IowaScaledEngineering/ckt-irsense/pg/ckt-irsense-ra-v4.1-9db1f3e/ckt-irsense-ra-pcb.pdf

# ckt-irsense-ra.pcb

# 1. Table of Contents (This Page) Created on Mon Oct 12 17:48:26 2020

# 2. top 3. bottom 4. outline 5. plated-drill 6. unplated-drill 7. componentmask 8. soldermask 9. topsilk 10. bottomsilk 11. toppaste 12. bottompaste 13. topassembly 14. bottomassembly 15. fab

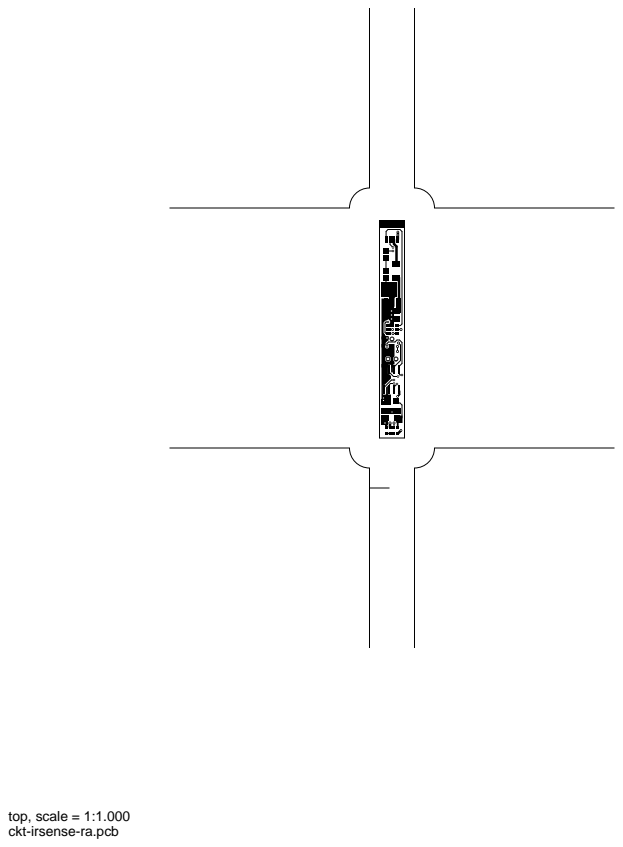
[picture p4: page 2]
top, scale = 1:1.000

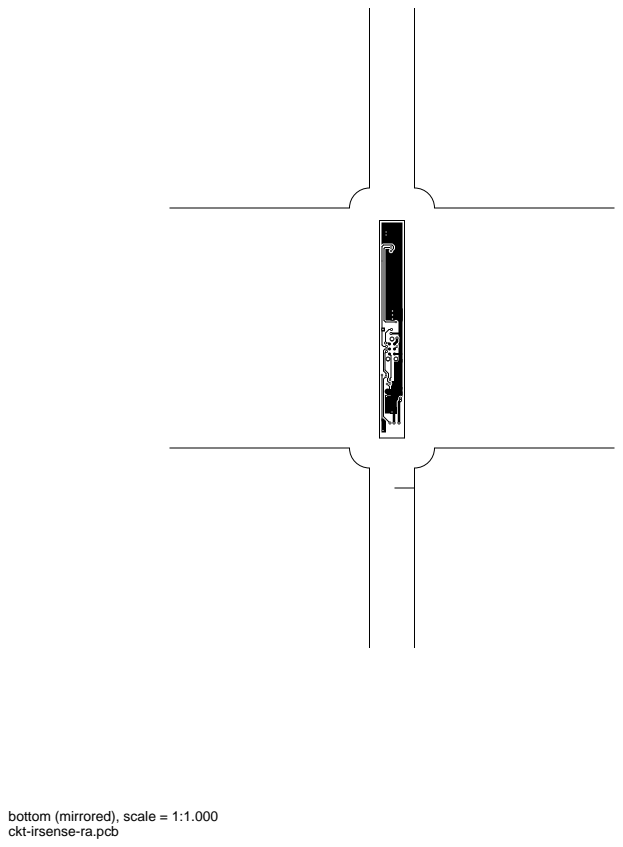
[picture p5: page 3]

bottom (mirrored), scale = 1:1.000

outline, scale = 1:1.000 plated-drill, scale = 1:1.000 unplated-drill, scale = 1:1.000

topmask, scale = 1:1.000

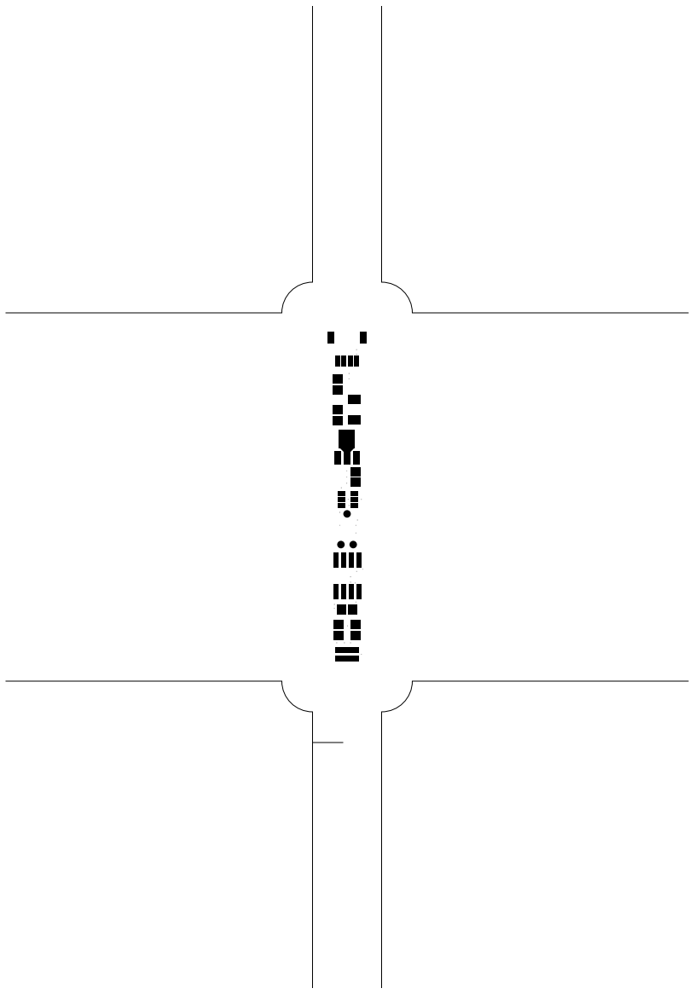
[picture p6: figure]

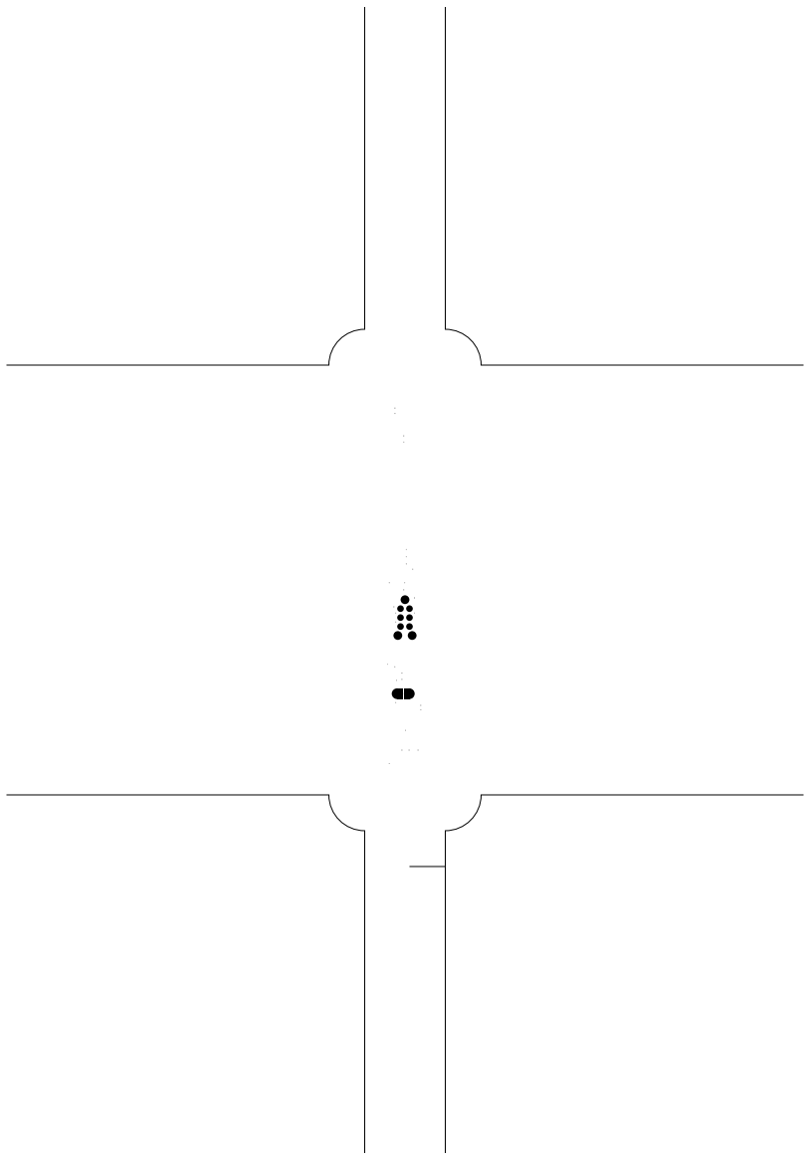
[picture p7: figure]

bottommask (mirrored), scale = 1:1.000

topsilk, scale = 1:1.000 bottomsilk (mirrored), scale = 1:1.000

toppaste, scale = 1:1.000 bottompaste (mirrored), scale = 1:1.000

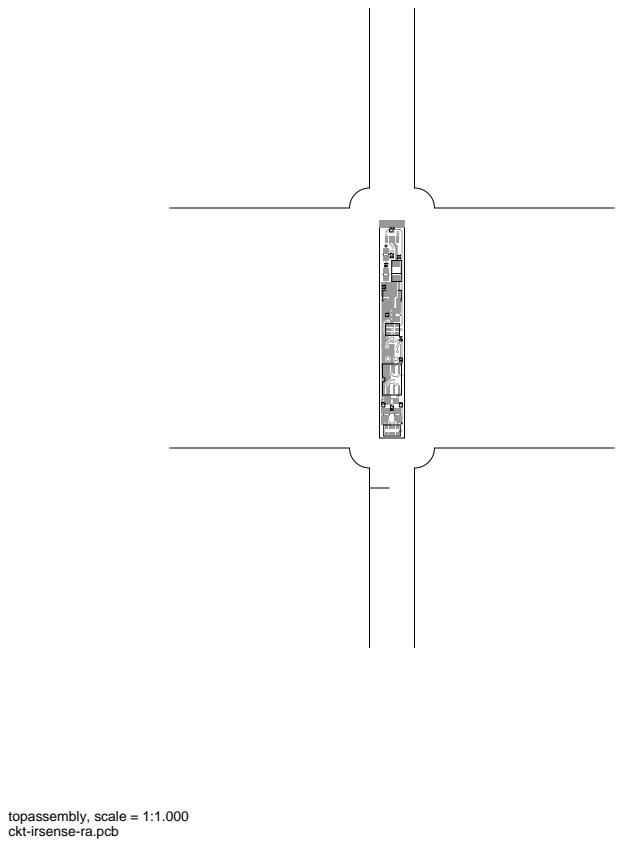
[picture p8: page 13]
topassembly, scale = 1:1.000

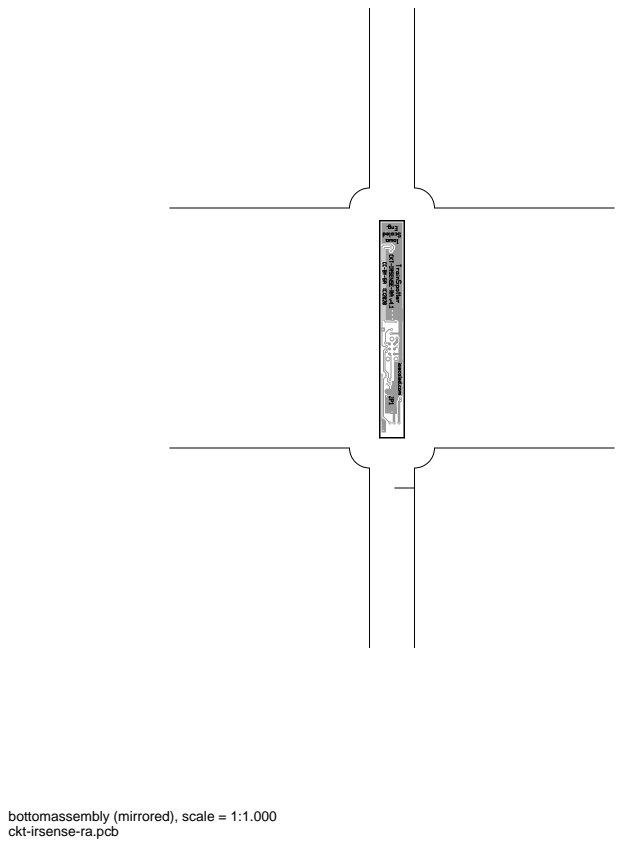
[picture p9: page 14]

bottomassembly (mirrored), scale = 1:1.000

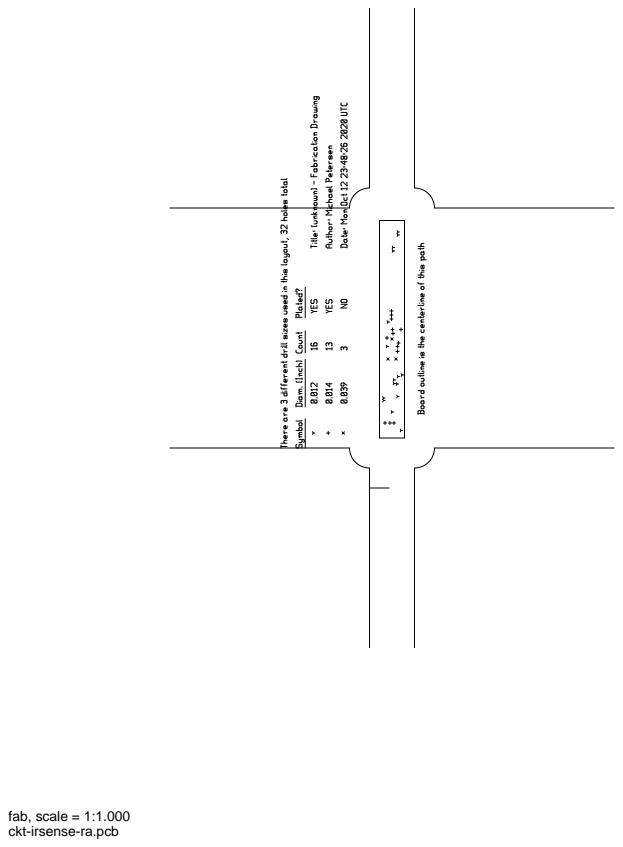
[picture p10: page 15]
fab, scale = 1:1.000
