IowaScaledEngineering/ckt-irsense/pg/i2c-irsense-v1.1-0d06f27/i2c-irsense-pcb.pdf

# i2c-irsense.pcb

# 1. Table of Contents (This Page) Created on Tue Jan 26 08:26:58 2016

# 2. top 3. bottom 4. outline 5. plated-drill 6. componentmask 7. soldermask 8. topsilk 9. bottomsilk 10. toppaste 11. topassembly 12. bottomassembly 13. fab

top, scale = 1:1.000

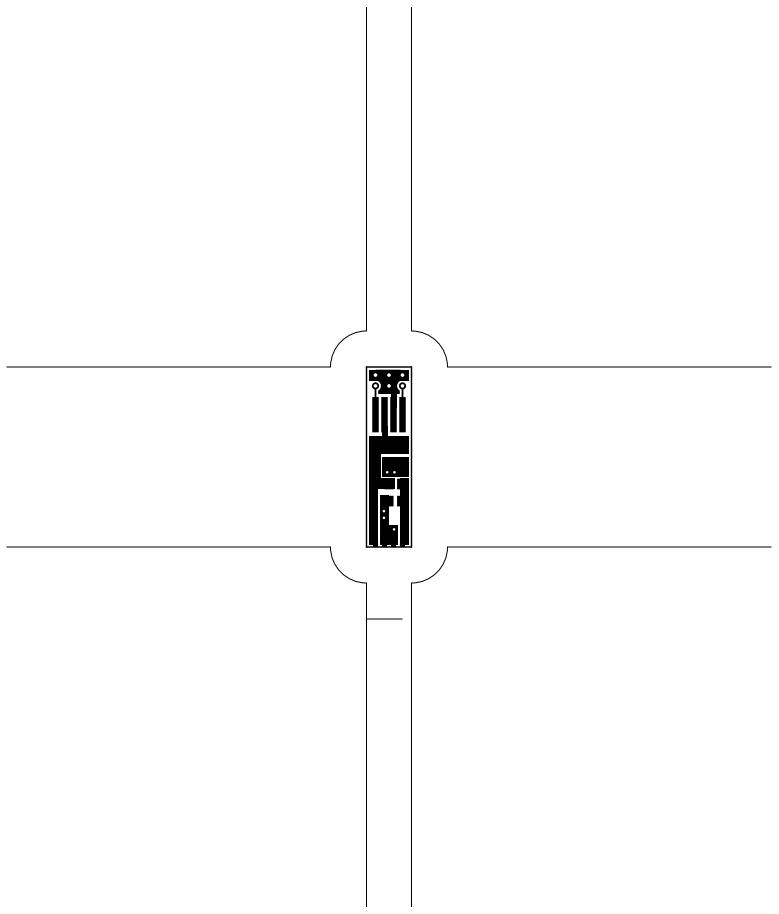
[picture p20: figure]
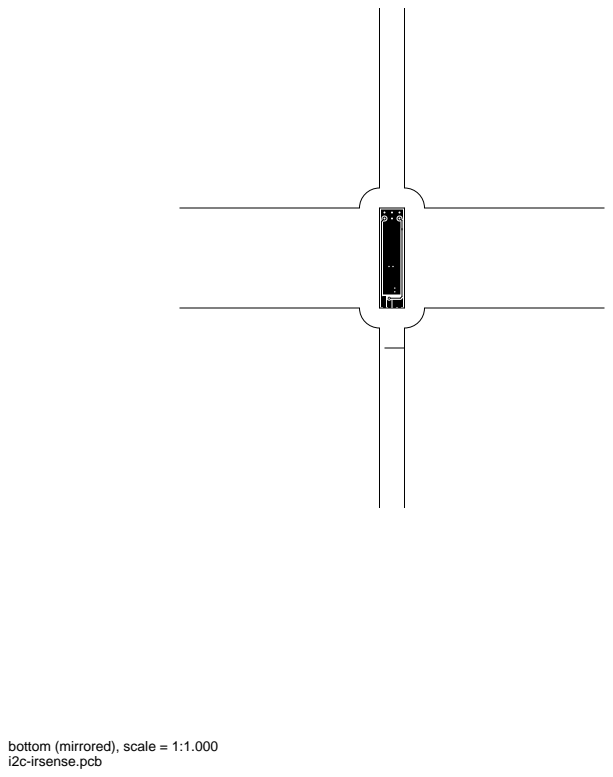
[picture p21: page 3]

bottom (mirrored), scale = 1:1.000

outline, scale = 1:1.000 plated-drill, scale = 1:1.000

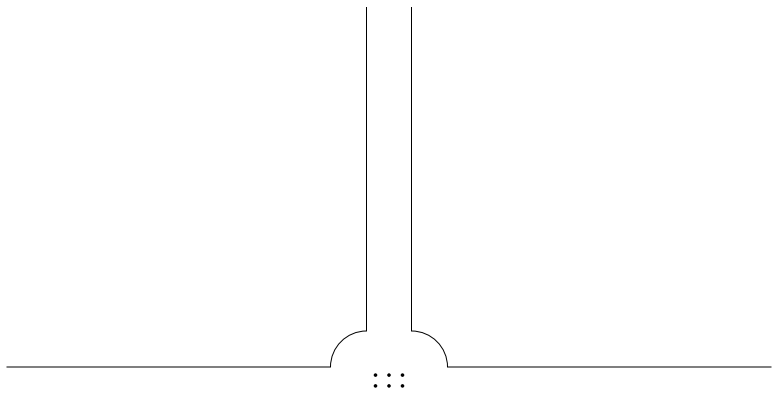
[picture p22: figure]
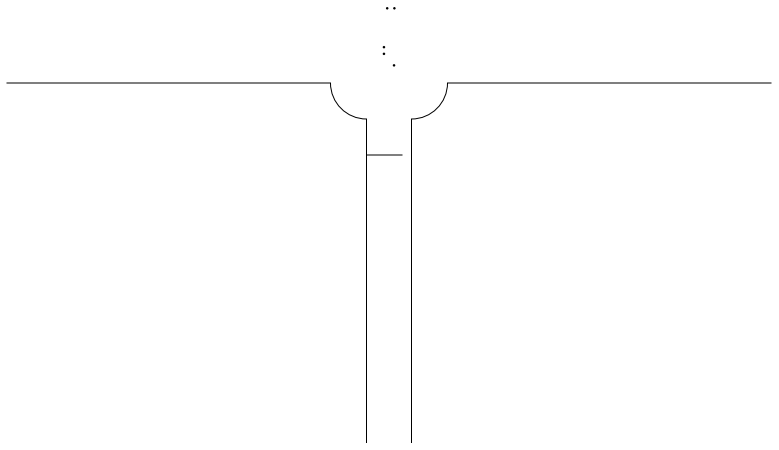
[picture p23: figure]

topmask, scale = 1:1.000 bottommask (mirrored), scale = 1:1.000

topsilk, scale = 1:1.000

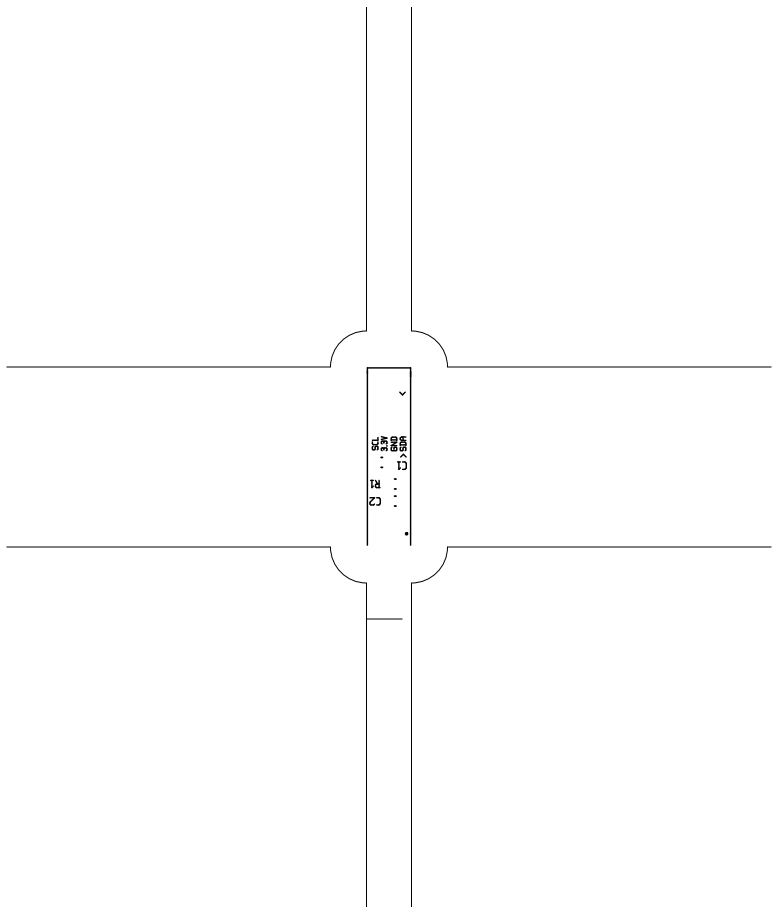
[picture p24: figure]

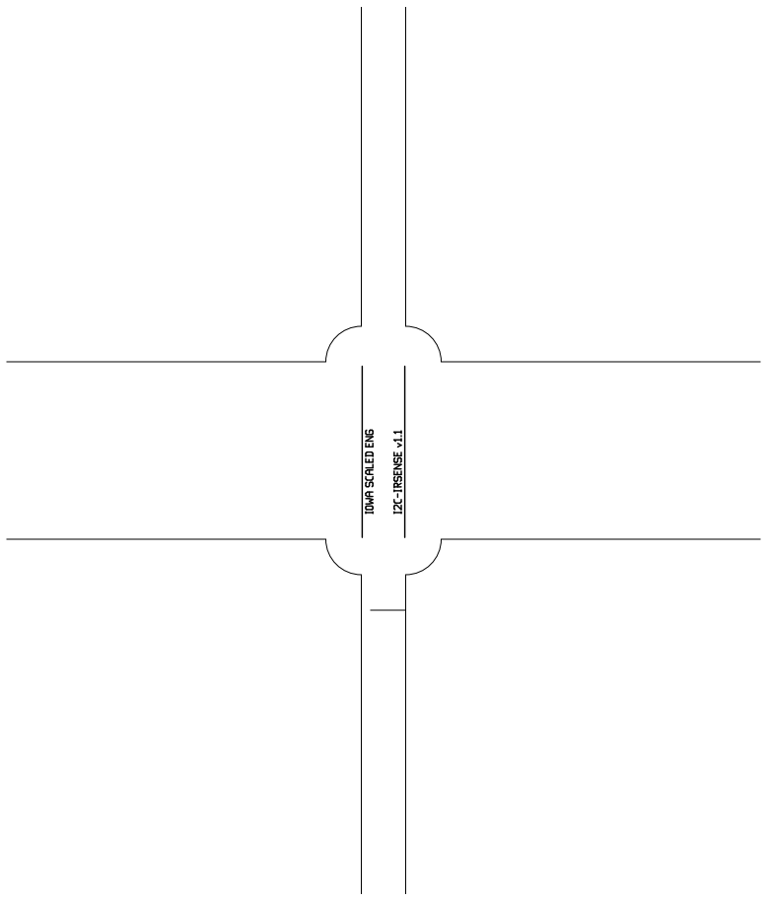
[picture p25: figure]

bottomsilk (mirrored), scale = 1:1.000

toppaste, scale = 1:1.000

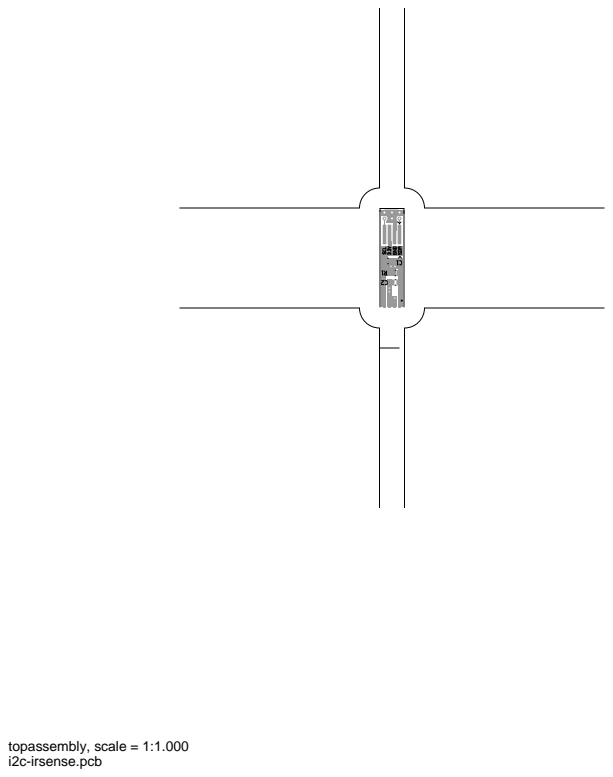
[picture p26: page 11]
topassembly, scale = 1:1.000

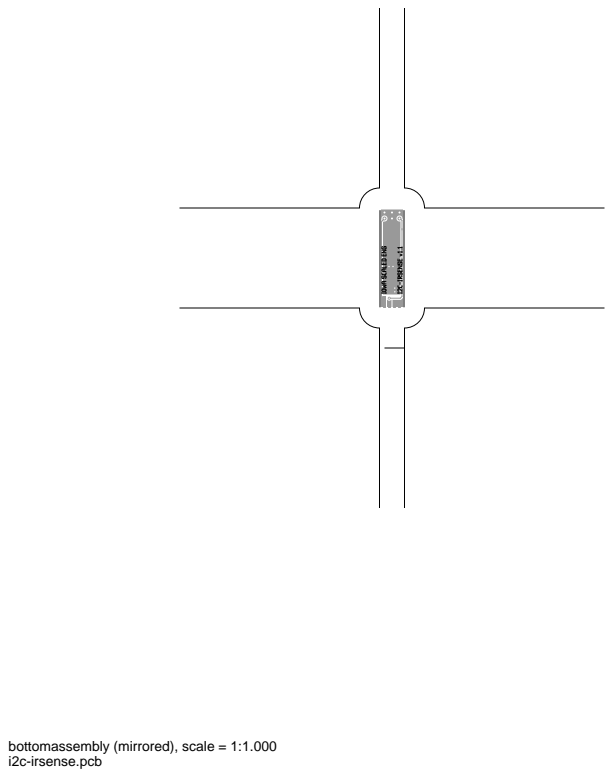
[picture p27: page 12]

bottomassembly (mirrored), scale = 1:1.000

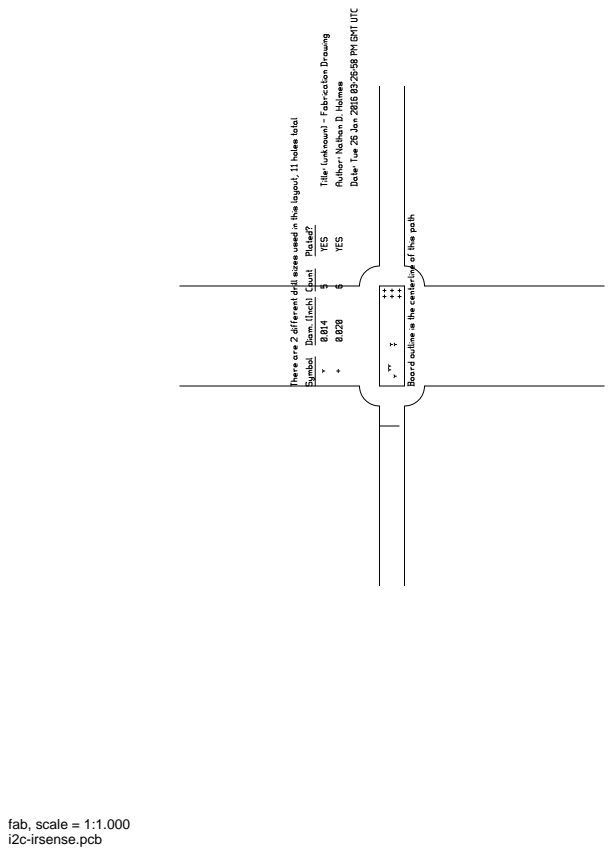
[picture p28: page 13]
fab, scale = 1:1.000
