IowaScaledEngineering/ckt-irsense/pg/ckt-irsense-v3.2-r1103/ckt-irsense-pcb.pdf

# ckt-irsense.pcb

# 1. Table of Contents (This Page) Created on Thu Oct 16 12:59:54 2014

# 2. top 3. bottom 4. outline 5. plated-drill 6. unplated-drill 7. componentmask 8. soldermask 9. topsilk 10. bottomsilk 11. toppaste 12. topassembly 13. bottomassembly 14. fab

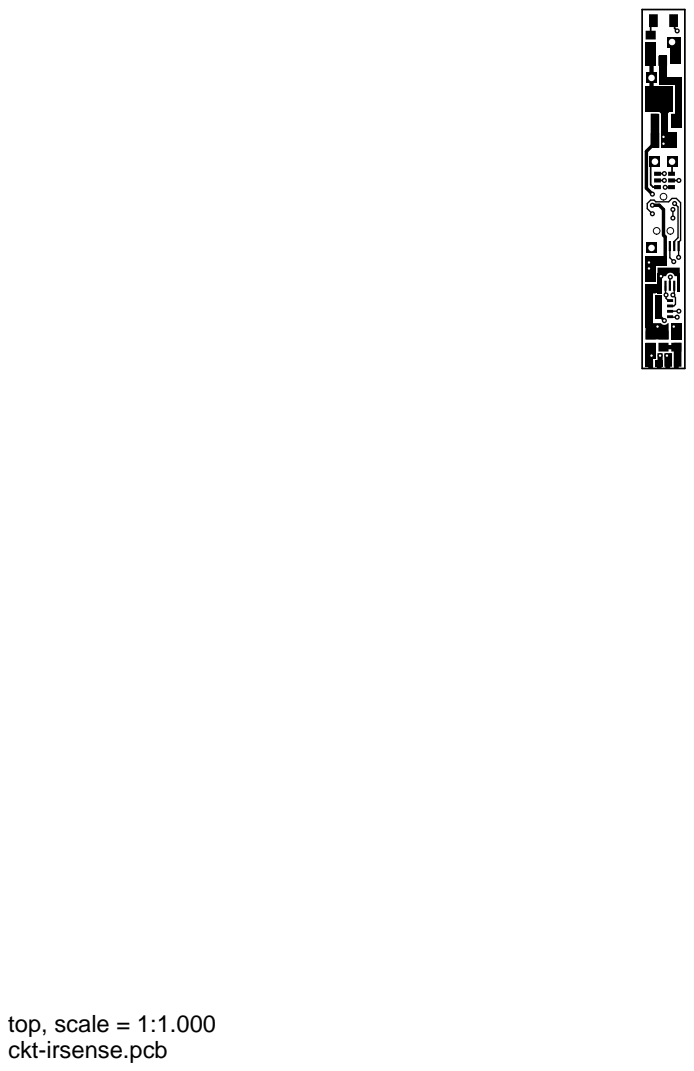
[picture p29: page 2]
top, scale = 1:1.000

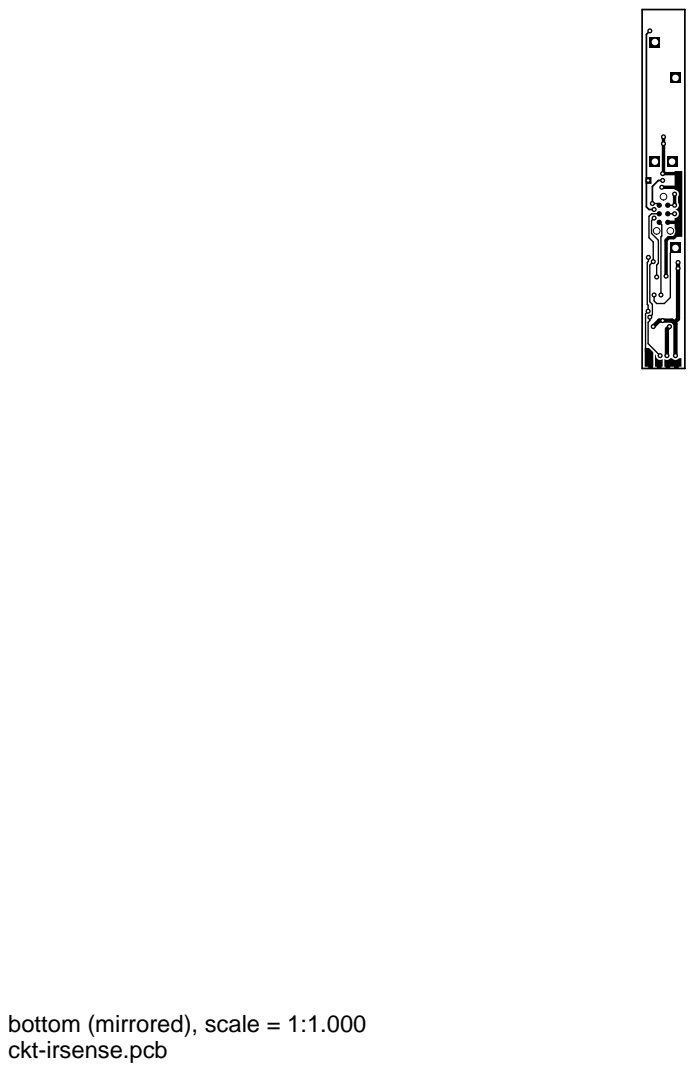
[picture p30: page 3]

bottom (mirrored), scale = 1:1.000

outline, scale = 1:1.000

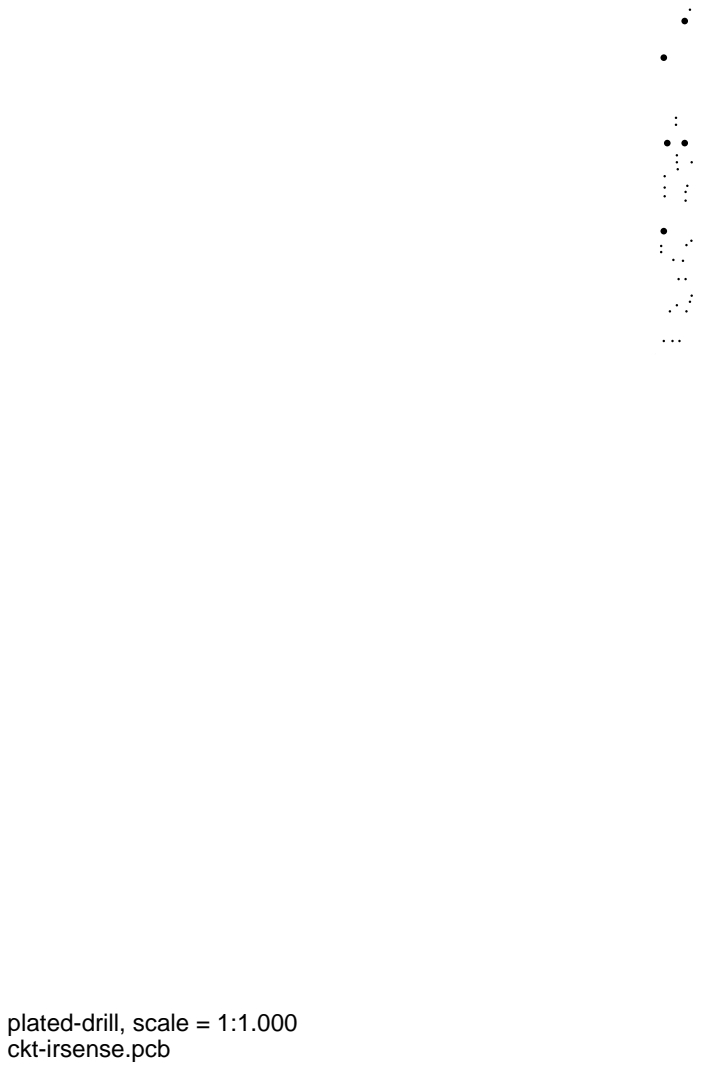
[picture p31: page 5]

plated-drill, scale = 1:1.000

unplated-drill, scale = 1:1.000

topmask, scale = 1:1.000 bottommask (mirrored), scale = 1:1.000

topsilk, scale = 1:1.000 bottomsilk (mirrored), scale = 1:1.000

toppaste, scale = 1:1.000

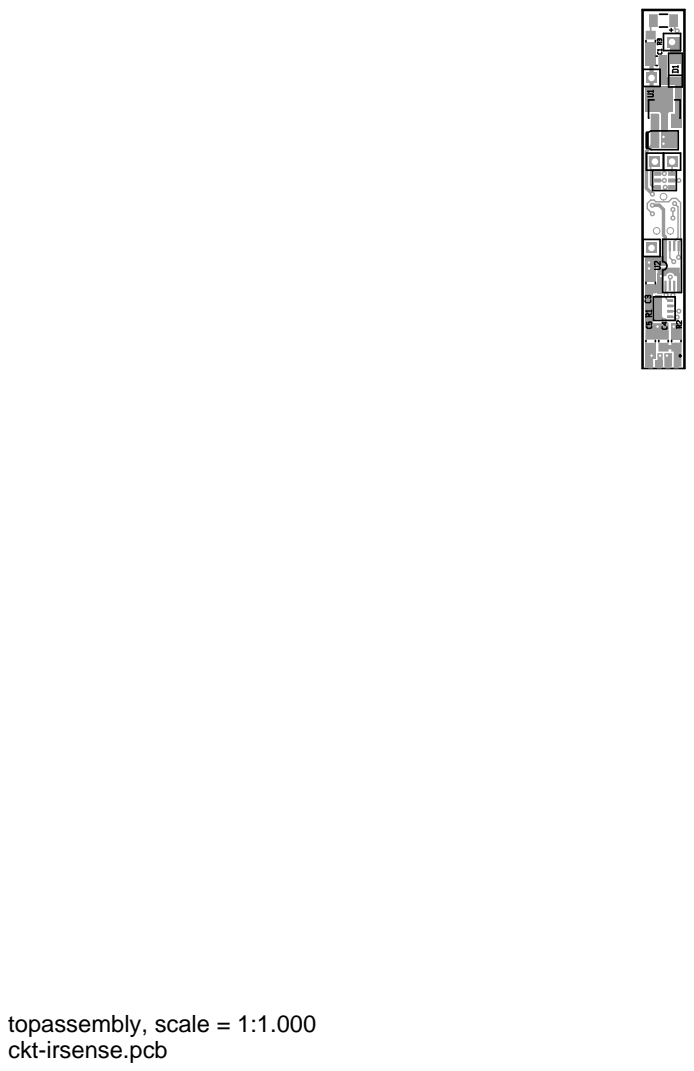
[picture p32: page 12]
topassembly, scale = 1:1.000

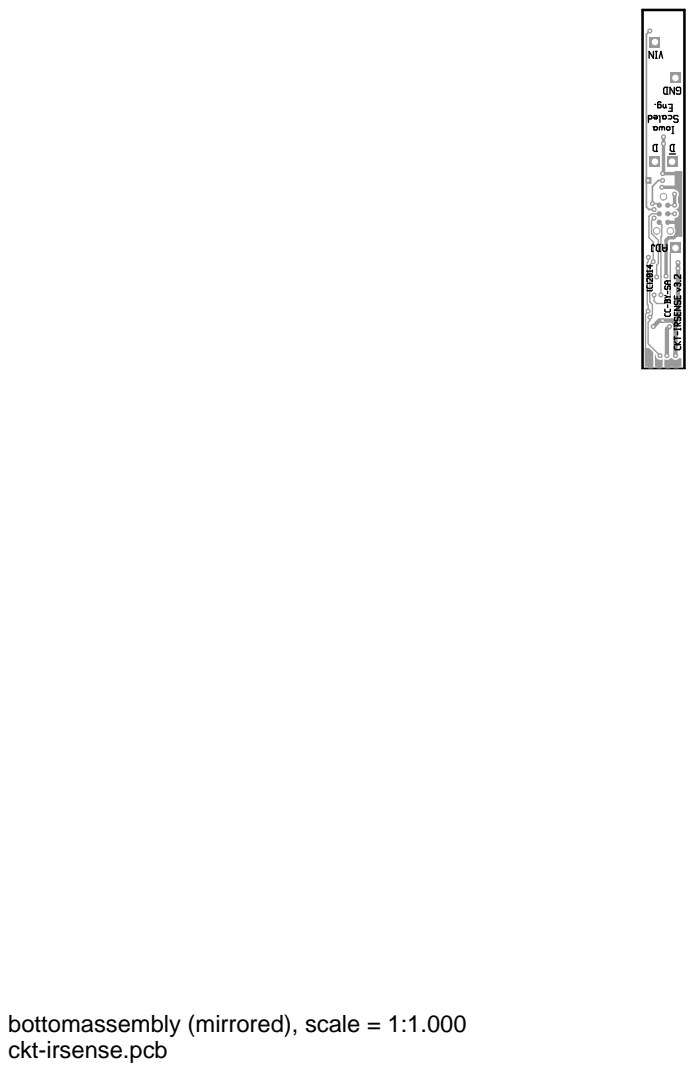
[picture p33: page 13]

bottomassembly (mirrored), scale = 1:1.000

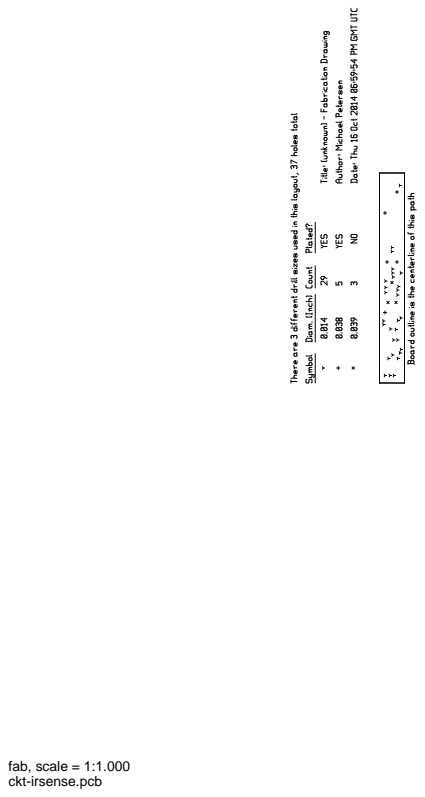
[picture p34: page 14]
fab, scale = 1:1.000
