IowaScaledEngineering/ckt-irsense/pg/ckt-irsense-sns-v1.0-r943/ckt-irsense-sns-pcb.pdf

# ckt-irsense-sns.pcb

# 1. Table of Contents (This Page) Created on Sat Jun 21 22:25:47 2014

# 2. top 3. bottom 4. outline 5. plated-drill 6. componentmask 7. soldermask 8. topsilk 9. bottomsilk 10. toppaste 11. topassembly 12. bottomassembly 13. fab

top, scale = 1:1.000 bottom (mirrored), scale = 1:1.000

outline, scale = 1:1.000 plated-drill, scale = 1:1.000

topmask, scale = 1:1.000 bottommask (mirrored), scale = 1:1.000

topsilk, scale = 1:1.000 bottomsilk (mirrored), scale = 1:1.000

toppaste, scale = 1:1.000 topassembly, scale = 1:1.000 bottomassembly (mirrored), scale = 1:1.000

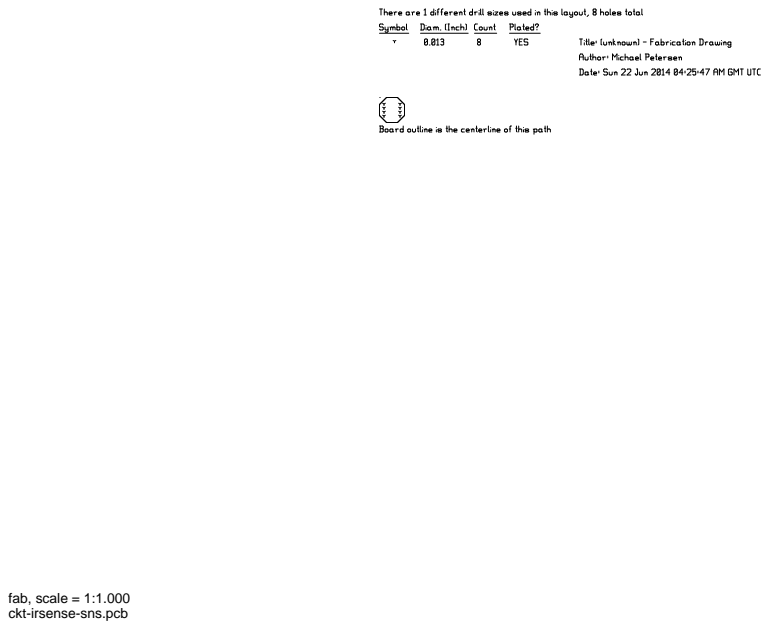
[picture p35: page 13]
fab, scale = 1:1.000
