IowaScaledEngineering/ckt-irsense/pg/ckt-irsense-sns-panel-v1.1-4b12239/ckt-irsense-sns-panel-pcb.pdf

# ckt-irsense-sns-panel.pcb

# 1. Table of Contents (This Page) Created on Fri Dec 9 19:34:45 2016

# 2. top 3. bottom 4. outline 5. plated-drill 6. componentmask 7. soldermask 8. topsilk 9. bottomsilk 10. toppaste 11. topassembly 12. bottomassembly 13. fab

top, scale = 1:1.000


bottom (mirrored), scale = 1:1.000

outline, scale = 1:1.000


plated-drill, scale = 1:1.000

topmask, scale = 1:1.000 bottommask (mirrored), scale = 1:1.000

topsilk, scale = 1:1.000

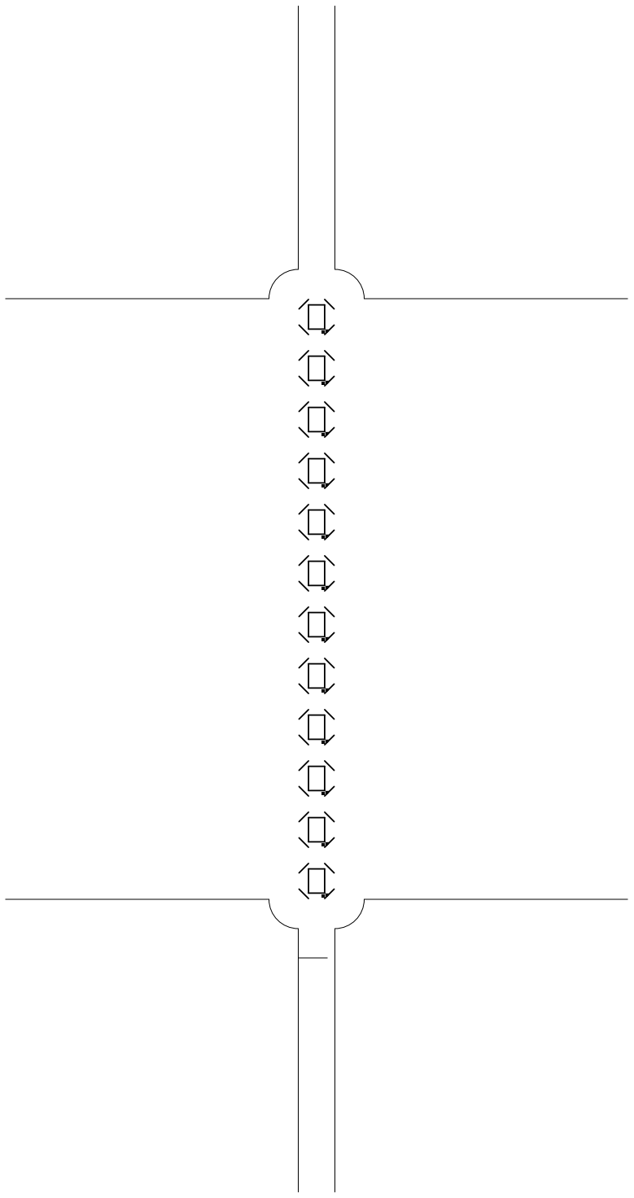
[picture p36: figure]

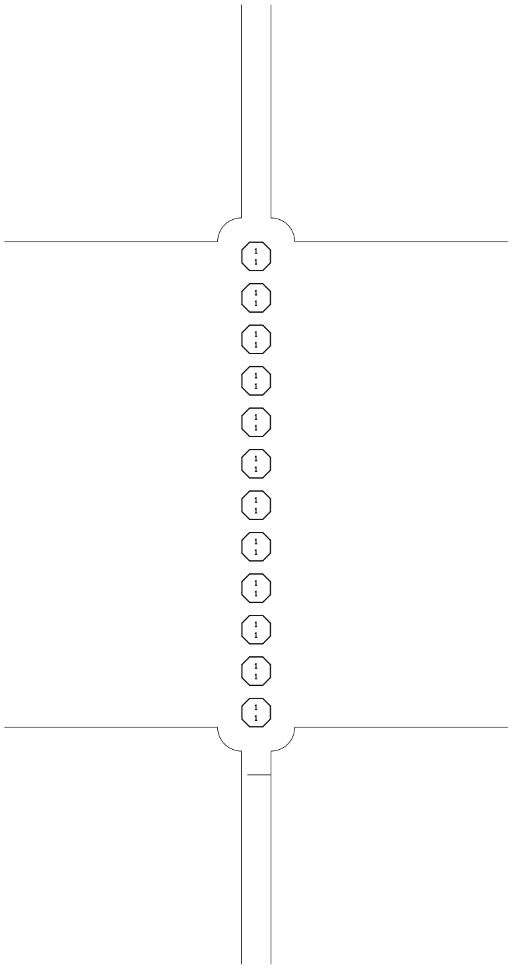
[picture p37: figure]

bottomsilk (mirrored), scale = 1:1.000

toppaste, scale = 1:1.000

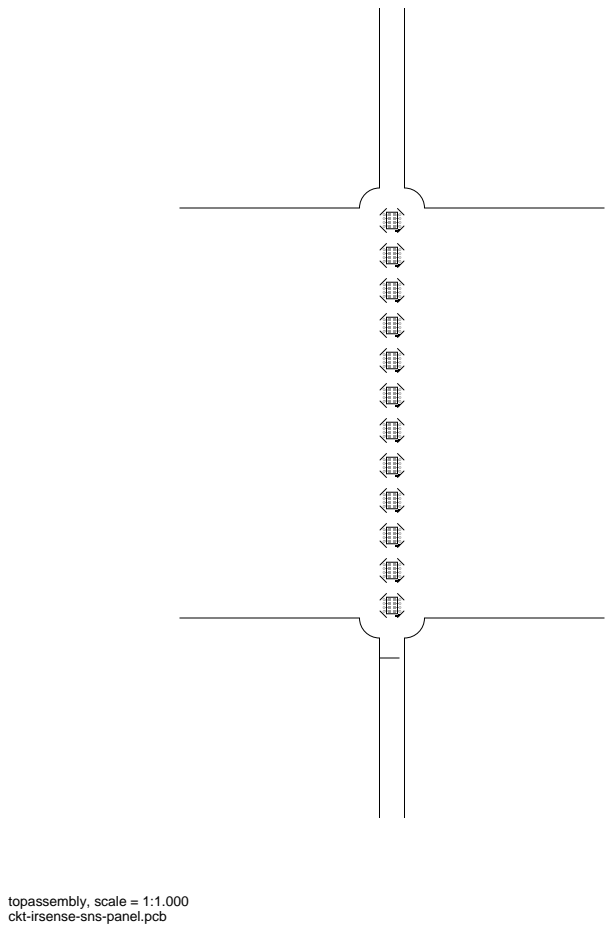
[picture p38: page 11]
topassembly, scale = 1:1.000

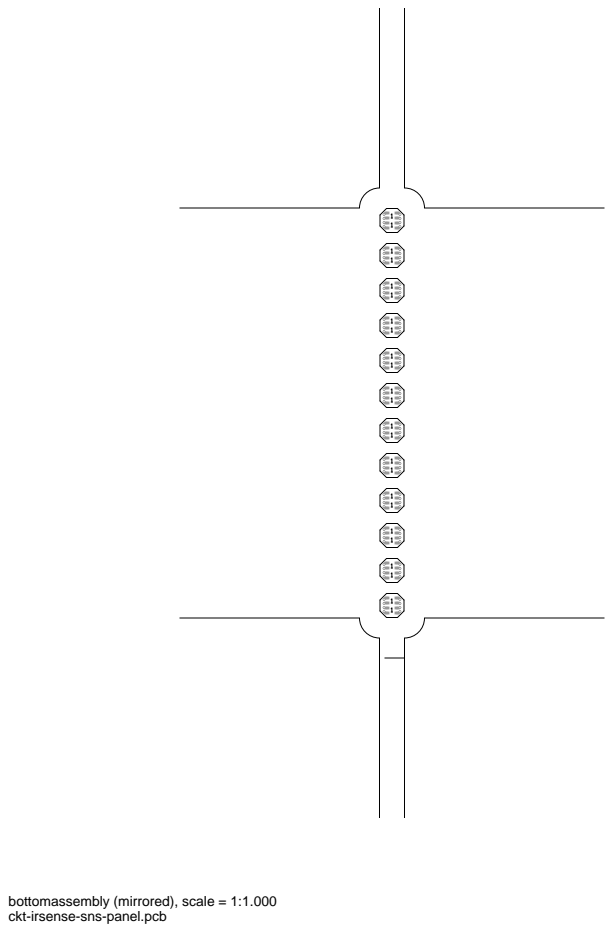
[picture p39: page 12]

bottomassembly (mirrored), scale = 1:1.000

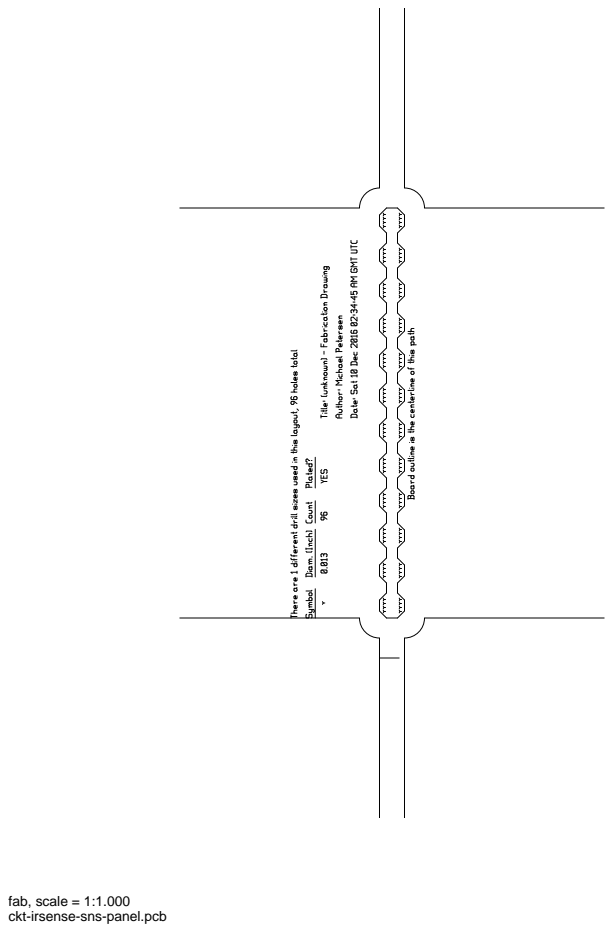
[picture p40: page 13]
fab, scale = 1:1.000
