IowaScaledEngineering/ckt-irsense/pg/i2c-irsense-v1.0-a2b9973/i2c-irsense-pcb.pdf

# i2c-irsense.pcb

# 1. Table of Contents (This Page) Created on Mon Nov 2 10:29:45 2015

# 2. top 3. bottom 4. outline 5. plated-drill 6. componentmask 7. soldermask 8. topsilk 9. bottomsilk 10. toppaste 11. topassembly 12. bottomassembly 13. fab

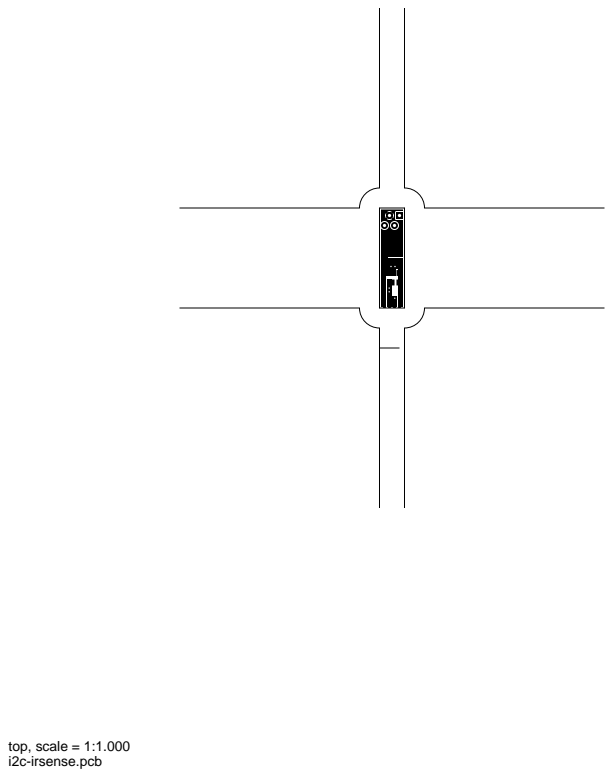
[picture p41: page 2]
top, scale = 1:1.000

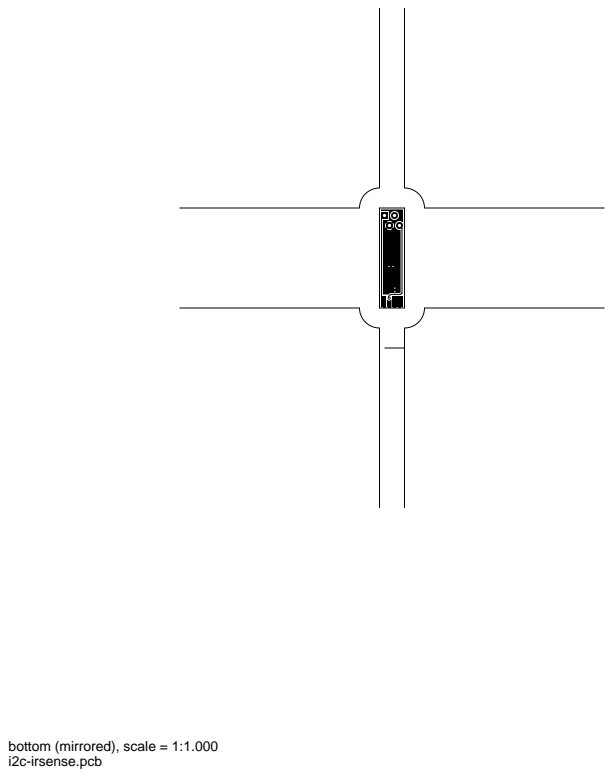
[picture p42: page 3]

bottom (mirrored), scale = 1:1.000

outline, scale = 1:1.000 plated-drill, scale = 1:1.000

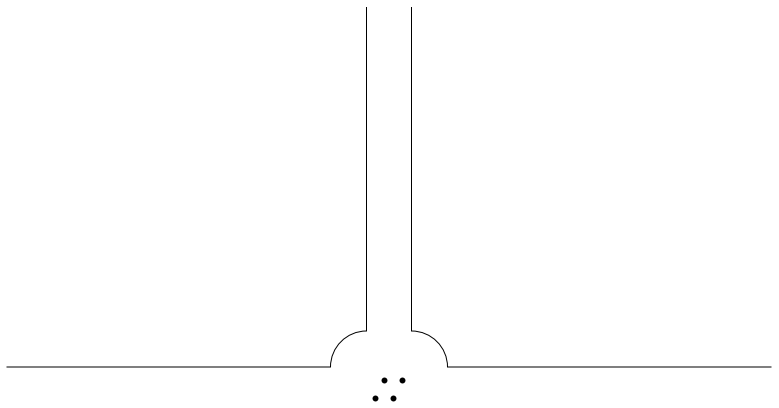
[picture p43: figure]

topmask, scale = 1:1.000

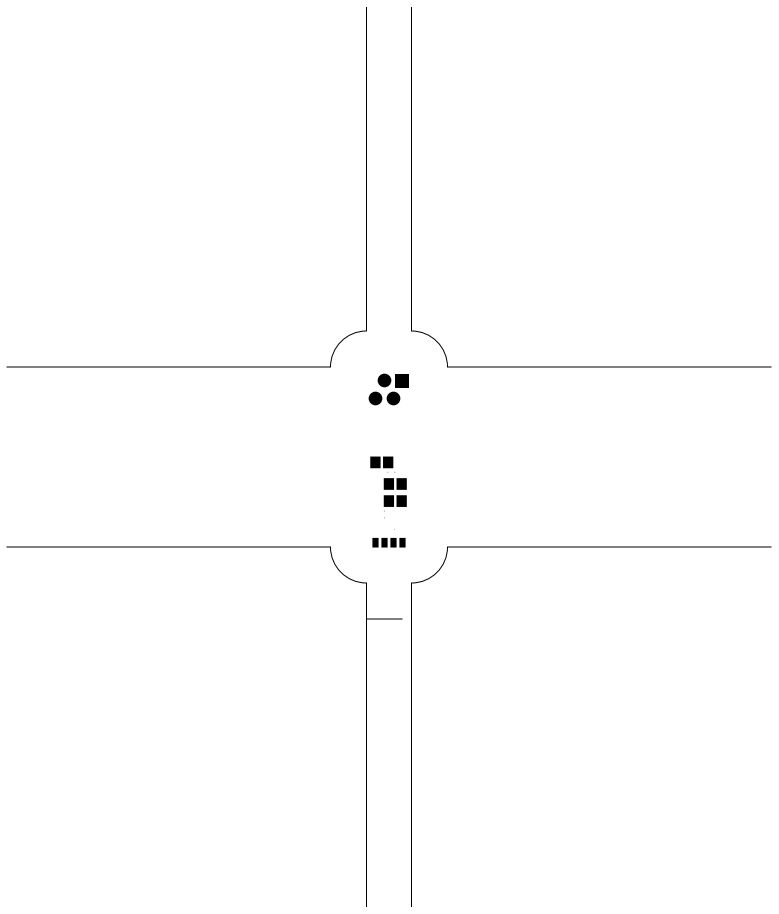
[picture p44: figure]

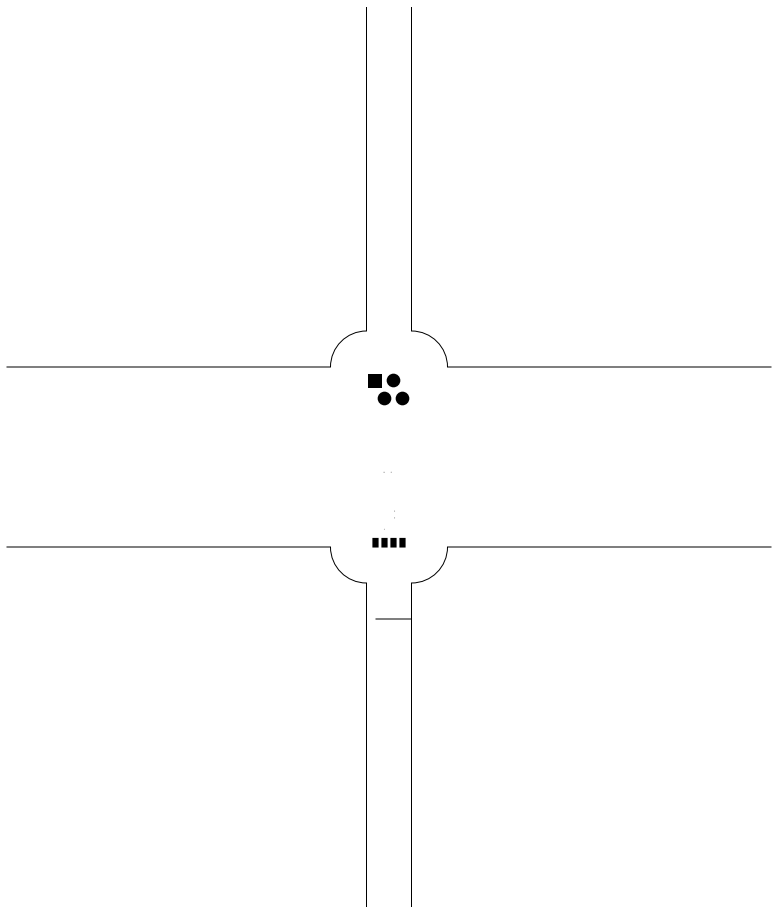
[picture p45: figure]

bottommask (mirrored), scale = 1:1.000

topsilk, scale = 1:1.000

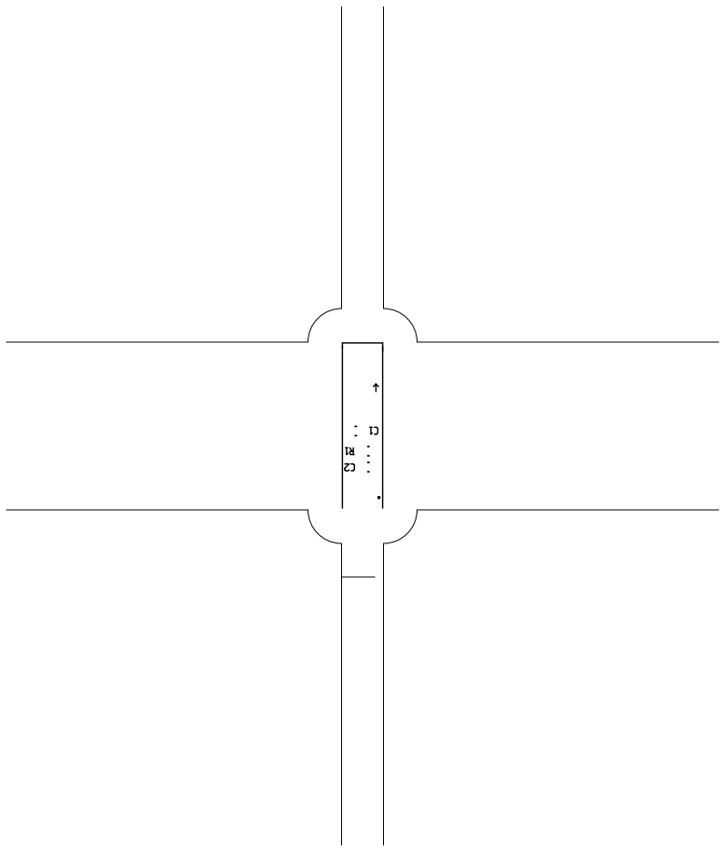
[picture p46: figure]

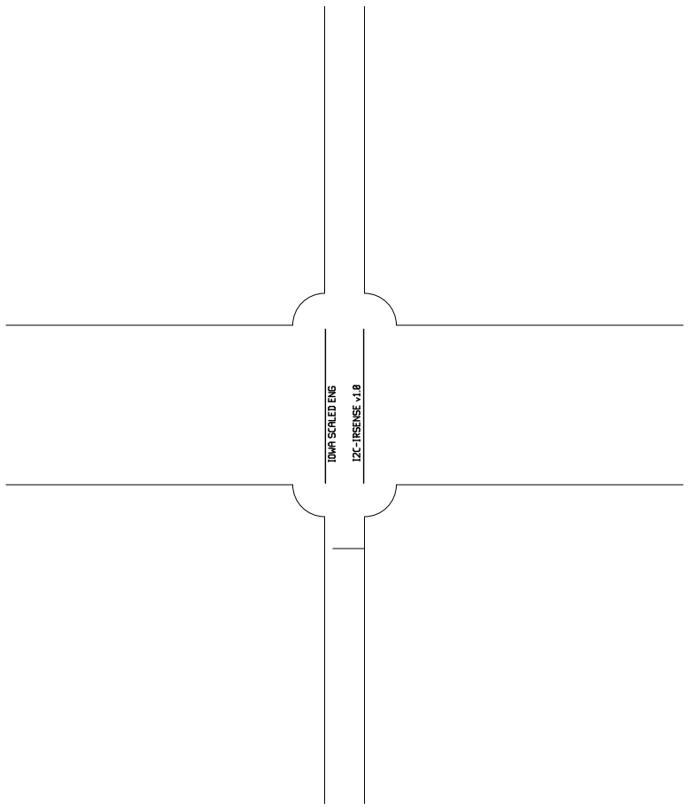
[picture p47: figure]

bottomsilk (mirrored), scale = 1:1.000

toppaste, scale = 1:1.000

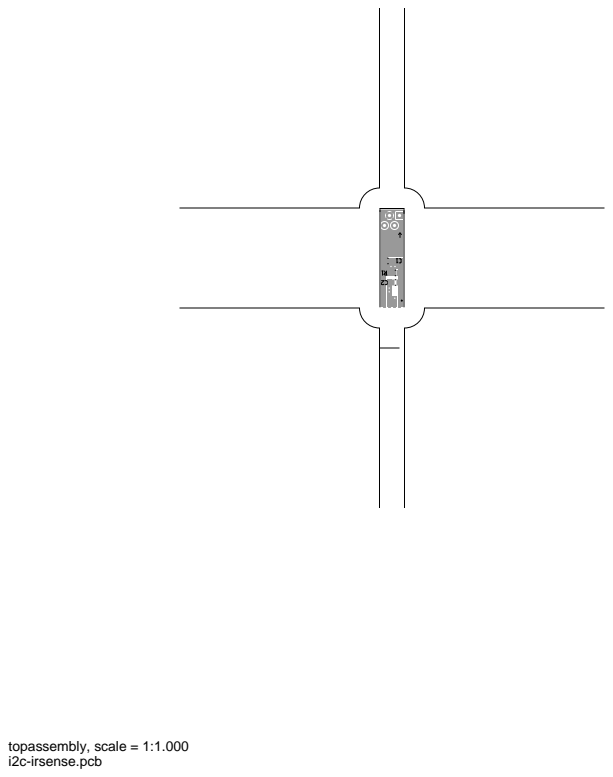
[picture p48: page 11]
topassembly, scale = 1:1.000

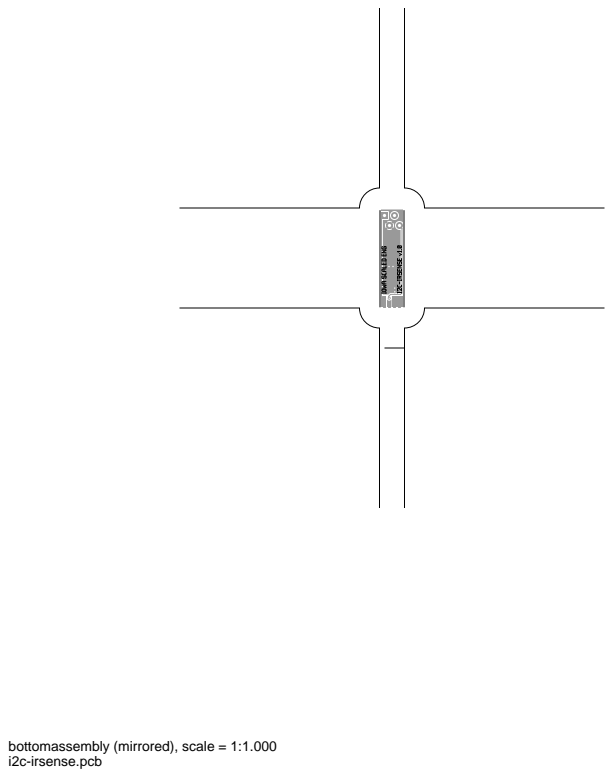
[picture p49: page 12]

bottomassembly (mirrored), scale = 1:1.000

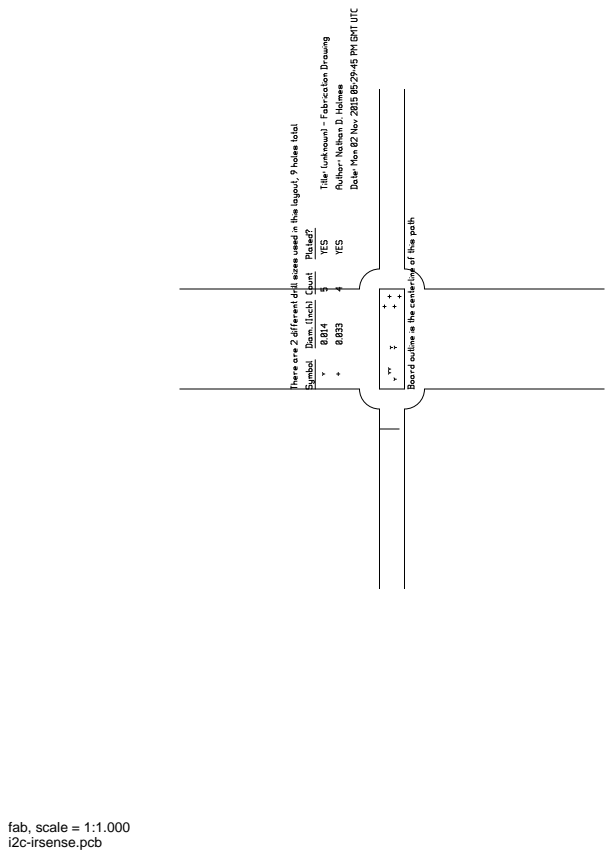
[picture p50: page 13]
fab, scale = 1:1.000
