IowaScaledEngineering/ckt-irsense/pg/ckt-irsense-v3.1-r943/ckt-irsense-pcb.pdf

# ckt-irsense.pcb

# 1. Table of Contents (This Page) Created on Sat Jun 21 22:24:18 2014

# 2. top 3. bottom 4. outline 5. plated-drill 6. unplated-drill 7. componentmask 8. soldermask 9. topsilk 10. bottomsilk 11. toppaste 12. topassembly 13. bottomassembly 14. fab

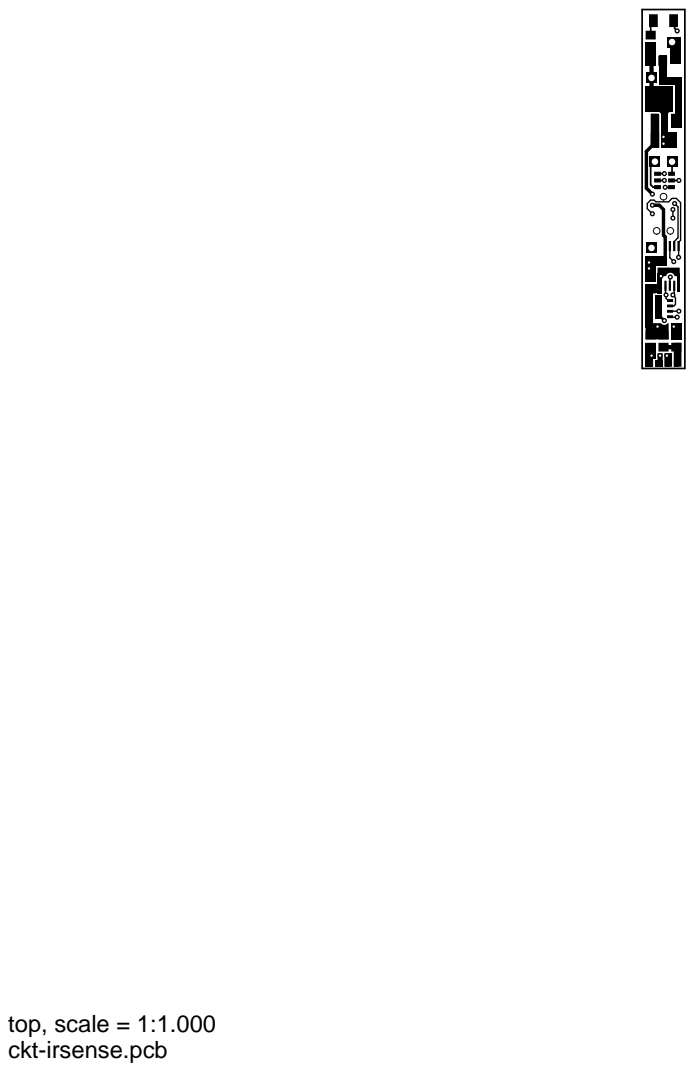
[picture p57: page 2]
top, scale = 1:1.000

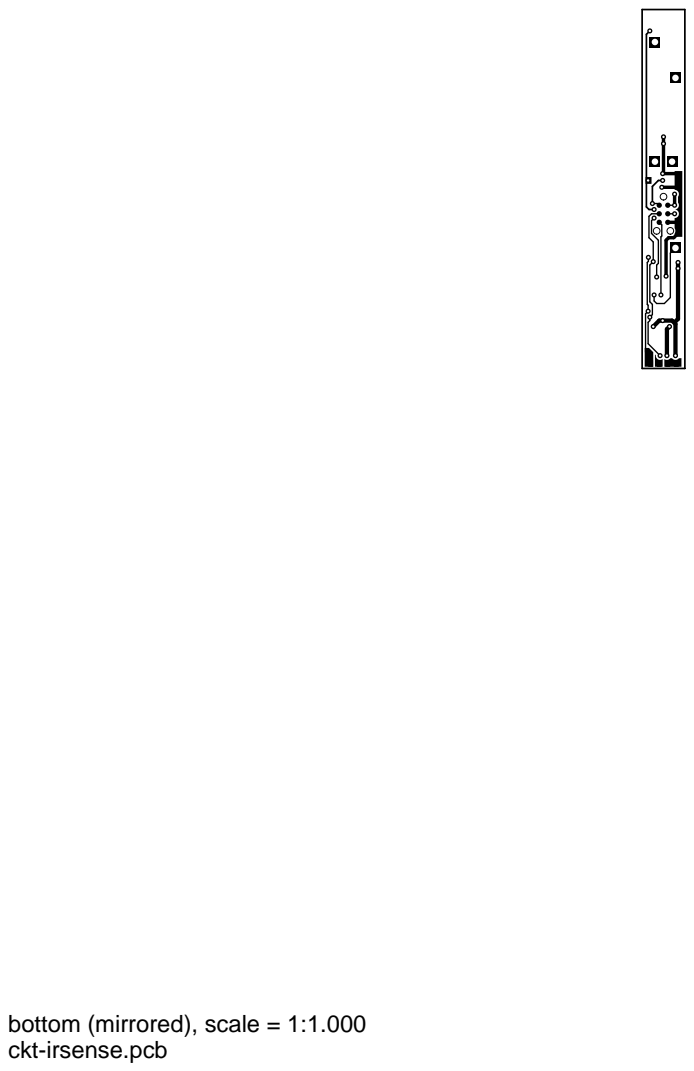
[picture p58: page 3]

bottom (mirrored), scale = 1:1.000

outline, scale = 1:1.000


plated-drill, scale = 1:1.000

unplated-drill, scale = 1:1.000

topmask, scale = 1:1.000 bottommask (mirrored), scale = 1:1.000

topsilk, scale = 1:1.000 bottomsilk (mirrored), scale = 1:1.000

toppaste, scale = 1:1.000

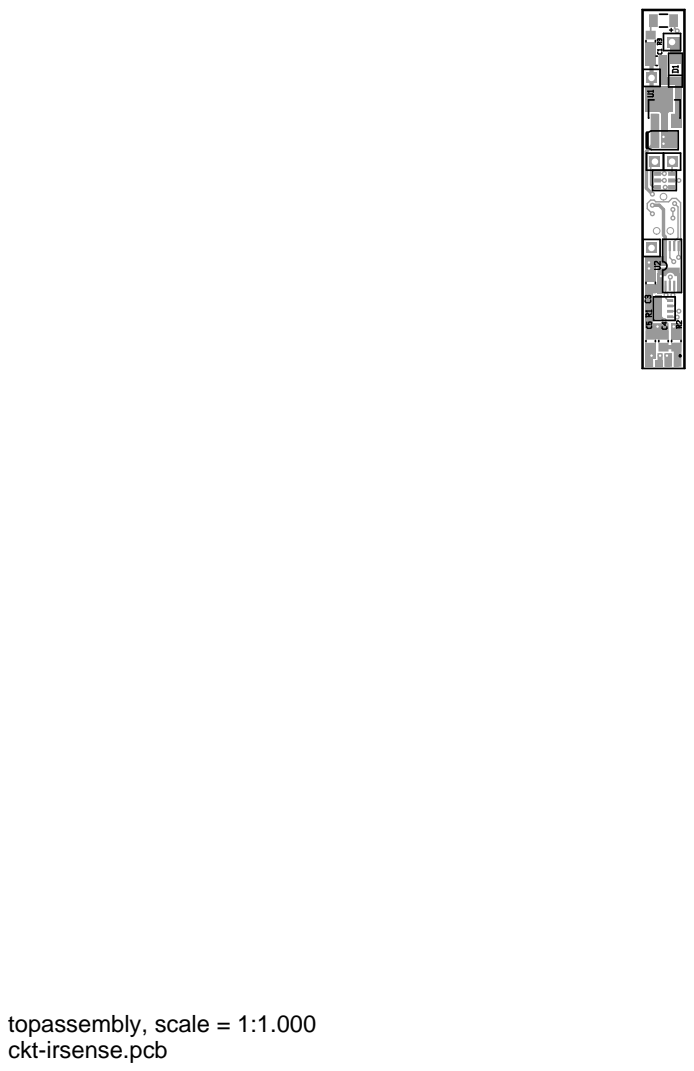
[picture p59: page 12]
topassembly, scale = 1:1.000

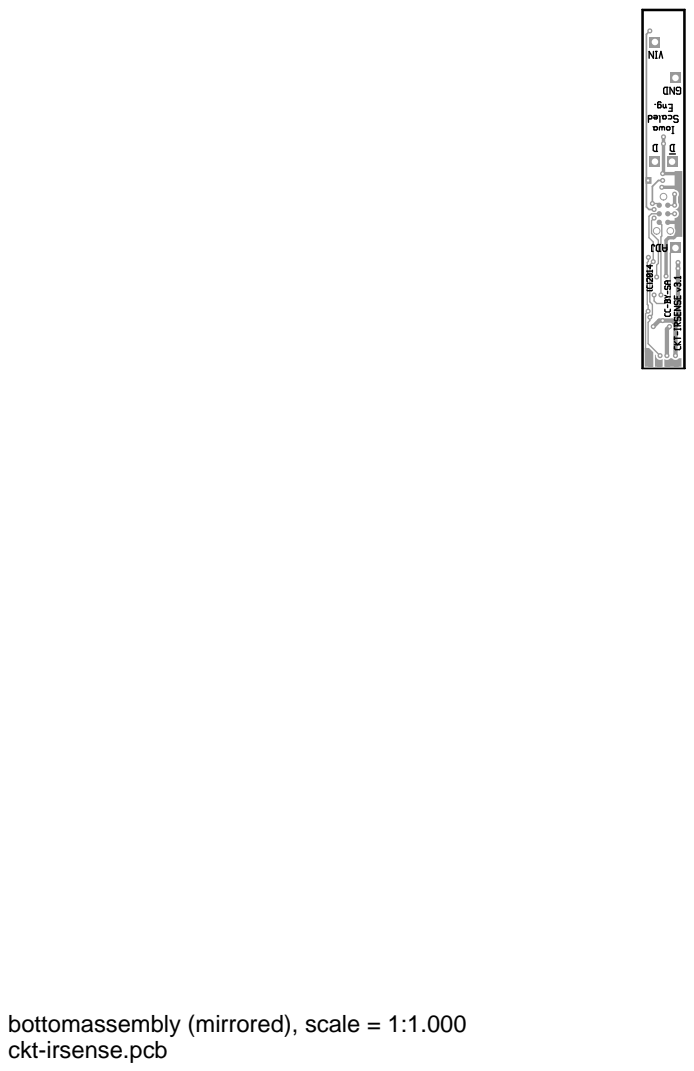
[picture p60: page 13]

bottomassembly (mirrored), scale = 1:1.000

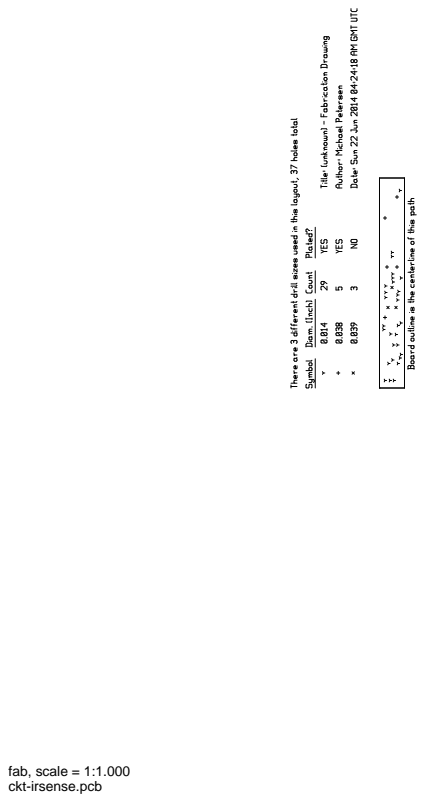
[picture p61: page 14]
fab, scale = 1:1.000
