IowaScaledEngineering/ckt-irsense/pg/ckt-irsense-v2.0-r755/ckt-irsense-pcb.pdf

# ckt-irsense.pcb

# 1. Table of Contents (This Page) Created on Sat Mar 22 13:33:40 2014

# 2. component 3. gnd 4. pwr 5. solder 6. outline 7. plated-drill 8. unplated-drill 9. componentmask 10. soldermask 11. topsilk 12. bottomsilk 13. toppaste 14. bottompaste 15. topassembly 16. bottomassembly 17. fab

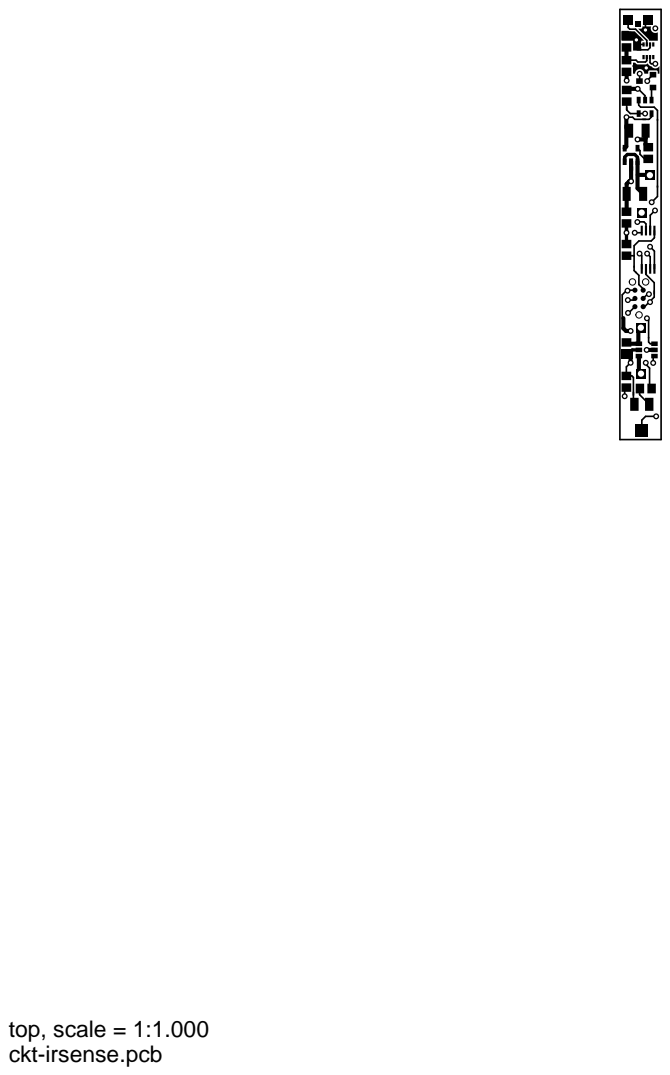
[picture p67: page 2]
top, scale = 1:1.000

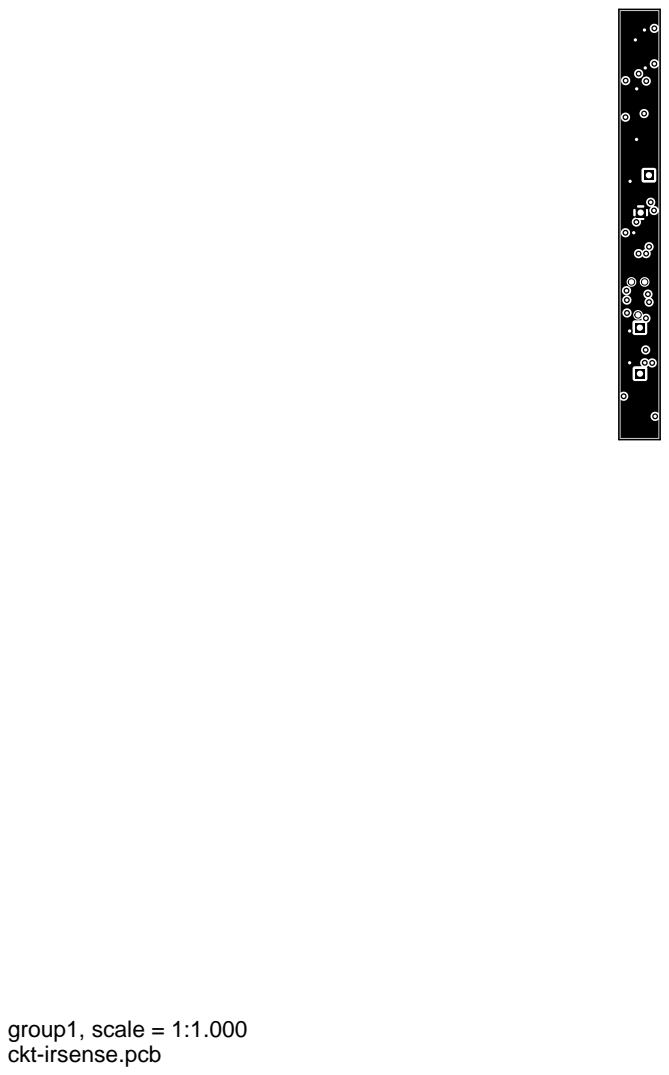
[picture p68: page 3]
group1, scale = 1:1.000

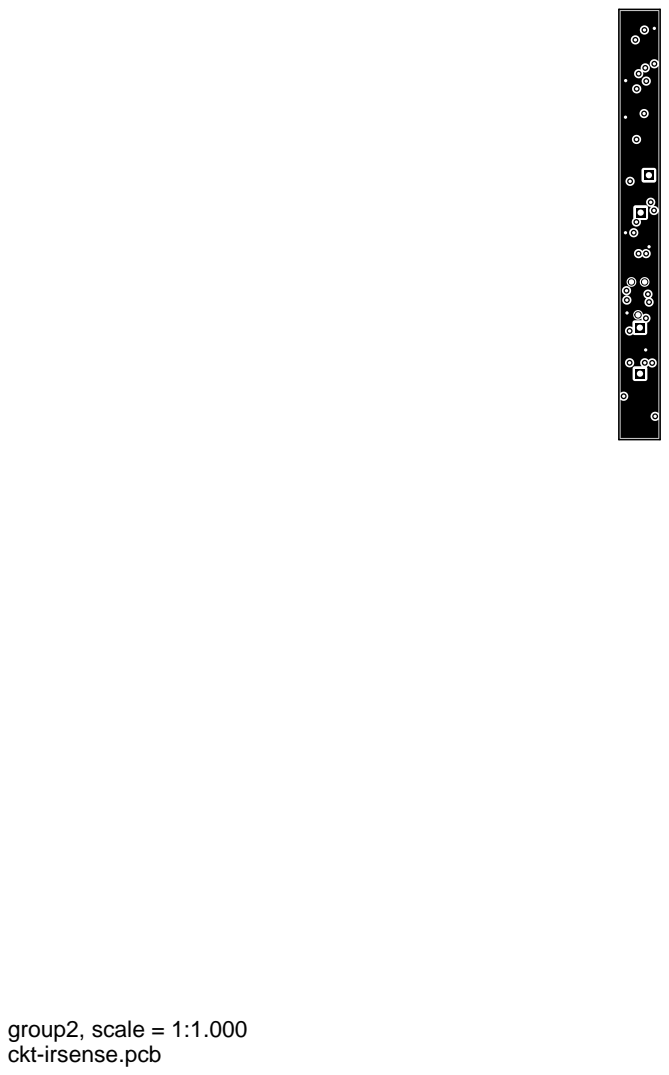
[picture p69: page 4]
group2, scale = 1:1.000

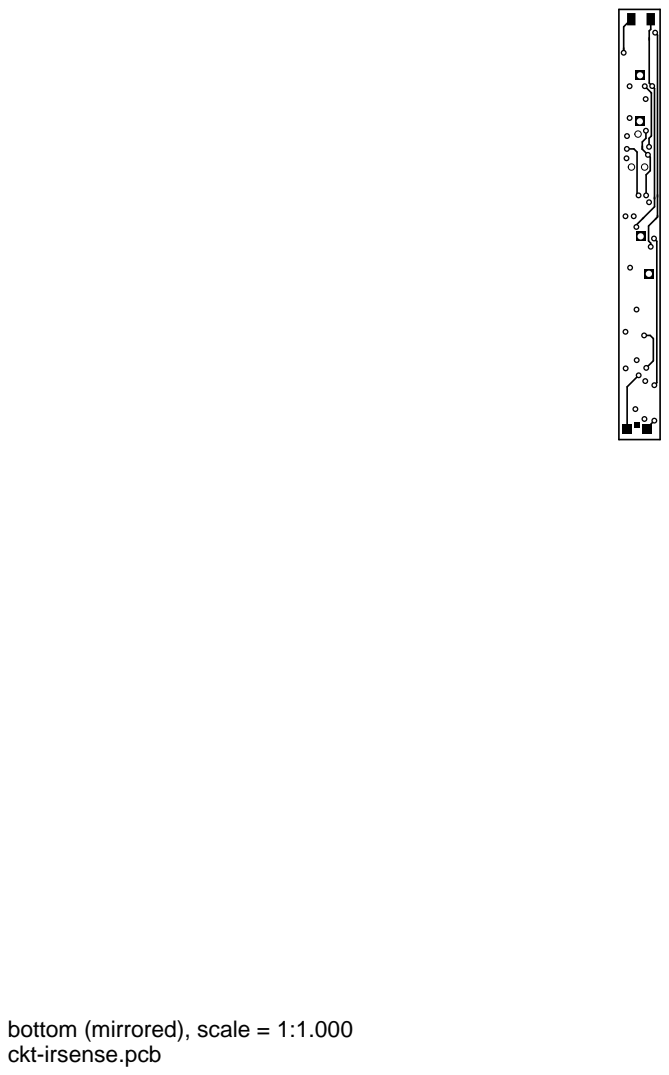
[picture p70: page 5]

bottom (mirrored), scale = 1:1.000

outline, scale = 1:1.000

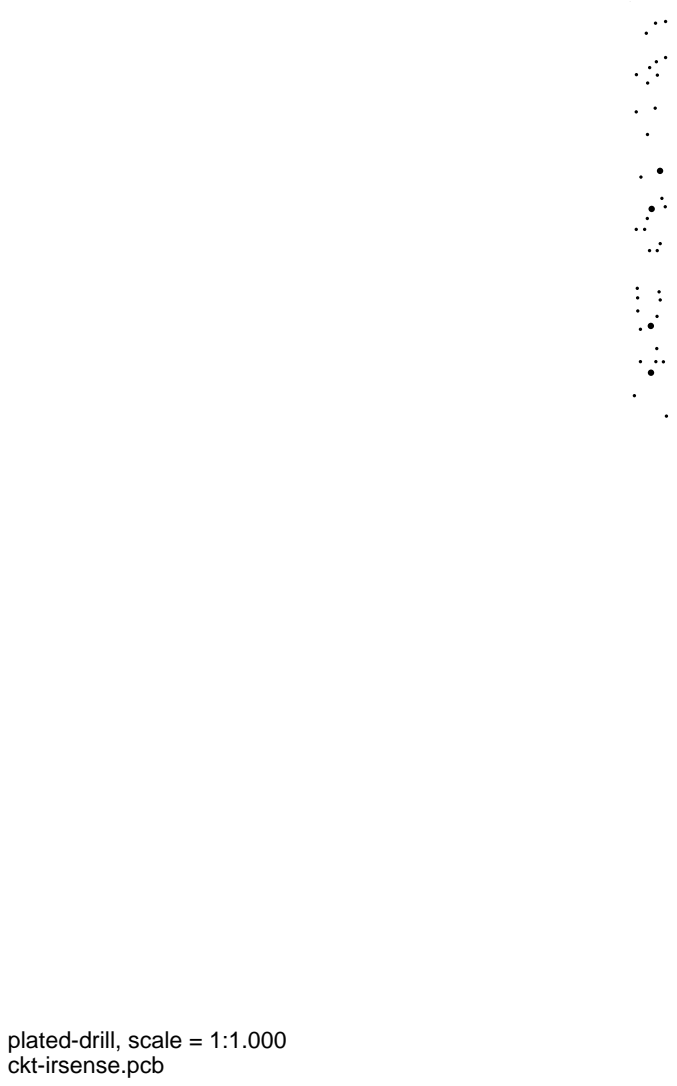
[picture p71: page 7]

plated-drill, scale = 1:1.000

unplated-drill, scale = 1:1.000

topmask, scale = 1:1.000 bottommask (mirrored), scale = 1:1.000

topsilk, scale = 1:1.000 bottomsilk (mirrored), scale = 1:1.000

toppaste, scale = 1:1.000 bottompaste (mirrored), scale = 1:1.000

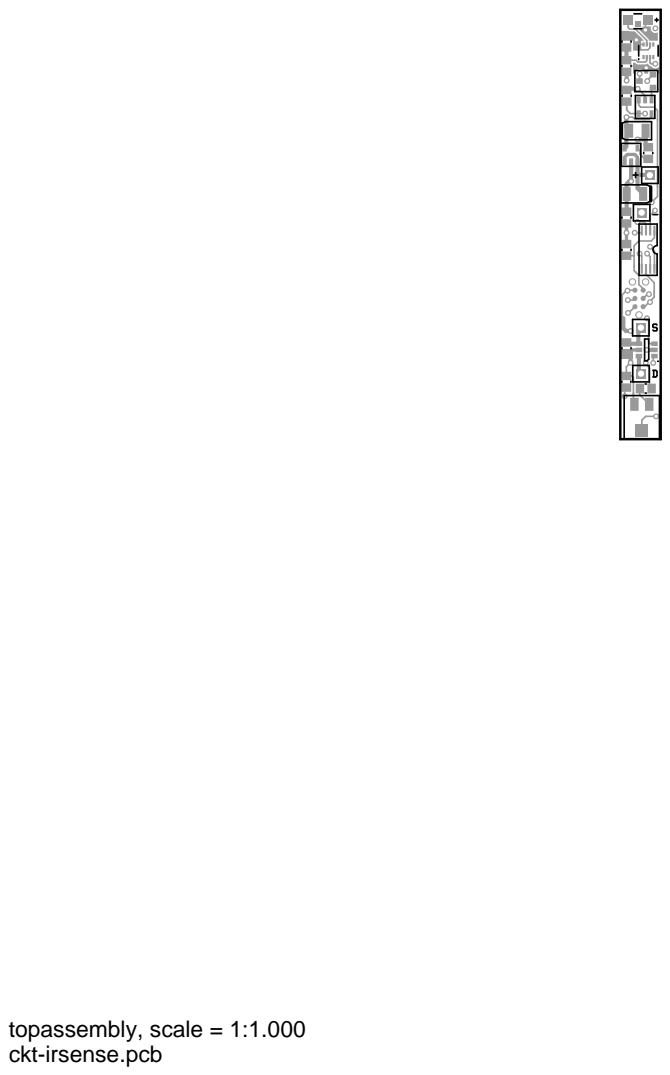
[picture p72: page 15]
topassembly, scale = 1:1.000

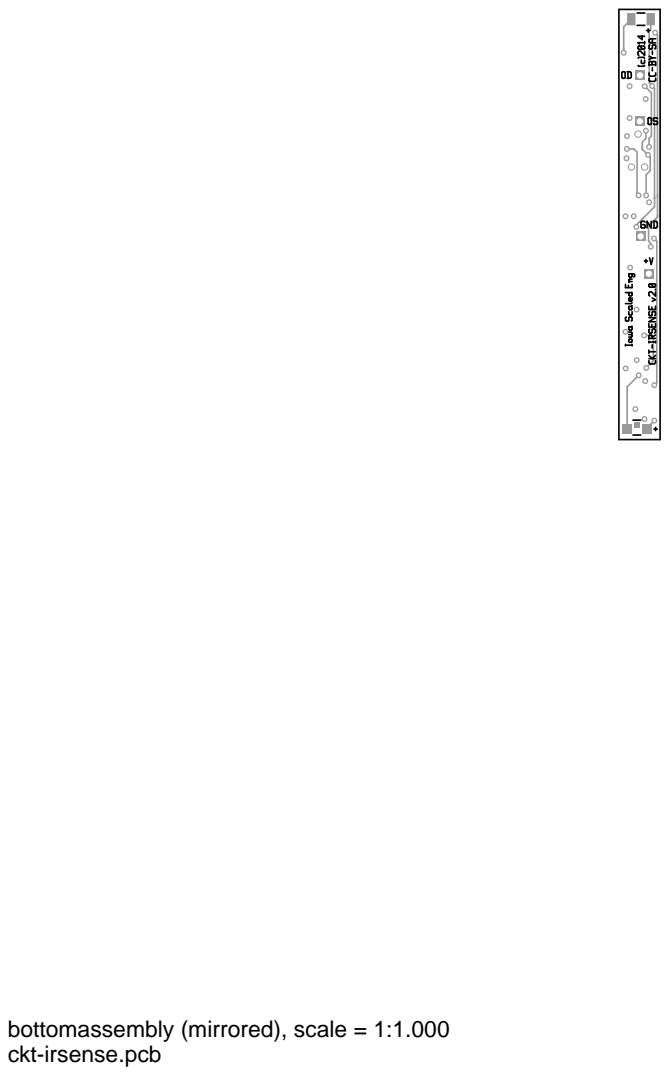
[picture p73: page 16]

bottomassembly (mirrored), scale = 1:1.000

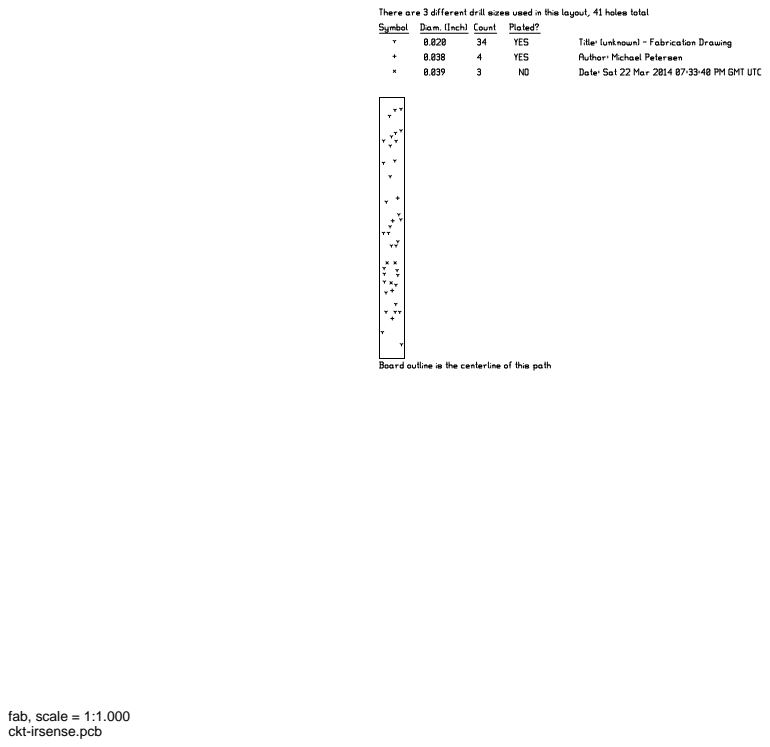
[picture p74: page 17]
fab, scale = 1:1.000
