IowaScaledEngineering/ckt-irsense/pg/ckt-irsense-v1.0-r656/ckt-irsense-pcb.pdf

# ckt-irsense.pcb

# 1. Table of Contents (This Page) Created on Sat Feb 22 21:32:07 2014

# 2. component 3. solder 4. plated-drill 5. unplated-drill 6. componentmask 7. soldermask 8. topsilk 9. bottomsilk 10. toppaste 11. bottompaste 12. topassembly 13. bottomassembly 14. fab

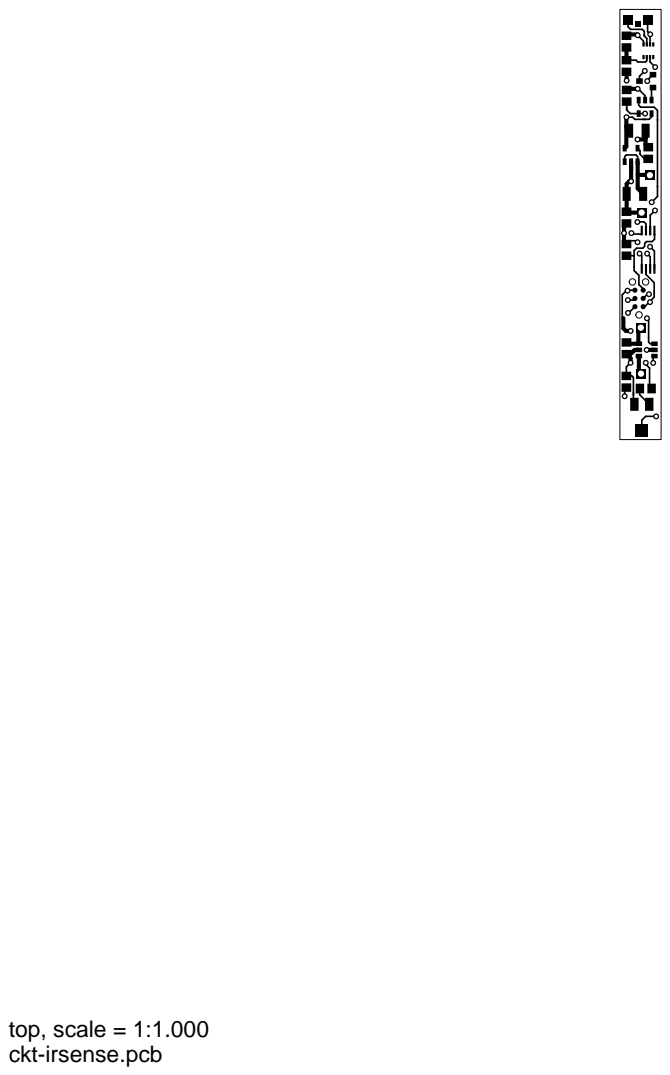
[picture p75: page 2]
top, scale = 1:1.000

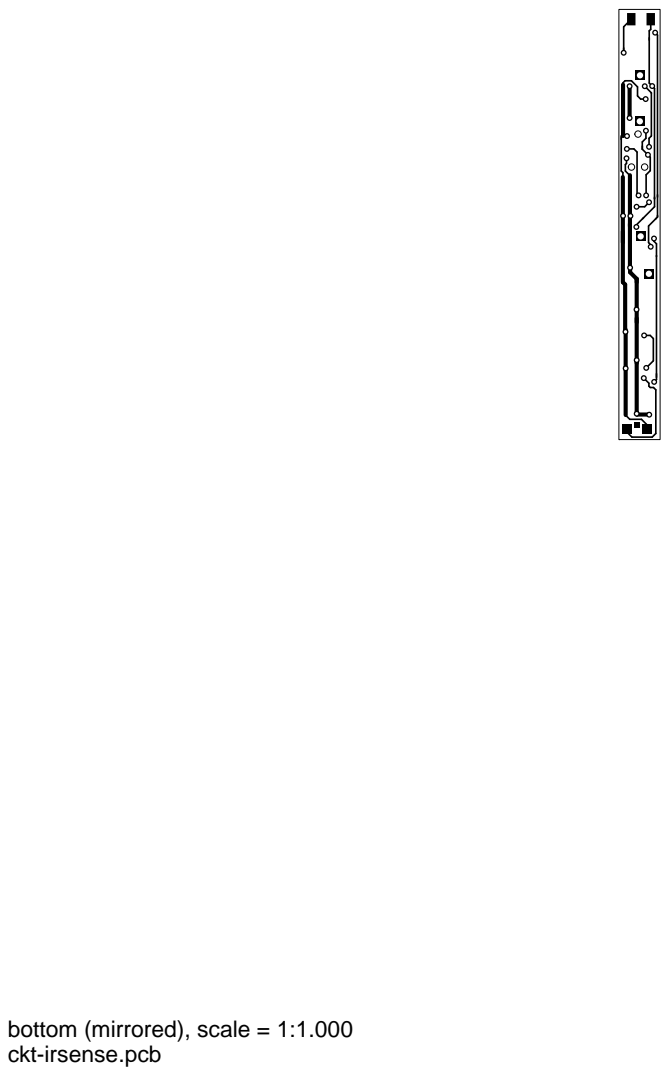
[picture p76: page 3]

bottom (mirrored), scale = 1:1.000

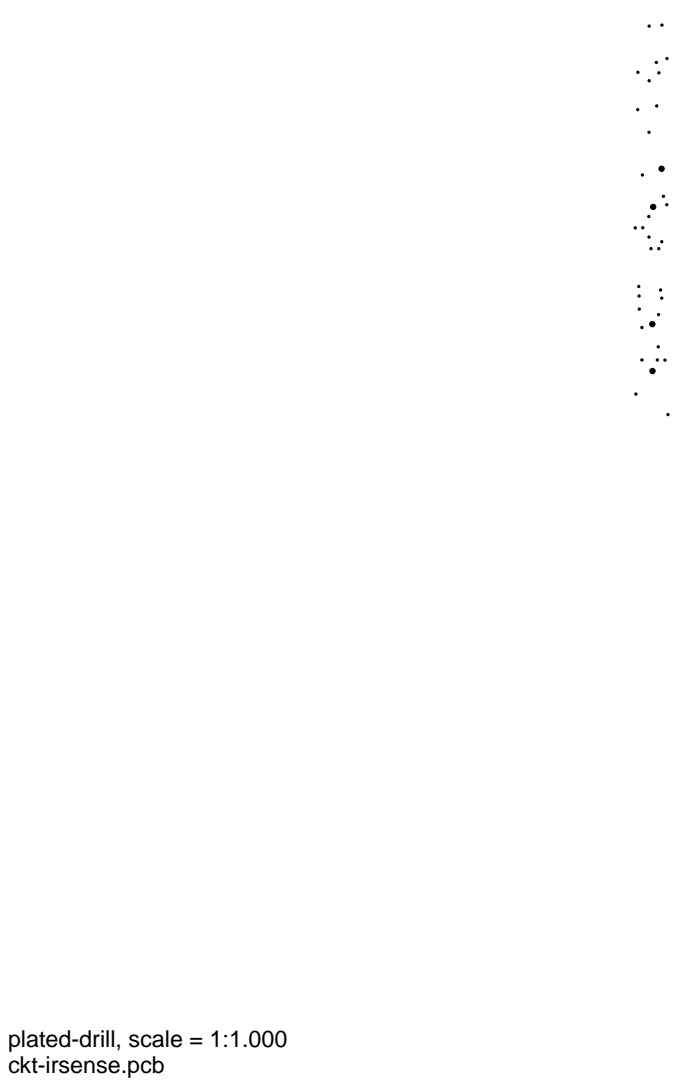
[picture p77: page 4]

plated-drill, scale = 1:1.000

unplated-drill, scale = 1:1.000

topmask, scale = 1:1.000 bottommask (mirrored), scale = 1:1.000

topsilk, scale = 1:1.000 bottomsilk (mirrored), scale = 1:1.000

toppaste, scale = 1:1.000 bottompaste (mirrored), scale = 1:1.000

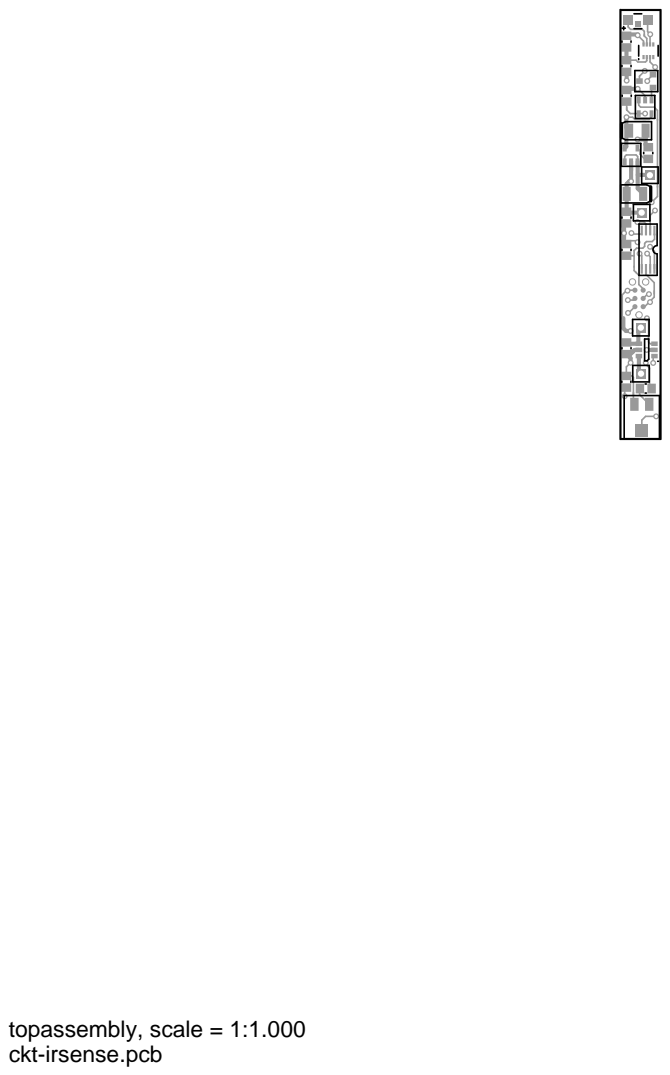
[picture p78: page 12]
topassembly, scale = 1:1.000

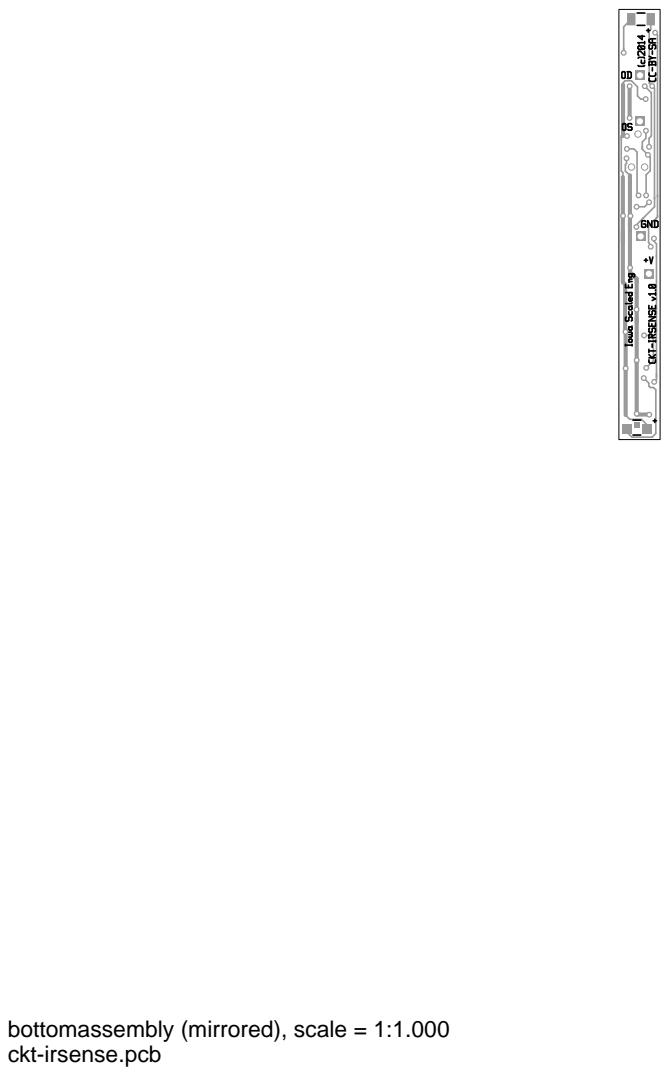
[picture p79: page 13]

bottomassembly (mirrored), scale = 1:1.000

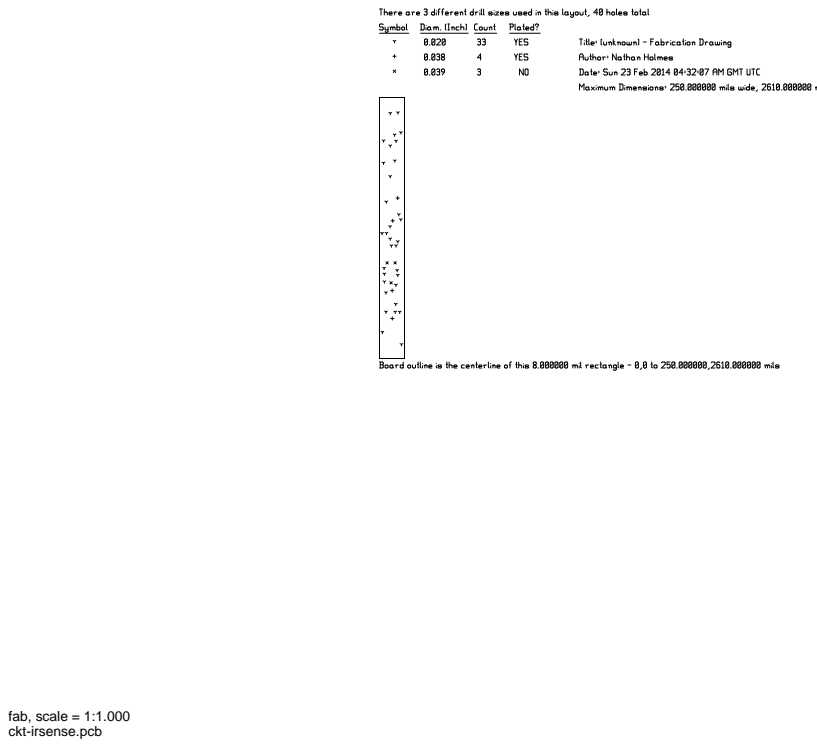
[picture p80: page 14]
fab, scale = 1:1.000
