IowaScaledEngineering/ckt-irsense/doc/usermanual/ckt-irsense-manual-print.pdf

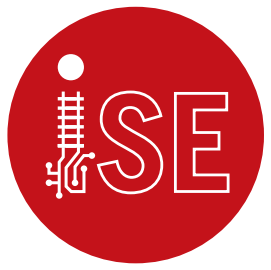
[picture p83: figure]

## www.iascaled.com • support@iascaled.com

## MANUAL

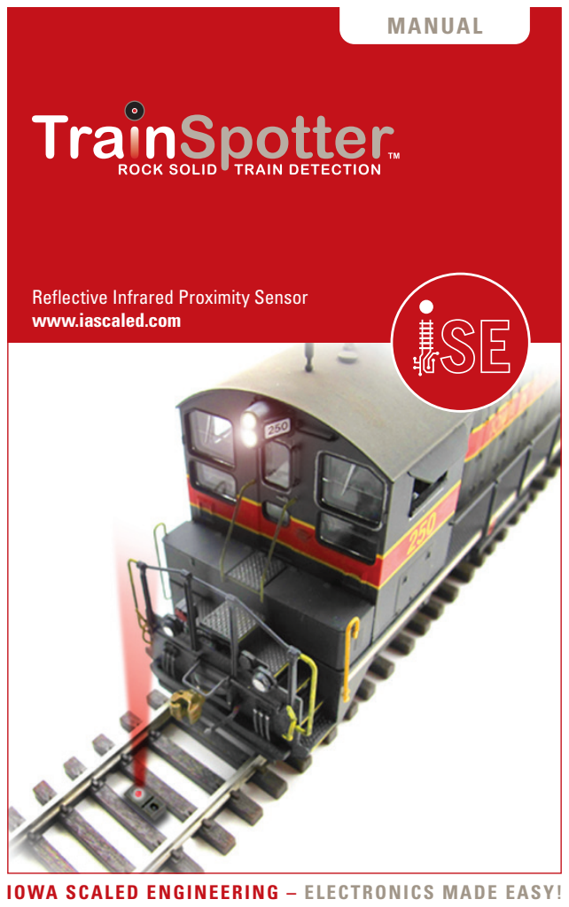
[picture p84: page 2]

Reflective Infrared Proximity Sensor
www.iascaled.com

IOWA SCALED ENGINEERING – ELECTRONICS MADE EASY!

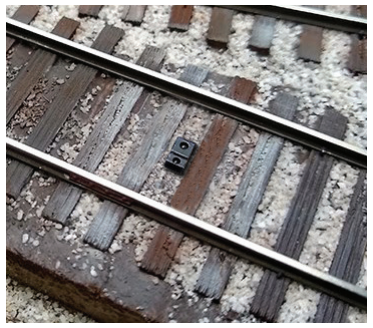
[picture p85: figure]

### 2 Reflective Infrared Proximity Sensor

The TrainSpotter is a simple infrared proximity sensor that makes detection of model railroad locomotives and rolling stock easy and reliable. Just place the sensor where its invisible light beam will reflect off the object of interest and you’re done - no time-consuming or frustrating adjustments! Based on modern silicon technology, this sensor is tolerant of ambient (background) lighting conditions, be it completely dark or under full lights, with no false triggering. Combined with a discrete under-track or beside-track installation, this low-profile sensor solves many of the challenges that plague other optical detector products.

Features
- Small size (0.25" x 2.25")
- No adjustment needed!
- Simple, discrete under-track installation
- Selectable release times
- Two opposite polarity, open-collector outputs (40V / 250mA capable)
- Tolerant of ambient (background) lighting conditions - no false triggering
- 24" pre-stripped wire leads (CKT-IRSENSE, CKT-IRSENSE-RA)
- Terminal blocks for easy connections (CKT-IRSENSE-2PC)
- Powered from 5V to 24V
- Optional mounting bracket available

Typical Applications
- Activate grade crossing signals
- Trigger sounds
- Build an automatic interchange
- Indicate end-of-track in hidden staging yards
- Detect block occupancy for signal systems

Reflective Infrared Proximity Sensor | 11

## Notes

### 10 Reflective Infrared Proximity Sensor

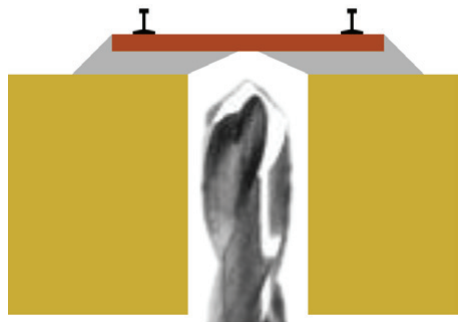
[picture p86: figure]
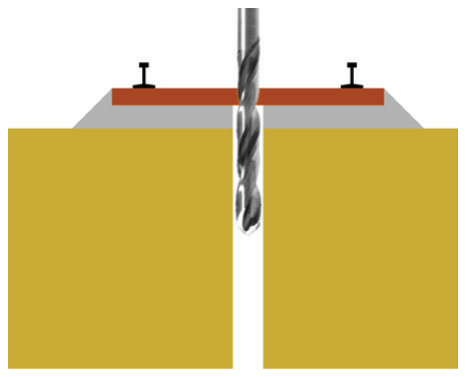
[picture p87: figure]
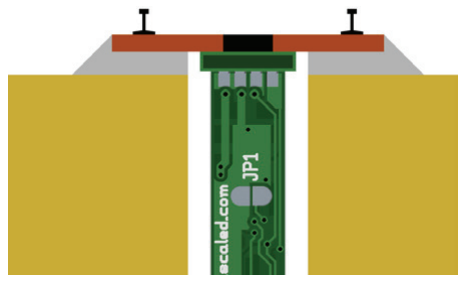
[picture p88: figure]

Reflective Infrared Proximity Sensor | 3

Installation
The TrainSpotter is designed to be installed up through the benchwork in a 3/8” (10 mm) hole. To install in existing track, first drill a 1/16” pilot hole between the ties. Then, from the bottom, drill a 3/8” hole up toward the track, using the pilot hole you just drilled as a guide. Work slowly and be very careful to not damage the ties (you might want to remove a couple of ties first and reinsert them after drilling the hole). Once the TrainSpotter is installed, be sure that both lenses are clear to shine up between any ties or ballast.
The TrainSpotter with Right-Angle Sensor (CKT-IRSENSE-RA) can be installed in a similar manner beside the track. Make sure the sensor points toward the track, is not obstructed, and will not reflect off any other stationary objects nearby.
The module is not naturally water resistant, so be careful when ballasting. Some amount of water resistance can be added by coating everything (other than the lenses) with liquid electrical tape or similar sealant. Be very careful not to cloud or cover the sensor lenses.
The TrainSpotter can be secured in the hole using a variety of methods such as hot glue or by using a mounting bracket. See the Iowa Scaled Engineering website for more details and to order a mounting bracket.
1/16" pilot hole | 3/8" mounting hole

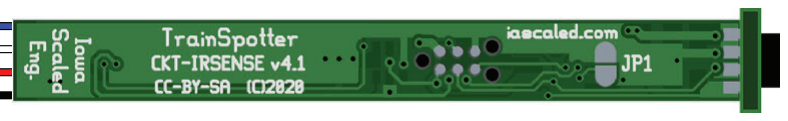
[picture p89: figure]
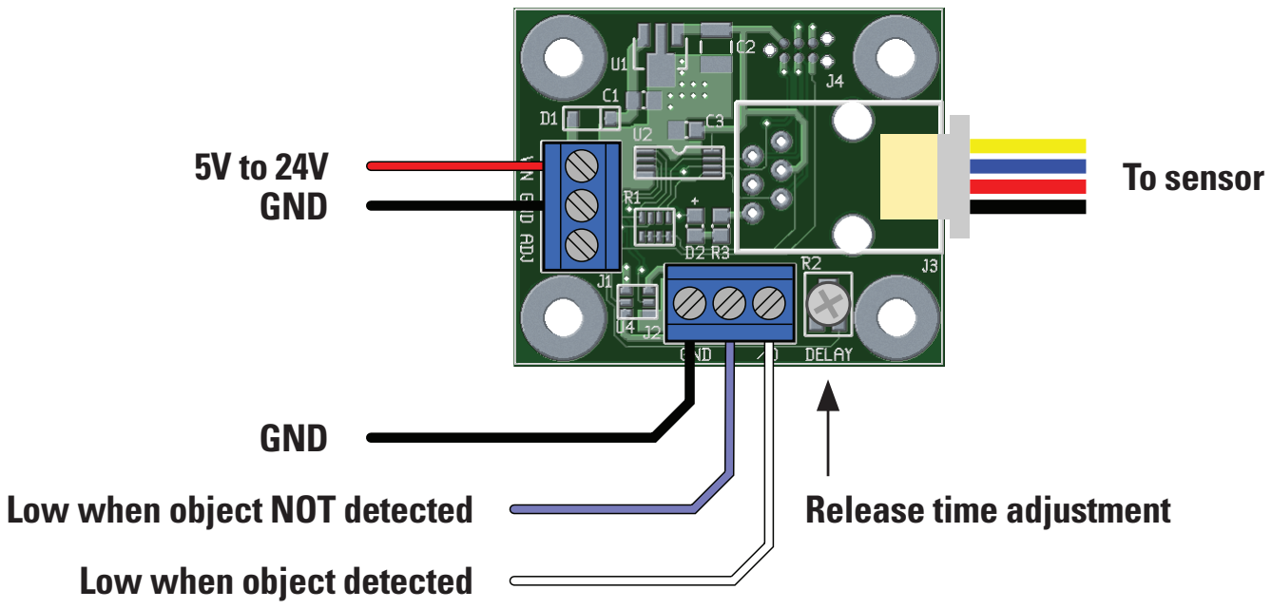
[picture p90: figure]
5V to 24V GND; GND; Low when object NOT detected; Low when object detected; Release Time Adjustment; Release time adjustment; To sensor

### 4 Reflective Infrared Proximity Sensor

Electrical Connections
Input power needs to be 5 to 24 volts of clean direct current (DC) for proper operation. Noisy power supplies may cause issues with detection, and supply voltages exceeding 24V DC may damage the device. The red wire should be connected to the positive side of the power supply and the black wire to the negative.
Two outputs are available, both of which are “open drain” (also known as “open collector”). This means that they act like a switch to the ground / negative lead. When an output is “active”, it will conduct current to ground. When an output is “inactive”, it will act like an open circuit and not pass any current. Each output can handle a maximum of 0.25 amps, and should be exposed to no more than a 40V DC supply.
The white output is active when the sensor is detecting an object. The blue output is active when the sensor is not detecting an object.

5V - 24V
GND

Low when object NOT detected Low when object detected

Low when object detected
5V to 24V
GND

Low when object NOT detected

### Figure 1: TrainSpotter Connections (CKT-IRSENSE, CKT-IRSENSE-RA)

### TrainSpotter with Remote Sensor Connections (CKT-IRSENSE-2PC)

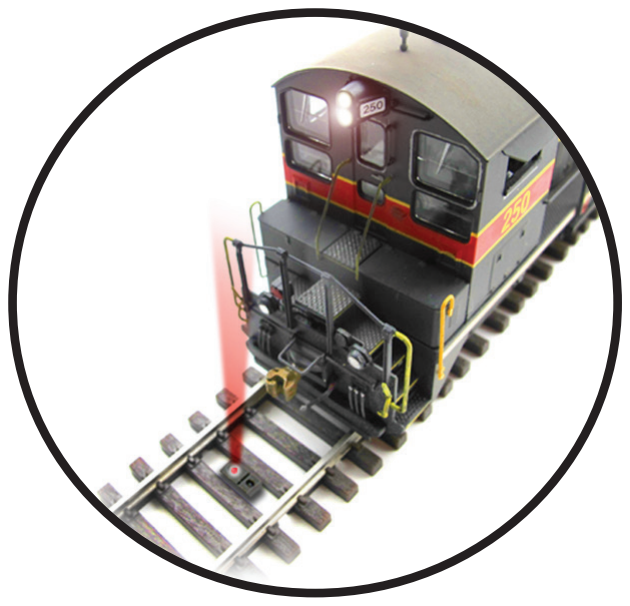
[picture p91: figure]
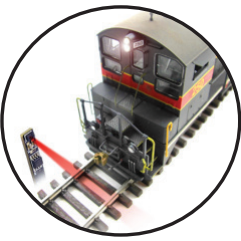
[picture p92: figure]
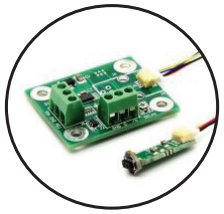
[picture p93: figure]

Reflective Infrared Proximity Sensor | 9

Ordering Information

MODEL | DESCRIPTION
CKT-IRSENSE | TrainSpotter
CKT-IRSENSE-RA | TrainSpotter with right-angle sensor
CKT-IRSENSE-2PC | TrainSpotter with remote sensor

### 8 Reflective Infrared Proximity Sensor

Open Design
Iowa Scaled Engineering is committed to creating open designs that users are free
to build, modify, adapt, improve, and share with others.
The design of the TrainSpotter hardware is open source hardware, and is made available under the terms of the Creative Commons Attribution-Share Alike v3.0 license, a copy of which is available from: https://creativecommons.org/licenses/by-sa/3.0/

Design files can be found on the Iowa Scaled Engineering website: https://www.iascaled.com/store/CKT-IRSENSEhttps://www.iascaled.com/store/CKT-IRSENSE-RAhttps://www.iascaled.com/store/CKT-IRSENSE-2PC

The official Iowa Scaled Engineering firmware for the TrainSpotter is free software: you can redistribute it and/or modify it under the terms of the GNU General Public License as published by the Free Software Foundation, either version 3 of the License, or (at your option) any later version. A copy of the GNU GPL can be found at: https://www.gnu.org/licenses/gpl.html

New firmware can be flashed into the CKT-IRSENSE and CKT-IRSENSE-RA through J1 or the CKT-IRSENSE-2PC through J4. The six land pads implement the standard AVR 6-pin ISP header on a connector compatible with the Tag-Connect TC2030 cable. Stable releases of firmware and source code can be found on the Iowa Scaled Engineering website.

Reflective Infrared Proximity Sensor | 5

Driving Other Circuits
If a logic level output is needed to drive a grade crossing controller, for instance, use
a 4.7k to 10k ohm resistor to pull the output up to the positive logic supply. See Figure 3. The TrainSpotter should share the same ground connection (black wire) with the circuit being driven.
To drive an LED, connect a current-limiting resistor in series with the LED and connect the LED cathode to the TrainSpotter output as shown in Figure 4. A similar method to drive a relay is shown in Figure 5.
Since the outputs are open drain, outputs from multiple sensors can be connected in parallel to create one common output. This common output will pull low whenever any one sensor pulls its output low.

### Figure 3: Logic Level Output

5

10

+5V

10K

Logic level output

CKT-IRSENSE blue
or white wire

### Figure 4: Driving an LED

1

1K

CKT-IRSENSE blue
or white wire

CKT-IRSENSE red wire or
positive power supply

### Figure 5: Driving a Relay

CKT-IRSENSE blue
or white wire

CKT-IRSENSE red wire or
positive power supply

To other circuits

### 6 Reflective Infrared Proximity Sensor

Sensing Distance
The sensor is pre-calibrated to a typical detection range of ~1.5” and needs no user adjustment for most applications. However, the detection distance will vary based on the reflectivity of the object being sensed. If other ranges are needed, contact us for custom programmed devices. The detection range can be adjusted from approximately 0.5” to 3”.

Activation Time
The activation time is preset to 0.1 seconds. The outputs will indicate an object is detected if the object is present over the sensor for 2 consecutive readings spaced 100ms apart. This helps eliminate errant readings. As a consequence, there will be
a slight (0.1s) delay before an object is detected. For most model railroad applications, this is not an issue. If longer (or shorter) activation times are required, we can provide custom programmed devices. Please contact us with your requirements.

Release Time
The default release time is preset to 0.1 seconds. The outputs will indicate an object is not detected if the sensor is clear for 2 consecutive readings spaced 100ms apart. To stop the outputs from toggling, for example, in the spaces between rolling stock as it travels over the sensor, the release time can be increased. On the single piece versions (CKT-IRSENSE, CKT-IRSENSE-RA) the release time can be changed to
5 seconds by shorting jumper JP1 on the back side. Solder this jumper closed to activate the longer delay.
For the version with remote sensor (CKT-IRSENSE-2PC), there is an adjustment potentiometer (variable resistor) located next to the output terminal block. Rotating it clockwise will increase the release time, whereas rotating it counter-clockwise will decrease the release time. The maximum release time is 23 seconds.
Custom delay times up to 23 minutes are available for any version of the sensor upon request.

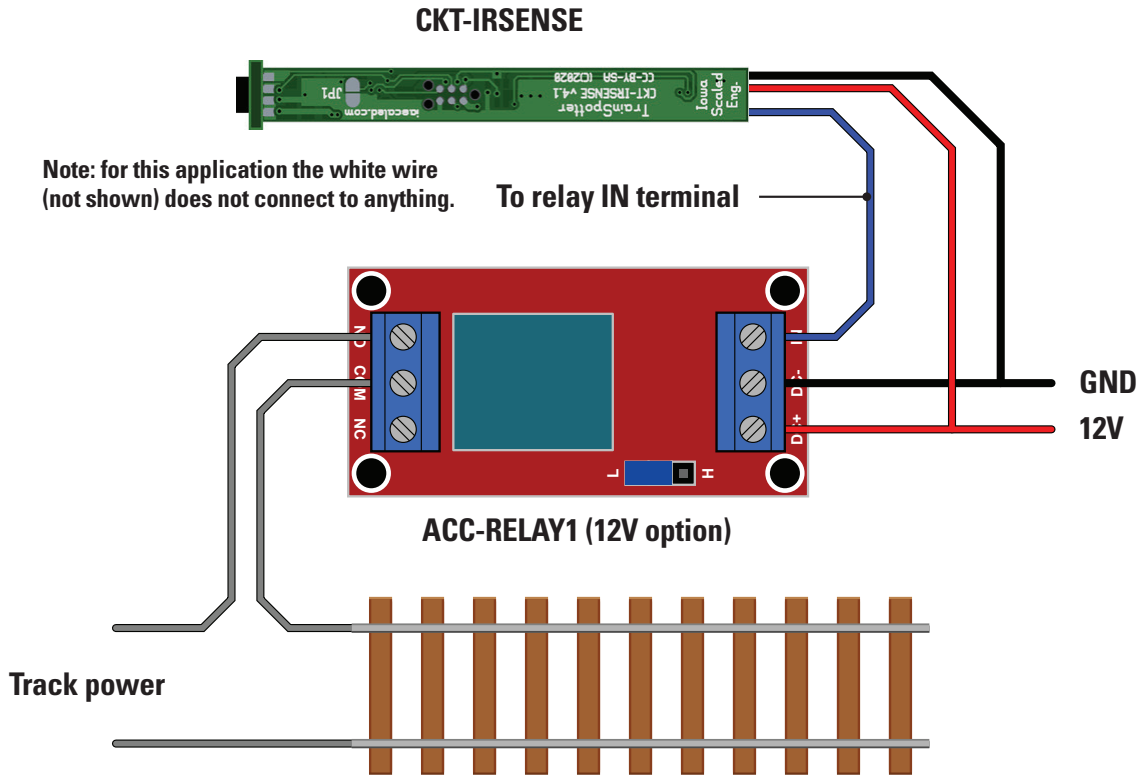
[picture p94: figure]
NO COM NC; H ACC-RELAY1 (12V Option); Track Power; CKT-IRSENSE; ACC-RELAY1 (12V option); GND 12V; Track power

Reflective Infrared Proximity Sensor | 7

Automatic Interchange
An automated interchange track, similar to the one described in the September 2006 issue of Model Railroader, can be assembled using a TrainSpotter and a relay module (ACC-RELAY1). The TrainSpotter is placed near the switch end of the interchange track. When the sensor is covered by a piece of rolling stock, the blue output line is released, causing the relay module (configured to activate with a low input) to be in the normal position. The normally-open (NO) contacts of the relay cut track power.
After a train picks up the cars covering the sensor, the blue output line then pulls low. This causes the relay to activate, closing the circuit between the COM and NO terminals, and applying power to the track. The locomotive is configured to push another cut of cars forward until they cover the sensor. At that point, track power is once again cut and the cars are available to be picked up by the next train.
A longer release time is helpful in this application to delay the time between cars being picked up and when the locomotive begins to push the next cut of cars. The variable delay time, up to 23 seconds, of the TrainSpotter with Remote Sensor (CKT-IRSENSE-2PC) is useful in this case. Or, contact us for custom delay times up to 23 minutes on any version of the TrainSpotter.

### Figure 6: Automatic Interchange

Note: for this application the white wire
(not shown) does not connect to anything. To relay IN terminal
