IowaScaledEngineering/ckt-irsense/doc/usermanual/installation.png

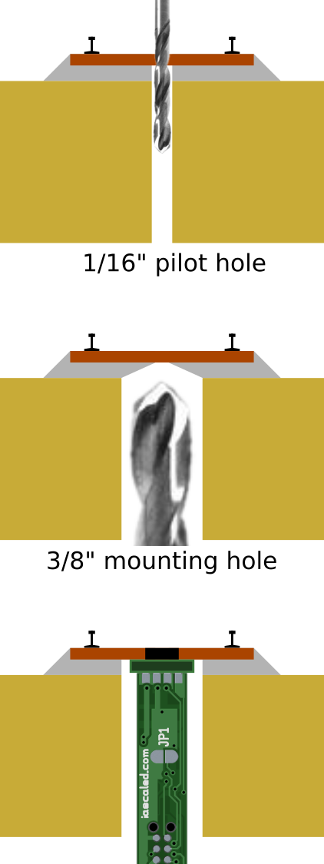
doc/usermanual/installation.png
