IowaScaledEngineering/ckt-irsense/pg/test-irsense-v1.1-36e9364/test-irsense-pcb.pdf

# test-irsense.pcb

# 1. Table of Contents (This Page) Created on Mon Dec 12 20:17:30 2016

# 2. top 3. bottom 4. plated-drill 5. componentmask 6. soldermask 7. topsilk 8. bottomsilk 9. toppaste 10. topassembly 11. bottomassembly 12. fab

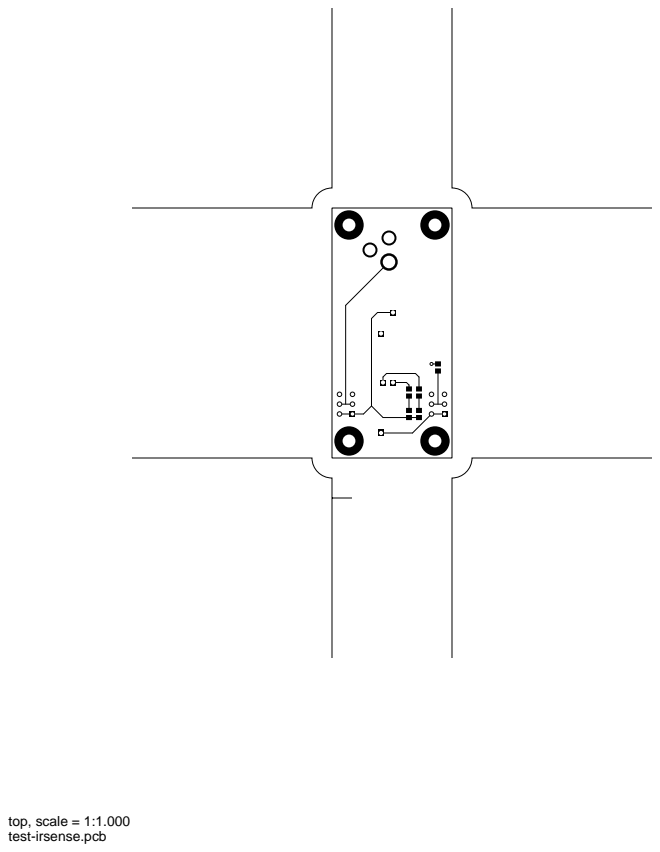
[picture p125: page 2]
top, scale = 1:1.000

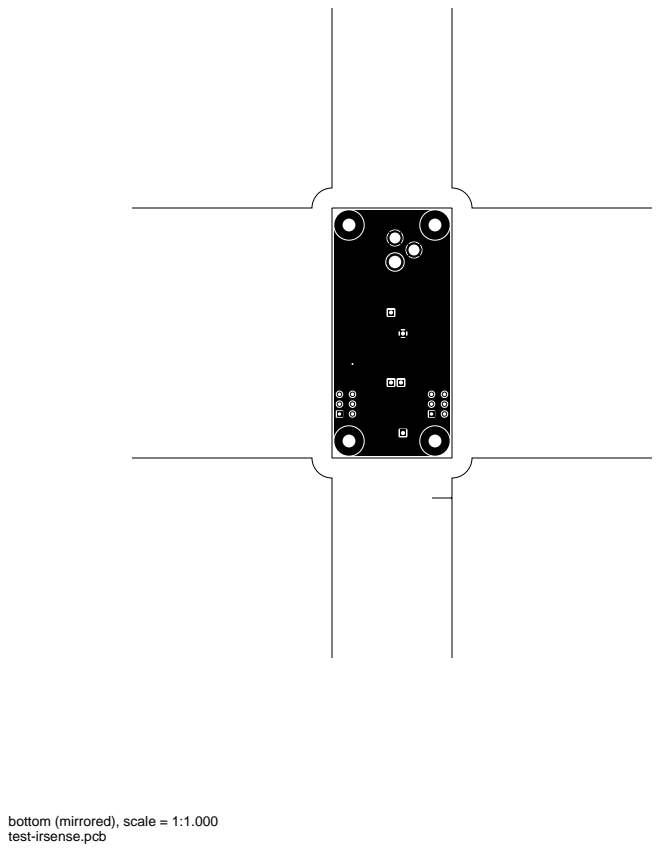
[picture p126: page 3]

bottom (mirrored), scale = 1:1.000

plated-drill, scale = 1:1.000

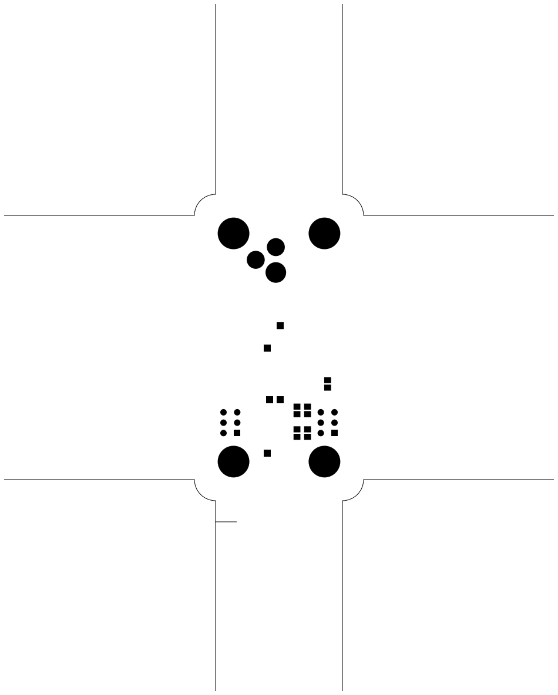
[picture p127: figure]

topmask, scale = 1:1.000

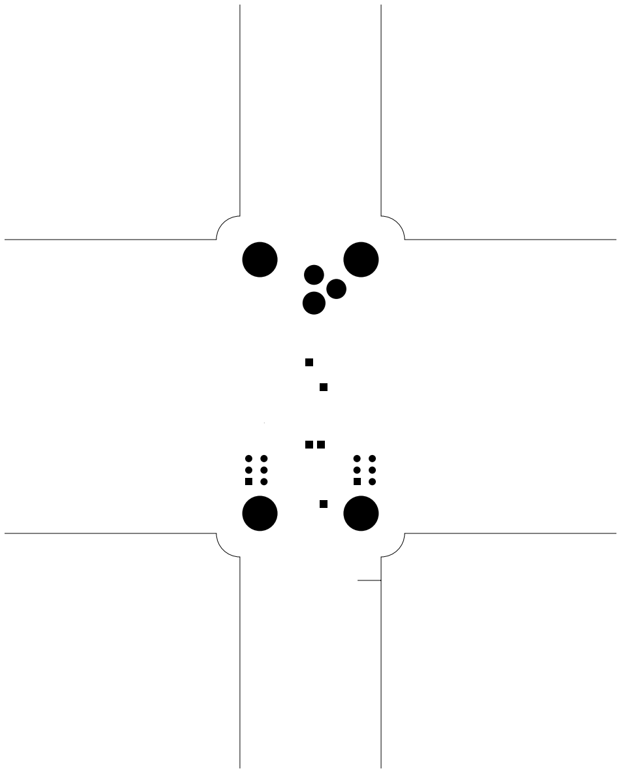
[picture p128: figure]

bottommask (mirrored), scale = 1:1.000

topsilk, scale = 1:1.000

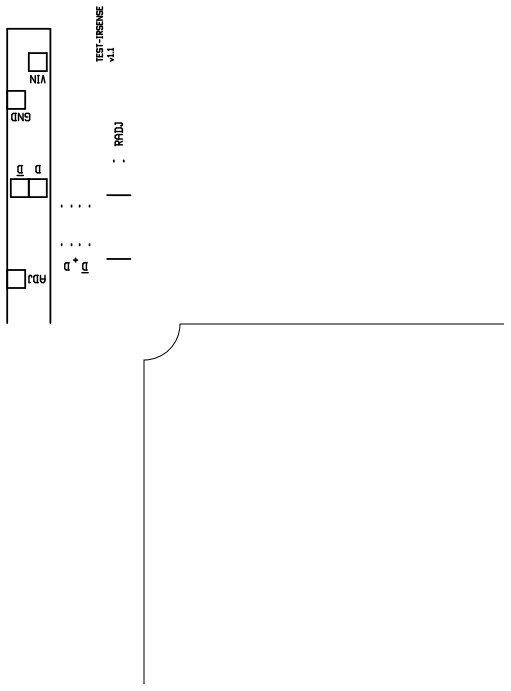
[picture p129: figure]

bottomsilk (mirrored), scale = 1:1.000

toppaste, scale = 1:1.000

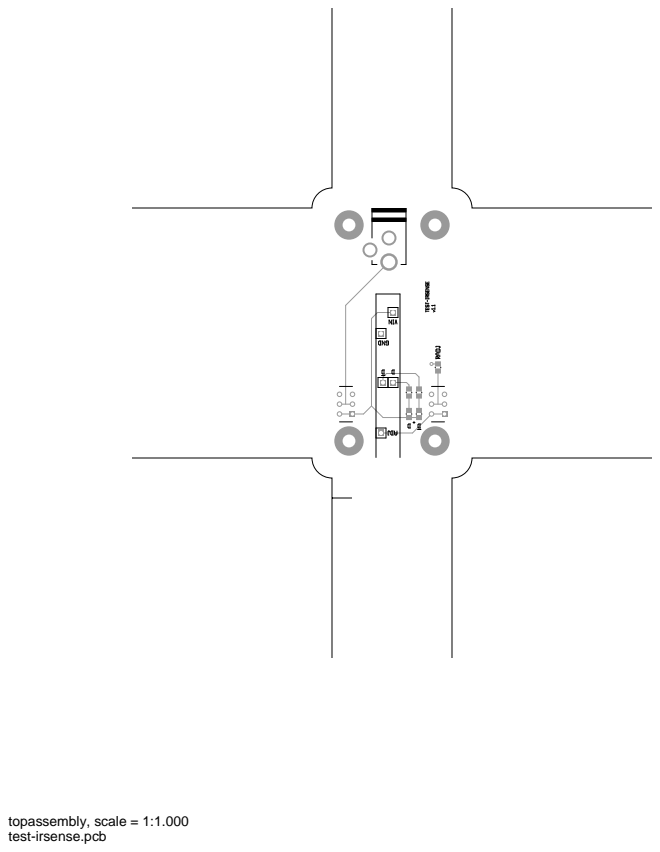
[picture p130: page 10]
topassembly, scale = 1:1.000

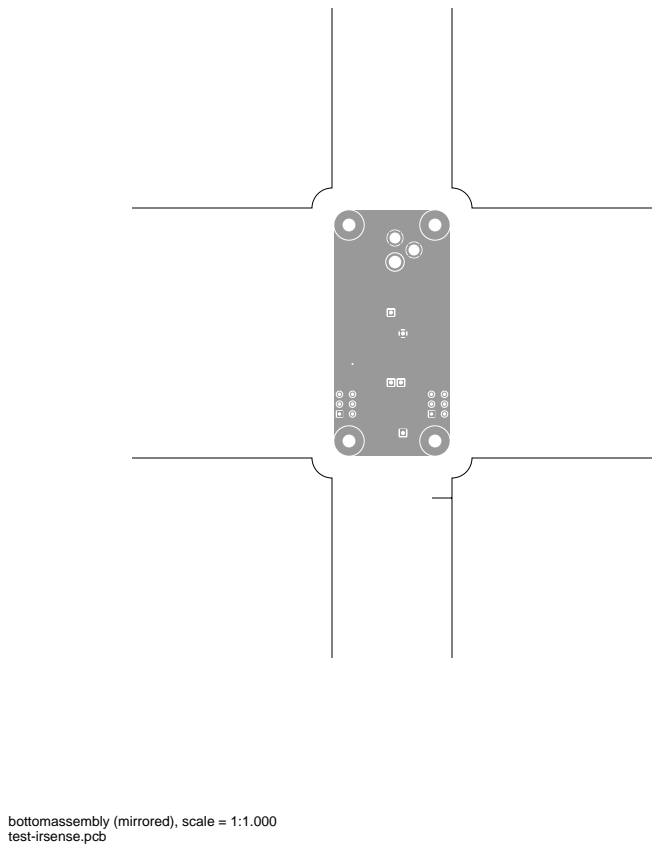
[picture p131: page 11]

bottomassembly (mirrored), scale = 1:1.000

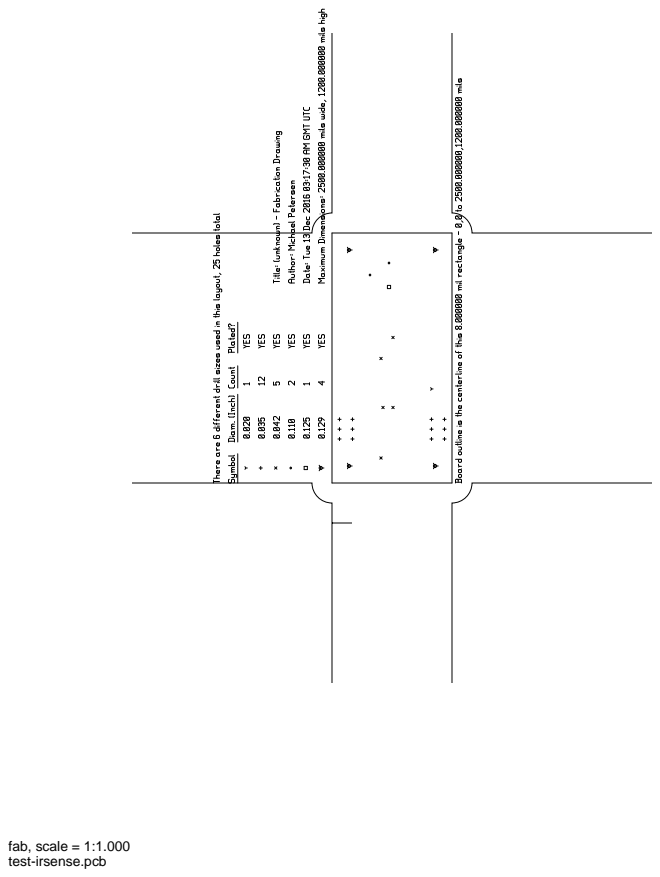
[picture p132: page 12]
fab, scale = 1:1.000
