IowaScaledEngineering/ckt-irsense/pg/test-irsense-v1.0-2aea66e/test-irsense-pcb.pdf

# test-irsense.pcb

# 1. Table of Contents (This Page) Created on Fri Jan 29 20:31:43 2016

# 2. top 3. bottom 4. outline 5. plated-drill 6. componentmask 7. soldermask 8. topsilk 9. bottomsilk 10. toppaste 11. topassembly 12. bottomassembly 13. fab

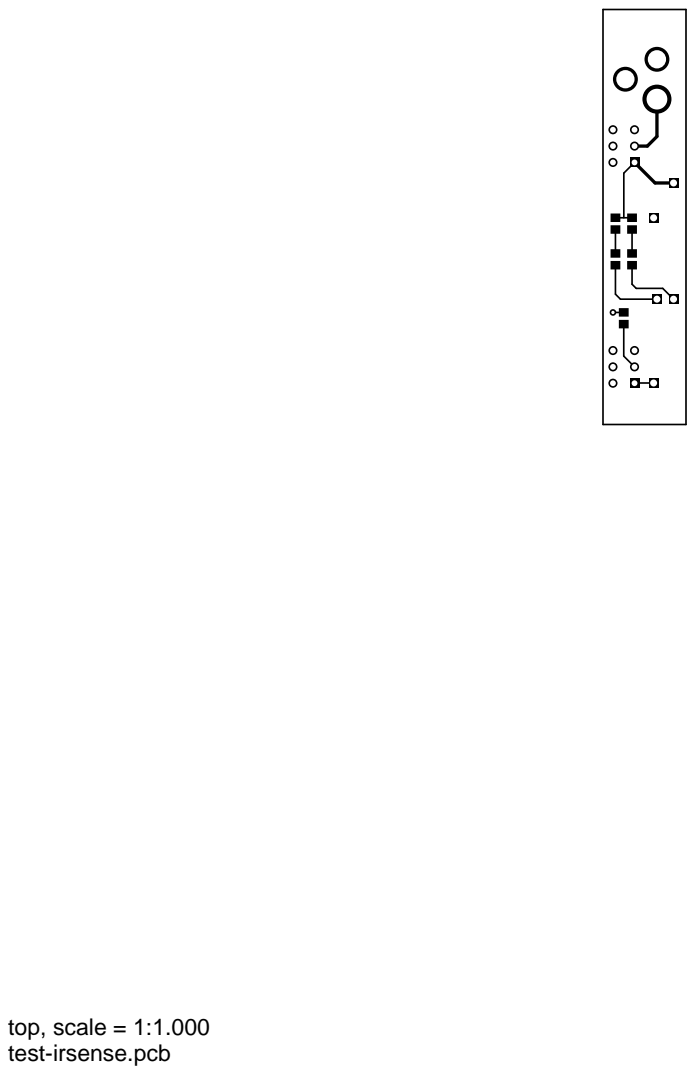
[picture p133: page 2]
top, scale = 1:1.000

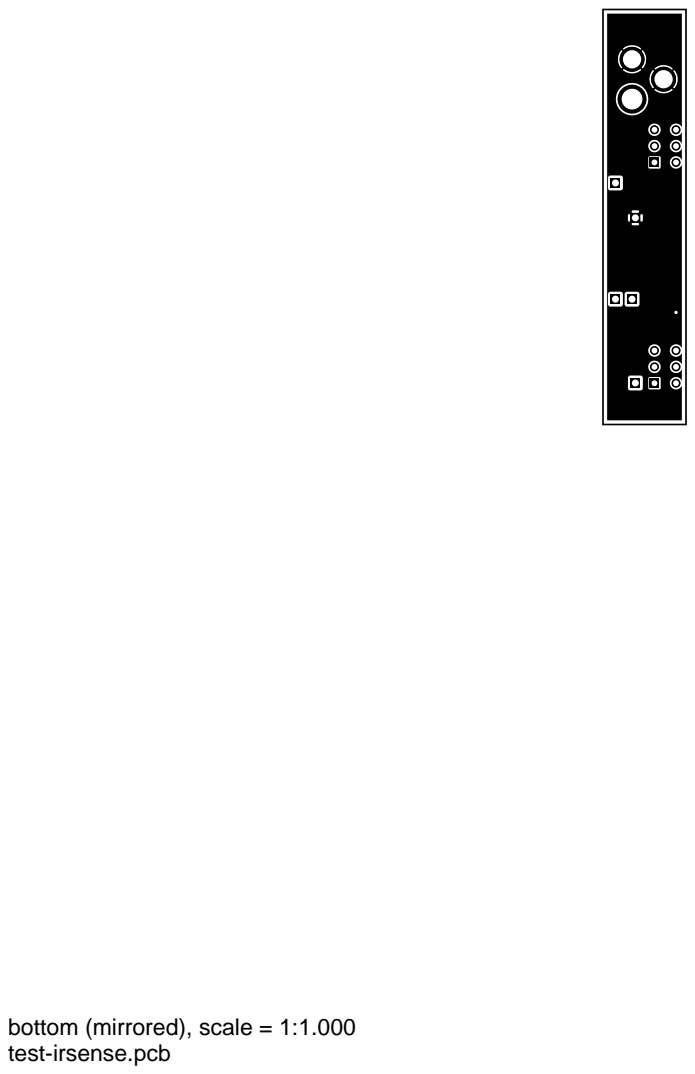
[picture p134: page 3]

bottom (mirrored), scale = 1:1.000

outline, scale = 1:1.000 plated-drill, scale = 1:1.000

topmask, scale = 1:1.000 bottommask (mirrored), scale = 1:1.000

topsilk, scale = 1:1.000 bottomsilk (mirrored), scale = 1:1.000

toppaste, scale = 1:1.000

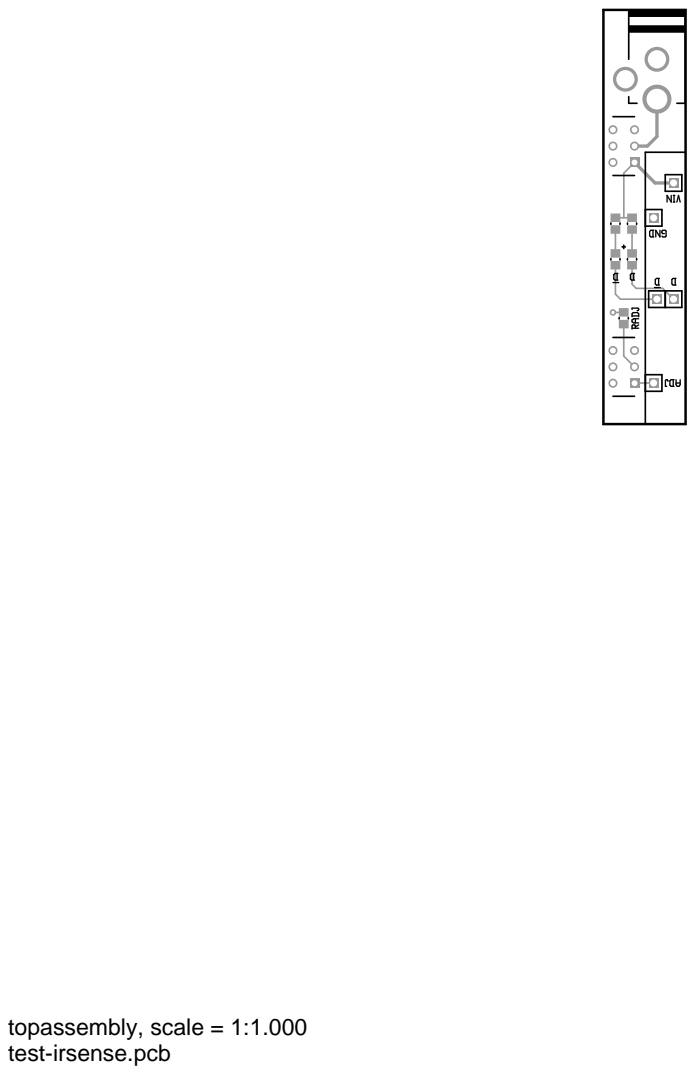
[picture p135: page 11]
topassembly, scale = 1:1.000

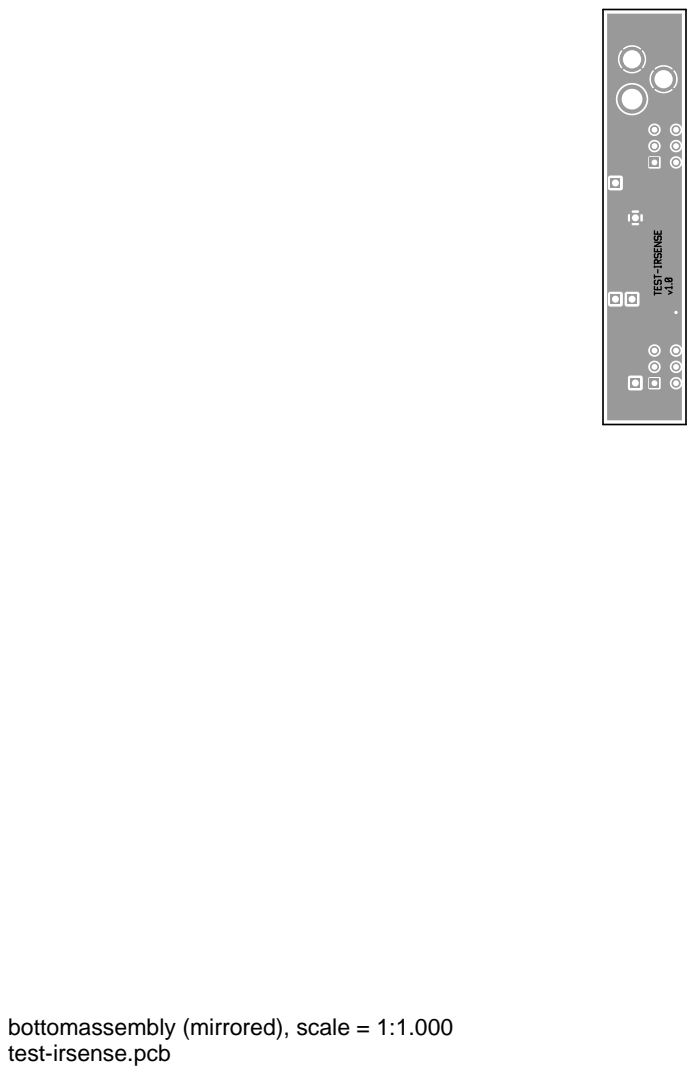
[picture p136: page 12]

bottomassembly (mirrored), scale = 1:1.000

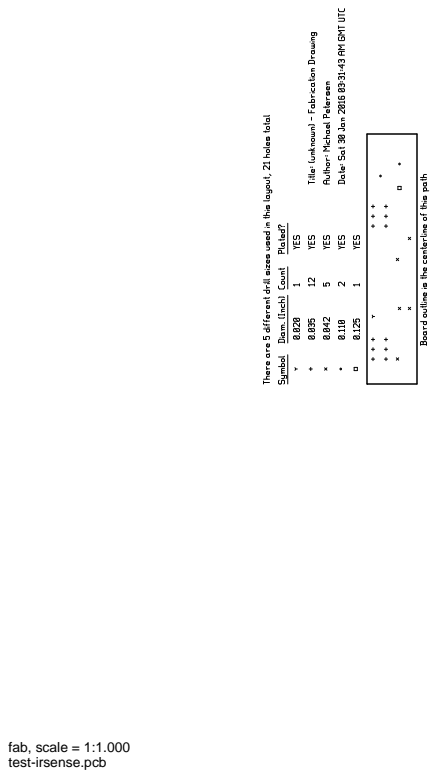
[picture p137: page 13]
fab, scale = 1:1.000
