IowaScaledEngineering/ckt-irsense/pg/ckt-irsense-sns-panel-3x-v1.2-b9ed279/ckt-irsense-sns-panel-3x-pcb.pdf

# ckt-irsense-sns-panel-3x.pcb

# 1. Table of Contents (This Page) Created on Thu Oct 28 09:19:50 2021

# 2. top 3. bottom 4. outline 5. plated-drill 6. componentmask 7. soldermask 8. topsilk 9. bottomsilk 10. toppaste 11. topassembly 12. bottomassembly 13. fab

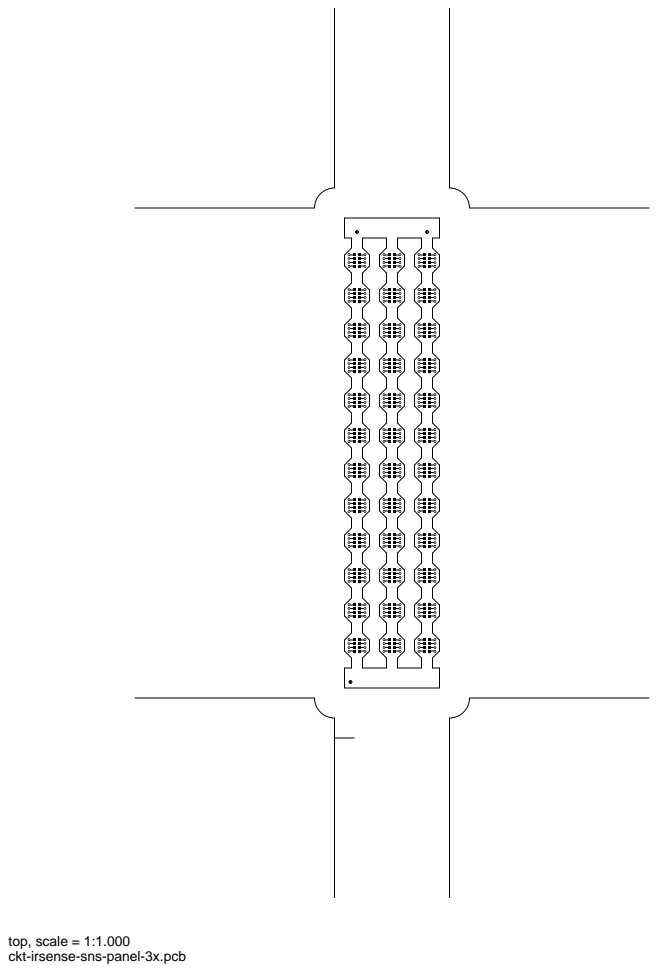
[picture p187: page 2]
top, scale = 1:1.000

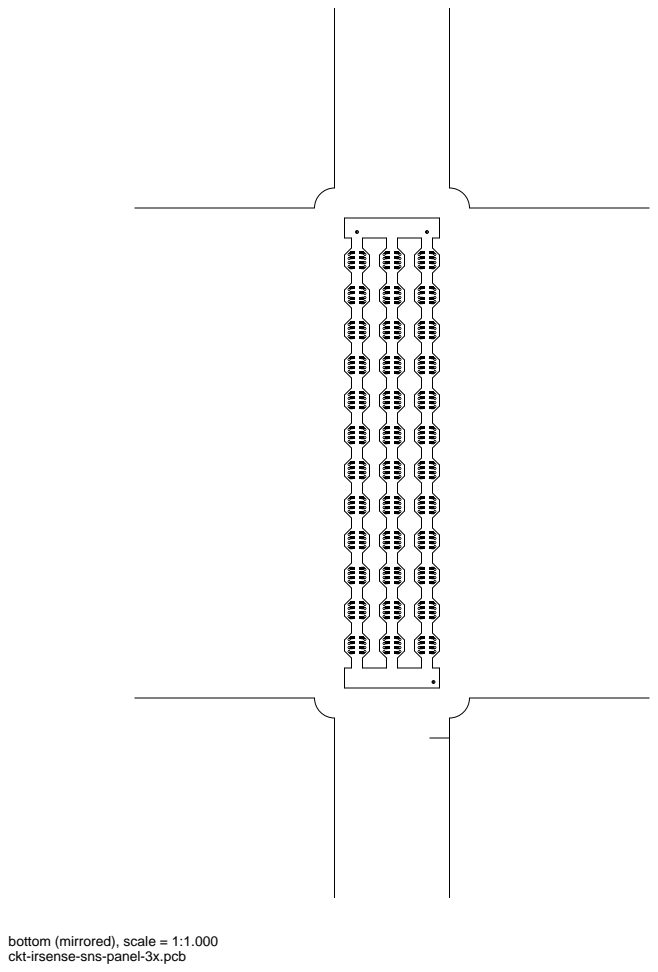
[picture p188: page 3]

bottom (mirrored), scale = 1:1.000

outline, scale = 1:1.000

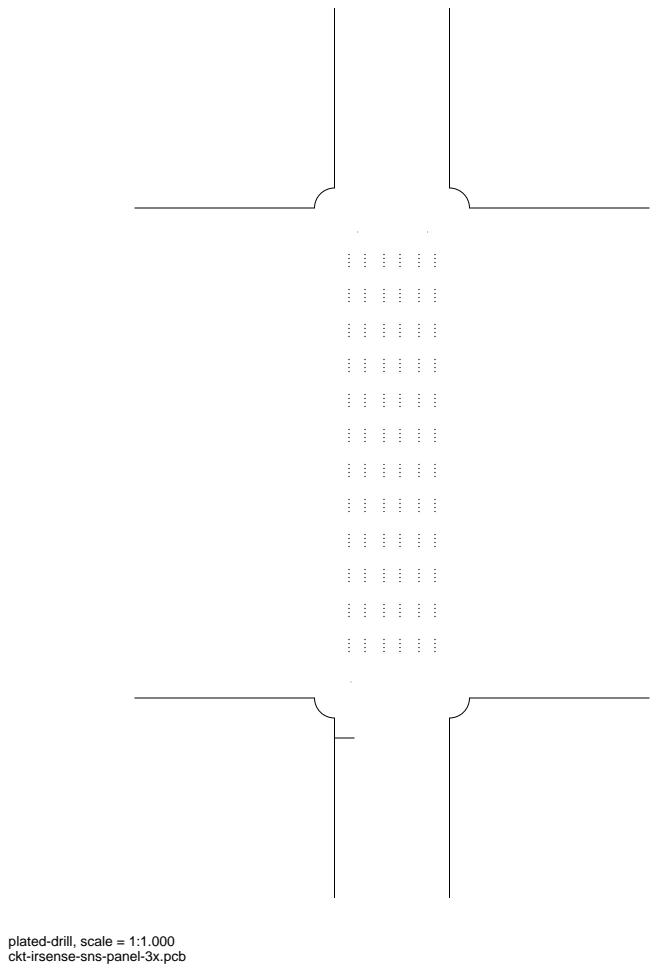
[picture p189: page 5]

plated-drill, scale = 1:1.000

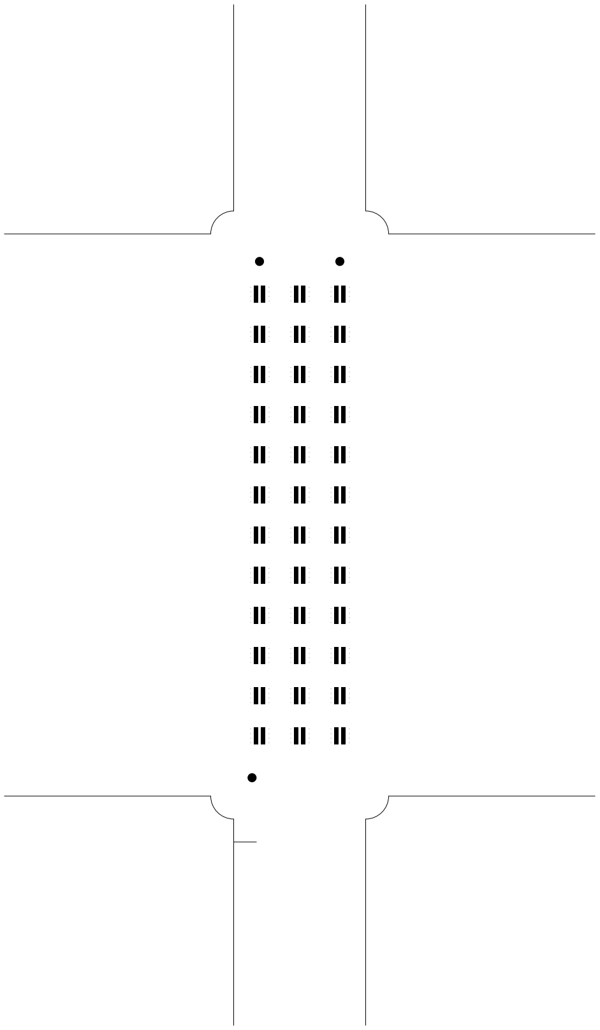
[picture p190: figure]

topmask, scale = 1:1.000

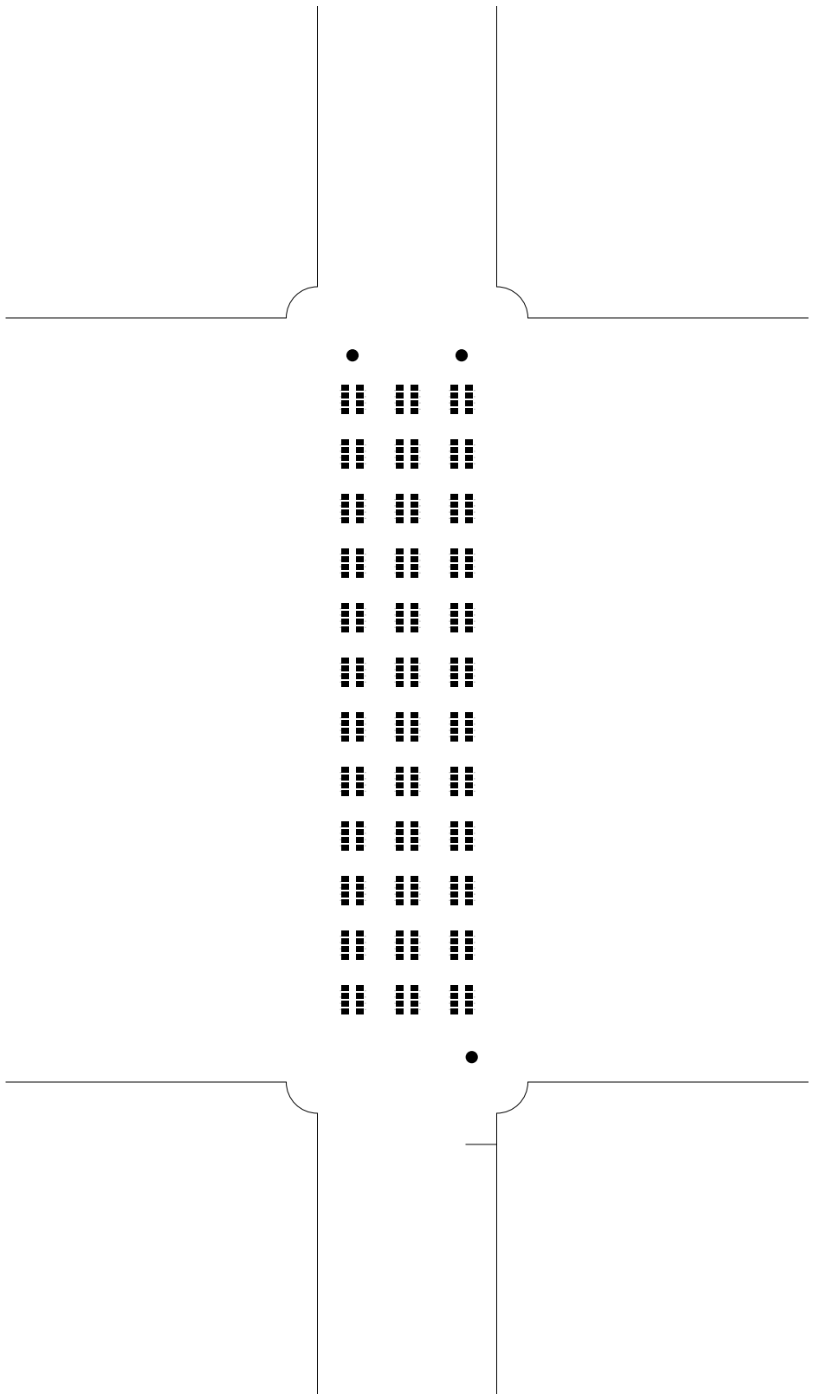
[picture p191: figure]

bottommask (mirrored), scale = 1:1.000

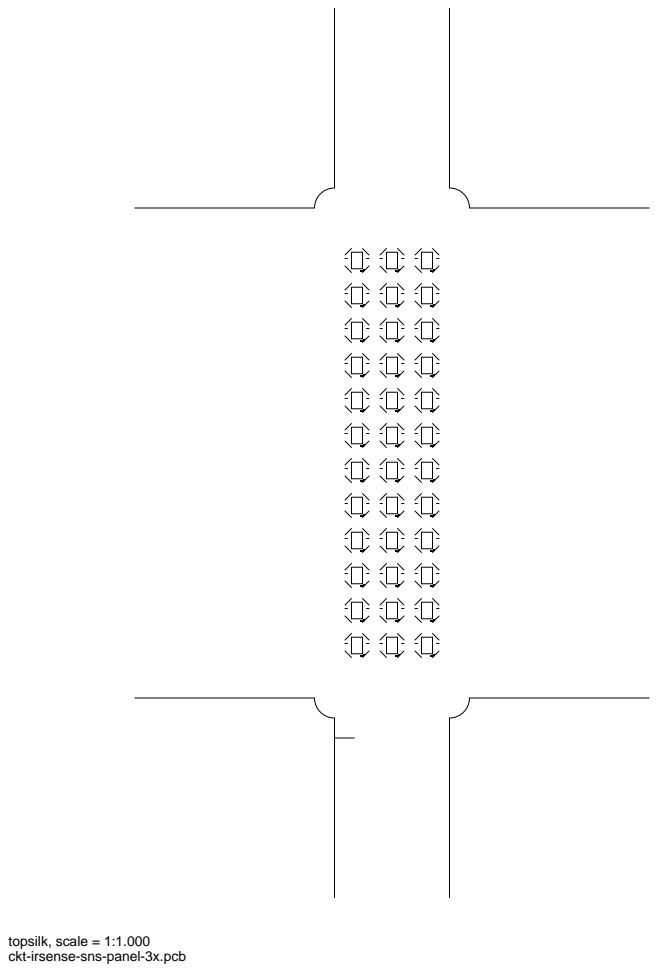
[picture p192: page 8]
topsilk, scale = 1:1.000

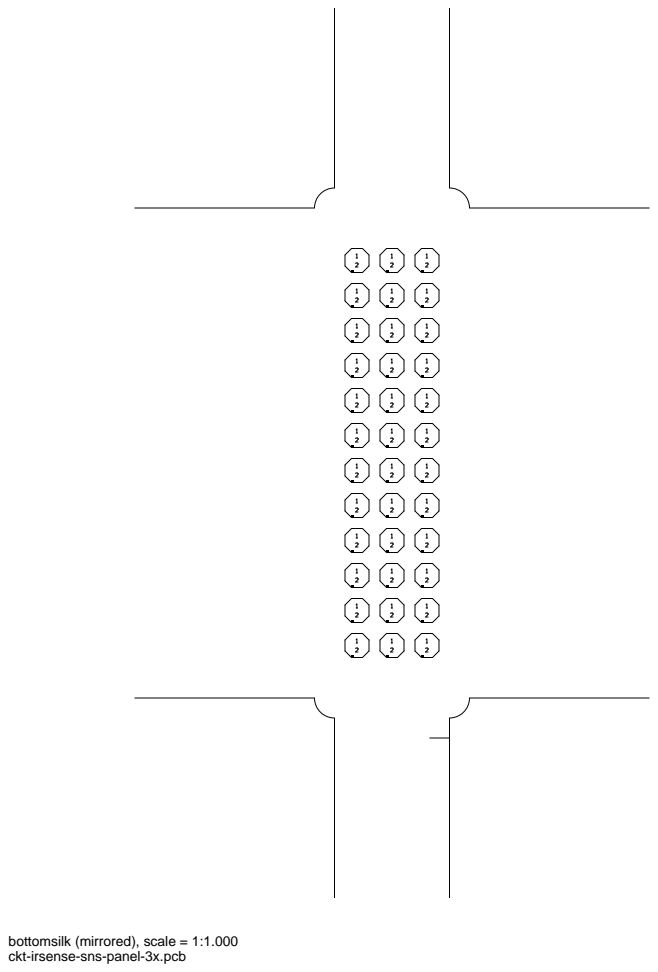
[picture p193: page 9]

bottomsilk (mirrored), scale = 1:1.000

toppaste, scale = 1:1.000

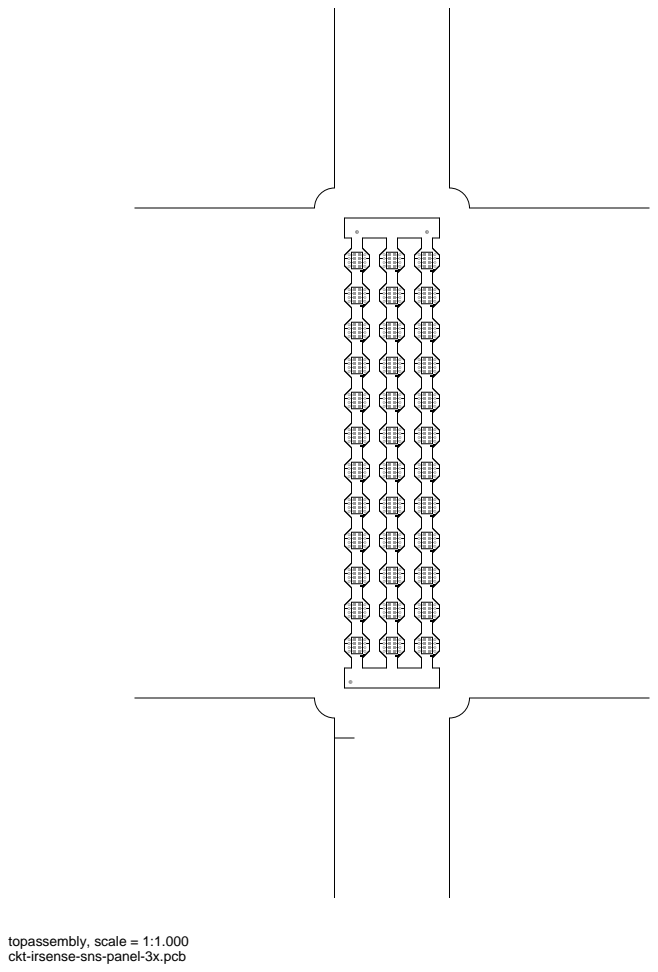
[picture p194: page 11]
topassembly, scale = 1:1.000

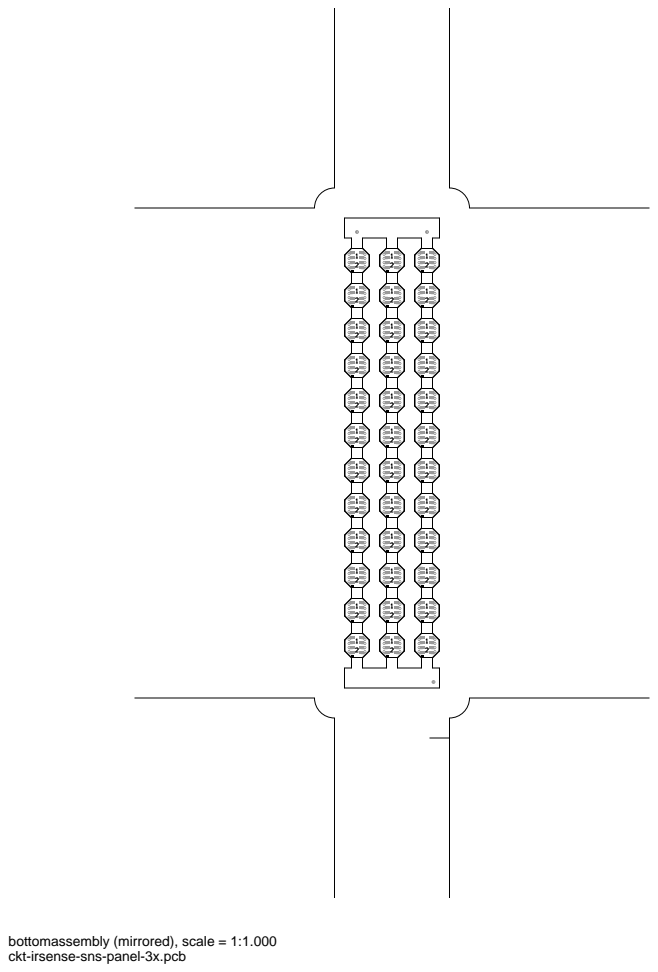
[picture p195: page 12]

bottomassembly (mirrored), scale = 1:1.000

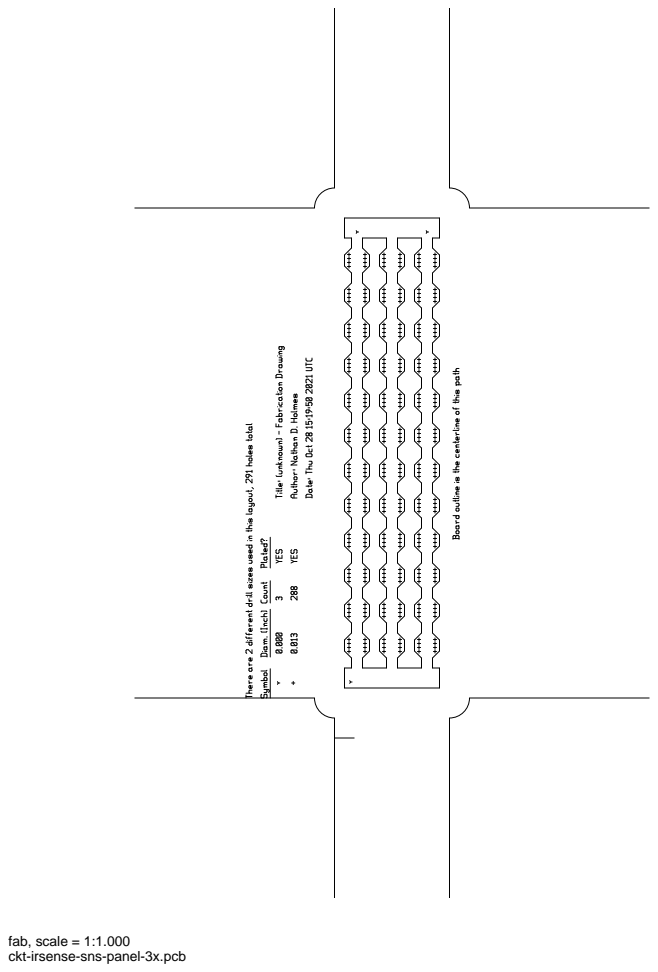
[picture p196: page 13]
fab, scale = 1:1.000
