IowaScaledEngineering/ckt-irsense/pg/i2c-irsense-panel-v2.1.txt-c6e3c9a/i2c-irsense-panel-pcb.pdf

# i2c-irsense-panel.pcb

# 1. Table of Contents (This Page) Created on Wed Feb 24 20:30:47 2021

# 2. top 3. bottom 4. outline 5. plated-drill 6. unplated-drill 7. componentmask 8. soldermask 9. topsilk 10. bottomsilk 11. toppaste 12. topassembly 13. bottomassembly 14. fab

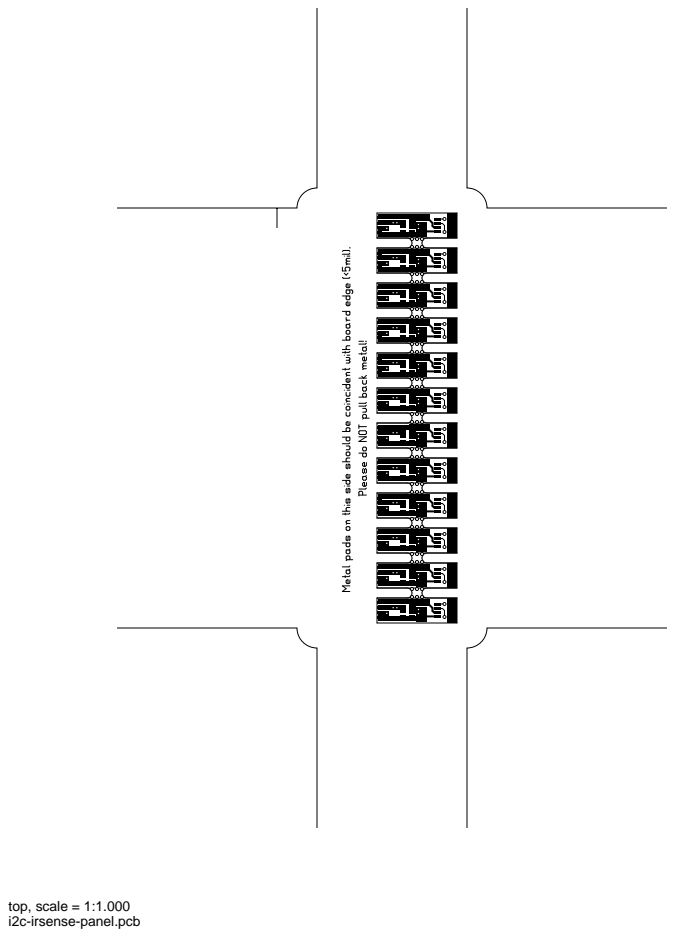
[picture p197: page 2]
top, scale = 1:1.000

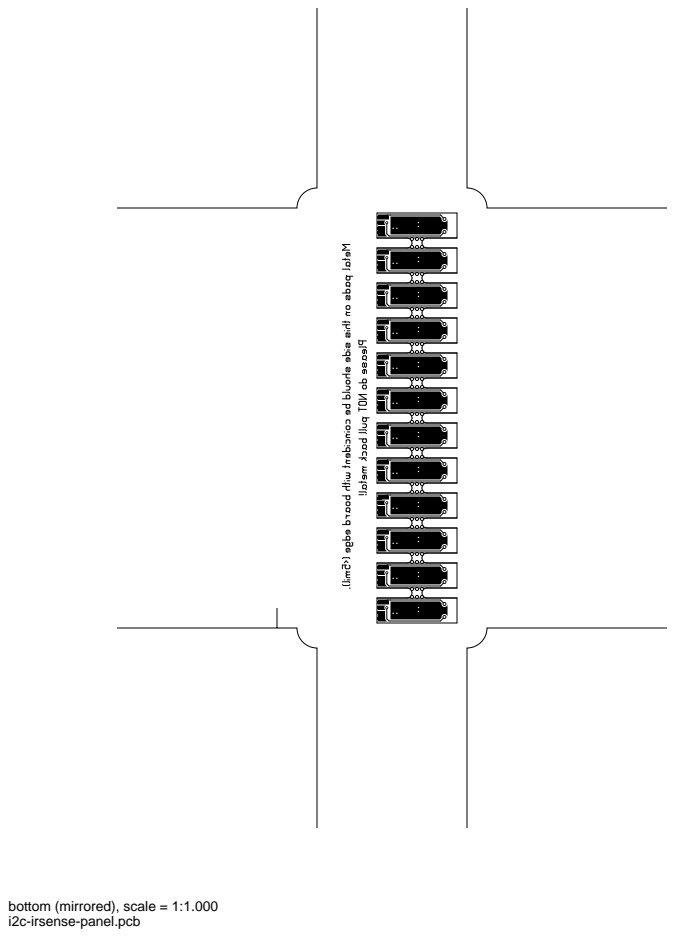
[picture p198: page 3]

bottom (mirrored), scale = 1:1.000

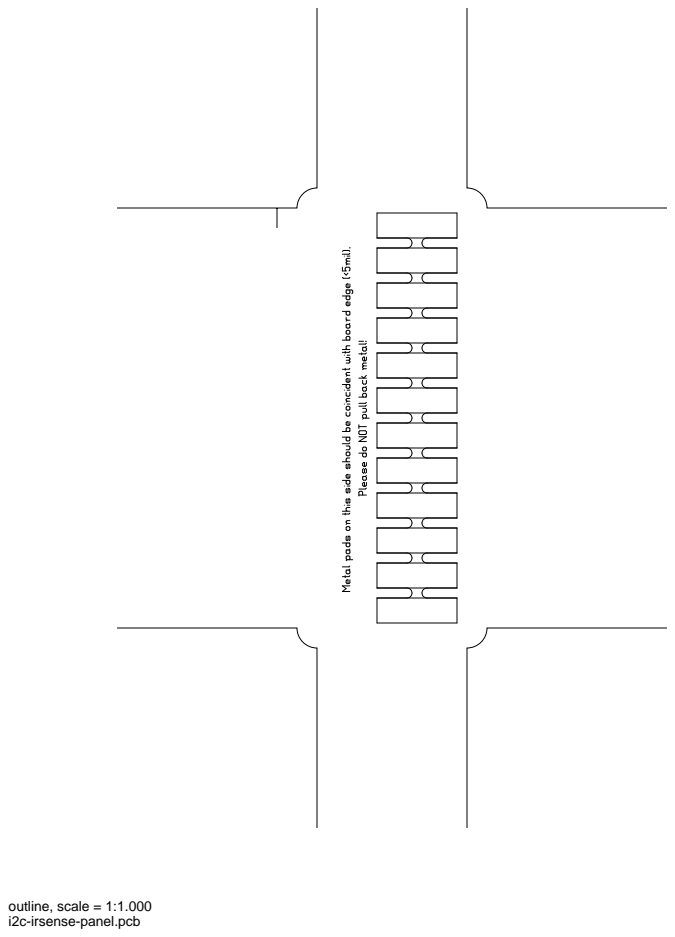
[picture p199: page 4]
outline, scale = 1:1.000

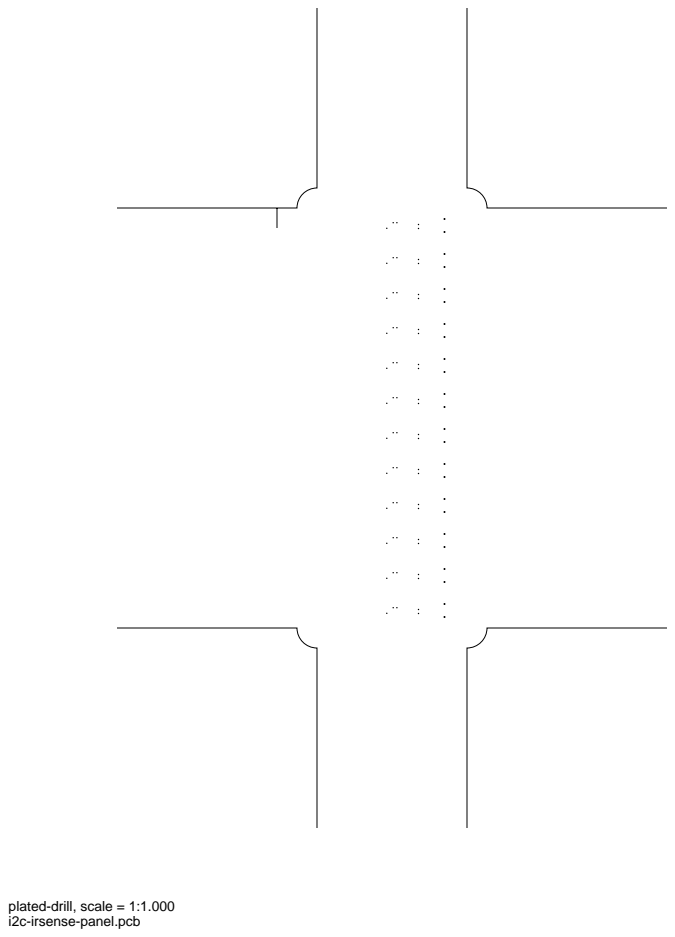
[picture p200: page 5]

plated-drill, scale = 1:1.000

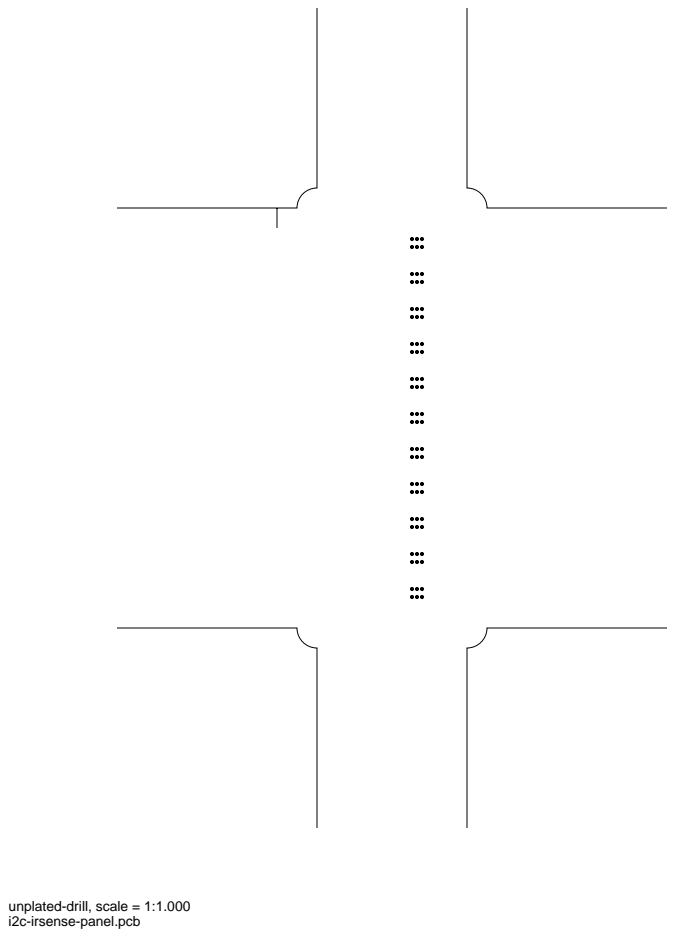
[picture p201: page 6]

unplated-drill, scale = 1:1.000

topmask, scale = 1:1.000 bottommask (mirrored), scale = 1:1.000

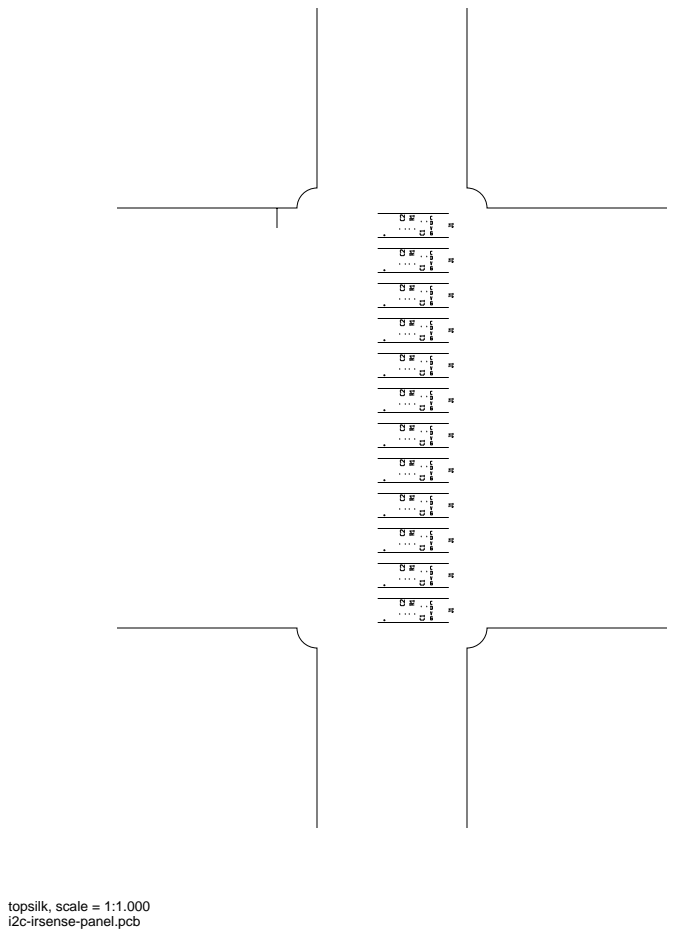
[picture p202: page 9]
topsilk, scale = 1:1.000

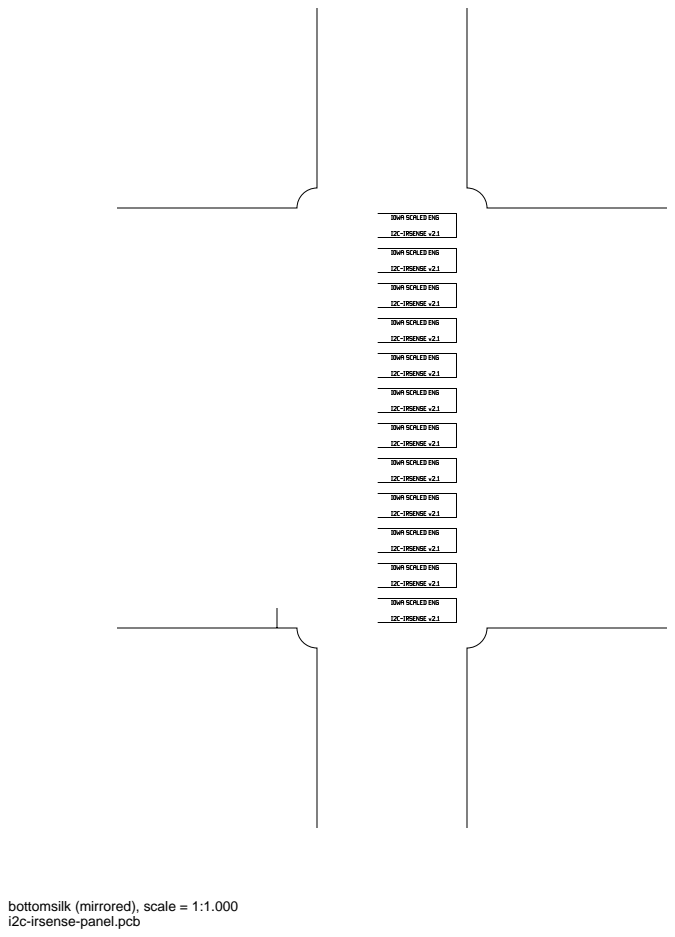
[picture p203: page 10]

bottomsilk (mirrored), scale = 1:1.000

toppaste, scale = 1:1.000

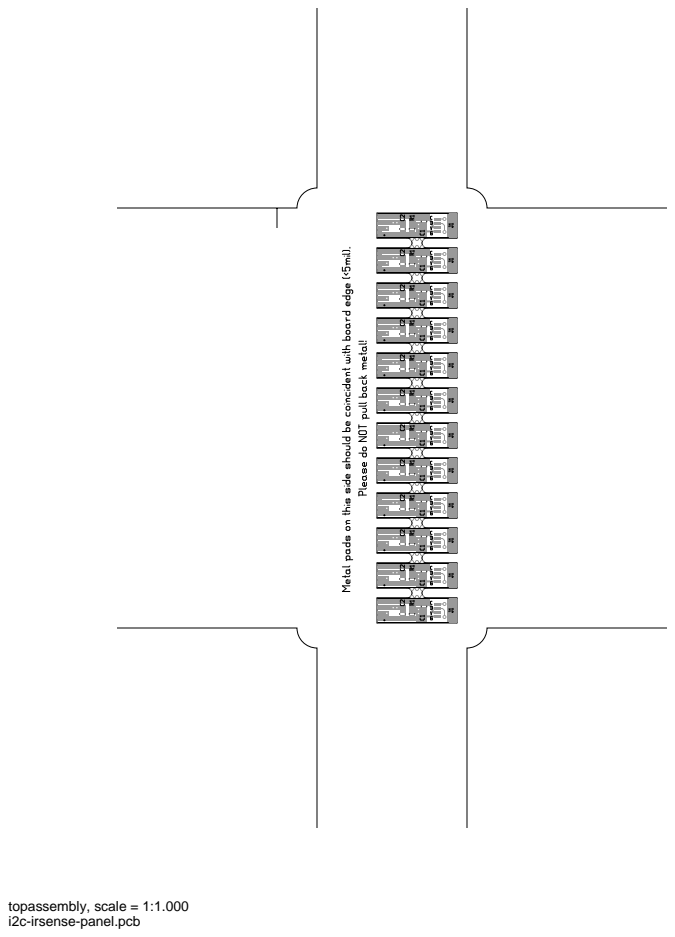
[picture p204: page 12]
topassembly, scale = 1:1.000

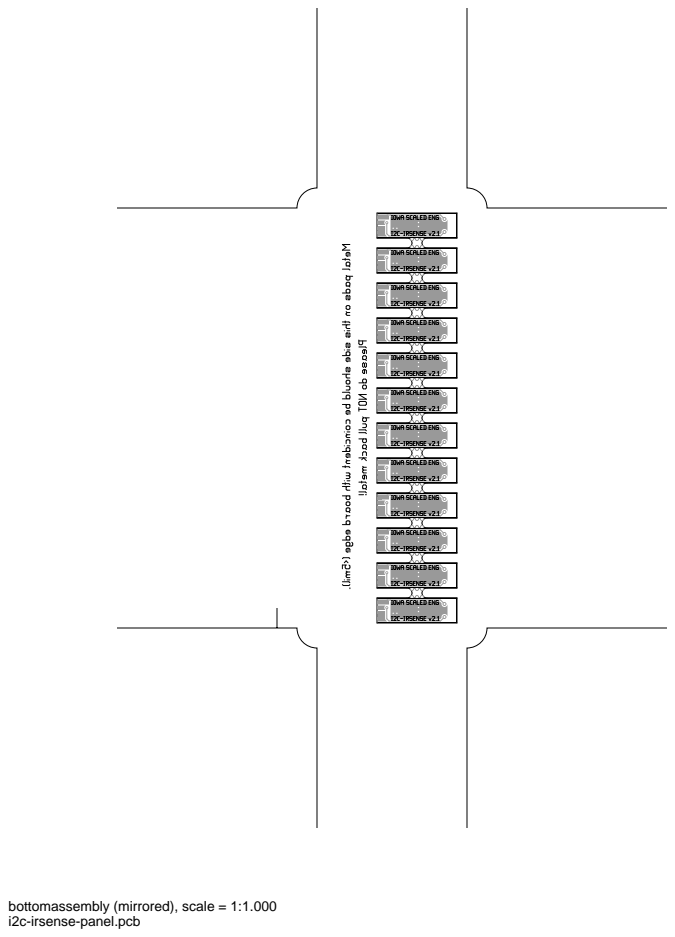
[picture p205: page 13]

bottomassembly (mirrored), scale = 1:1.000

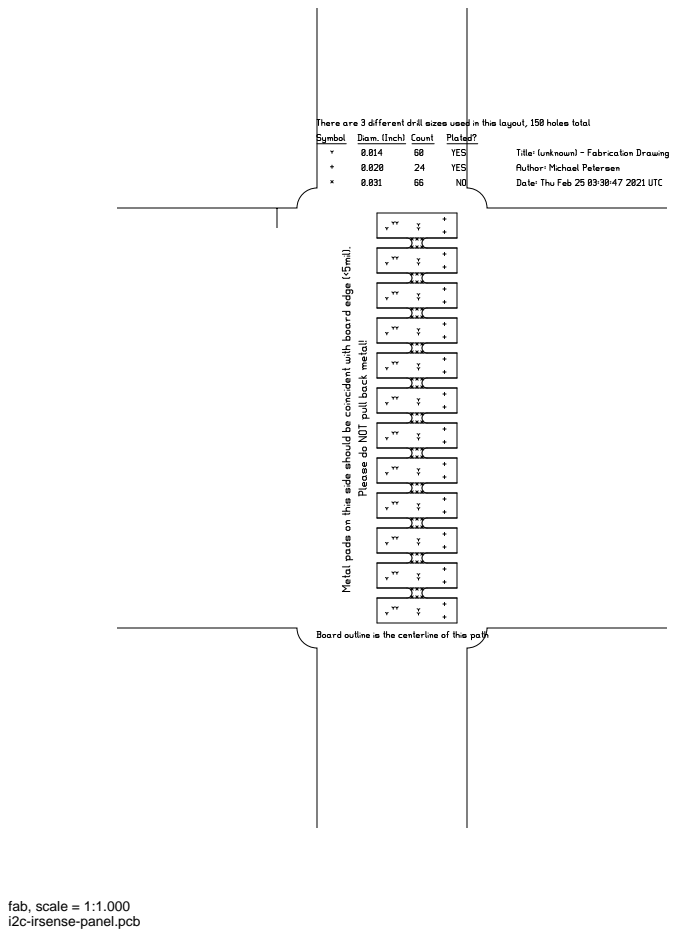
[picture p206: page 14]
fab, scale = 1:1.000
