IowaScaledEngineering/ckt-irsense/pg/ckt-irsense-panel-v4.1x-e690acc/ckt-irsense-panel-pcb.pdf

# ckt-irsense-panel.pcb

# 1. Table of Contents (This Page) Created on Wed Dec 16 20:42:43 2020

# 2. top 3. bottom 4. outline 5. plated-drill 6. unplated-drill 7. componentmask 8. soldermask 9. topsilk 10. bottomsilk 11. toppaste 12. bottompaste 13. topassembly 14. bottomassembly 15. fab

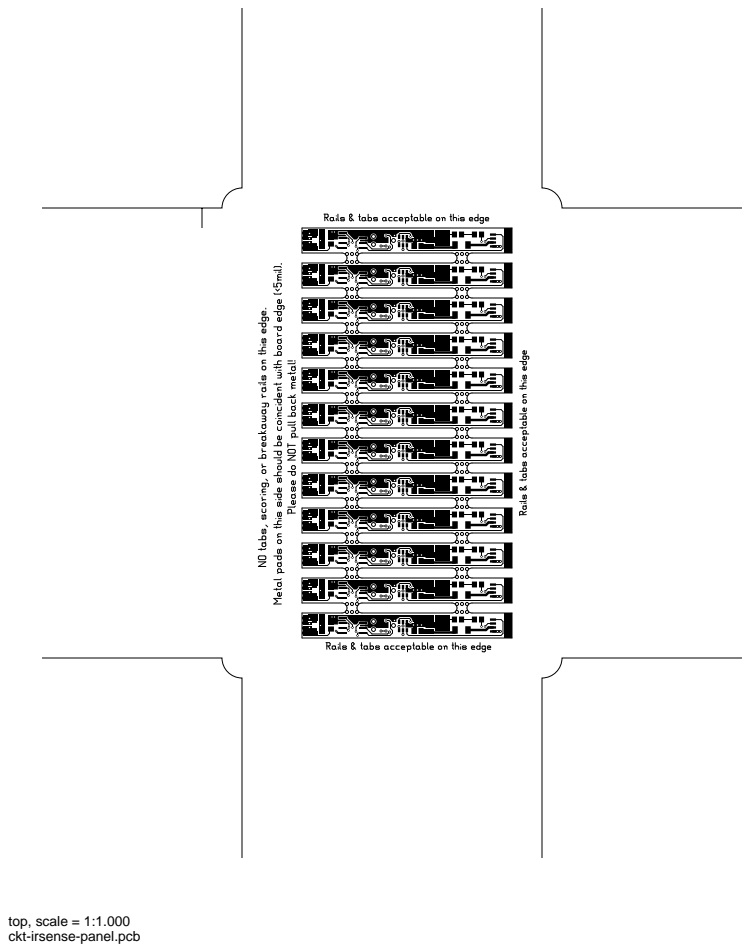
[picture p207: page 2]
top, scale = 1:1.000

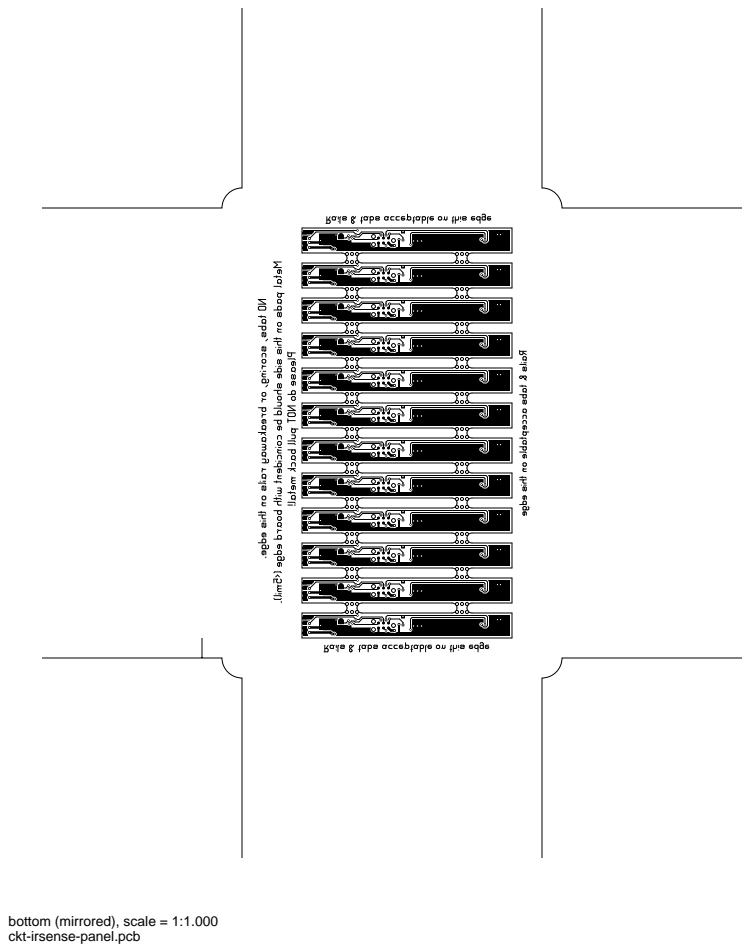
[picture p208: page 3]

bottom (mirrored), scale = 1:1.000

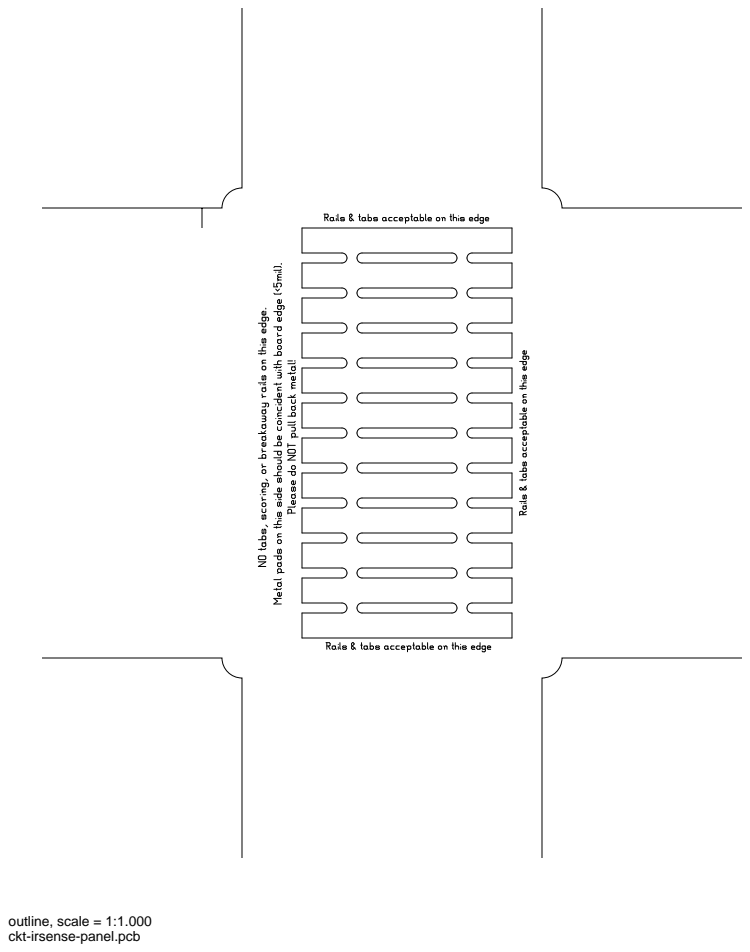
[picture p209: page 4]
outline, scale = 1:1.000

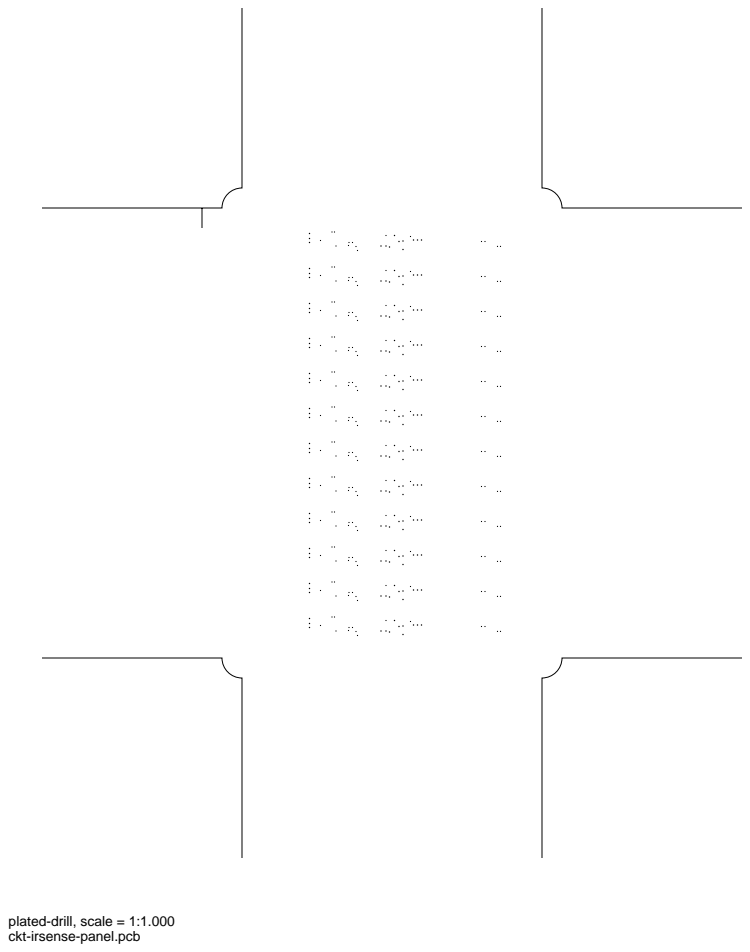
[picture p210: page 5]

plated-drill, scale = 1:1.000

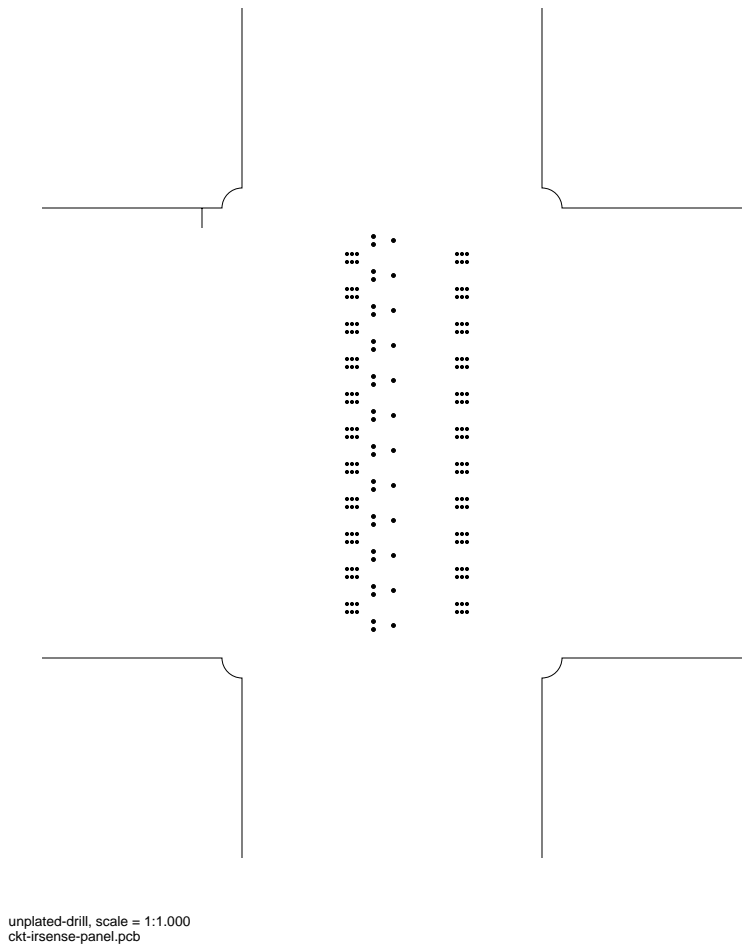
[picture p211: page 6]

unplated-drill, scale = 1:1.000

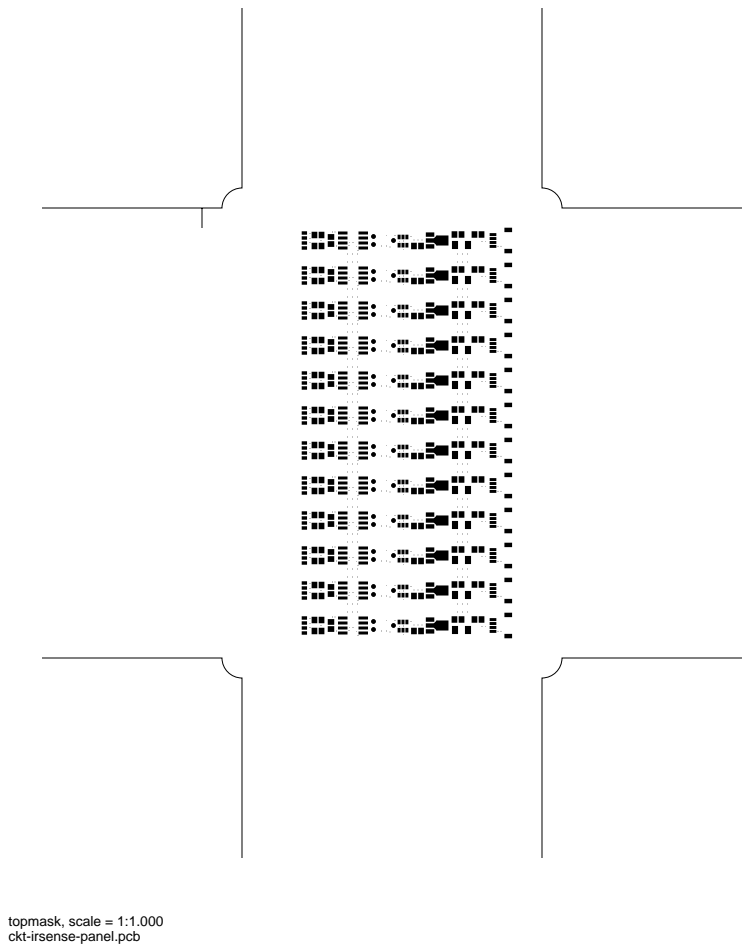
[picture p212: page 7]
topmask, scale = 1:1.000

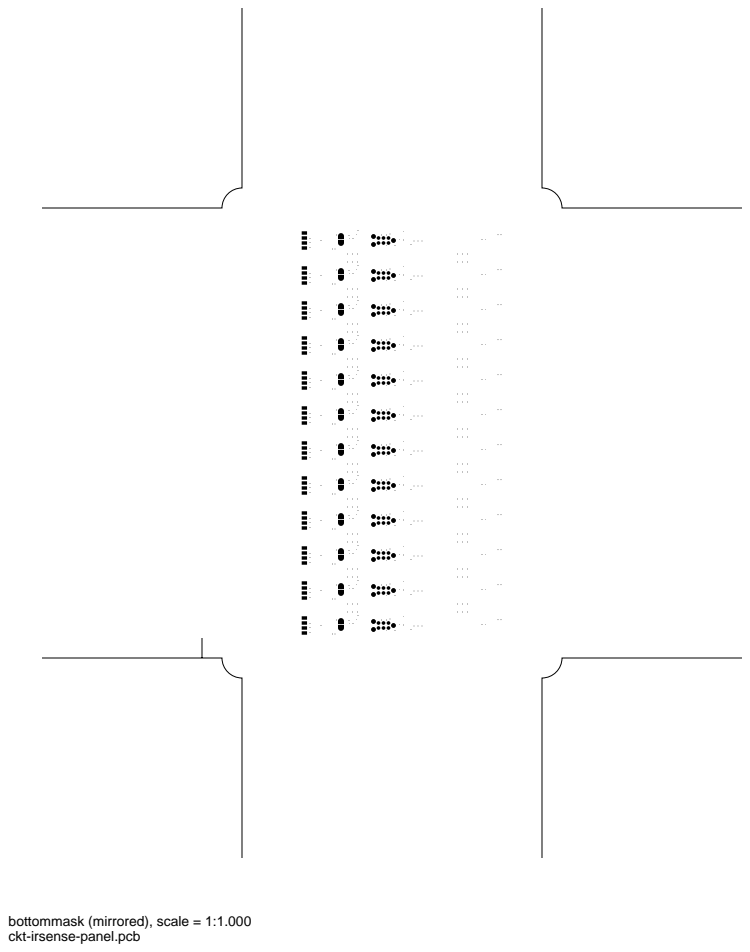
[picture p213: page 8]

bottommask (mirrored), scale = 1:1.000

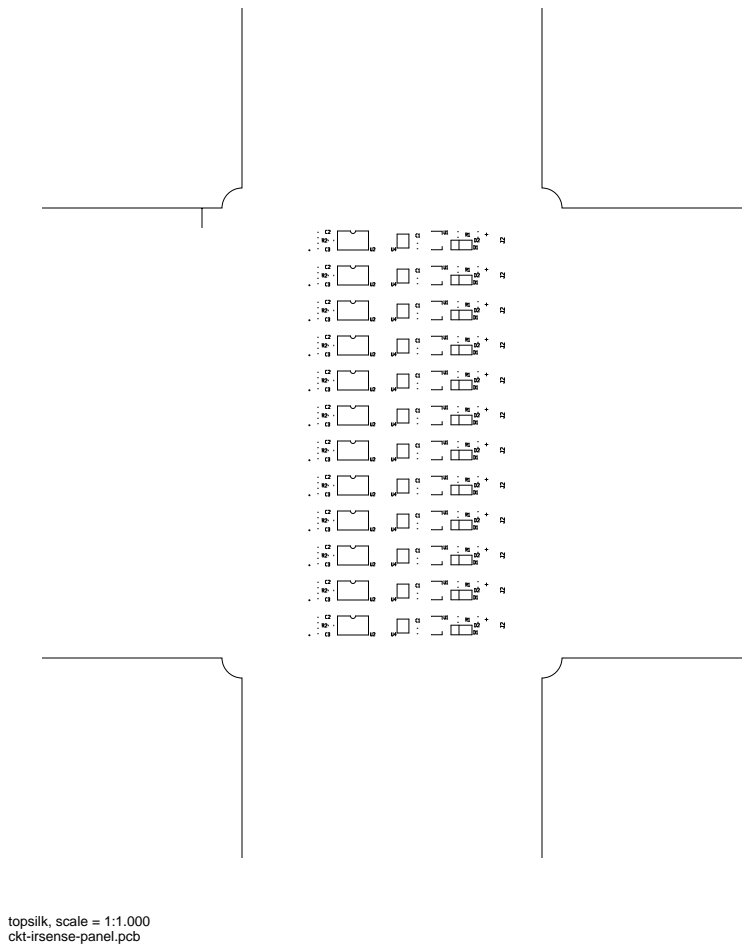
[picture p214: page 9]
topsilk, scale = 1:1.000

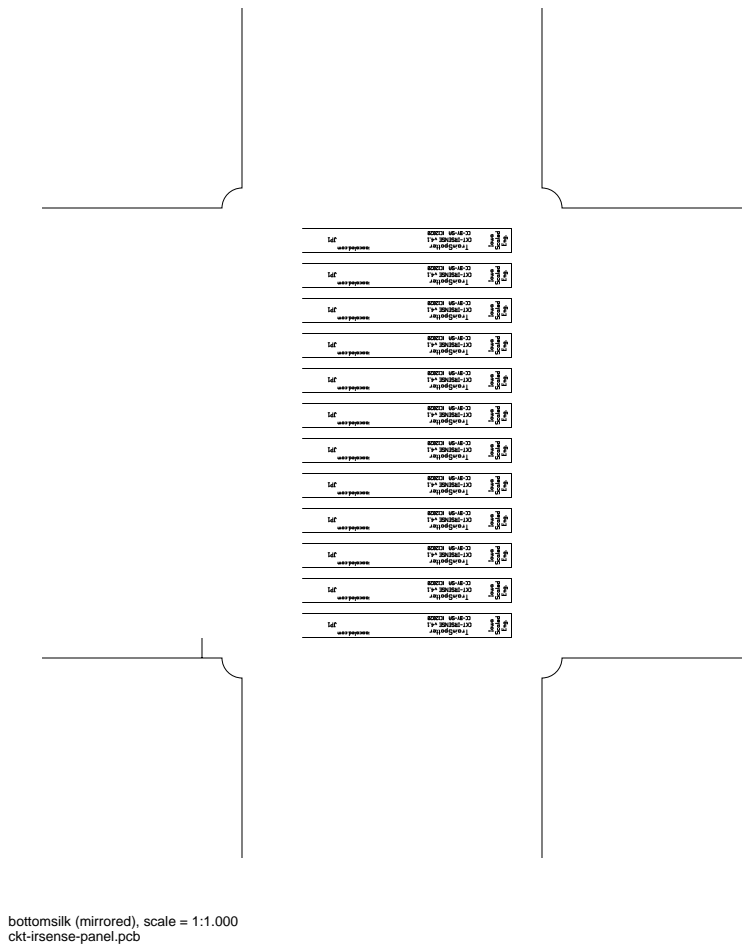
[picture p215: page 10]

bottomsilk (mirrored), scale = 1:1.000

toppaste, scale = 1:1.000 bottompaste (mirrored), scale = 1:1.000

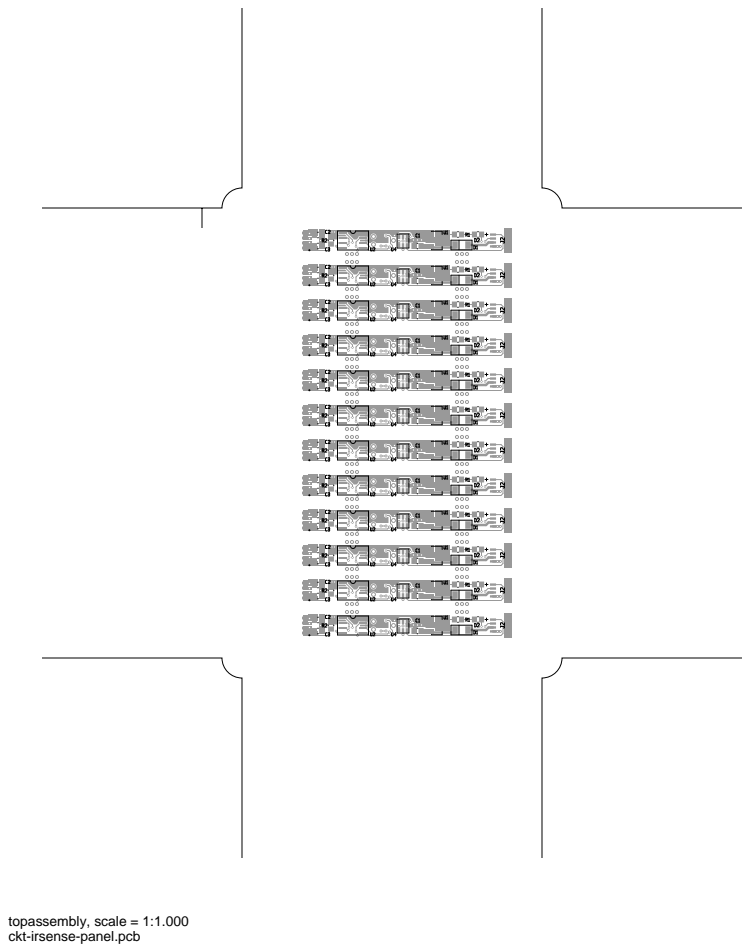
[picture p216: page 13]
topassembly, scale = 1:1.000

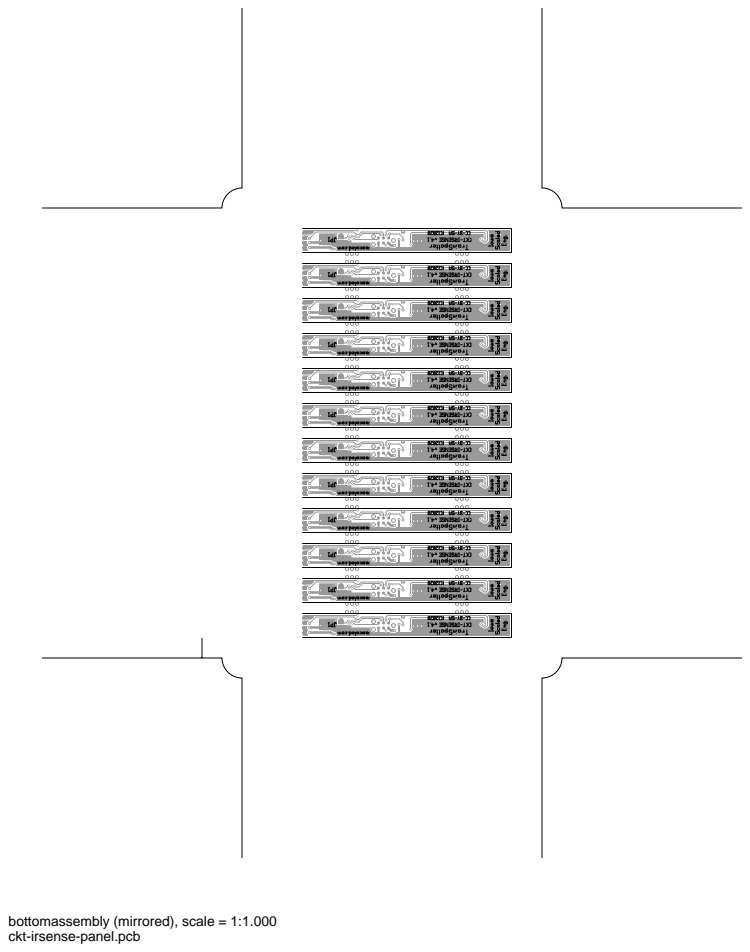
[picture p217: page 14]

bottomassembly (mirrored), scale = 1:1.000

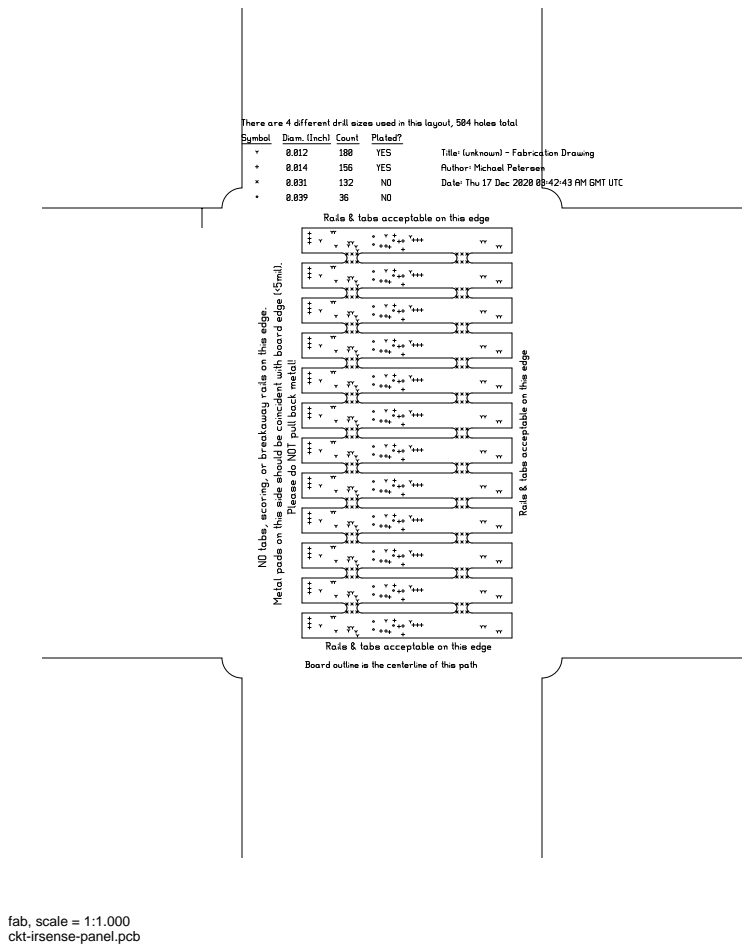
[picture p218: page 15]
fab, scale = 1:1.000
