IowaScaledEngineering/ckt-irsense/pg/ckt-irsense-base-v2.0-ae505da/ckt-irsense-base-pcb.pdf

# ckt-irsense-base.pcb

# 1. Table of Contents (This Page) Created on Wed Oct 14 17:18:56 2020

# 2. top 3. bottom 4. outline 5. plated-drill 6. unplated-drill 7. componentmask 8. soldermask 9. topsilk 10. bottomsilk 11. toppaste 12. topassembly 13. bottomassembly 14. fab

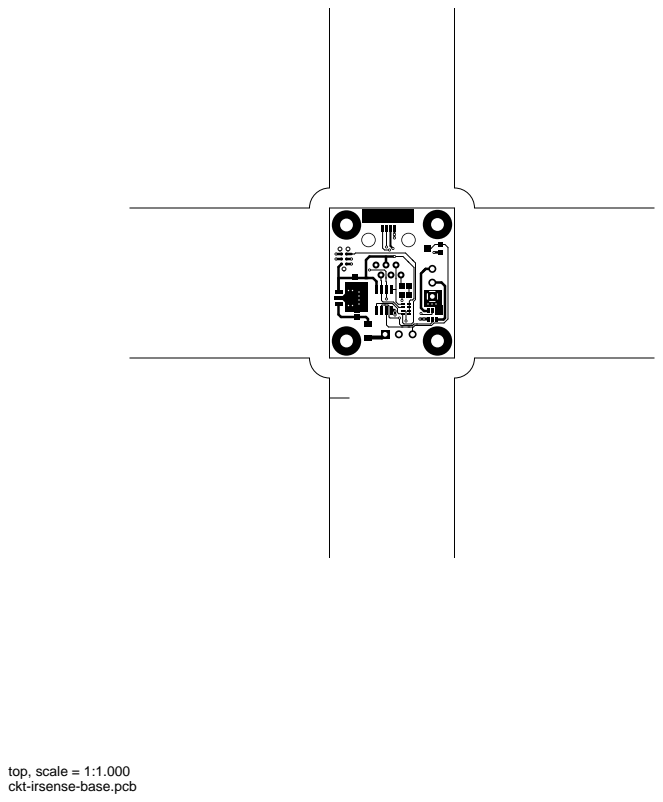
[picture p219: page 2]
top, scale = 1:1.000

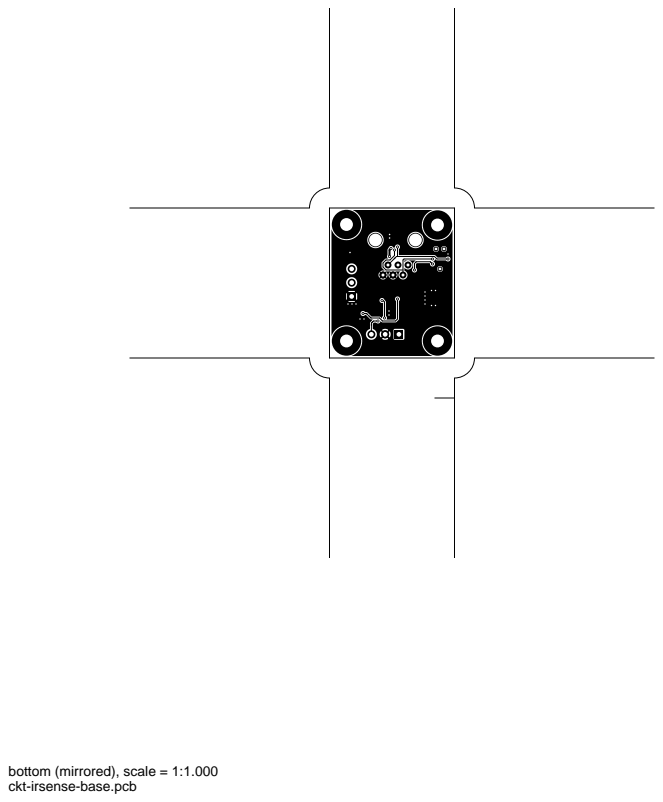
[picture p220: page 3]

bottom (mirrored), scale = 1:1.000

outline, scale = 1:1.000

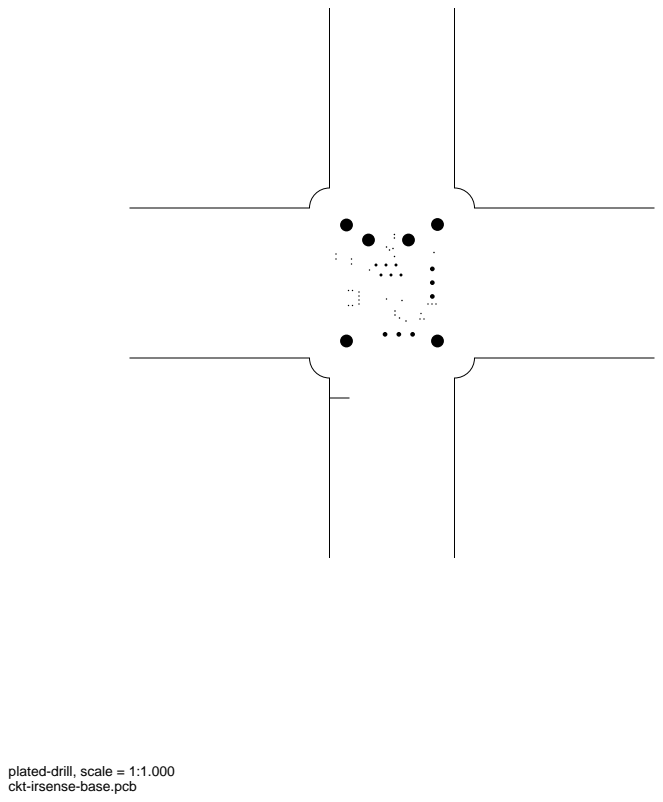
[picture p221: page 5]

plated-drill, scale = 1:1.000

unplated-drill, scale = 1:1.000

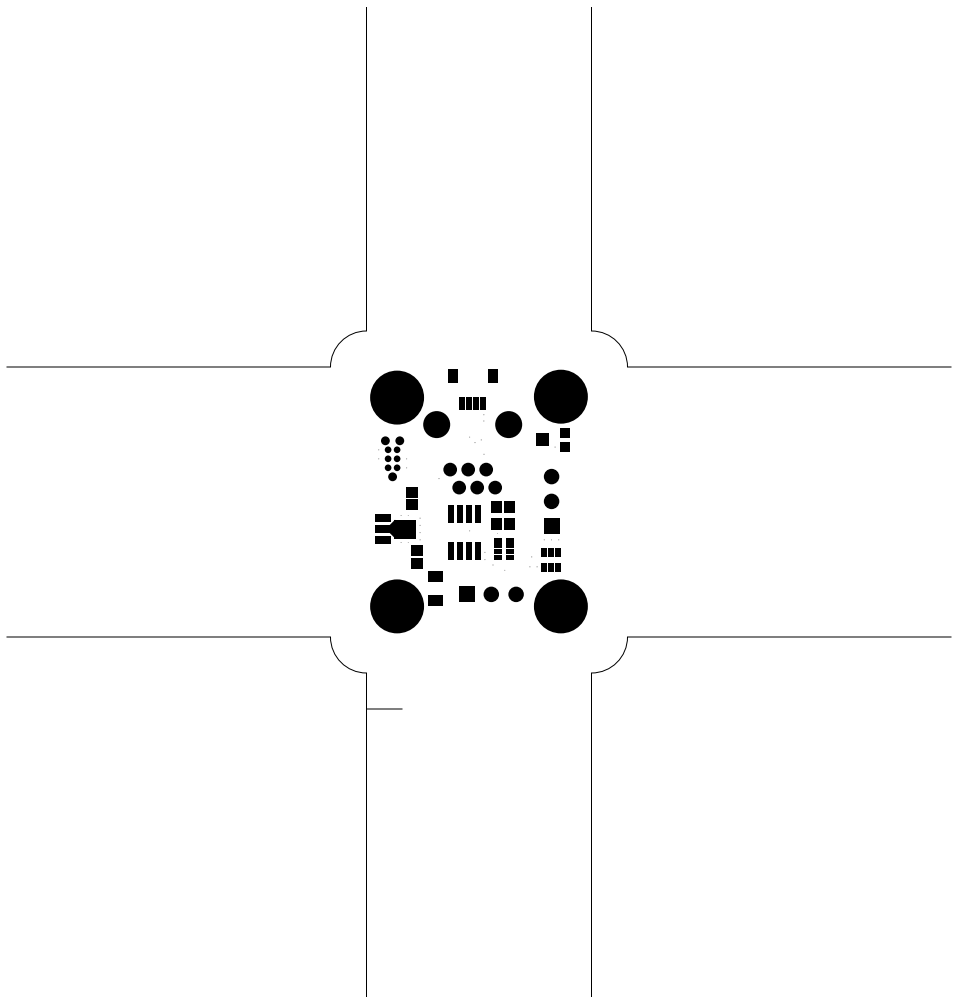
[picture p222: figure]

topmask, scale = 1:1.000

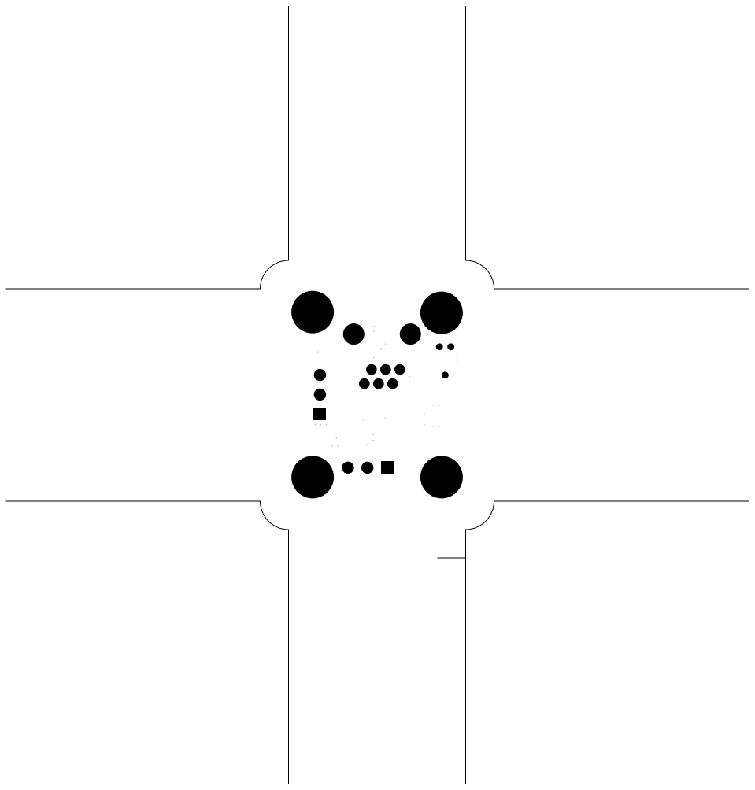
[picture p223: figure]

bottommask (mirrored), scale = 1:1.000

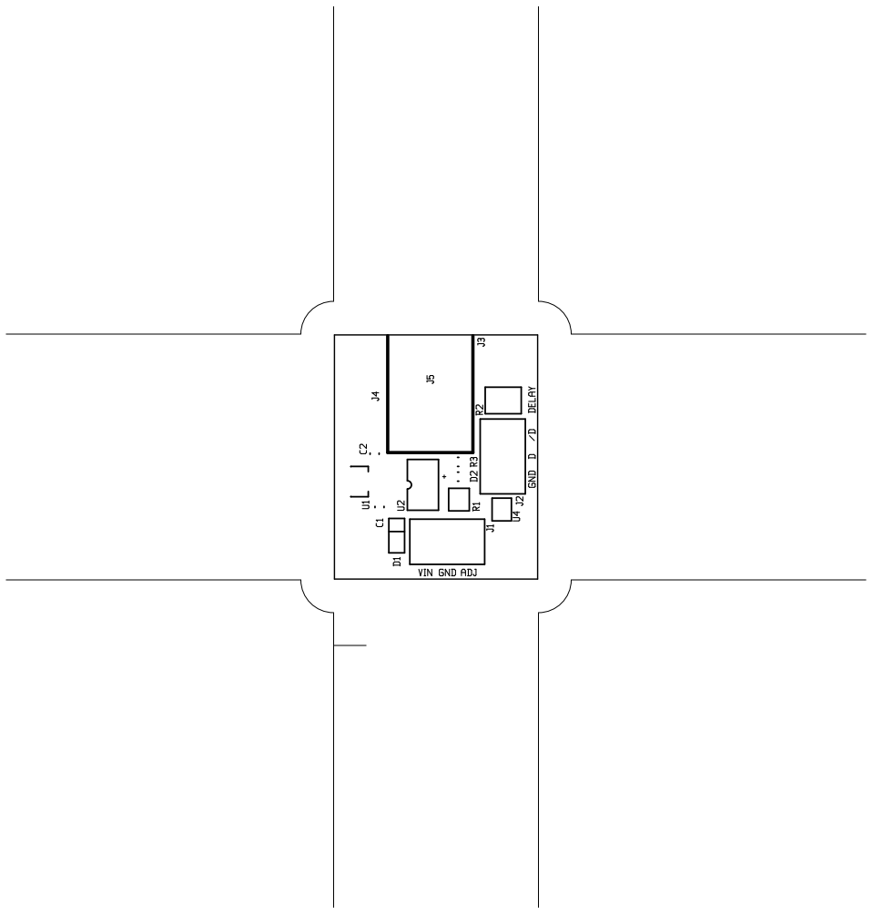
[picture p224: figure]

topsilk, scale = 1:1.000

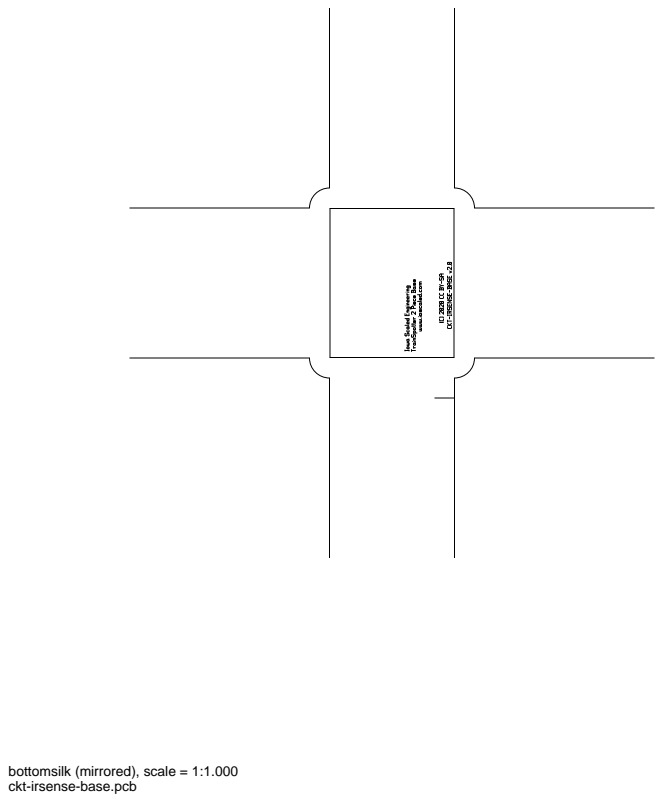
[picture p225: page 10]

bottomsilk (mirrored), scale = 1:1.000

toppaste, scale = 1:1.000

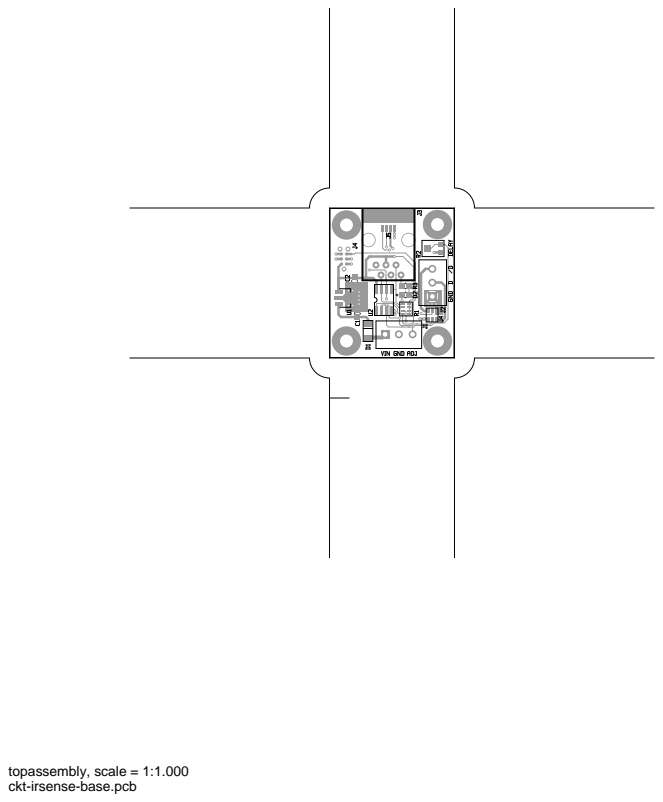
[picture p226: page 12]
topassembly, scale = 1:1.000

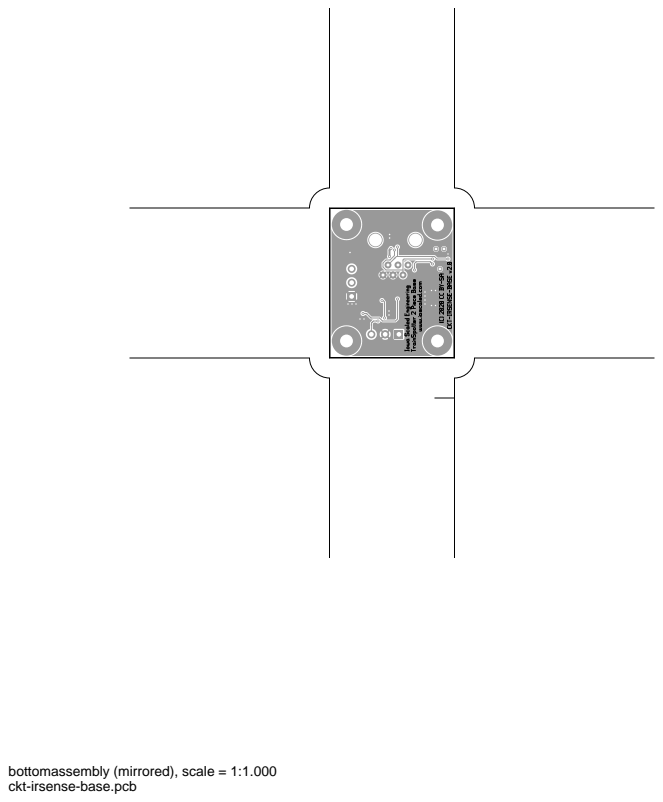
[picture p227: page 13]

bottomassembly (mirrored), scale = 1:1.000

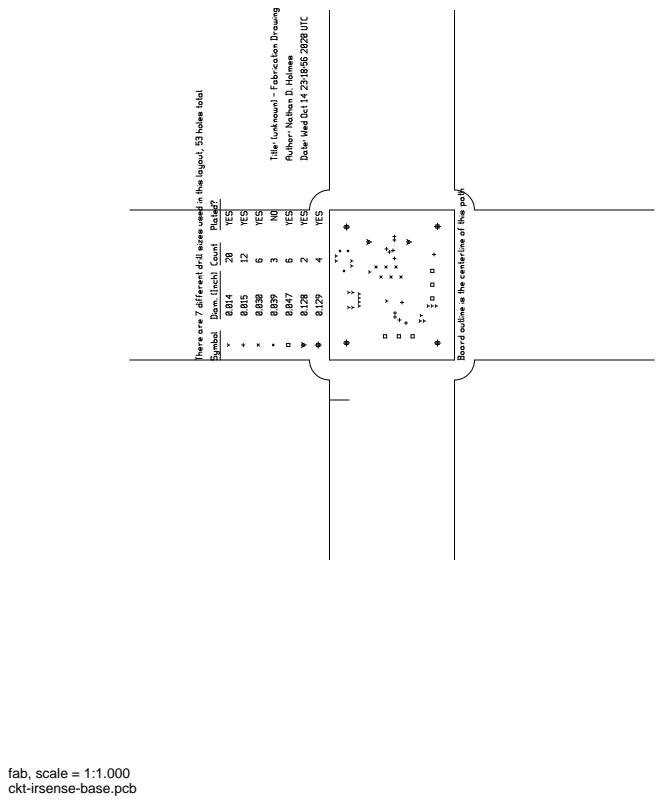
[picture p228: page 14]
fab, scale = 1:1.000
