IowaScaledEngineering/ckt-irsense/pg/ckt-irsense-base-v2.0-ae505da/ckt-irsense-base.pdf

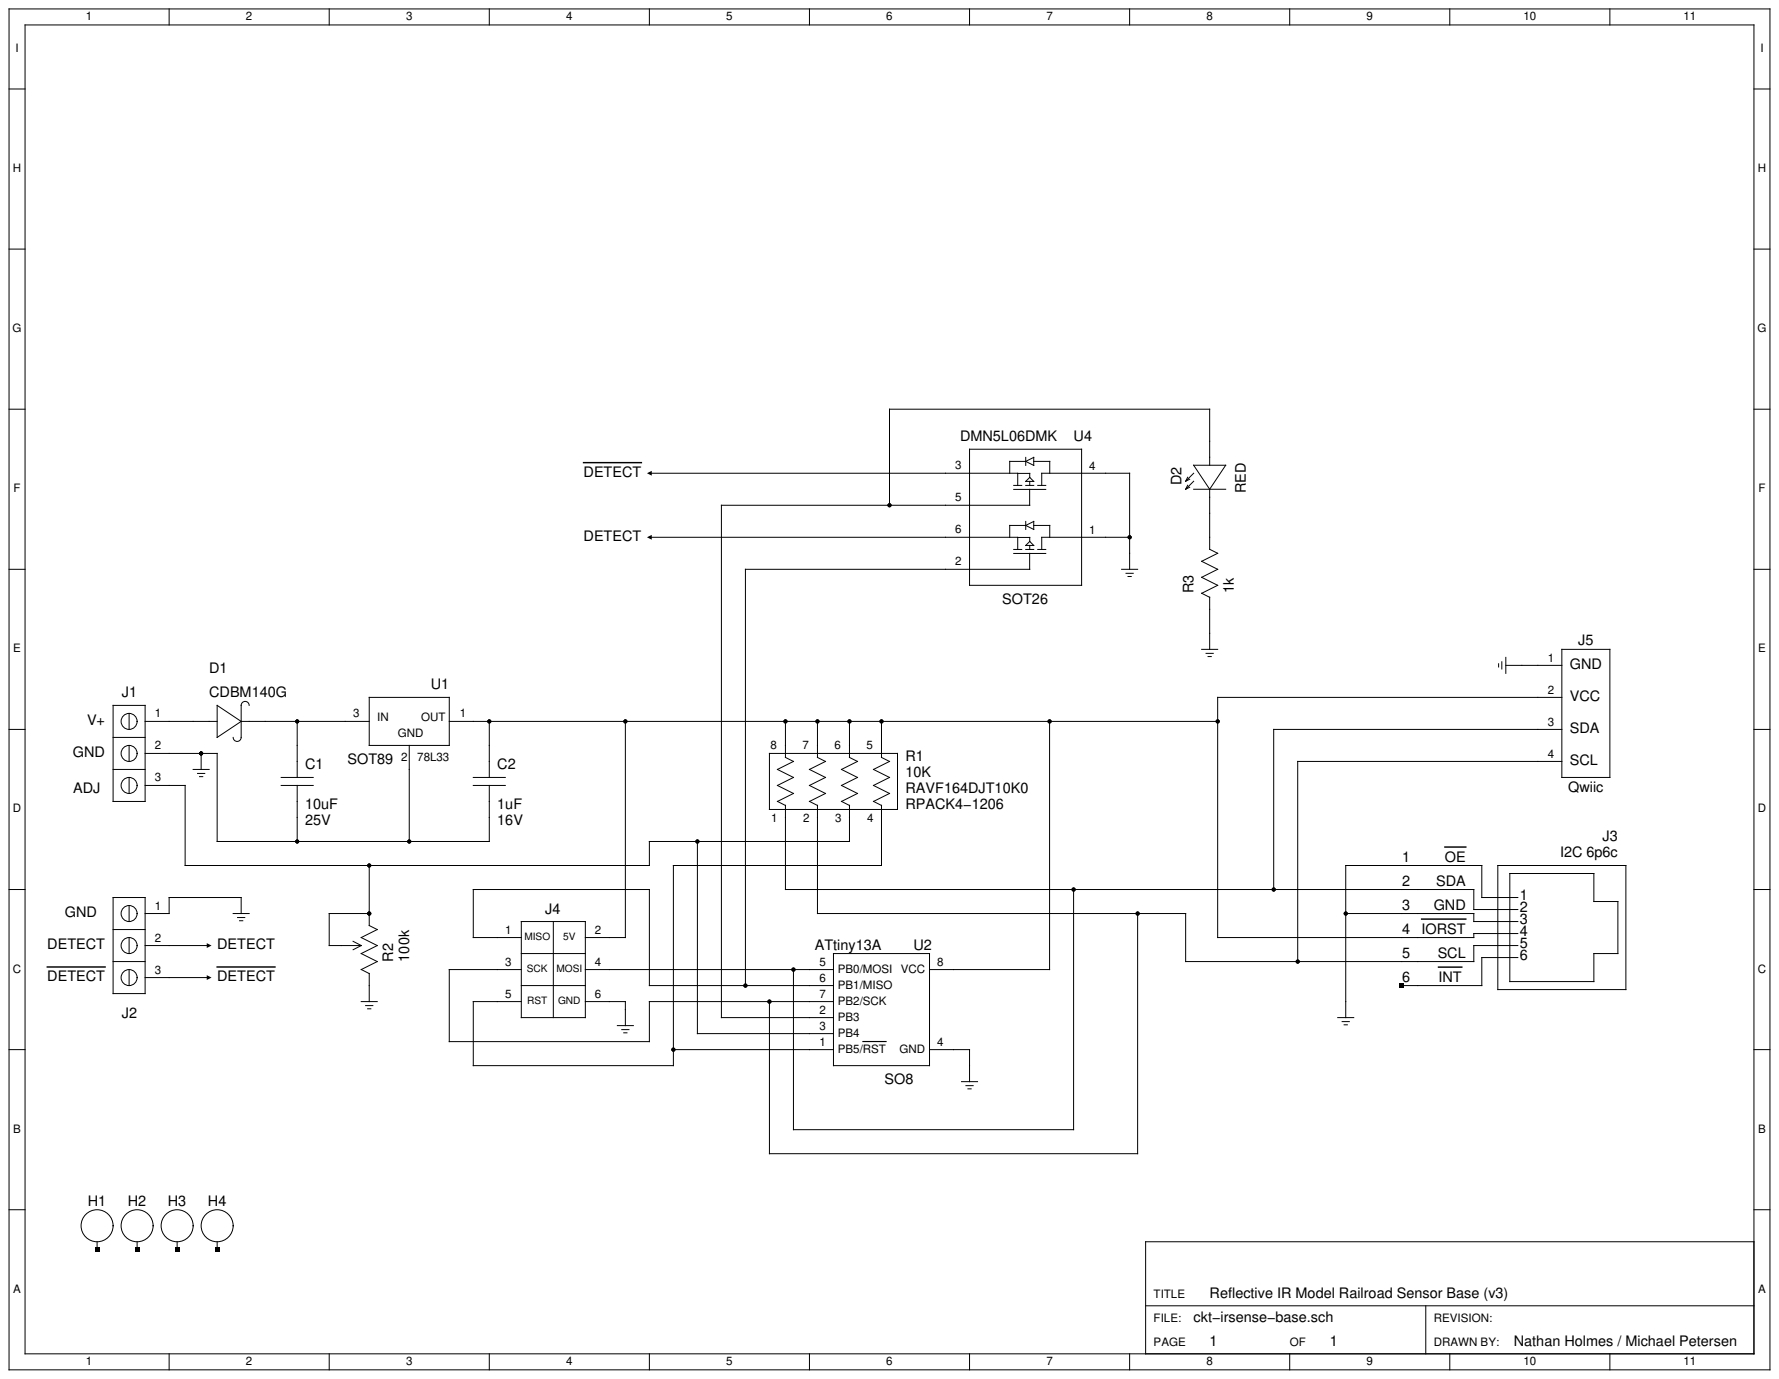
[picture p229: page 1]

Reflective IR Model Railroad Sensor Base (v3)
ckt−irsense−base.sch
