IowaScaledEngineering/ckt-irsense/pg/ckt-irsense-panel-v4.0-96c70f0/ckt-irsense.pdf

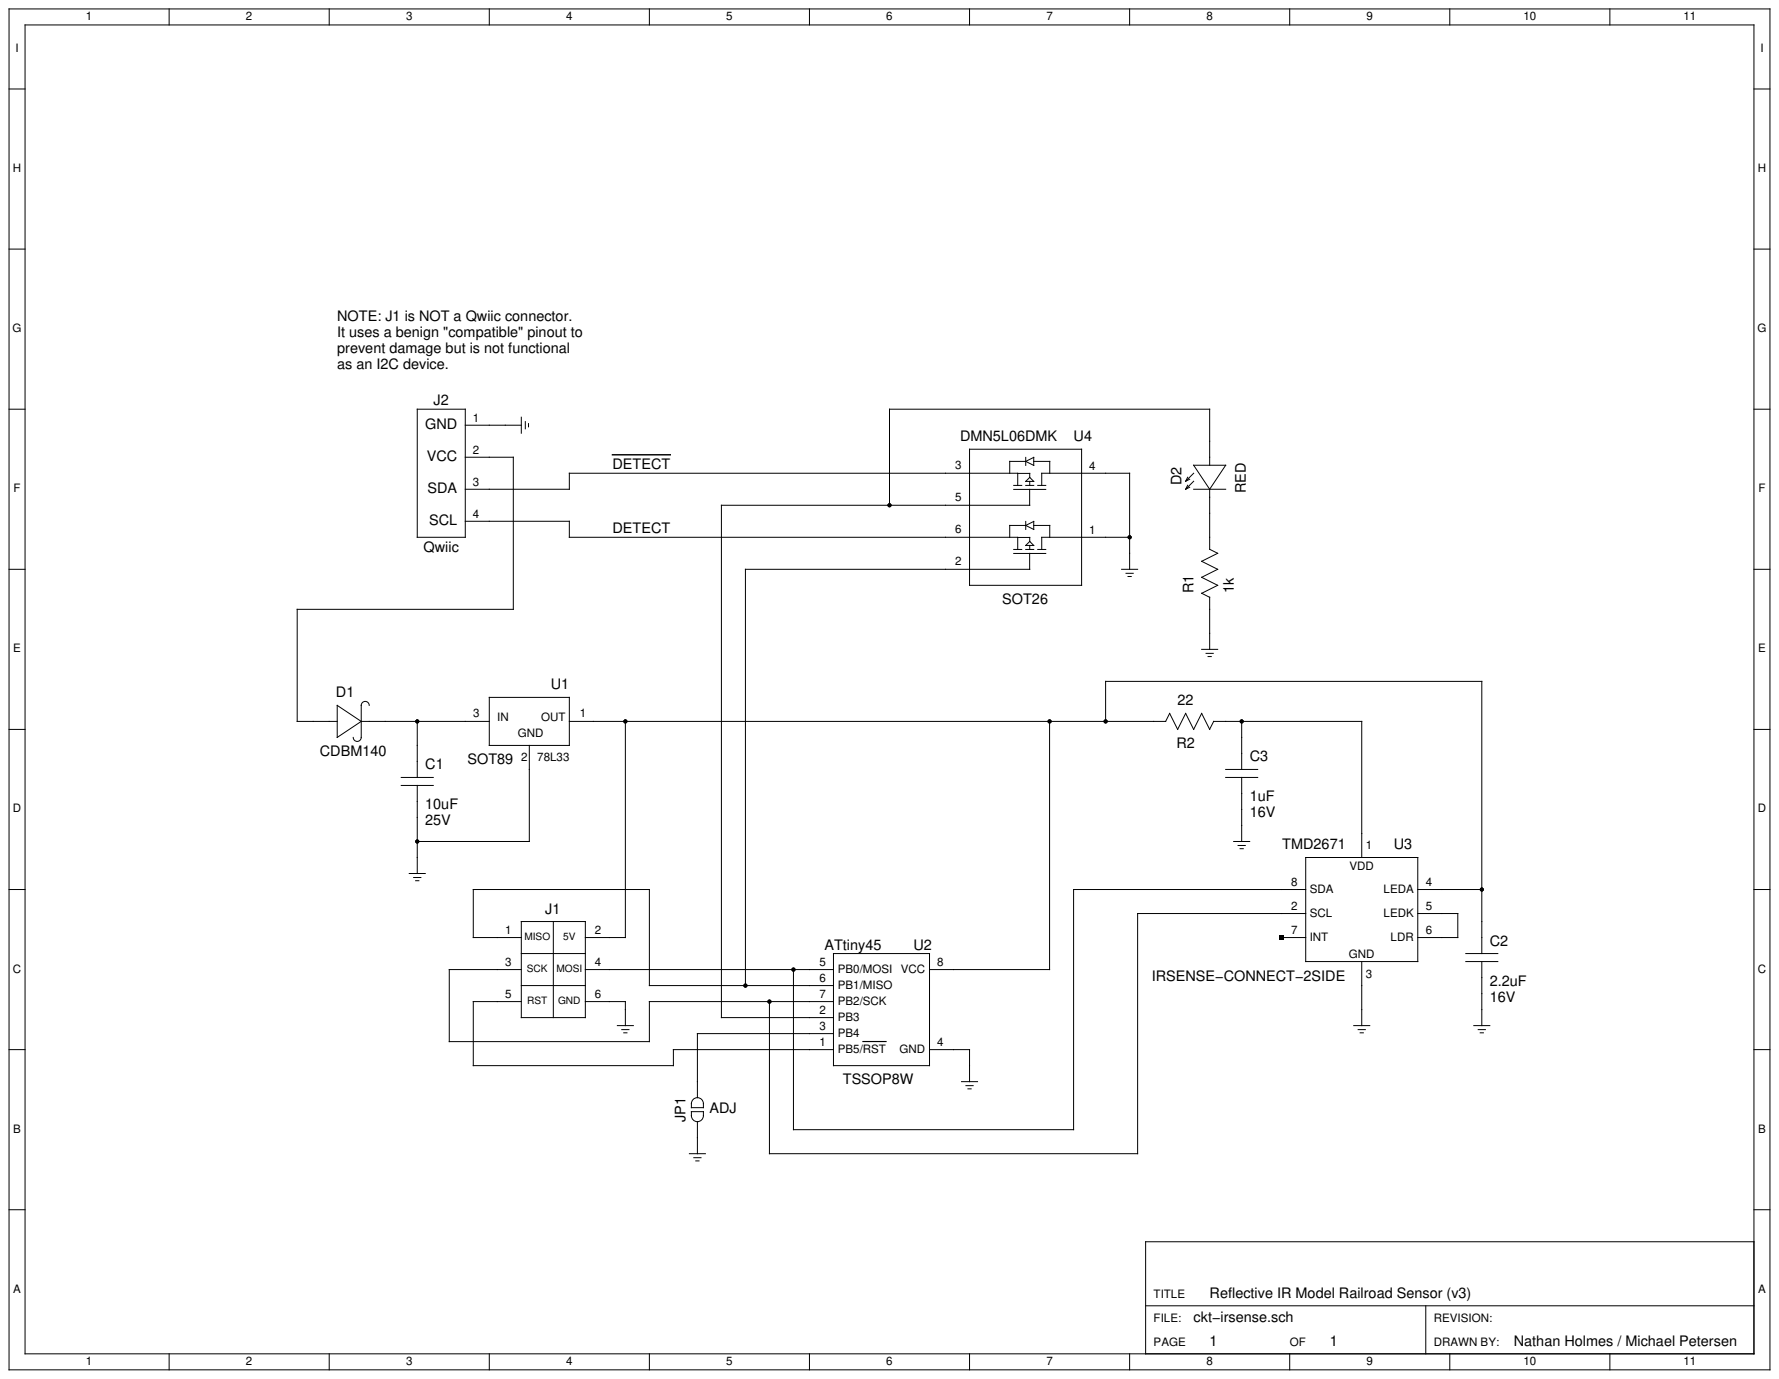
[picture p230: page 1]

NOTE: J1 is NOT a Qwiic connector.
It uses a benign "compatible" pinout to
prevent damage but is not functional
as an I2C device.

Reflective IR Model Railroad Sensor (v3)
ckt−irsense.sch
