IowaScaledEngineering/ckt-irsense/pg/ckt-irsense-ra-panel-v4.1-9db1f3e/ckt-irsense-ra-panel-pcb.pdf

# ckt-irsense-ra-panel.pcb

# 1. Table of Contents (This Page) Created on Wed Aug 19 20:40:31 2020

# 2. top 3. bottom 4. outline 5. plated-drill 6. unplated-drill 7. componentmask 8. soldermask 9. topsilk 10. bottomsilk 11. toppaste 12. bottompaste 13. topassembly 14. bottomassembly 15. fab

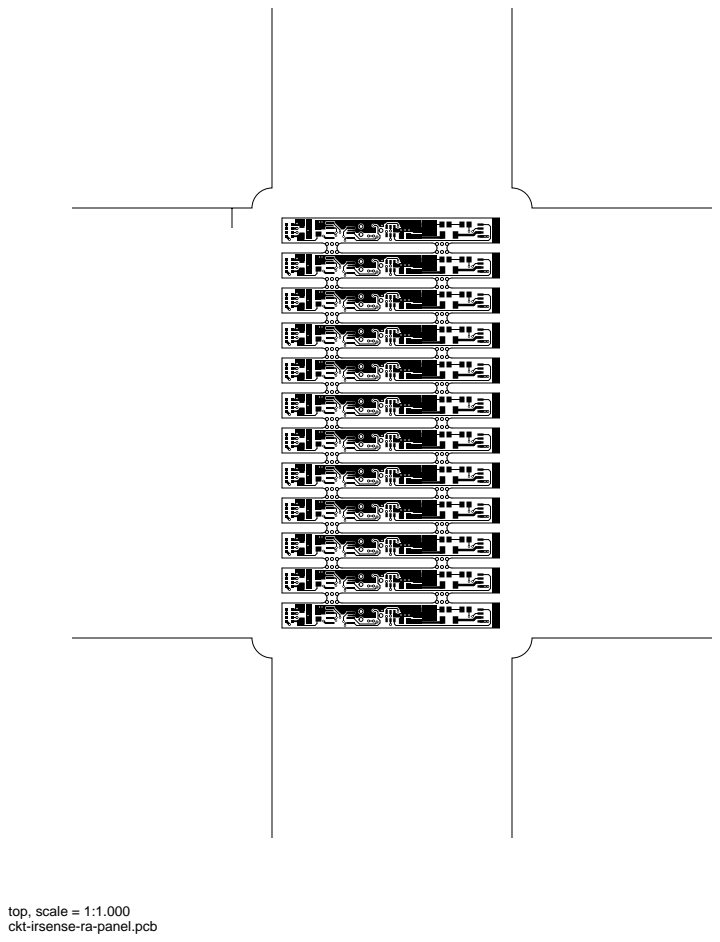
[picture p231: page 2]
top, scale = 1:1.000

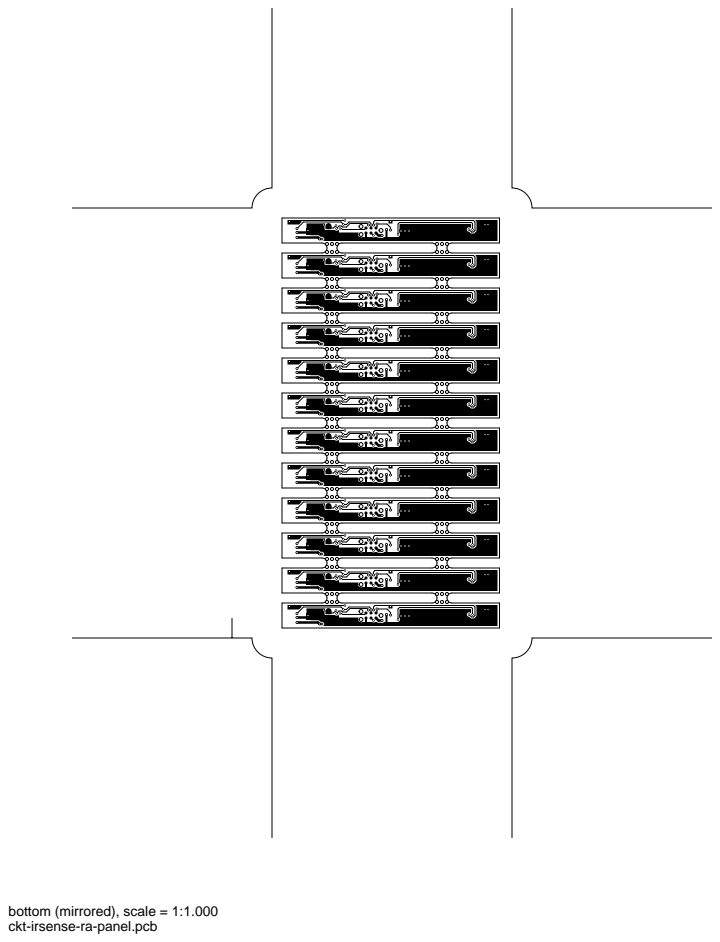
[picture p232: page 3]

bottom (mirrored), scale = 1:1.000

outline, scale = 1:1.000

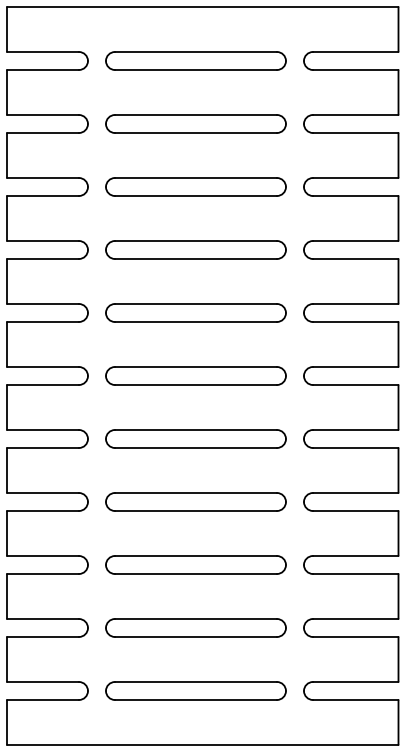
[picture p233: figure]
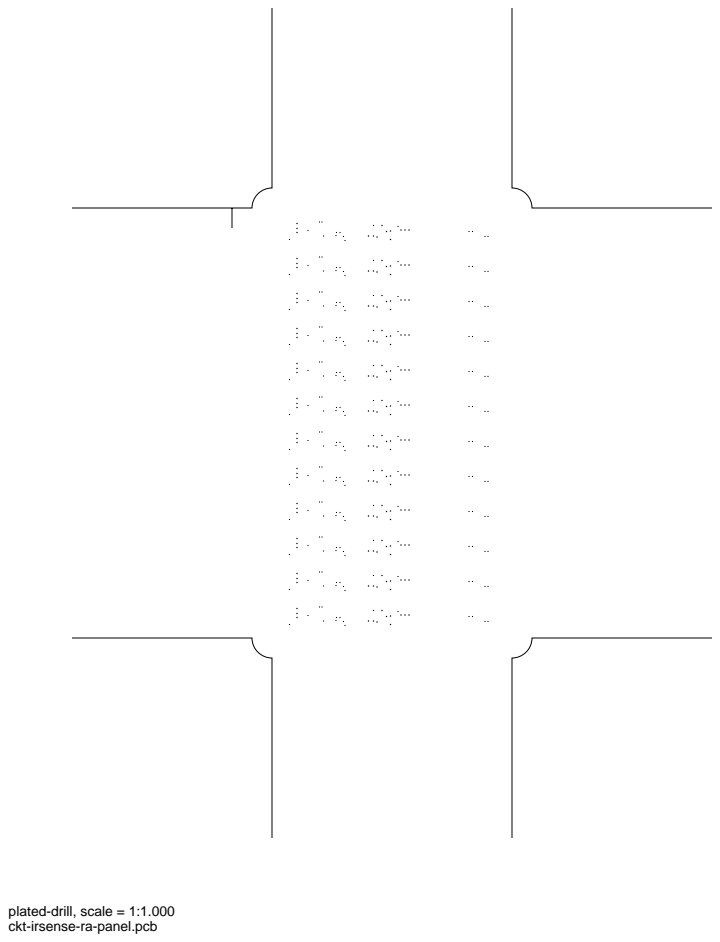
[picture p234: page 5]

plated-drill, scale = 1:1.000

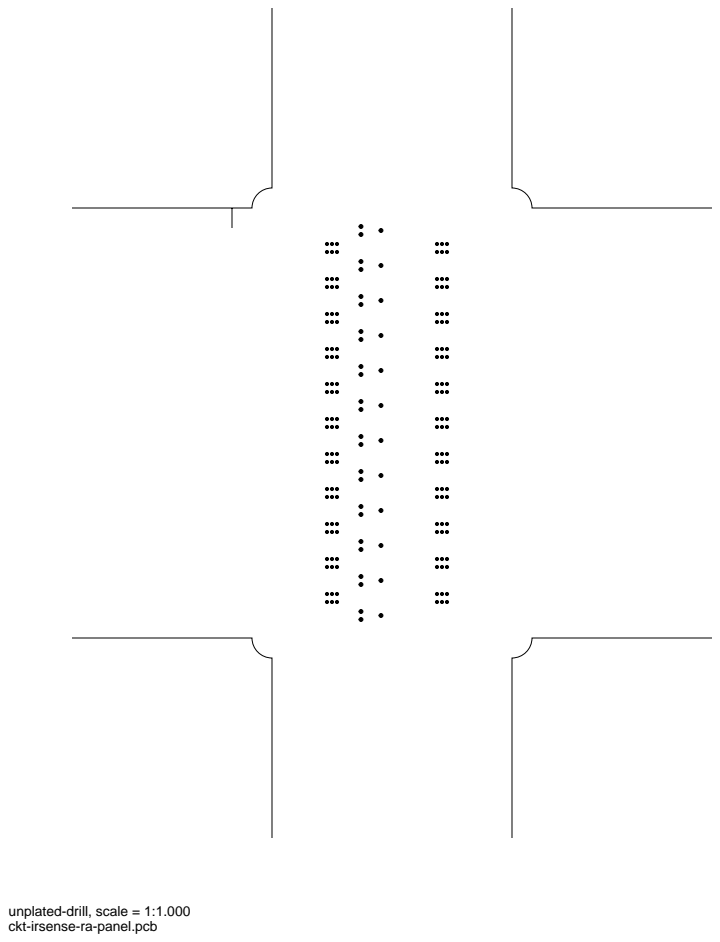
[picture p235: page 6]

unplated-drill, scale = 1:1.000

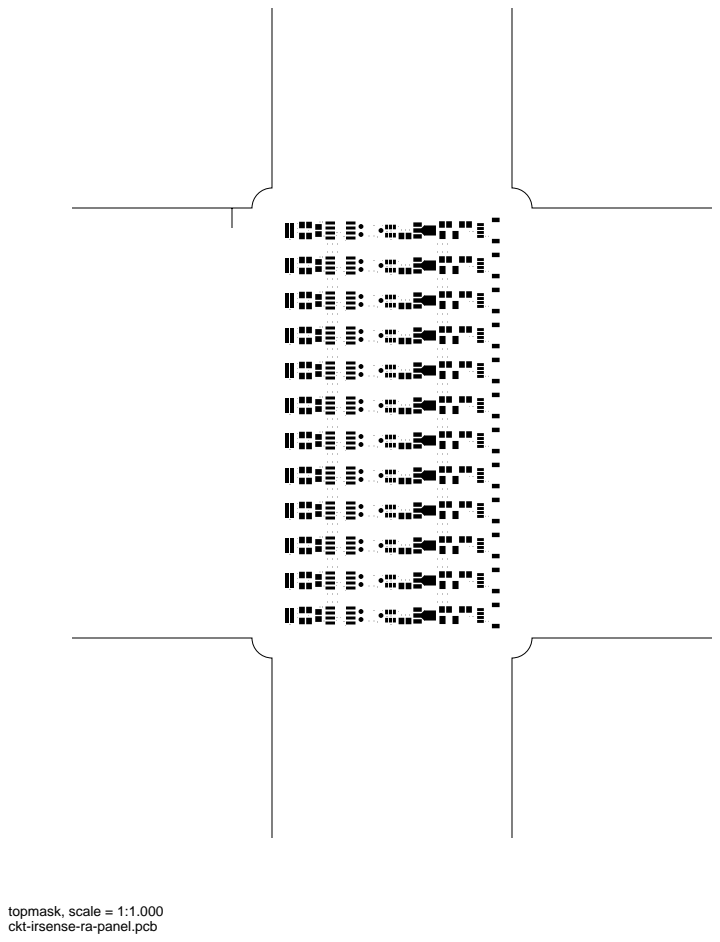
[picture p236: page 7]
topmask, scale = 1:1.000

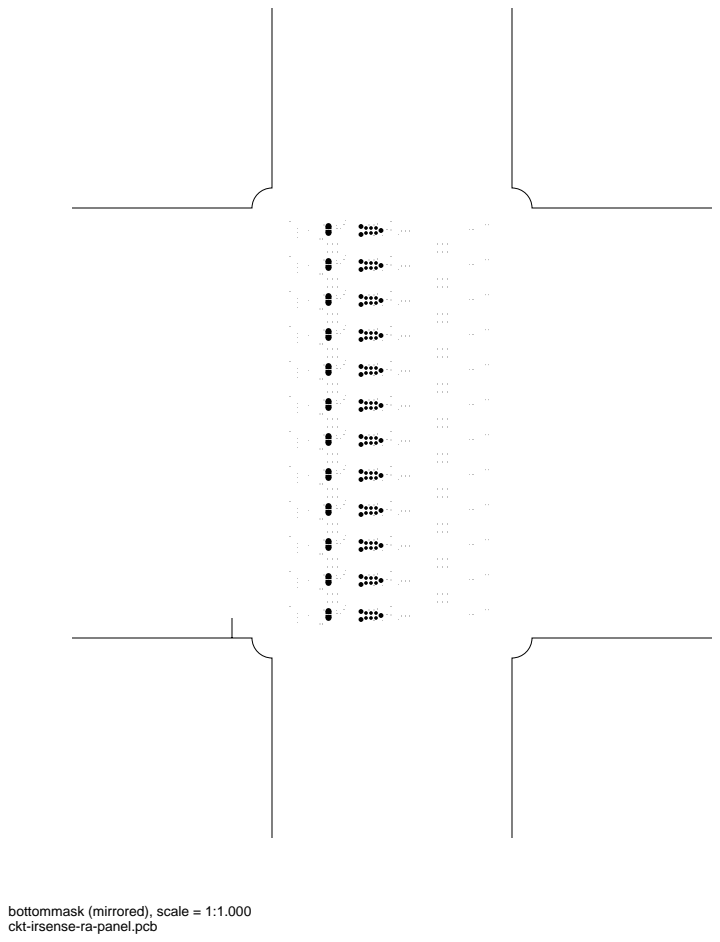
[picture p237: page 8]

bottommask (mirrored), scale = 1:1.000

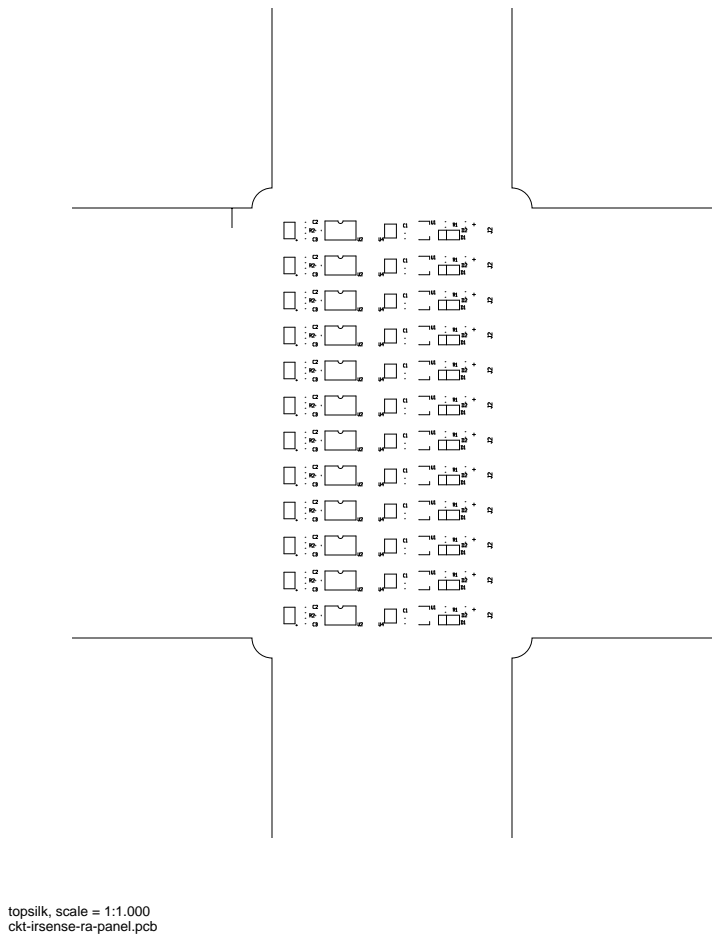
[picture p238: page 9]
topsilk, scale = 1:1.000

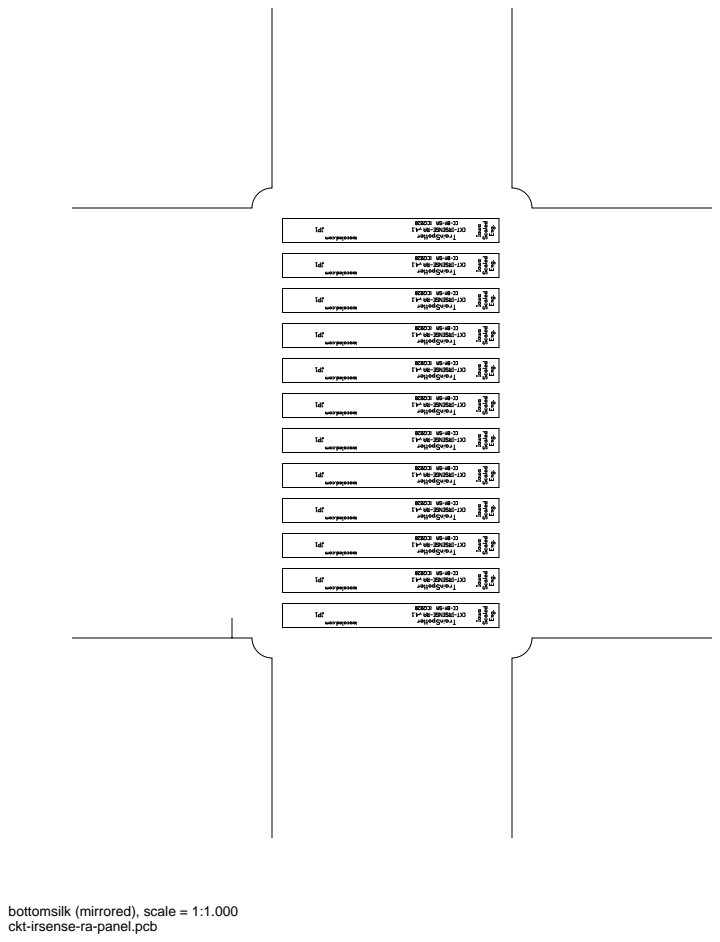
[picture p239: page 10]

bottomsilk (mirrored), scale = 1:1.000

toppaste, scale = 1:1.000 bottompaste (mirrored), scale = 1:1.000

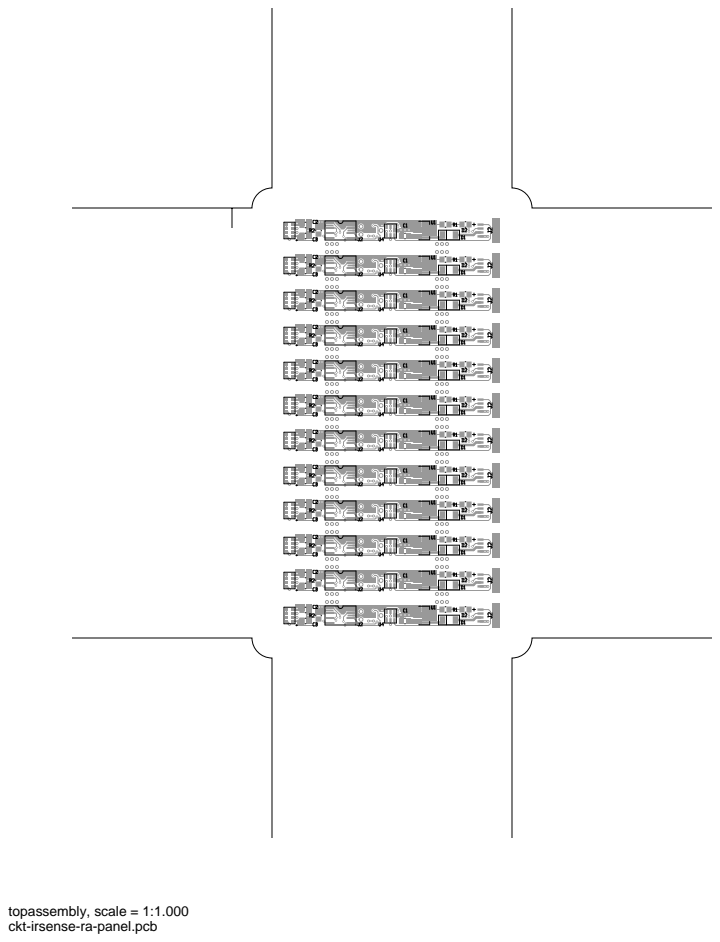
[picture p240: page 13]
topassembly, scale = 1:1.000

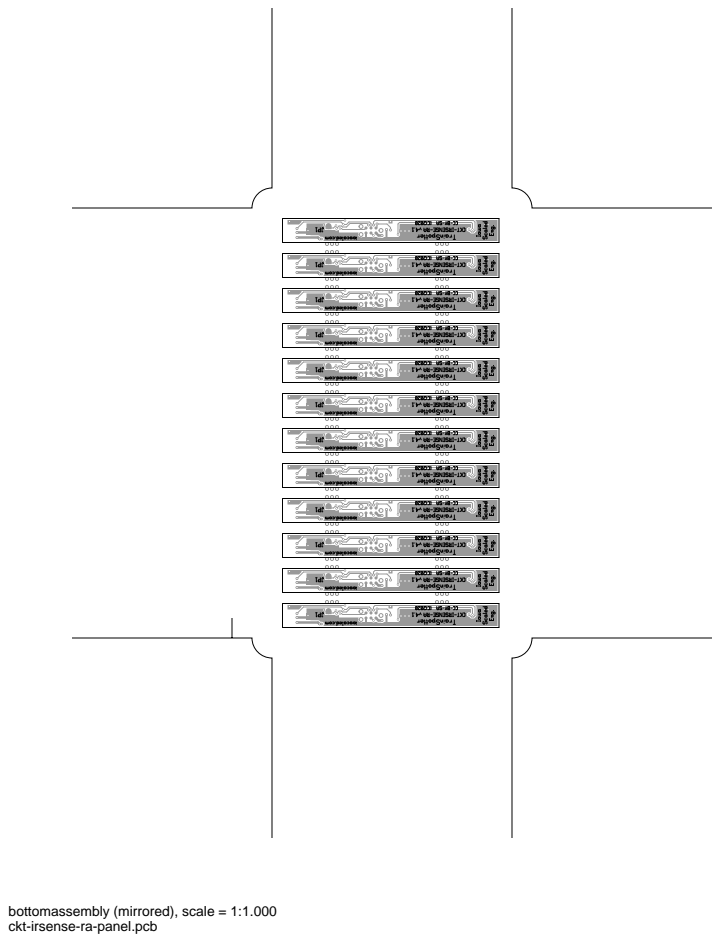
[picture p241: page 14]

bottomassembly (mirrored), scale = 1:1.000

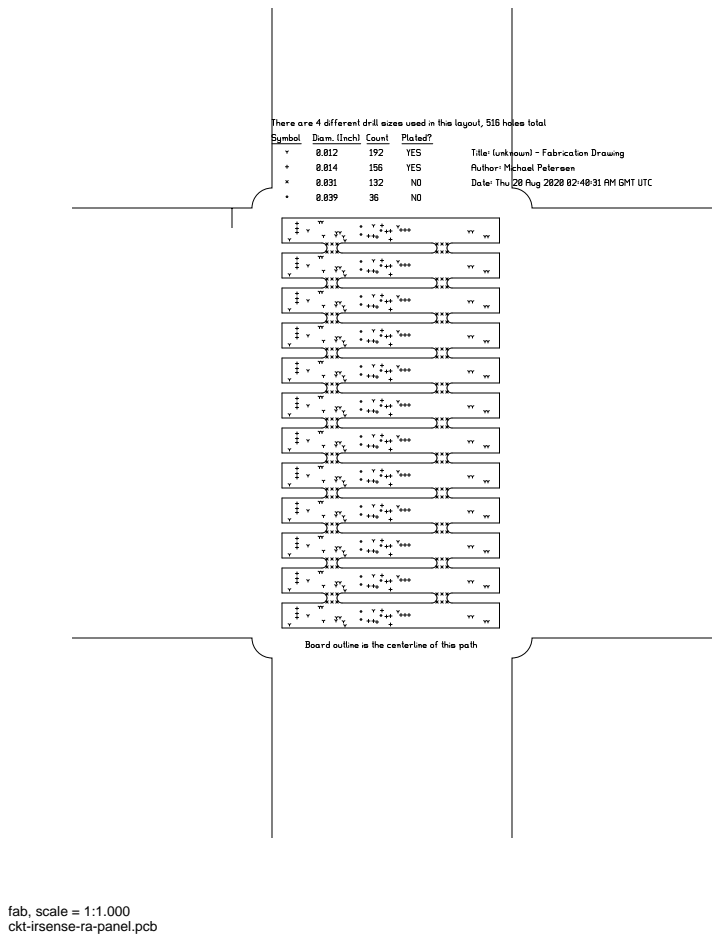
[picture p242: page 15]
fab, scale = 1:1.000
