IowaScaledEngineering/ckt-irsense/pg/i2c-irsense-panel-v2.1-6e7594a/i2c-irsense.pdf

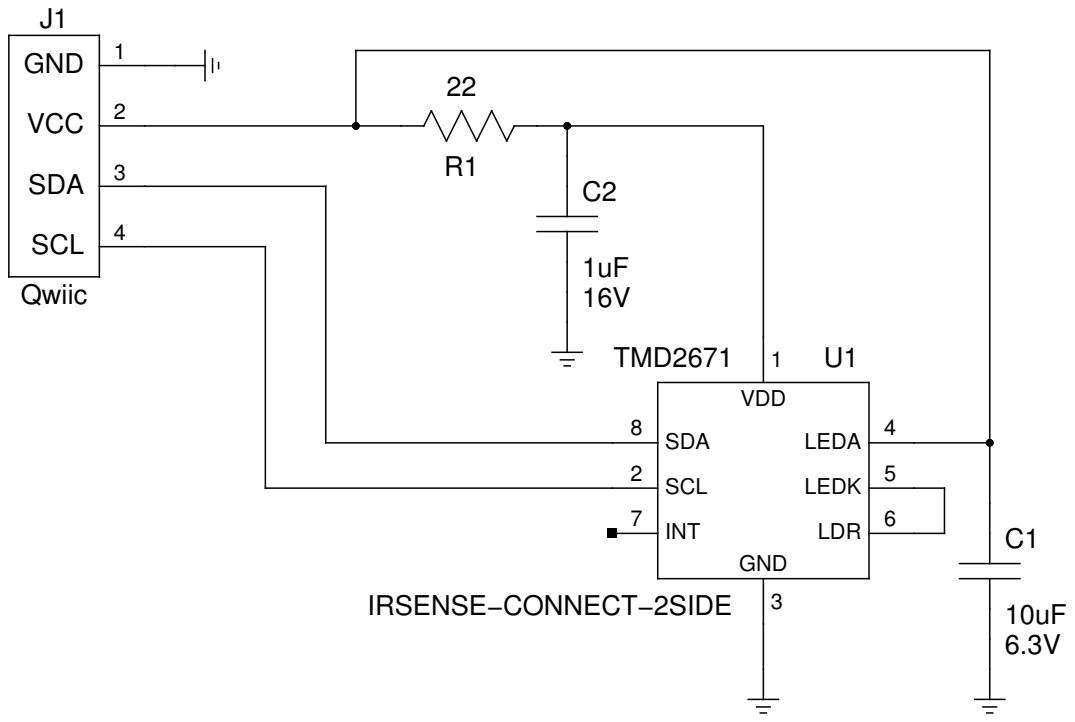
[picture p243: page 1]
4 LEDA; 5 LEDK; 6 LDR; 8 SDA; 2 SCL; 7 INT; PAGE; DRAWN BY:; Reflective IR Proximity Sensor (Qwiic compatible); Nathan Holmes / Michael Petersen
