IowaScaledEngineering/ckt-irsense/pg/i2c-irsense-v1.1-0d06f27/i2c-irsense.pdf

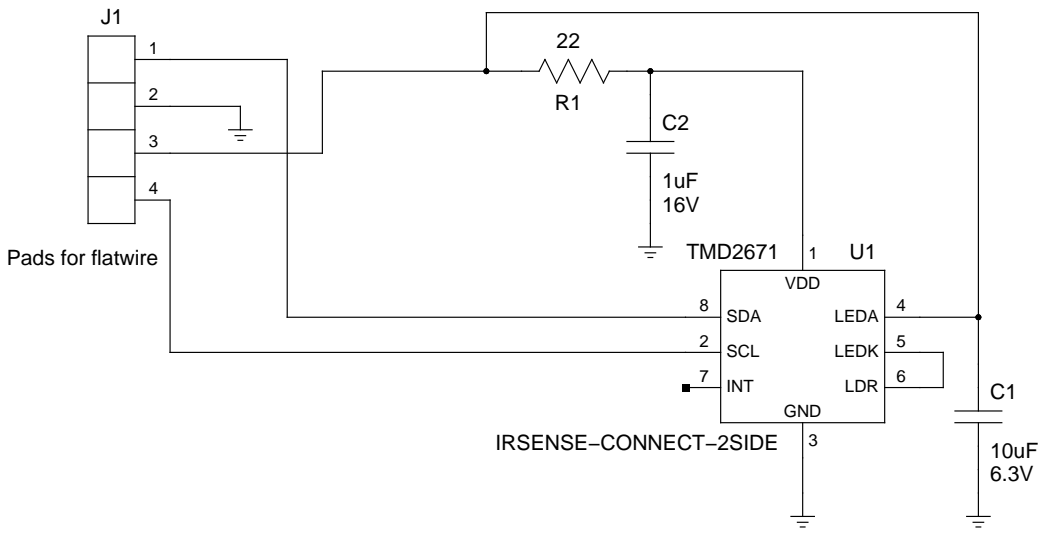
[picture p244: page 1]
Nathan Holmes / Michael Petersen; 4 LEDA; 5 LEDK; 6 LDR; PAGE; DRAWN BY:

Pads for flatwire

Reflective IR Model Railroad Sensor (v3)
ckt−irsense.sch
