IowaScaledEngineering/ckt-irsense/pg/ckt-irsense-v3.2-r1103/ckt-irsense.pdf

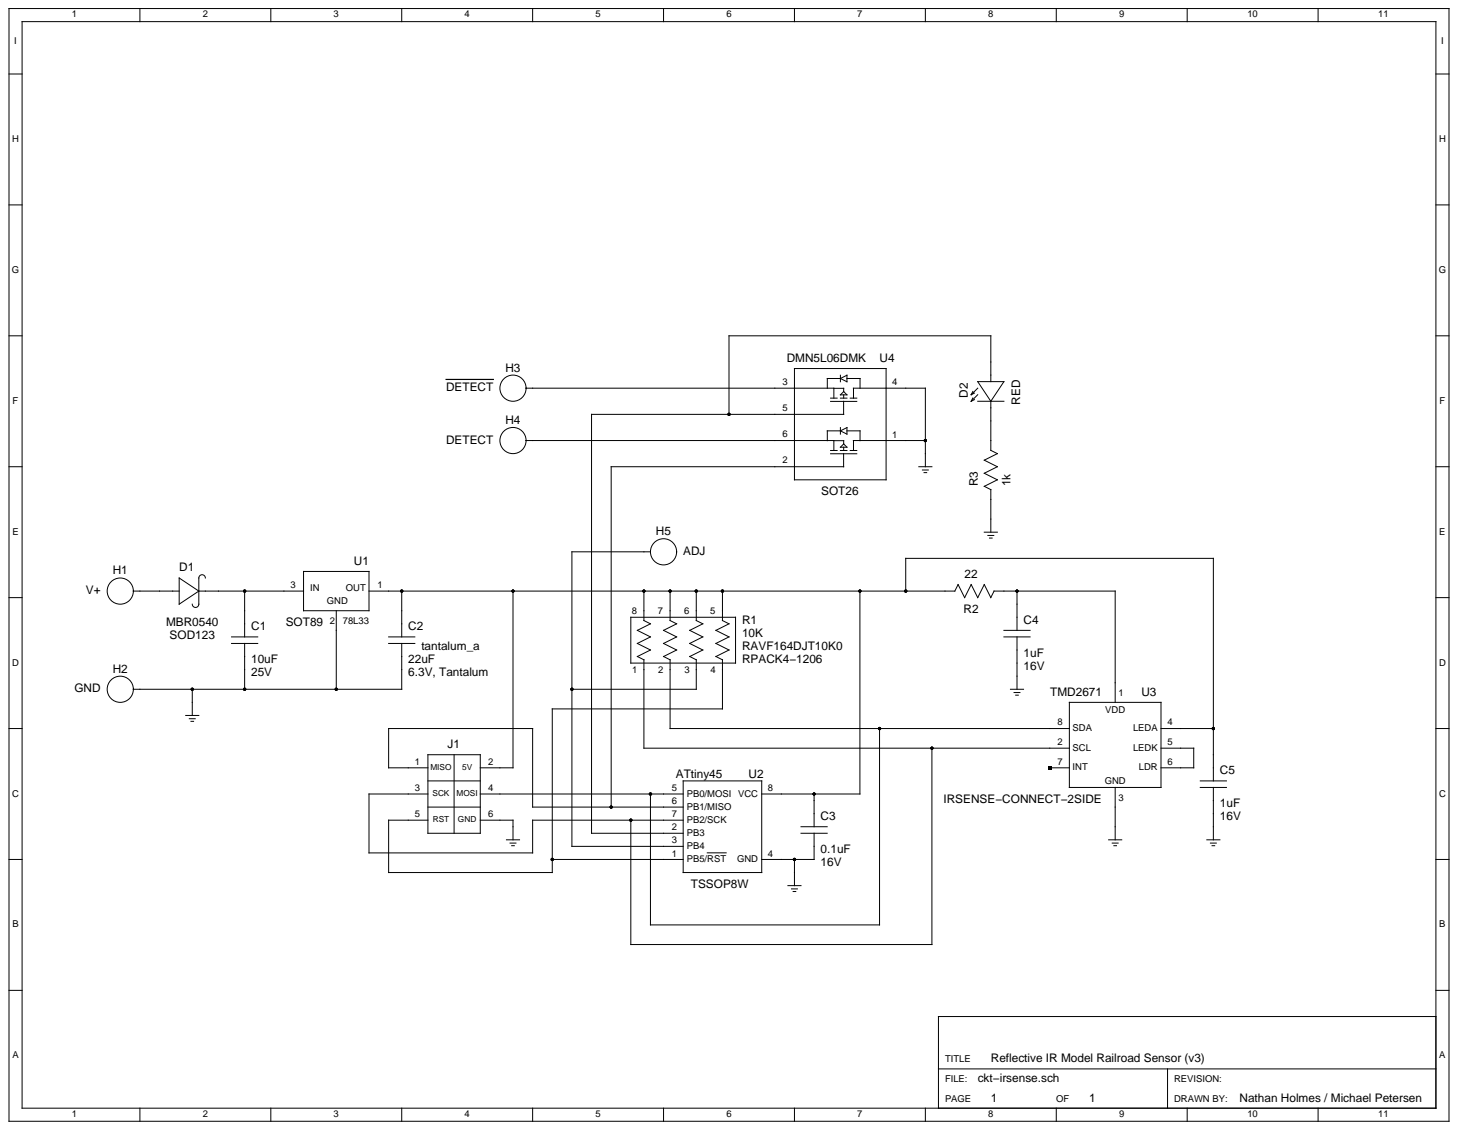
[picture p245: page 1]

Reflective IR Model Railroad Sensor (v3)
ckt−irsense.sch
