IowaScaledEngineering/ckt-irsense/pg/ckt-irsense-ra-array-v4.3a-7e089c9/ckt-irsense-ra-array-pcb.pdf

# ckt-irsense-ra-array.pcb

# 1. Table of Contents (This Page) Created on Mon Jul 24 15:31:58 2023

# 2. top 3. bottom 4. outline 5. plated-drill 6. unplated-drill 7. componentmask 8. soldermask 9. topsilk 10. bottomsilk 11. toppaste 12. bottompaste 13. topassembly 14. bottomassembly 15. fab

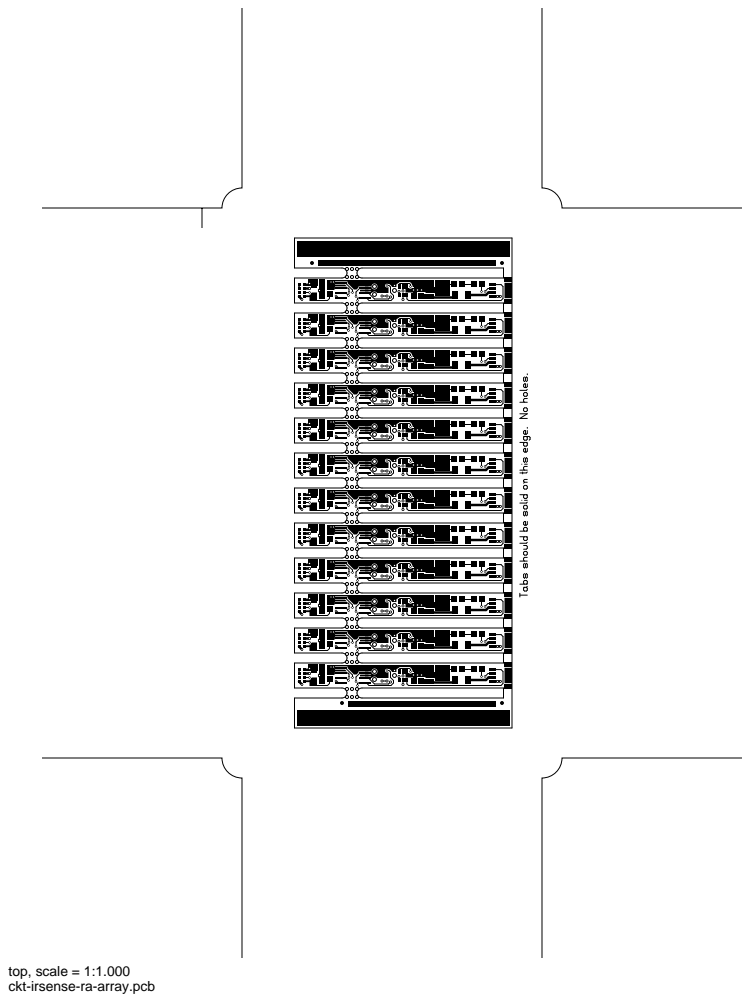
[picture p251: page 2]
top, scale = 1:1.000

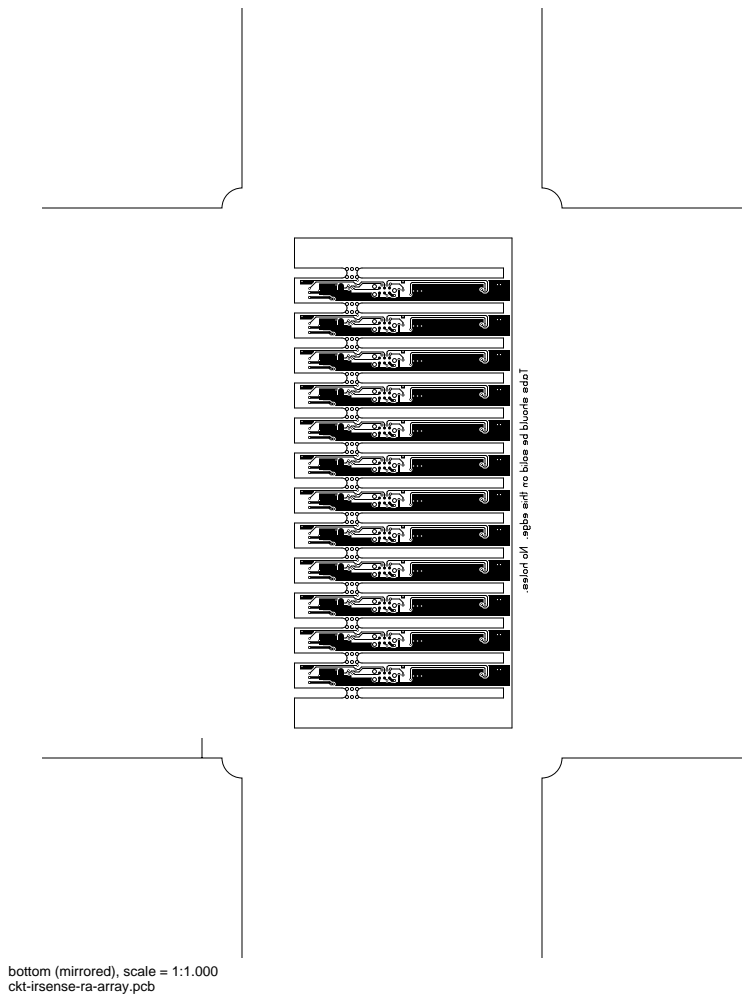
[picture p252: page 3]

bottom (mirrored), scale = 1:1.000

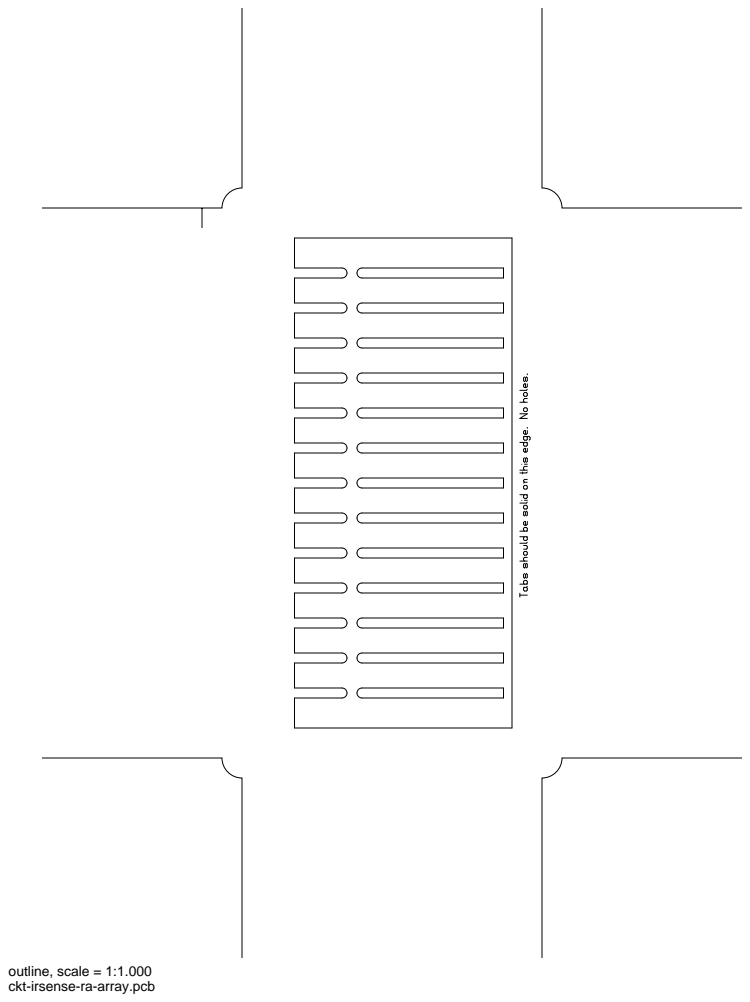
[picture p253: page 4]
outline, scale = 1:1.000


plated-drill, scale = 1:1.000


unplated-drill, scale = 1:1.000

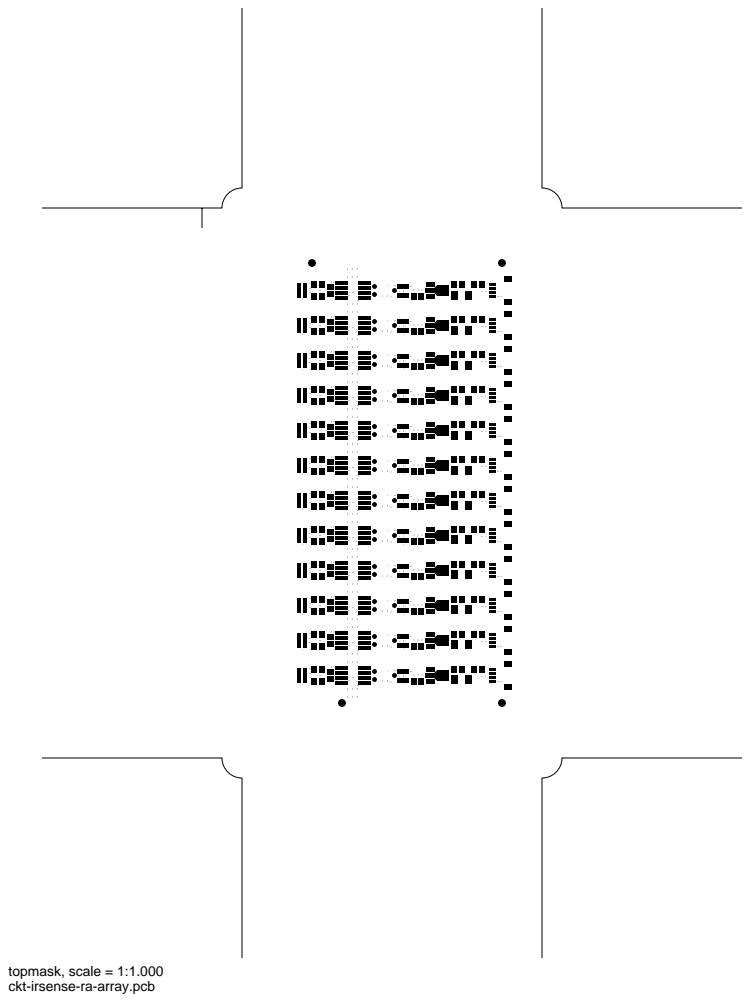
[picture p254: page 7]
topmask, scale = 1:1.000


bottommask (mirrored), scale = 1:1.000

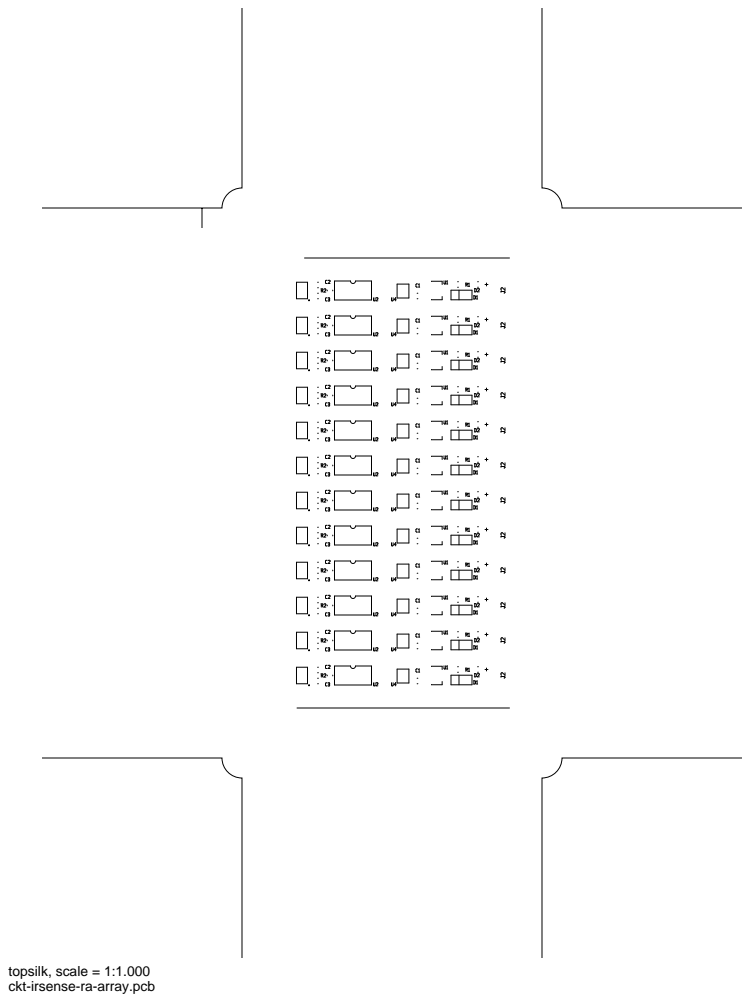
[picture p255: page 9]
topsilk, scale = 1:1.000

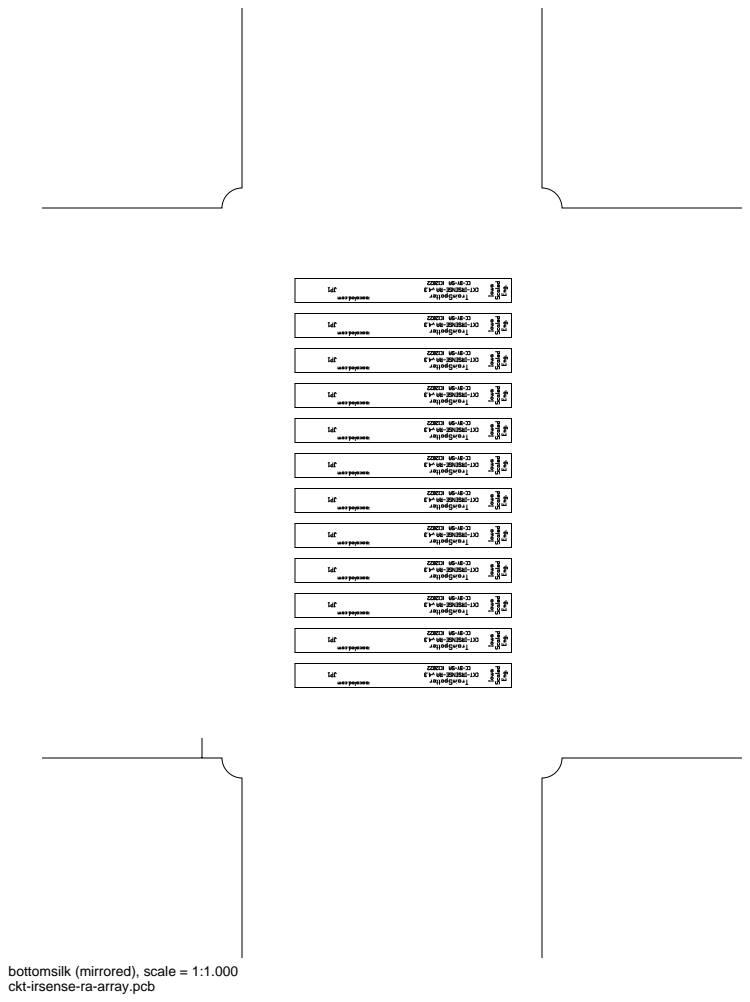
[picture p256: page 10]

bottomsilk (mirrored), scale = 1:1.000

toppaste, scale = 1:1.000 bottompaste (mirrored), scale = 1:1.000

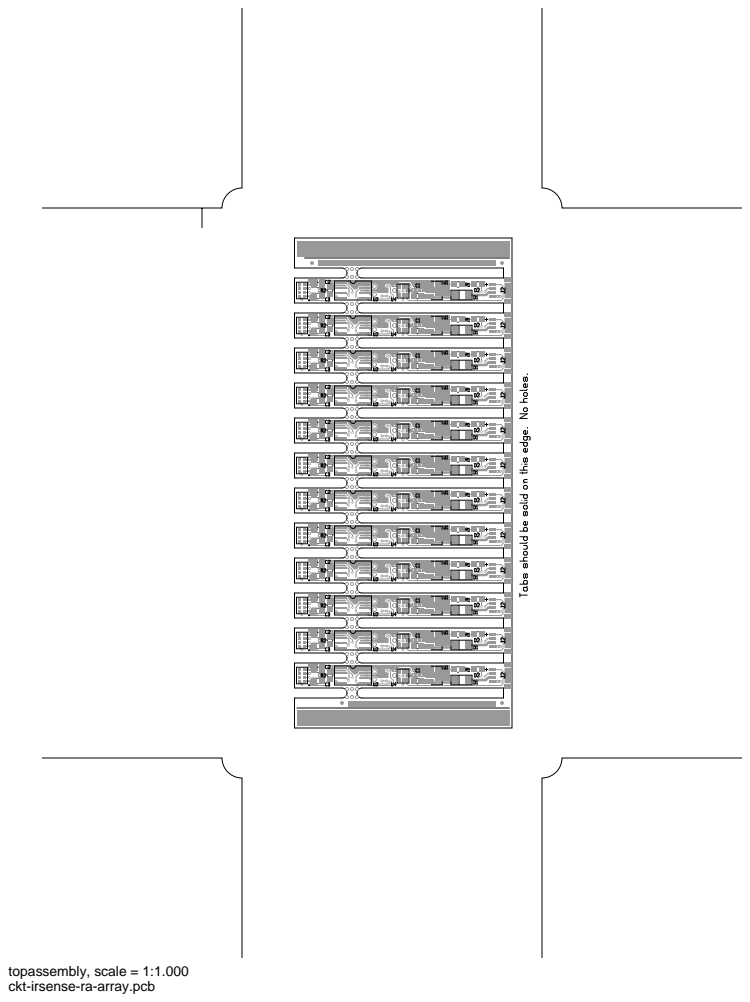
[picture p257: page 13]
topassembly, scale = 1:1.000

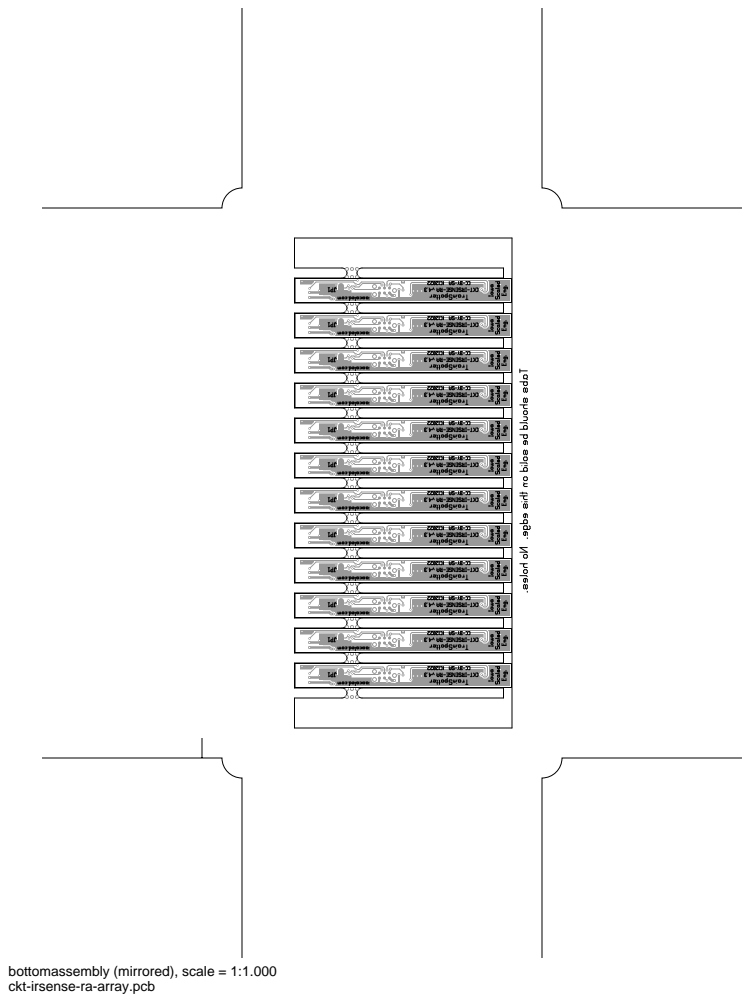
[picture p258: page 14]

bottomassembly (mirrored), scale = 1:1.000

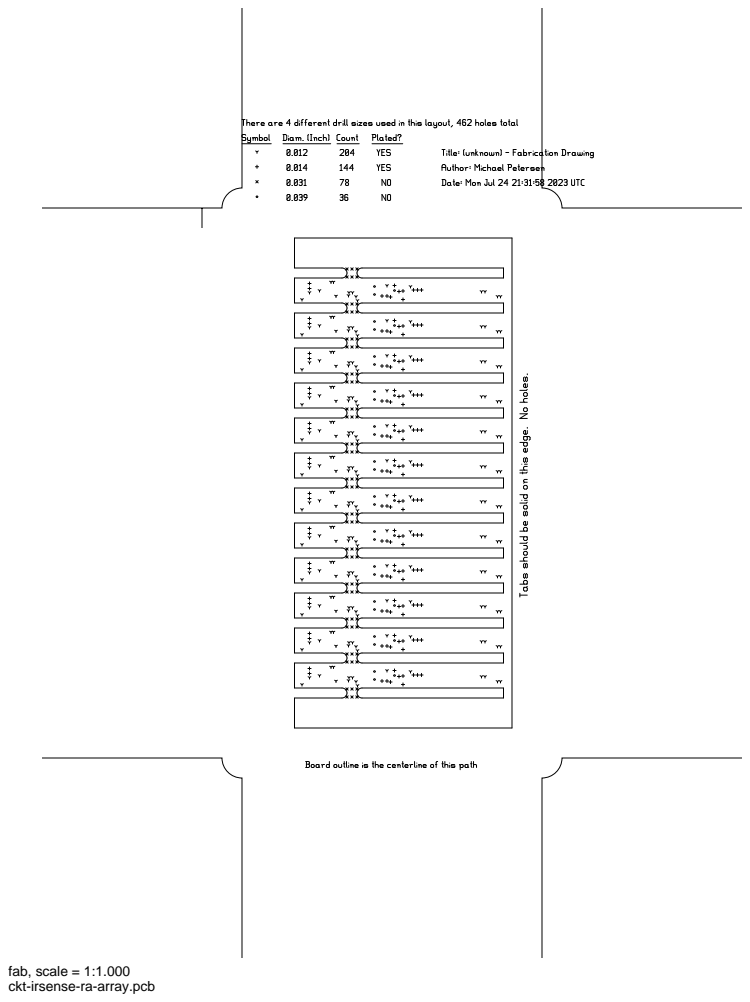
[picture p259: page 15]
fab, scale = 1:1.000
