IowaScaledEngineering/ckt-irsense/pg/ckt-irsense-array-v4.3-9e8855f/ckt-irsense-array-pcb.pdf

# ckt-irsense-array.pcb

# 1. Table of Contents (This Page) Created on Wed Jun 21 21:03:34 2023

# 2. top 3. bottom 4. outline 5. plated-drill 6. unplated-drill 7. componentmask 8. soldermask 9. topsilk 10. bottomsilk 11. toppaste 12. bottompaste 13. topassembly 14. bottomassembly 15. fab

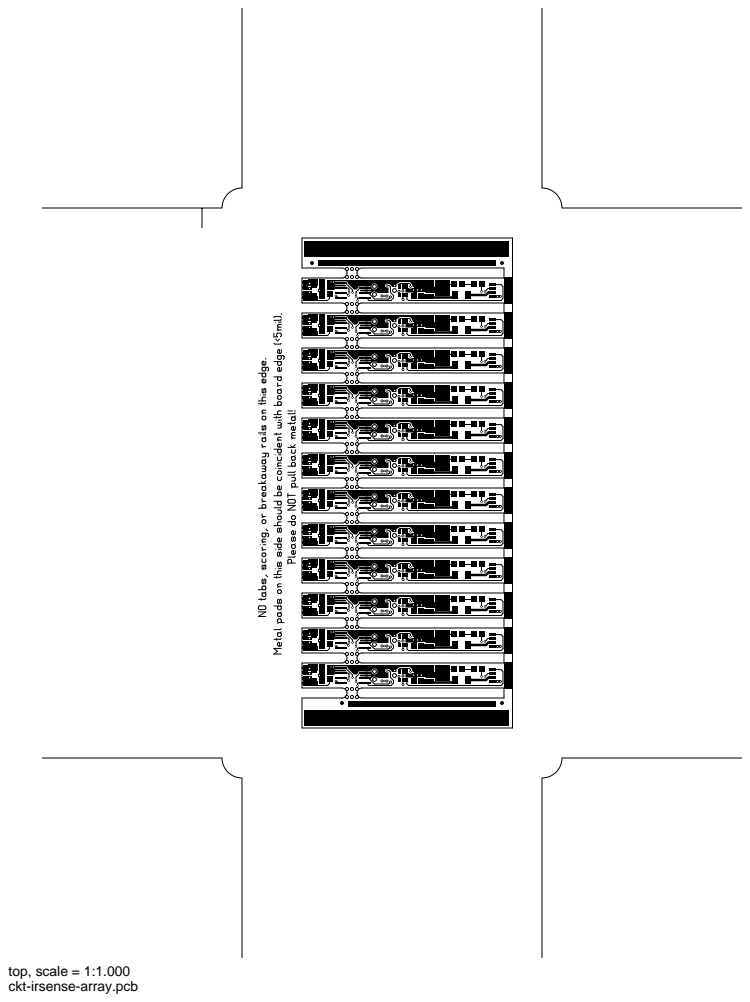
[picture p260: page 2]
top, scale = 1:1.000

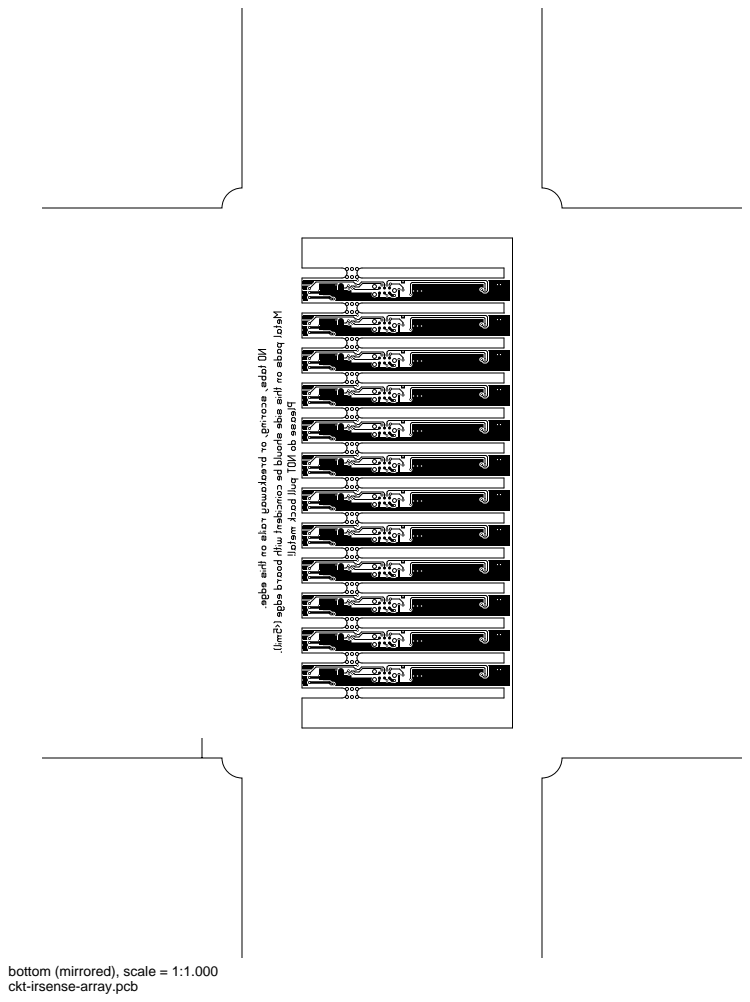
[picture p261: page 3]

bottom (mirrored), scale = 1:1.000

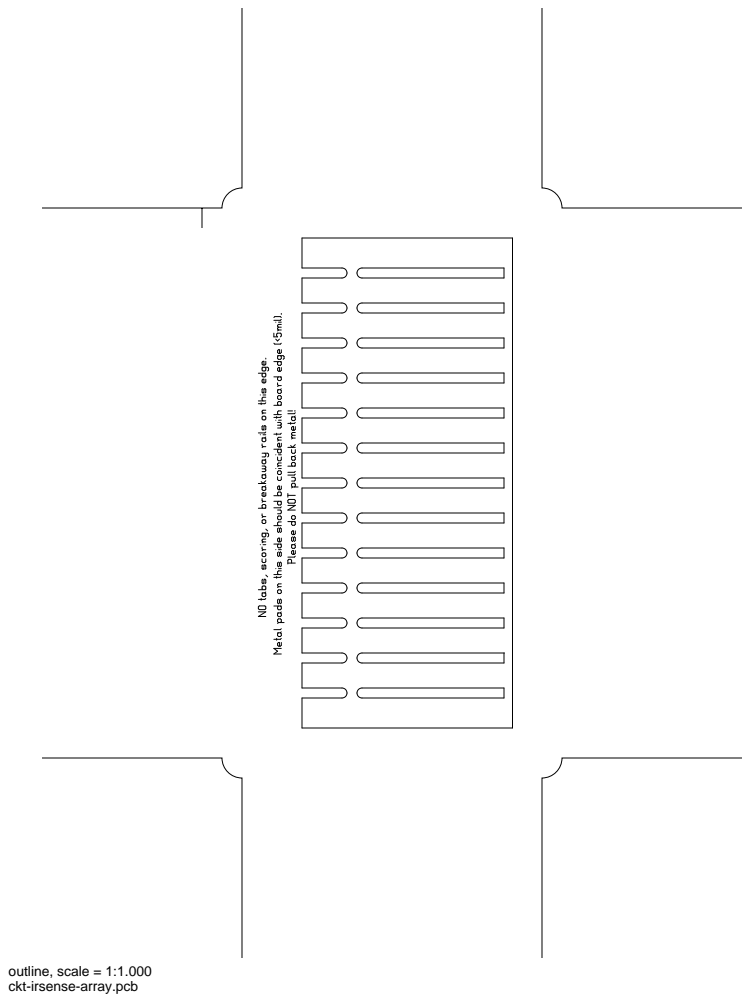
[picture p262: page 4]
outline, scale = 1:1.000


plated-drill, scale = 1:1.000


unplated-drill, scale = 1:1.000

topmask, scale = 1:1.000


bottommask (mirrored), scale = 1:1.000

topsilk, scale = 1:1.000


bottomsilk (mirrored), scale = 1:1.000

toppaste, scale = 1:1.000 bottompaste (mirrored), scale = 1:1.000

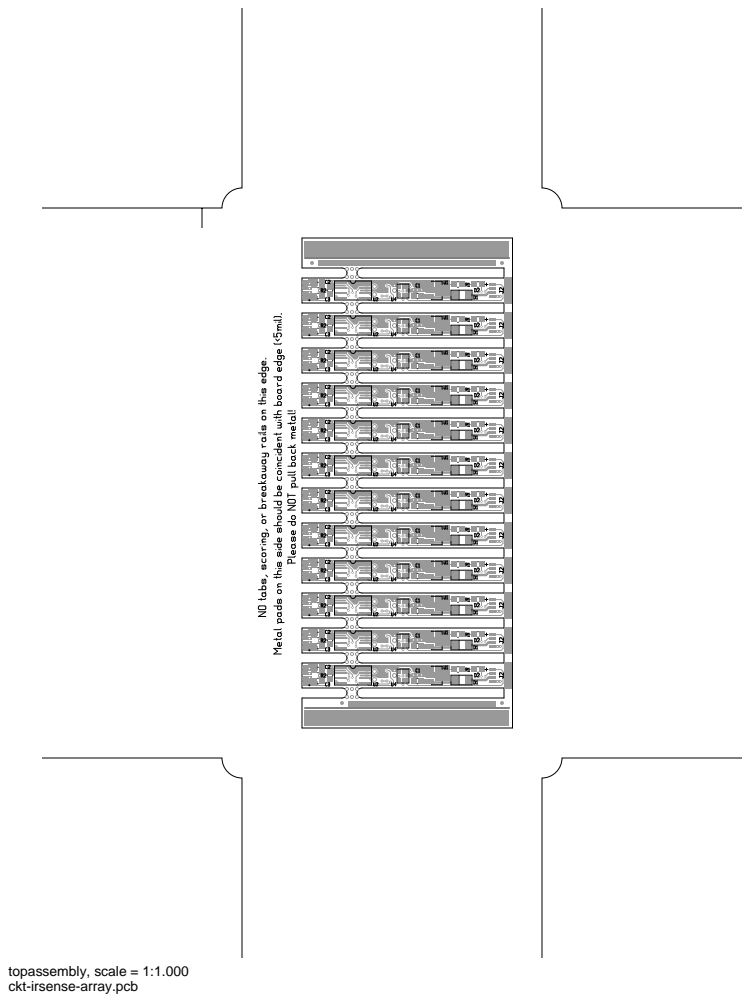
[picture p263: page 13]
topassembly, scale = 1:1.000

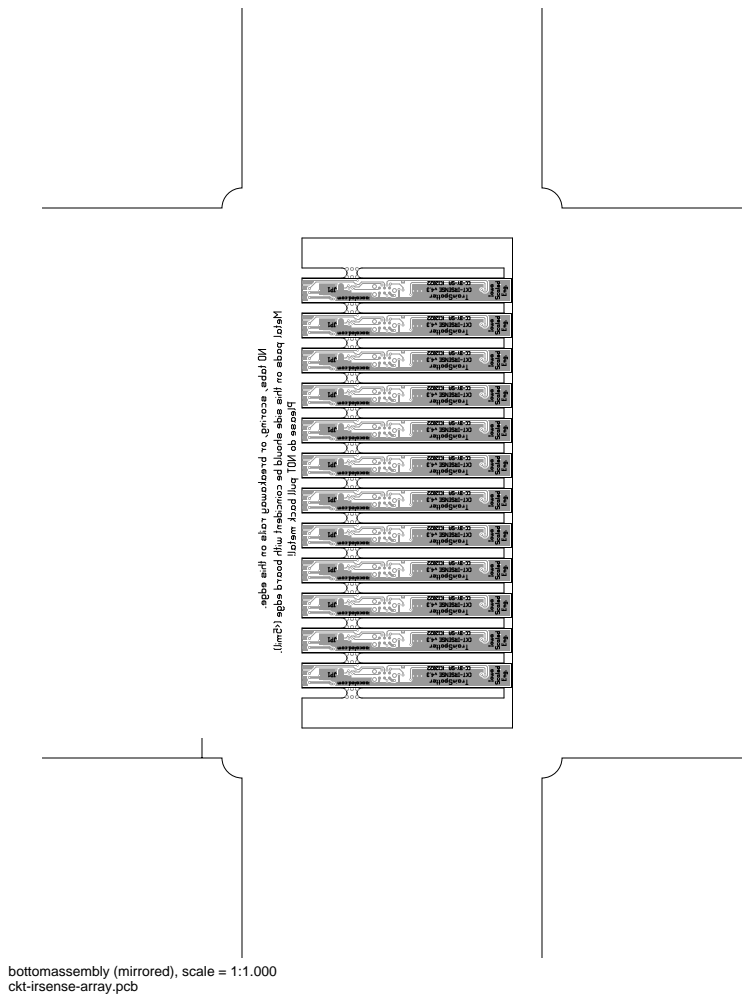
[picture p264: page 14]

bottomassembly (mirrored), scale = 1:1.000

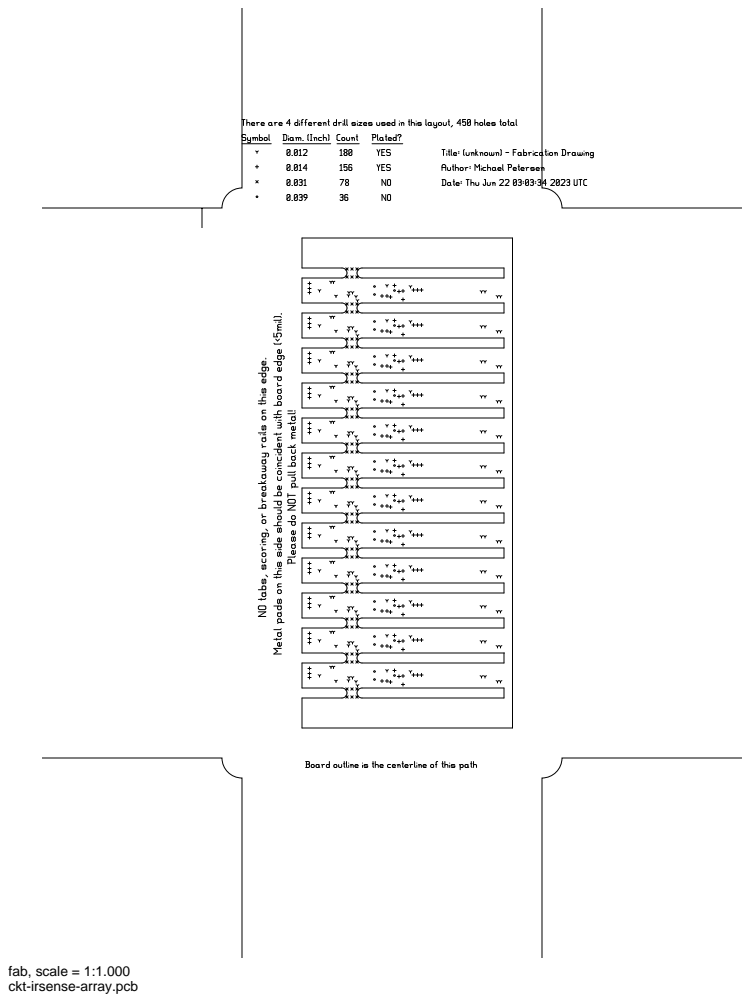
[picture p265: page 15]
fab, scale = 1:1.000
