IowaScaledEngineering/ckt-irsense/pg/ckt-irsense-array-v4.2-3599b4a/ckt-irsense-array-pcb.pdf

# ckt-irsense-array.pcb

# 1. Table of Contents (This Page) Created on Sat Oct 15 21:37:32 2022

# 2. top 3. bottom 4. outline 5. plated-drill 6. unplated-drill 7. componentmask 8. soldermask 9. topsilk 10. bottomsilk 11. toppaste 12. bottompaste 13. topassembly 14. bottomassembly 15. fab

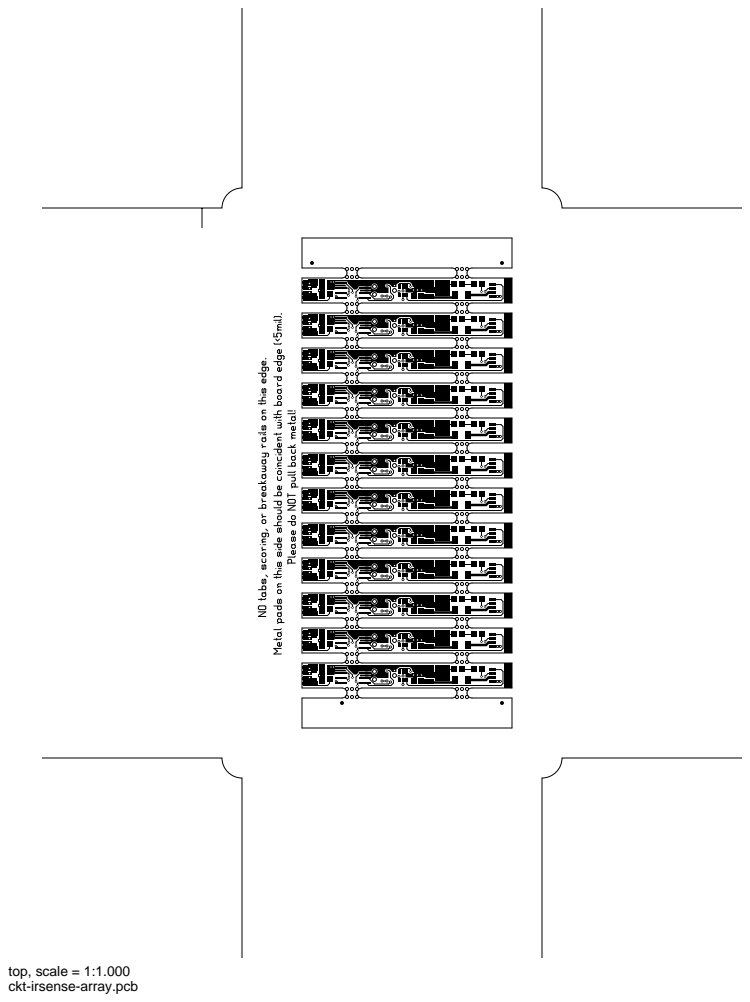
[picture p266: page 2]
top, scale = 1:1.000

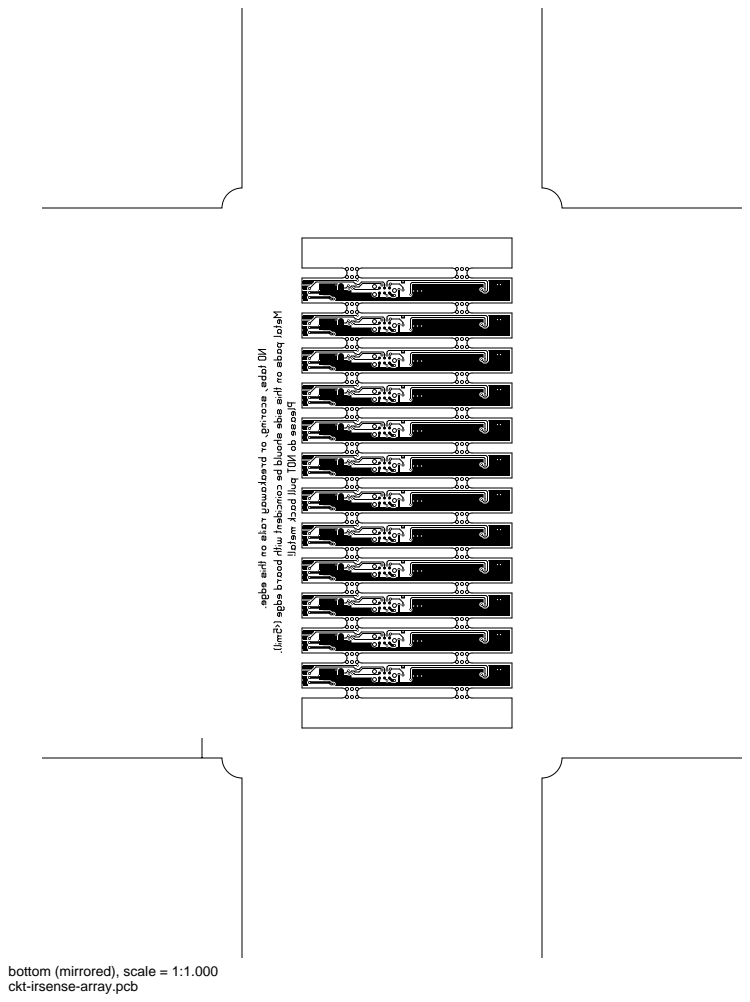
[picture p267: page 3]

bottom (mirrored), scale = 1:1.000

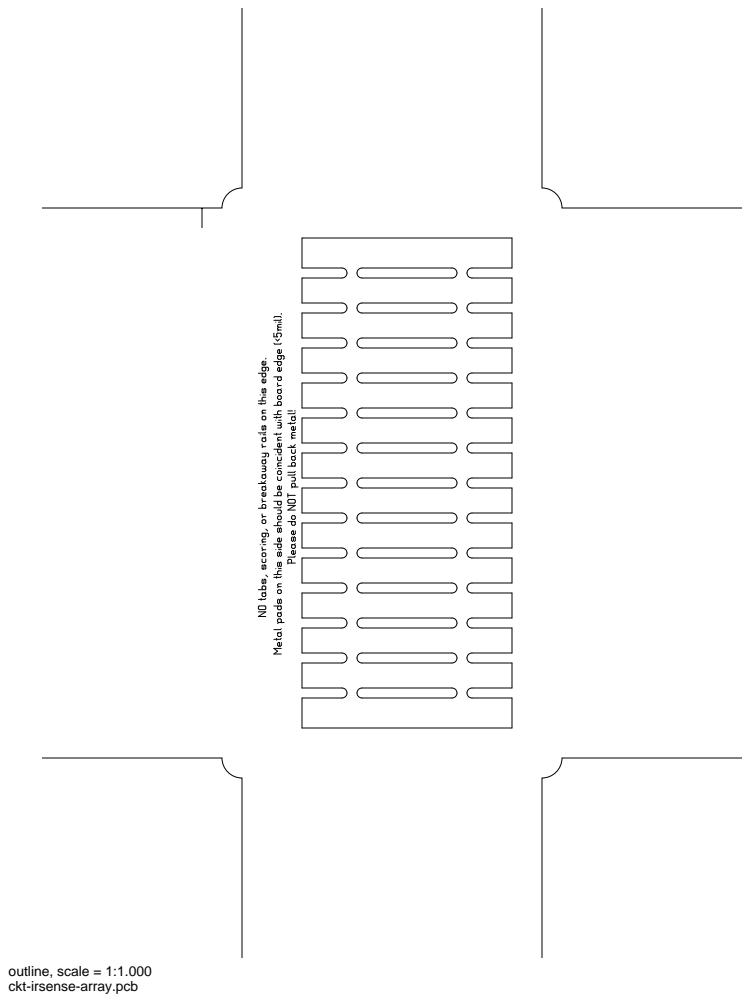
[picture p268: page 4]
outline, scale = 1:1.000


plated-drill, scale = 1:1.000

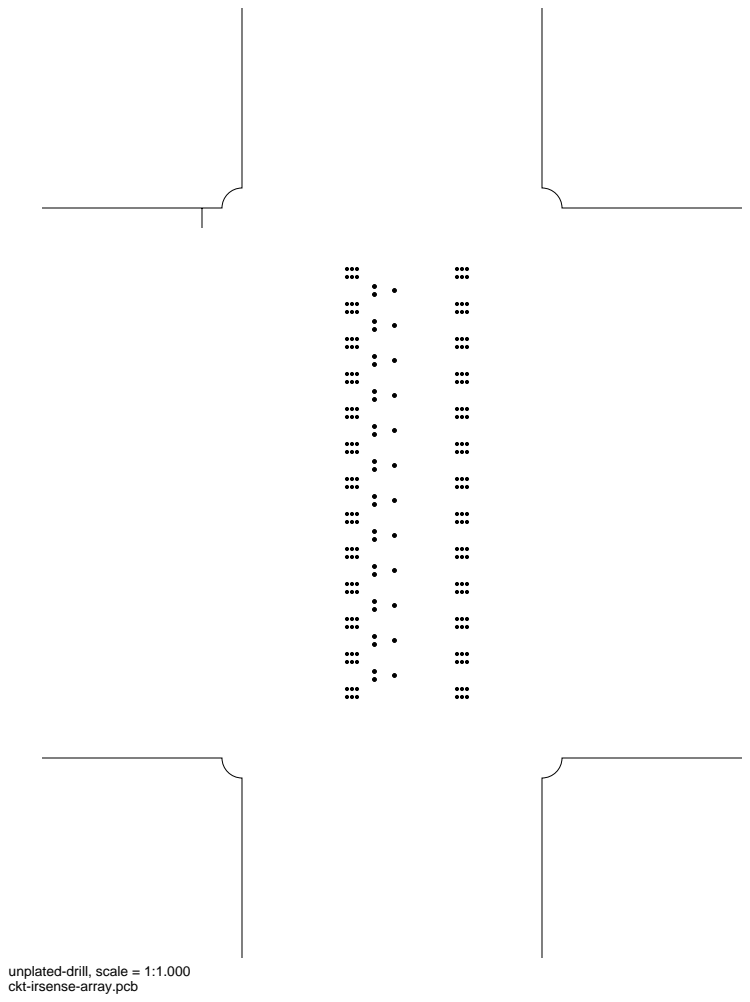
[picture p269: page 6]

unplated-drill, scale = 1:1.000

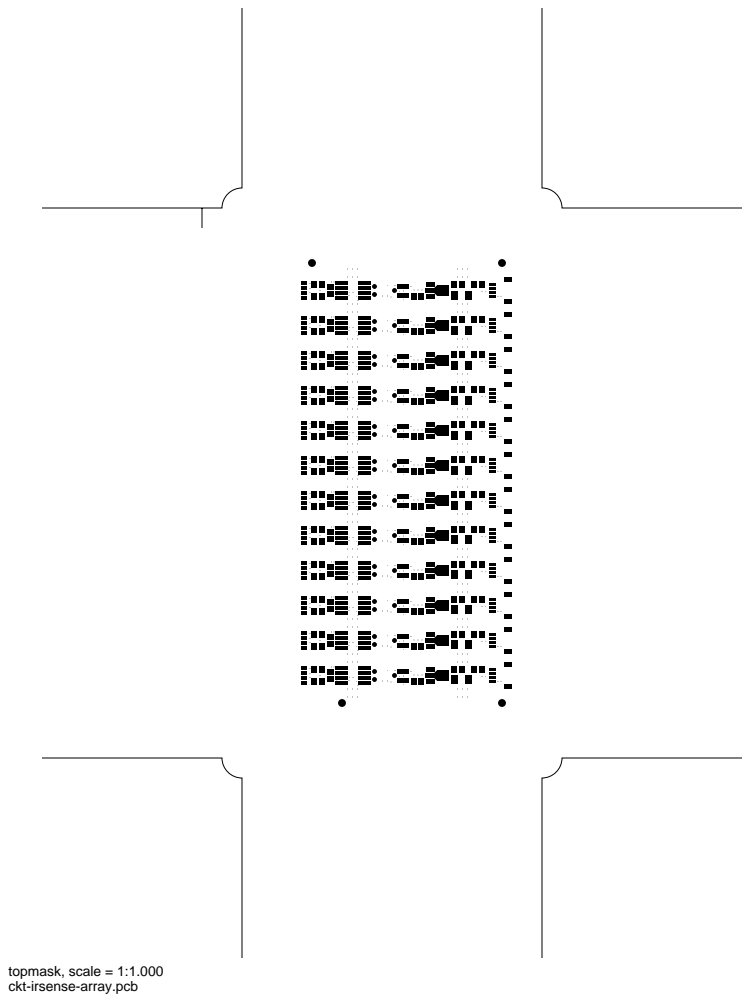
[picture p270: page 7]
topmask, scale = 1:1.000

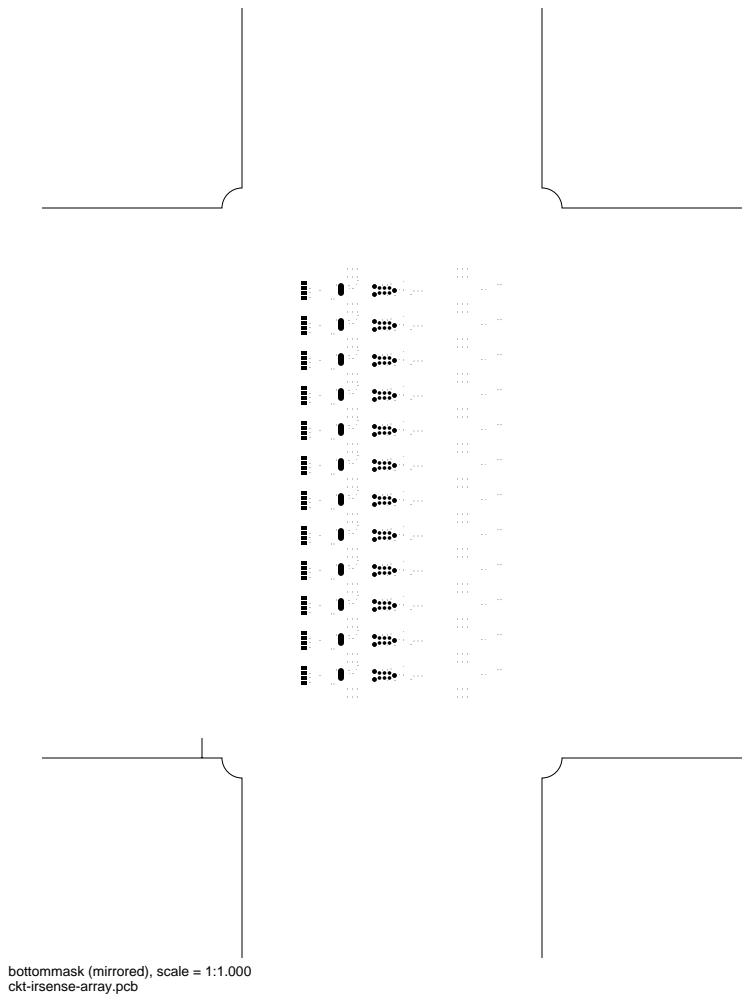
[picture p271: page 8]

bottommask (mirrored), scale = 1:1.000

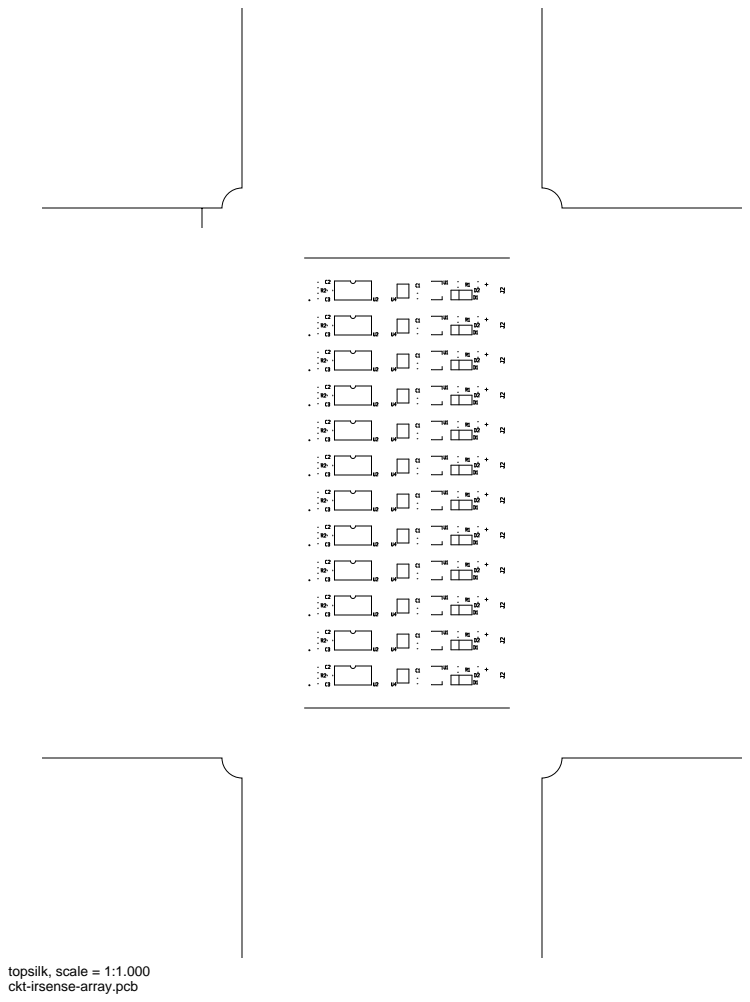
[picture p272: page 9]
topsilk, scale = 1:1.000

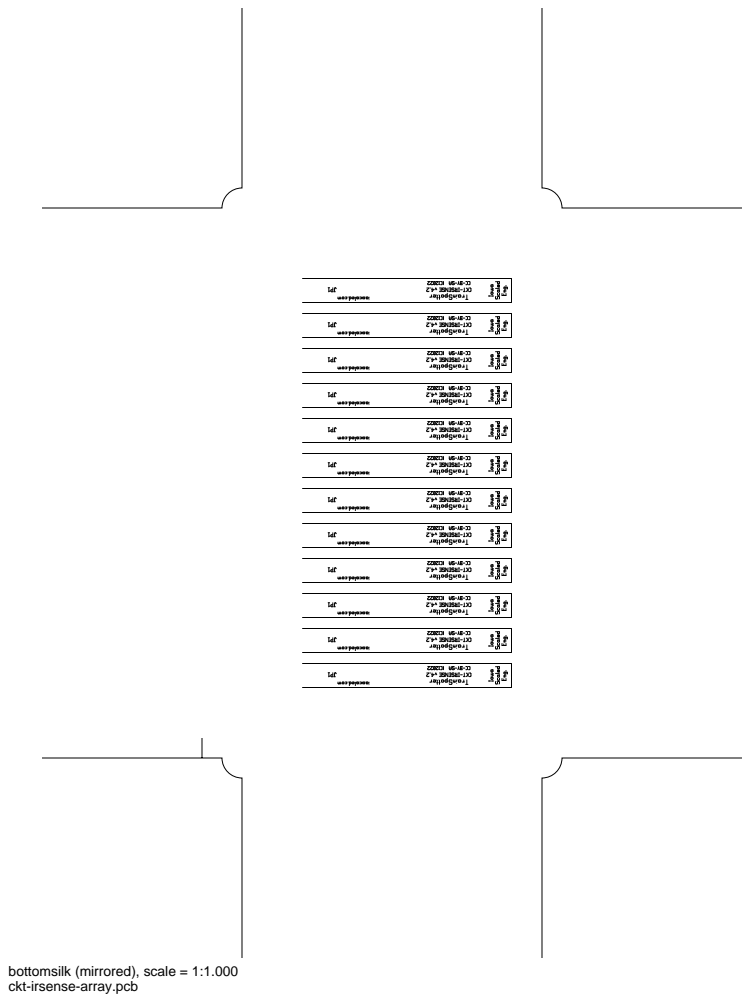
[picture p273: page 10]

bottomsilk (mirrored), scale = 1:1.000

toppaste, scale = 1:1.000 bottompaste (mirrored), scale = 1:1.000

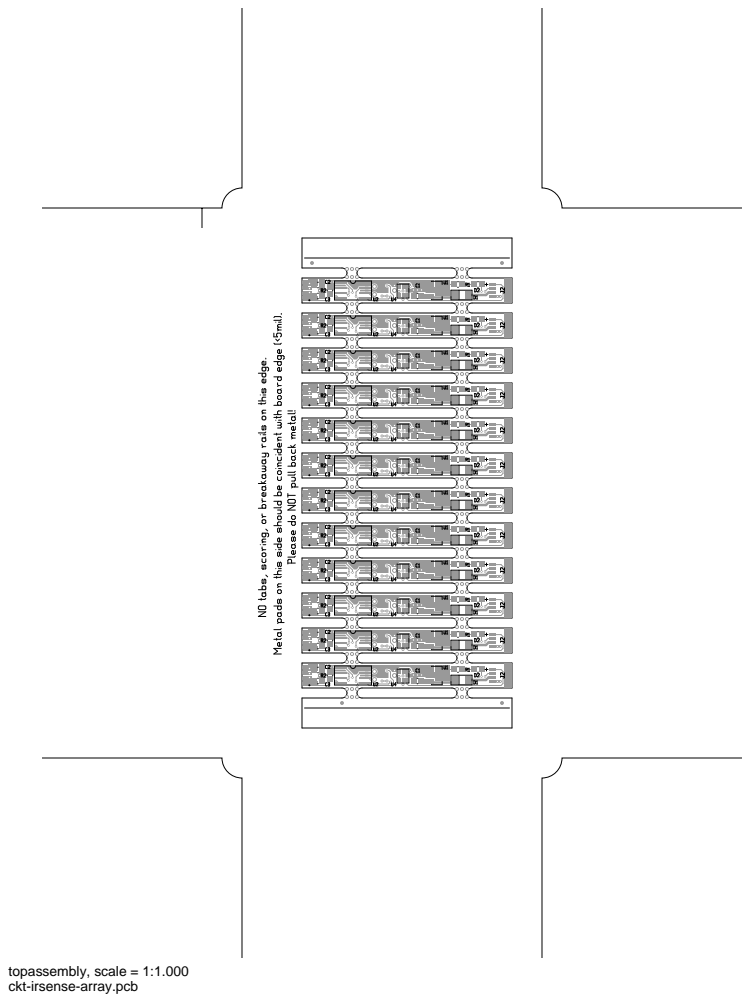
[picture p274: page 13]
topassembly, scale = 1:1.000

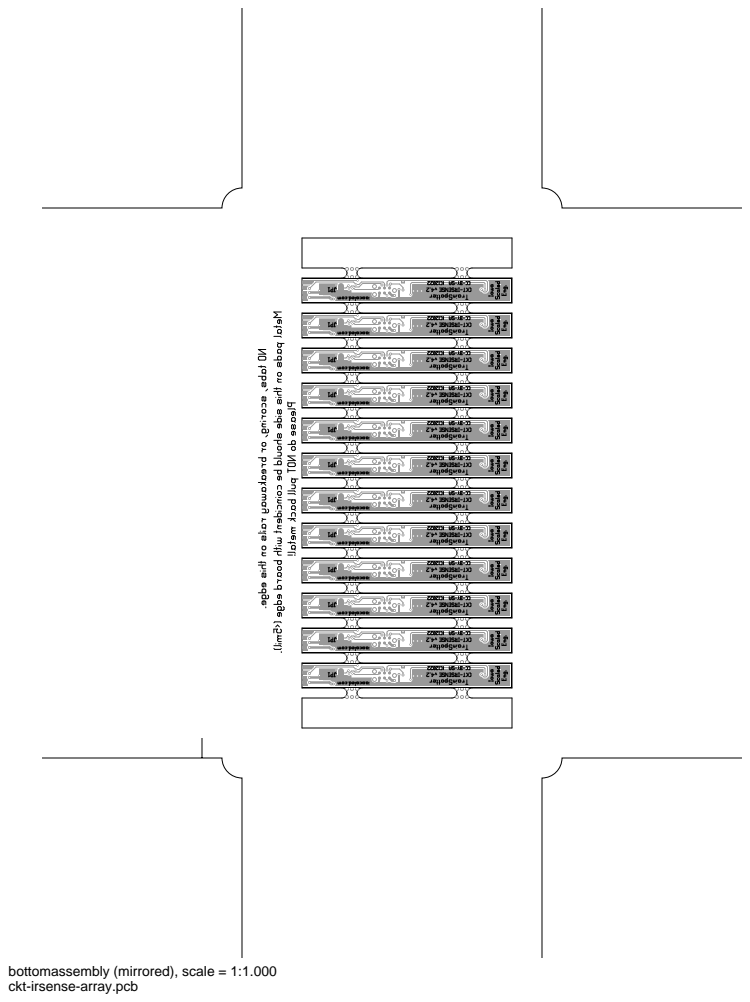
[picture p275: page 14]

bottomassembly (mirrored), scale = 1:1.000

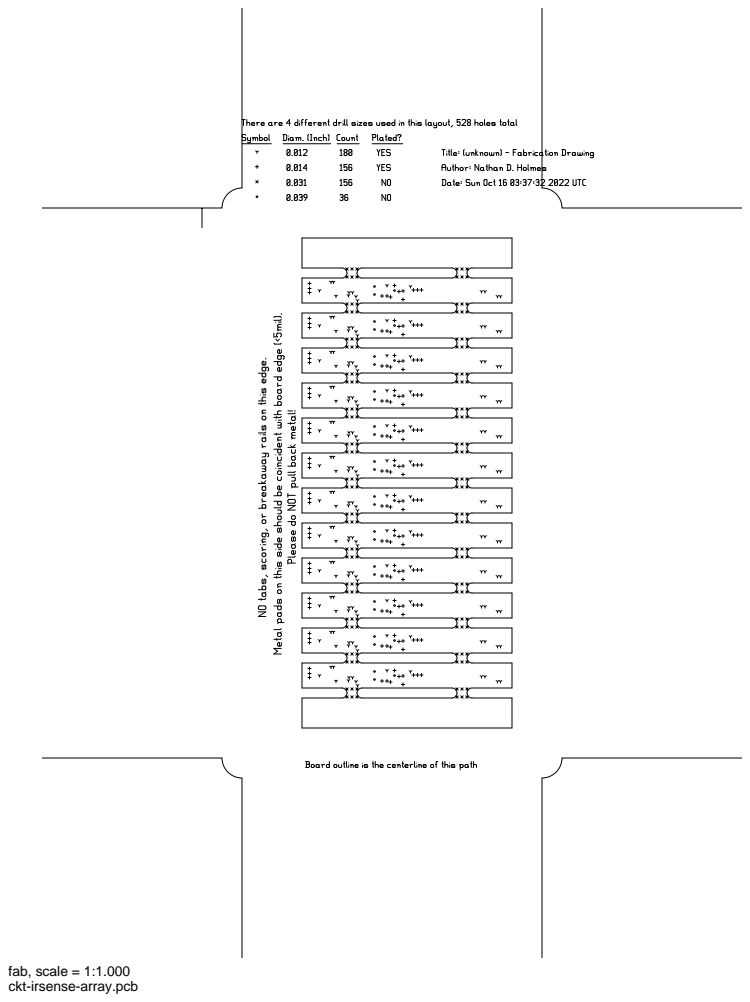
[picture p276: page 15]
fab, scale = 1:1.000
