IowaScaledEngineering/ckt-irsense/pg/ckt-irsense-ra-array-v4.2-3599b4a/ckt-irsense-ra-array-pcb.pdf

# ckt-irsense-ra-array.pcb

# 1. Table of Contents (This Page) Created on Sat May 14 21:05:20 2022

# 2. top 3. bottom 4. outline 5. plated-drill 6. unplated-drill 7. componentmask 8. soldermask 9. topsilk 10. bottomsilk 11. toppaste 12. bottompaste 13. topassembly 14. bottomassembly 15. fab

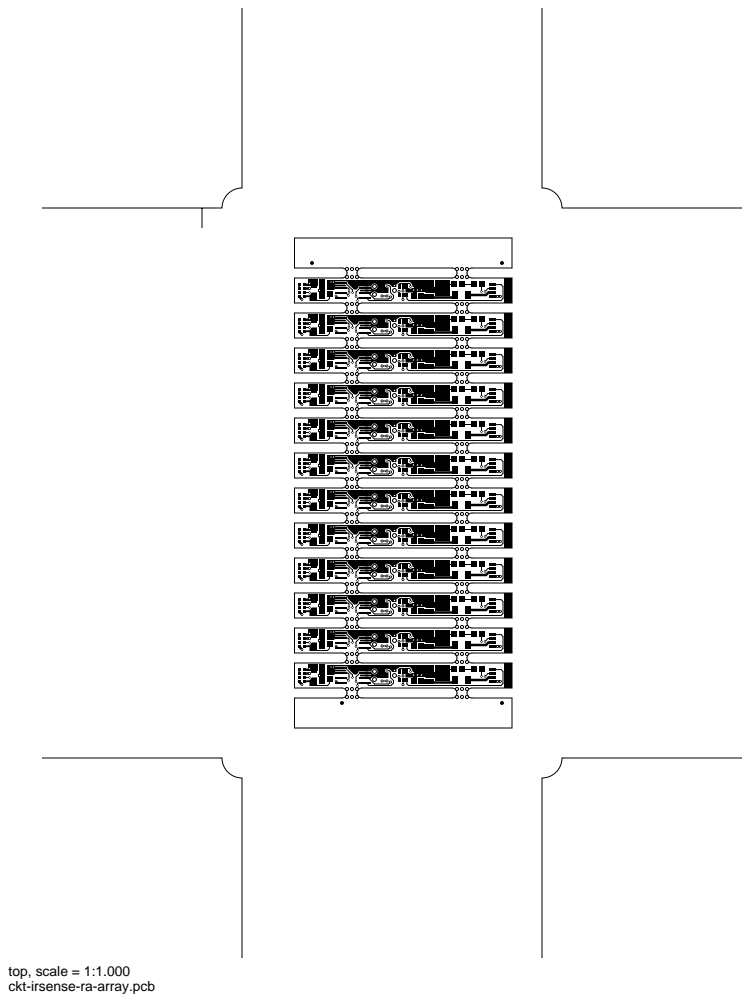
[picture p277: page 2]
top, scale = 1:1.000

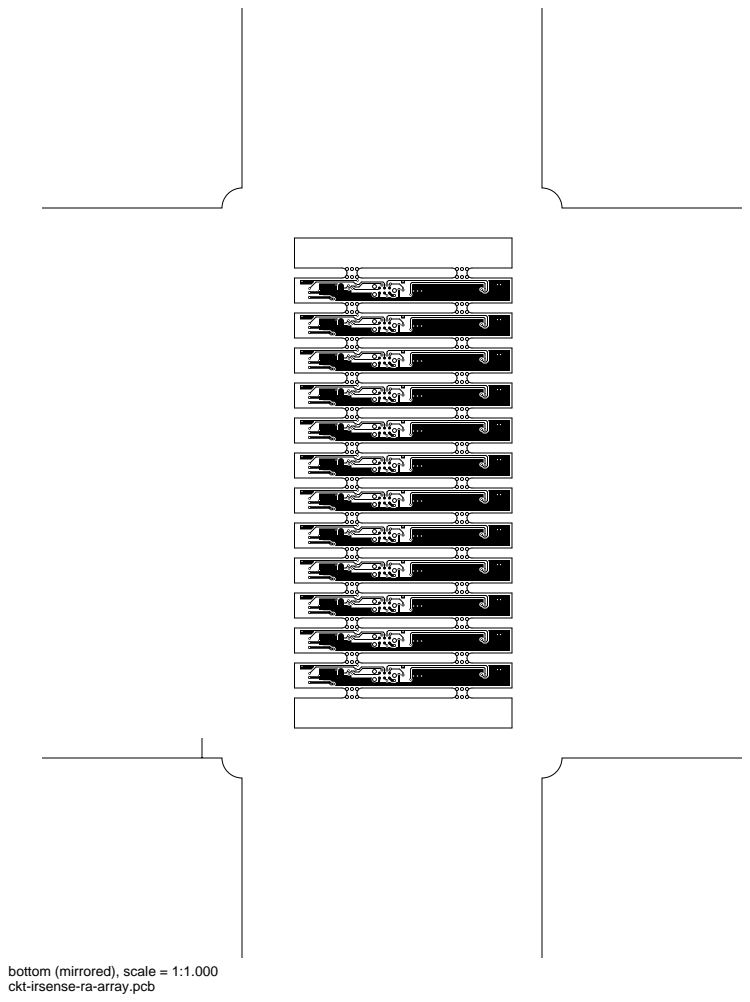
[picture p278: page 3]

bottom (mirrored), scale = 1:1.000

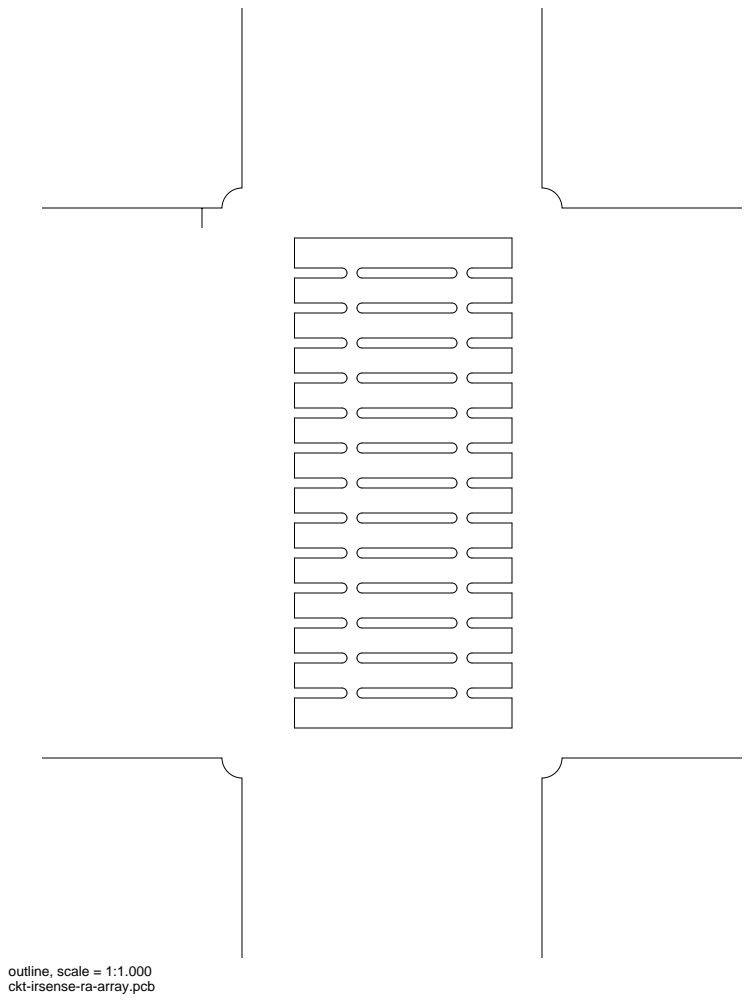
[picture p279: page 4]
outline, scale = 1:1.000


plated-drill, scale = 1:1.000

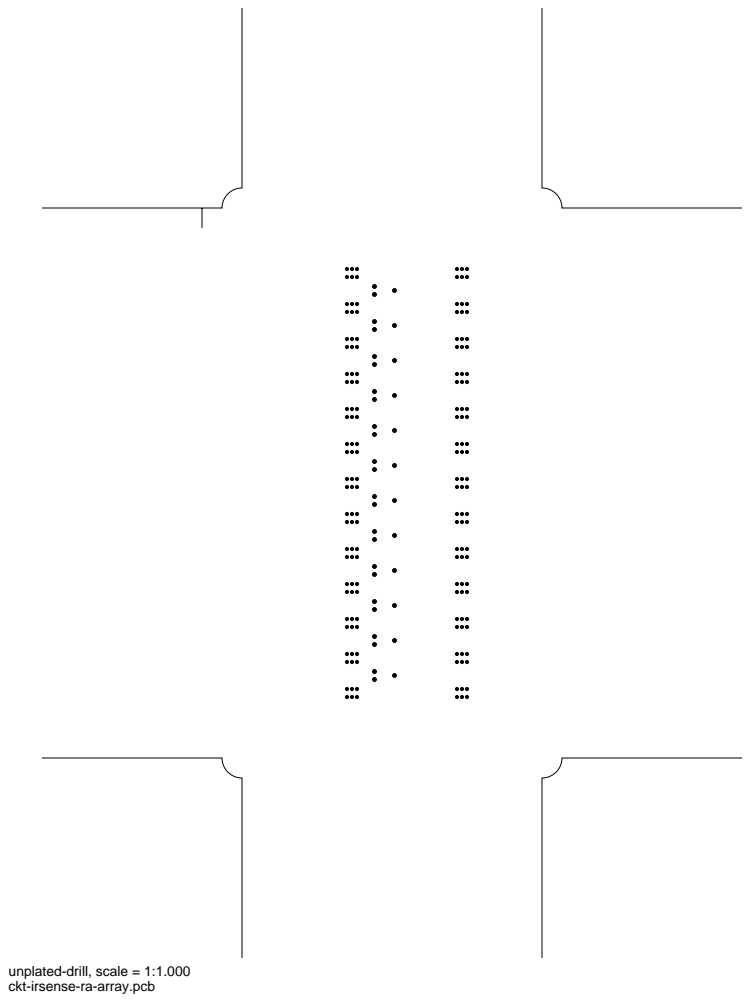
[picture p280: page 6]

unplated-drill, scale = 1:1.000

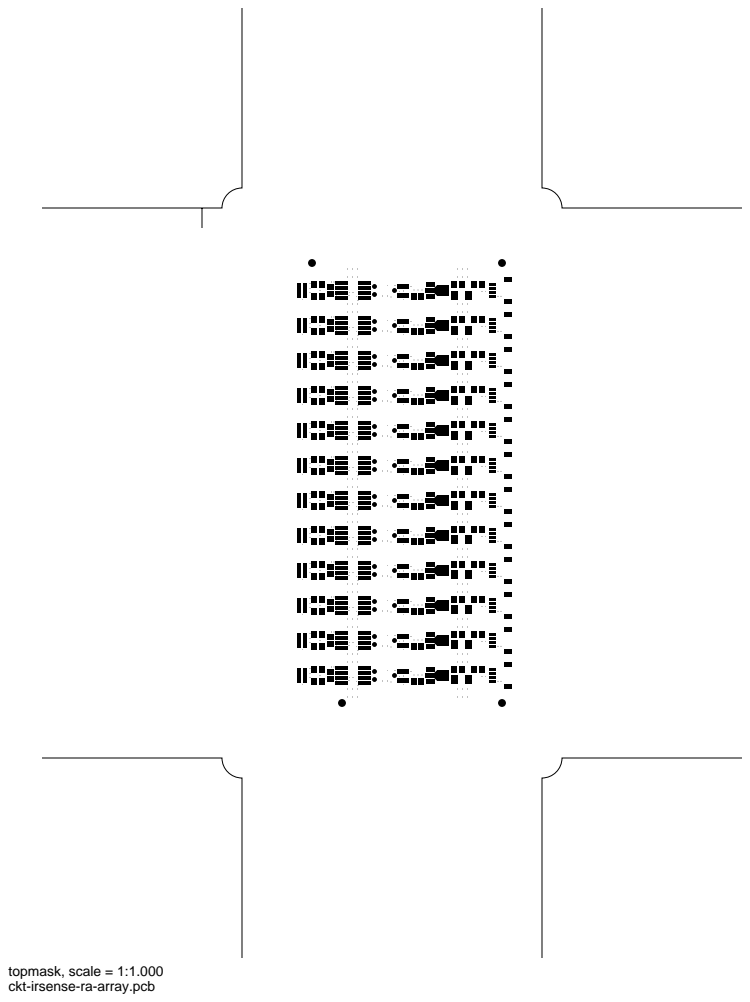
[picture p281: page 7]
topmask, scale = 1:1.000

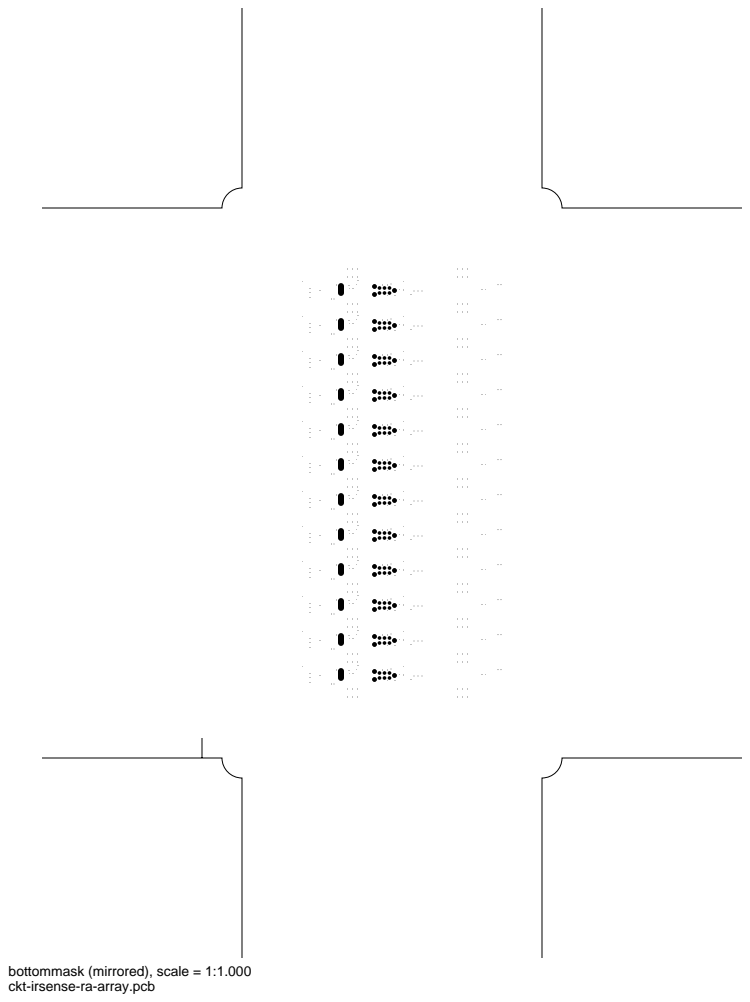
[picture p282: page 8]

bottommask (mirrored), scale = 1:1.000

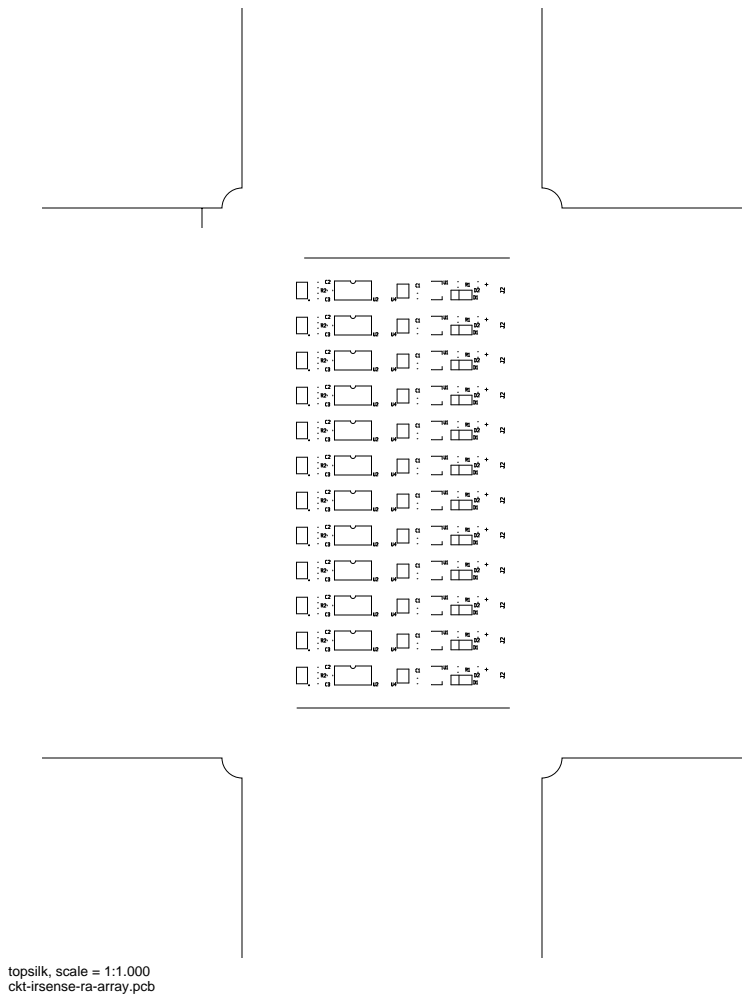
[picture p283: page 9]
topsilk, scale = 1:1.000

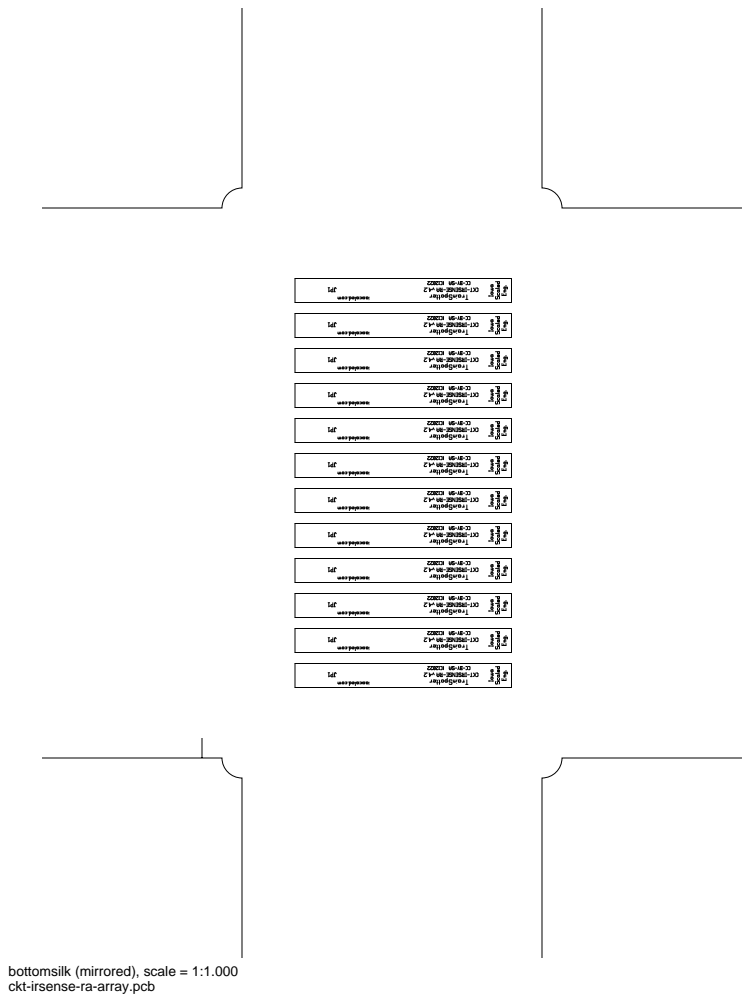
[picture p284: page 10]

bottomsilk (mirrored), scale = 1:1.000

toppaste, scale = 1:1.000 bottompaste (mirrored), scale = 1:1.000

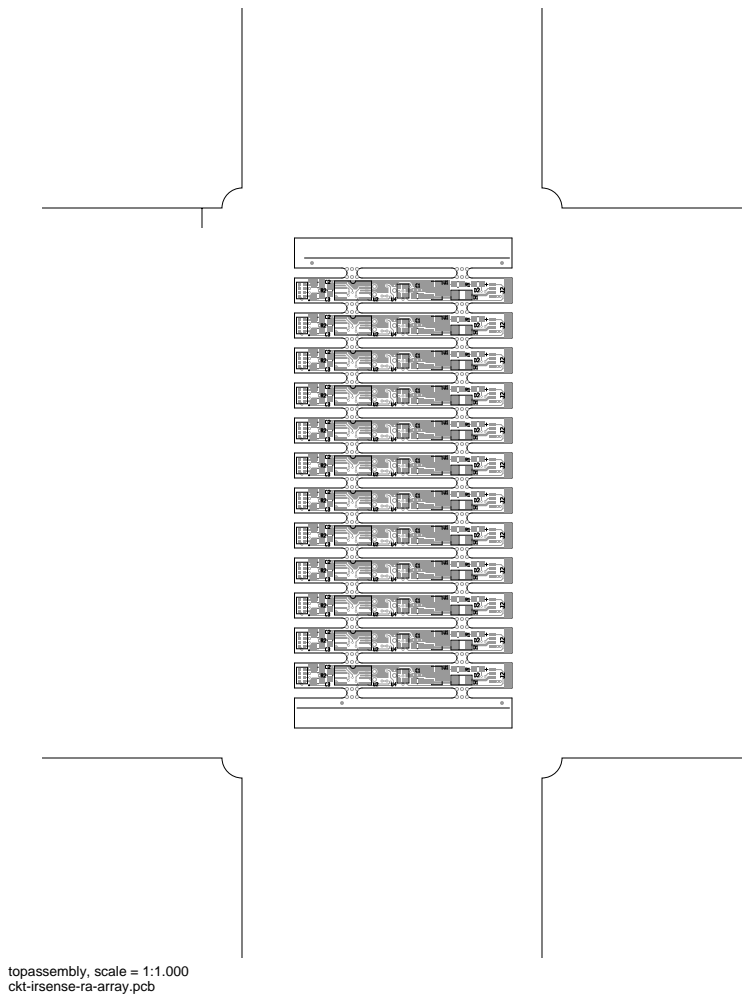
[picture p285: page 13]
topassembly, scale = 1:1.000

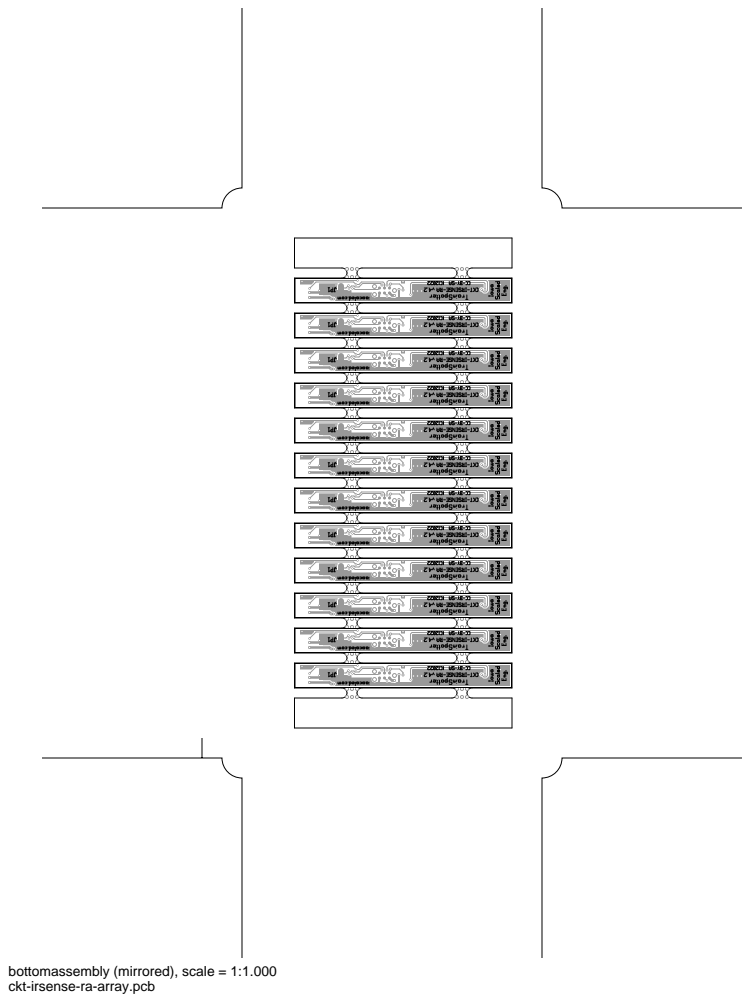
[picture p286: page 14]

bottomassembly (mirrored), scale = 1:1.000

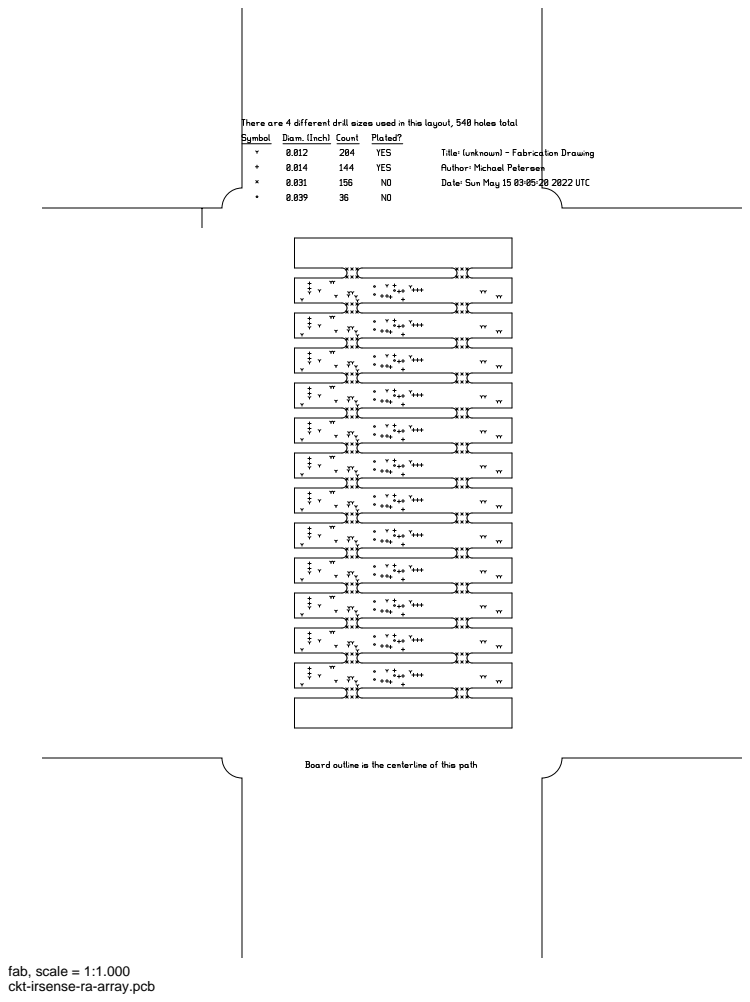
[picture p287: page 15]
fab, scale = 1:1.000
