IowaScaledEngineering/ckt-irsense/pg/ckt-irsense-panel-v4.0-96c70f0/ckt-irsense-panel-pcb.pdf

# ckt-irsense-panel.pcb

# 1. Table of Contents (This Page) Created on Thu Jul 2 15:16:04 2020

# 2. top 3. bottom 4. outline 5. plated-drill 6. unplated-drill 7. componentmask 8. soldermask 9. topsilk 10. bottomsilk 11. toppaste 12. bottompaste 13. topassembly 14. bottomassembly 15. fab

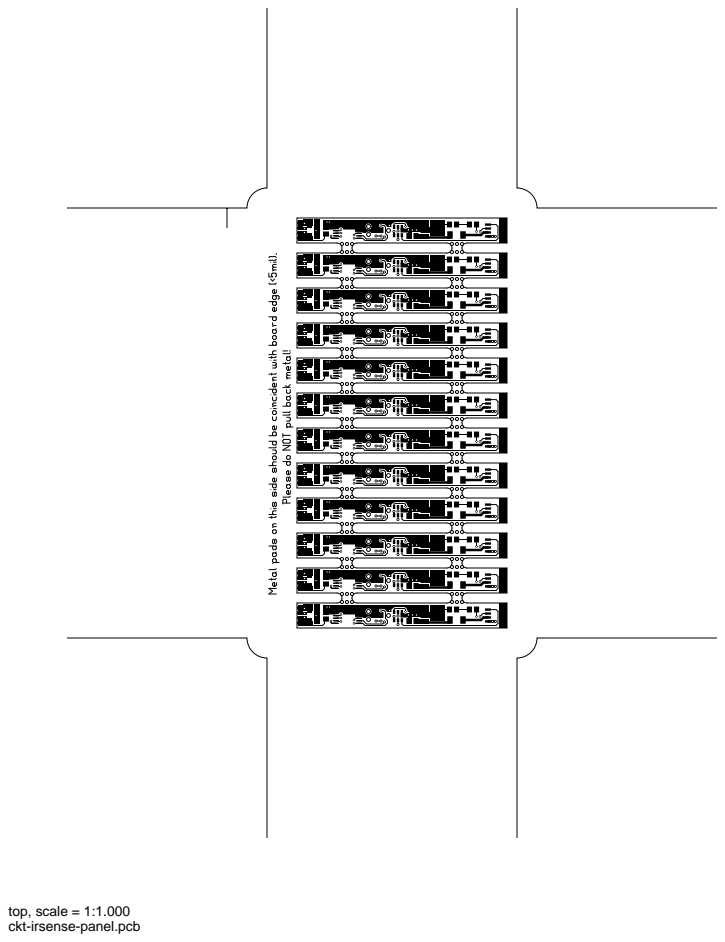
[picture p288: page 2]
top, scale = 1:1.000

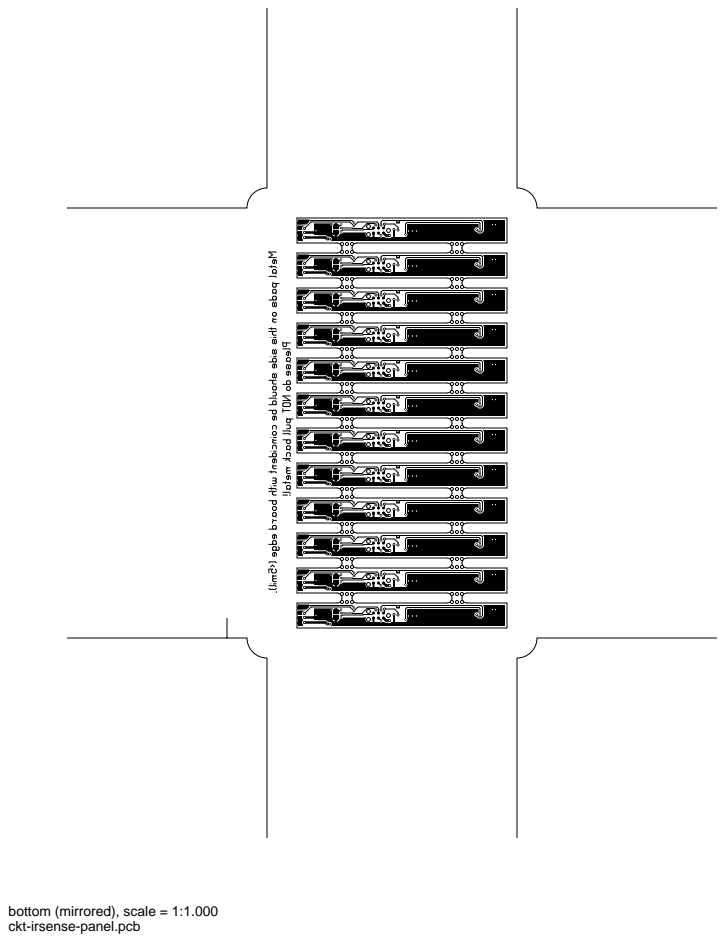
[picture p289: page 3]

bottom (mirrored), scale = 1:1.000

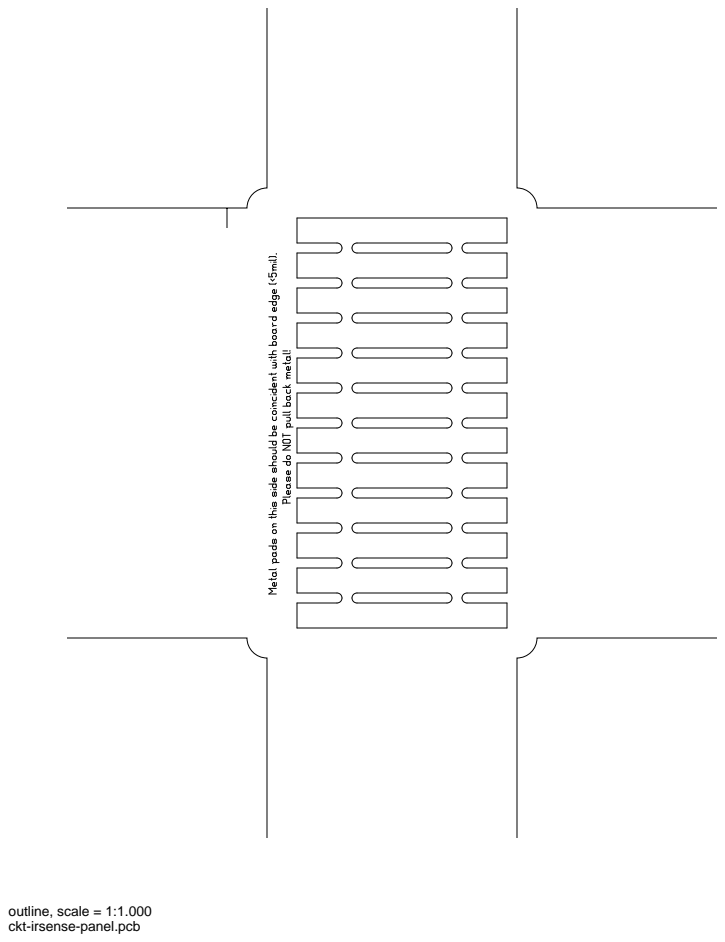
[picture p290: page 4]
outline, scale = 1:1.000

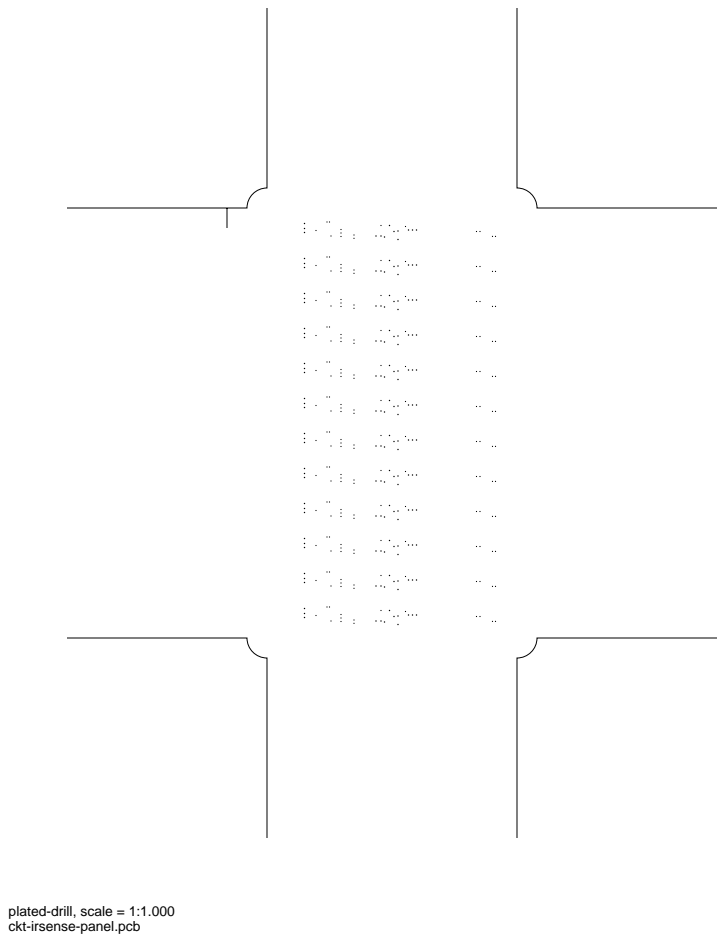
[picture p291: page 5]

plated-drill, scale = 1:1.000

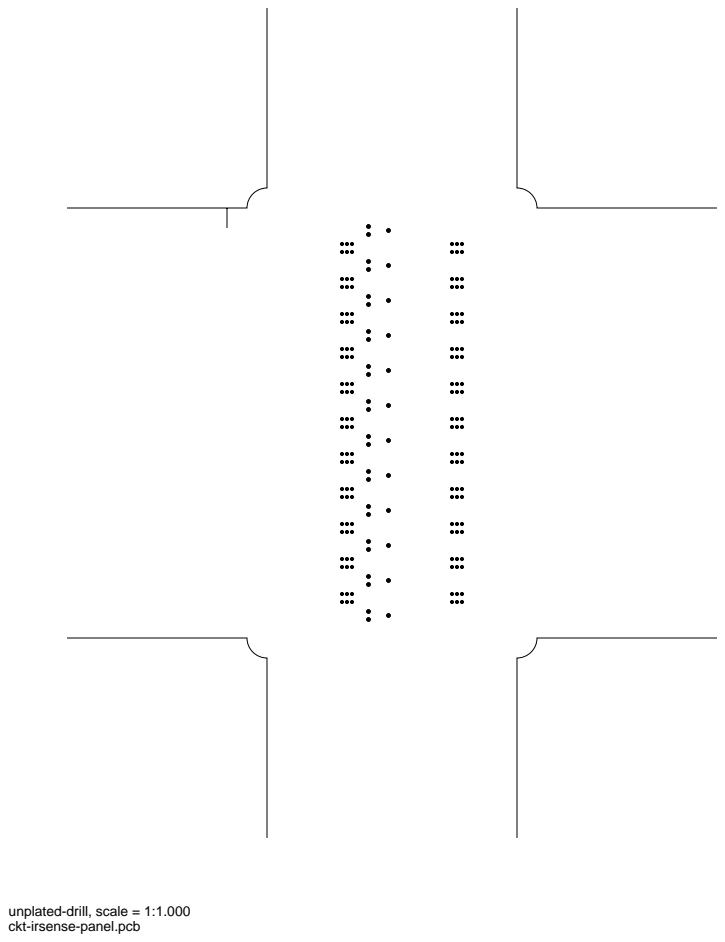
[picture p292: page 6]

unplated-drill, scale = 1:1.000

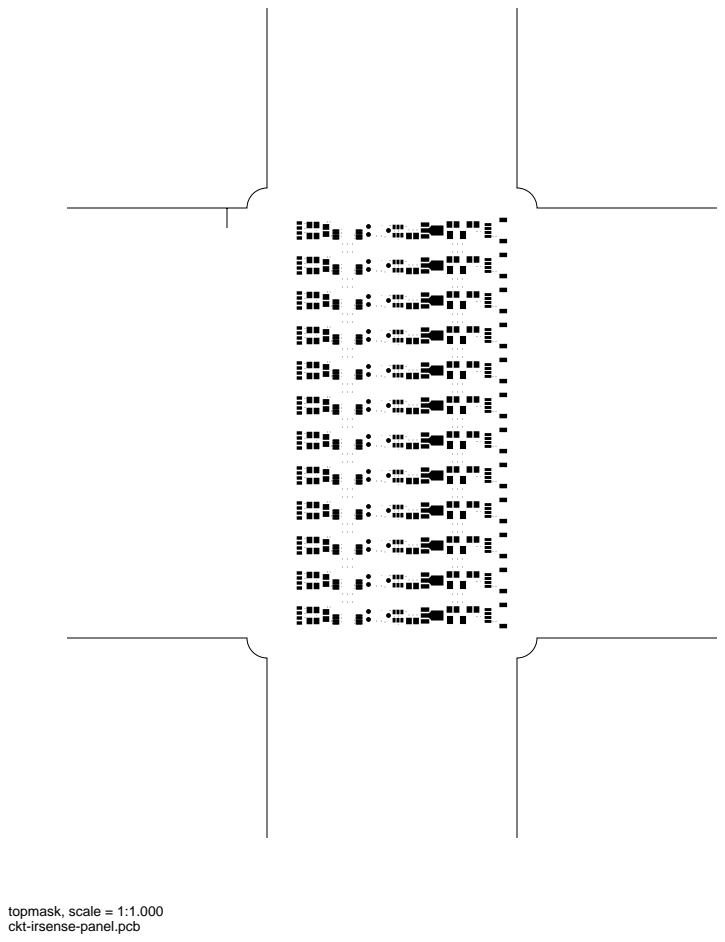
[picture p293: page 7]
topmask, scale = 1:1.000

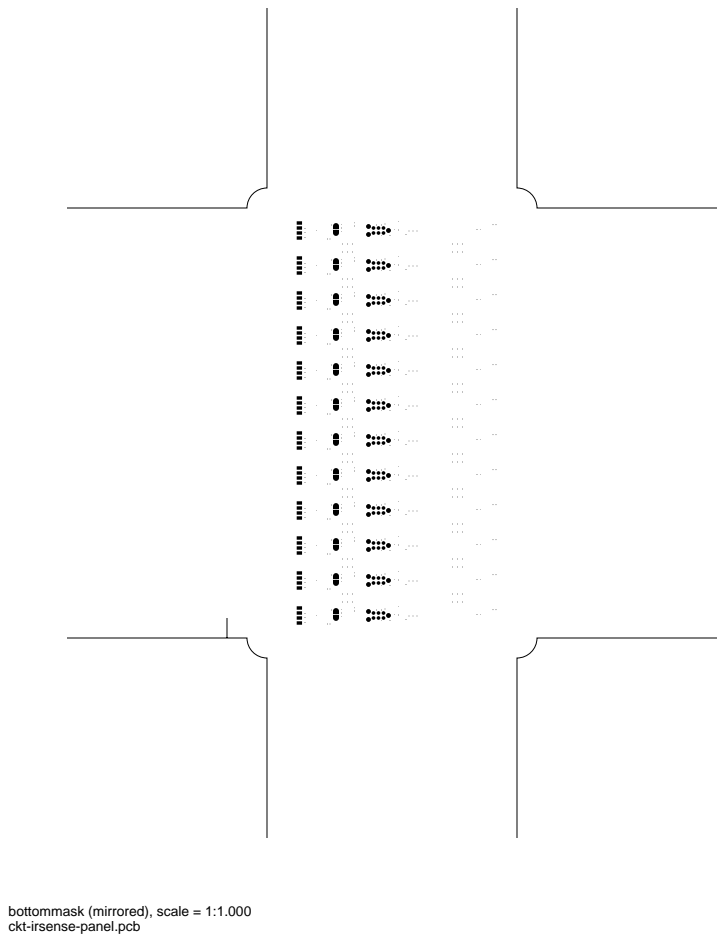
[picture p294: page 8]

bottommask (mirrored), scale = 1:1.000

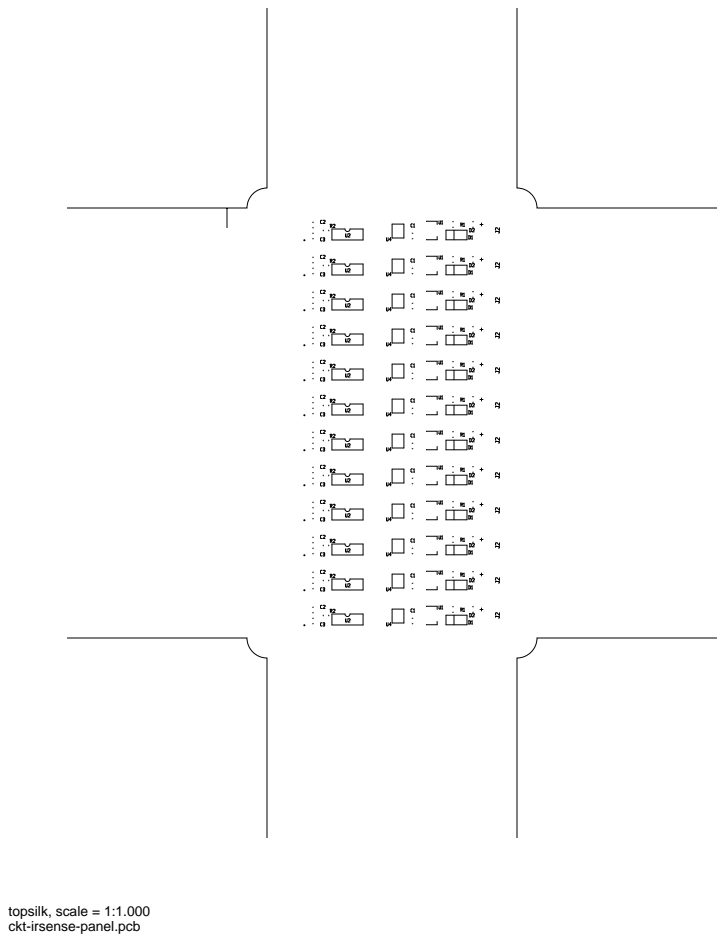
[picture p295: page 9]
topsilk, scale = 1:1.000

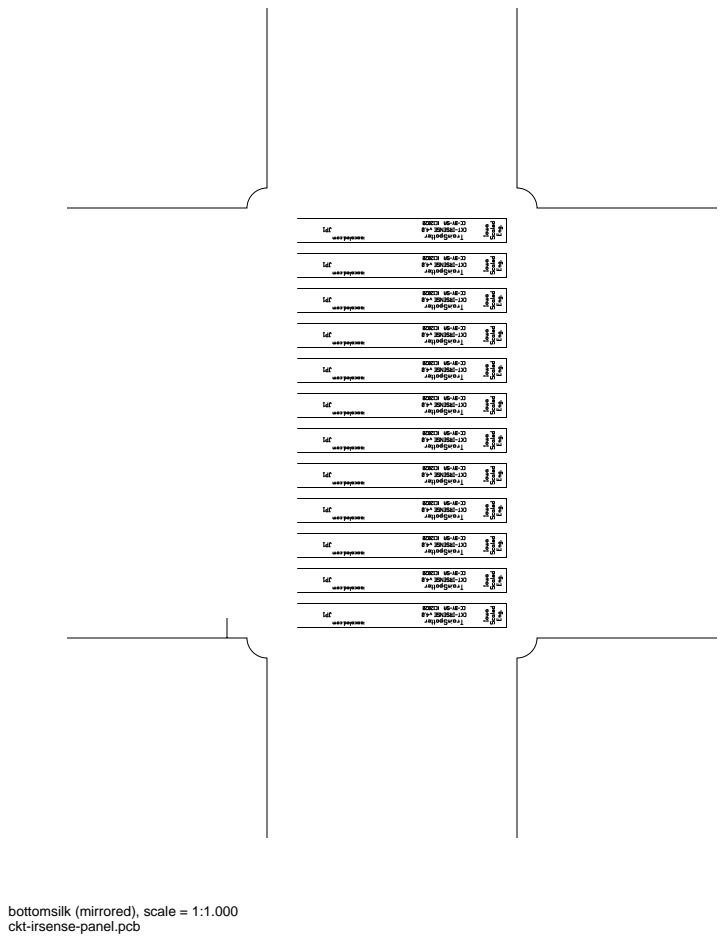
[picture p296: page 10]

bottomsilk (mirrored), scale = 1:1.000

toppaste, scale = 1:1.000 bottompaste (mirrored), scale = 1:1.000

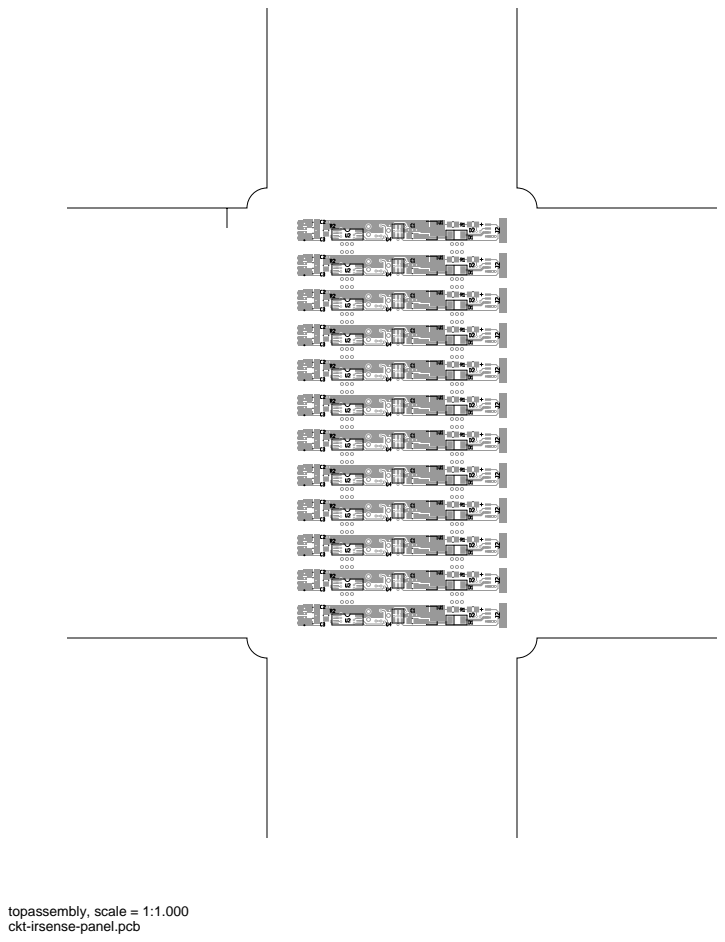
[picture p297: page 13]
topassembly, scale = 1:1.000

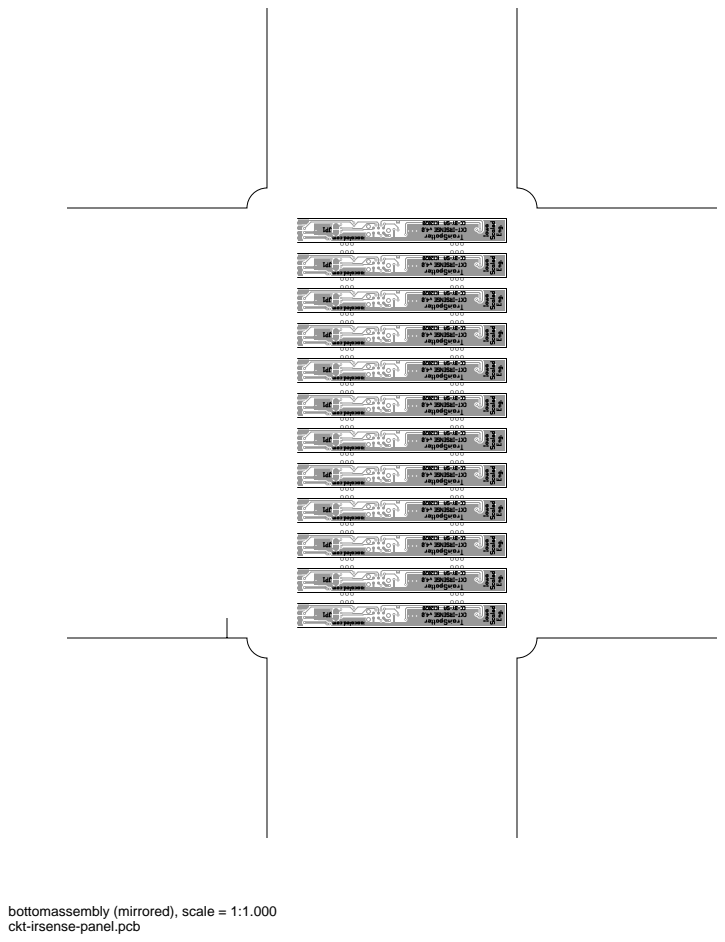
[picture p298: page 14]

bottomassembly (mirrored), scale = 1:1.000

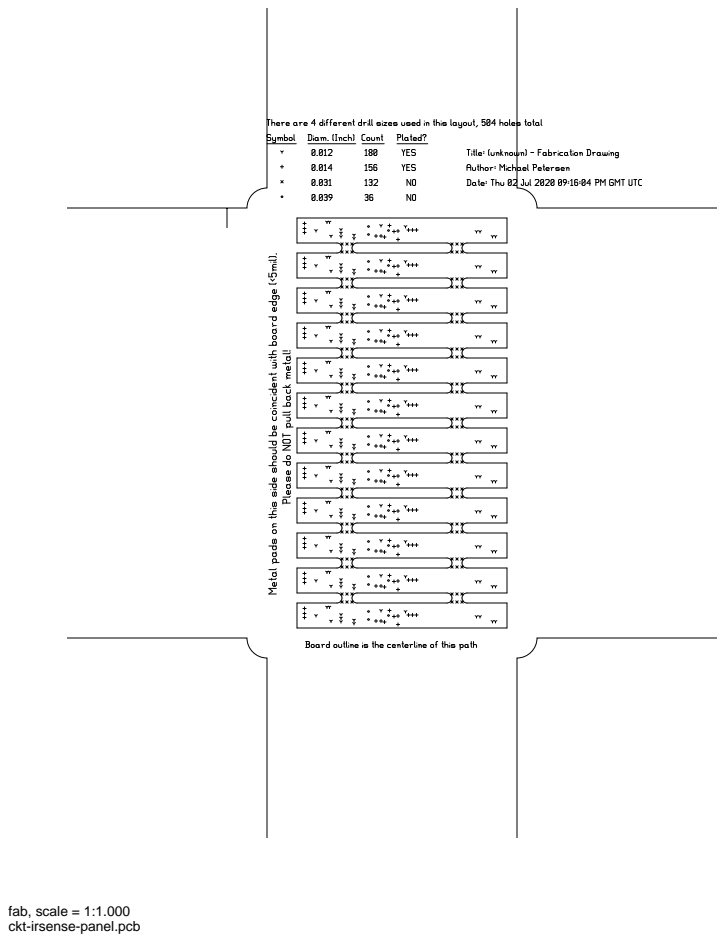
[picture p299: page 15]
fab, scale = 1:1.000
