IowaScaledEngineering/ckt-irsense/pg/ckt-irsense-panel-v4.1-fd210cc/ckt-irsense-panel-pcb.pdf

# ckt-irsense-panel.pcb

# 1. Table of Contents (This Page) Created on Wed Aug 19 20:40:23 2020

# 2. top 3. bottom 4. outline 5. plated-drill 6. unplated-drill 7. componentmask 8. soldermask 9. topsilk 10. bottomsilk 11. toppaste 12. bottompaste 13. topassembly 14. bottomassembly 15. fab

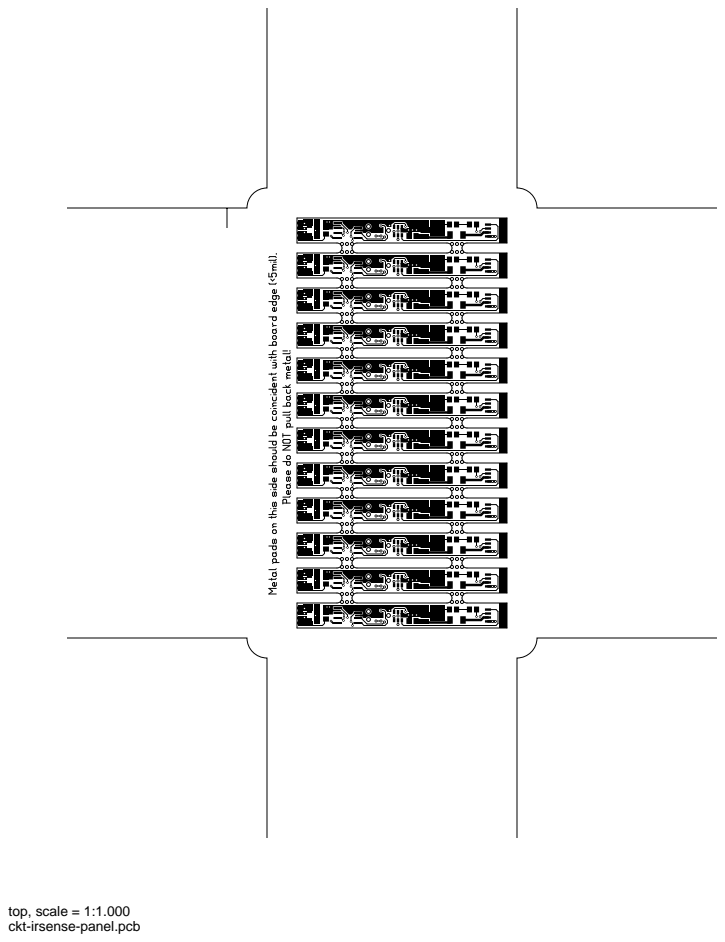
[picture p300: page 2]
top, scale = 1:1.000

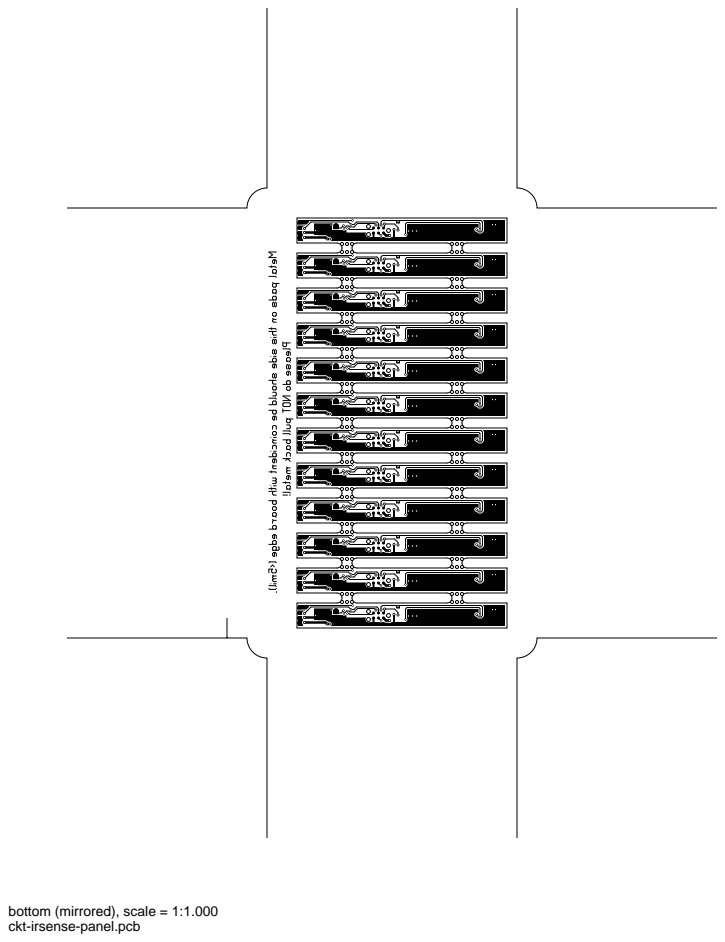
[picture p301: page 3]

bottom (mirrored), scale = 1:1.000

outline, scale = 1:1.000

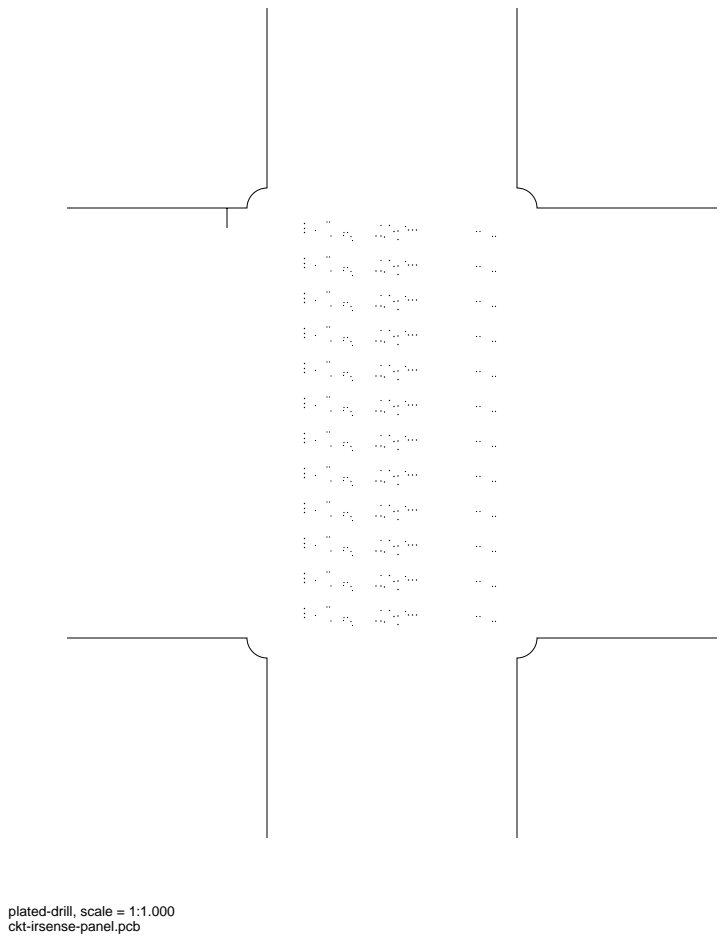
[picture p302: page 5]

plated-drill, scale = 1:1.000


unplated-drill, scale = 1:1.000

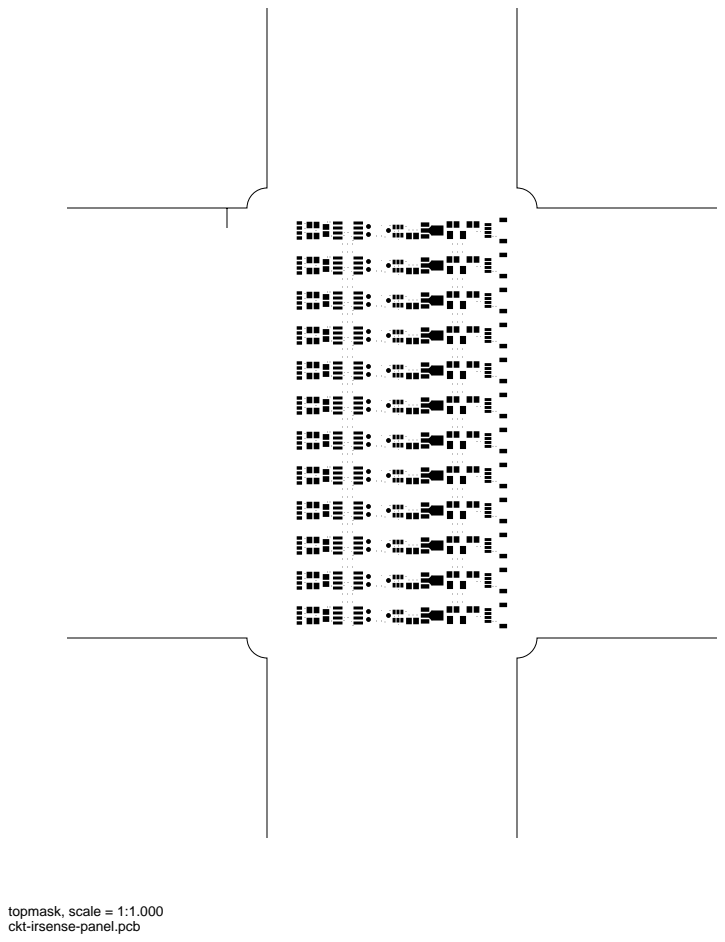
[picture p303: page 7]
topmask, scale = 1:1.000

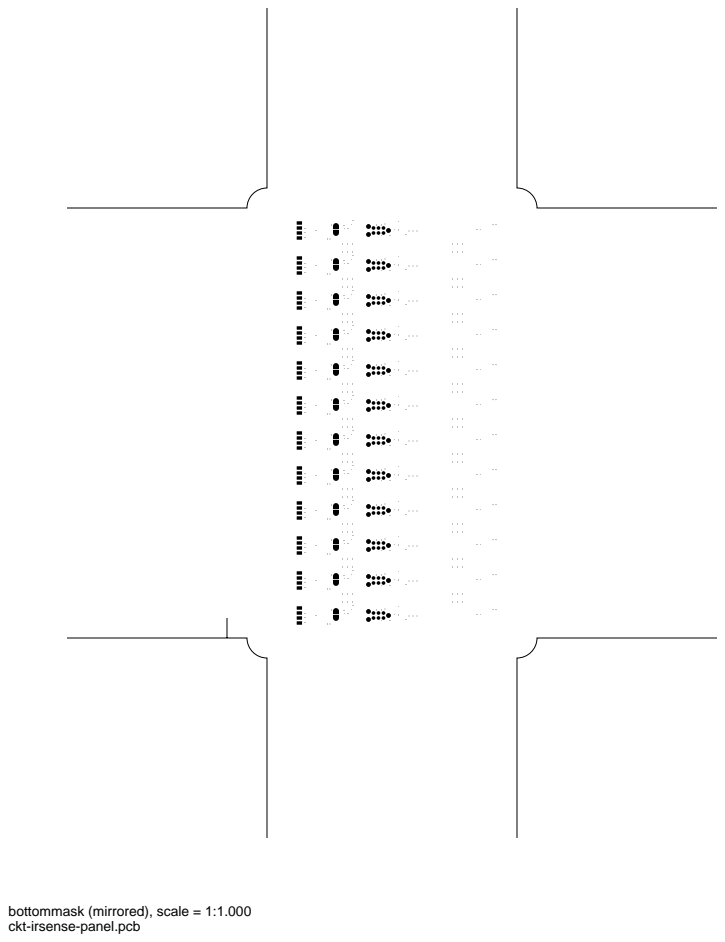
[picture p304: page 8]

bottommask (mirrored), scale = 1:1.000

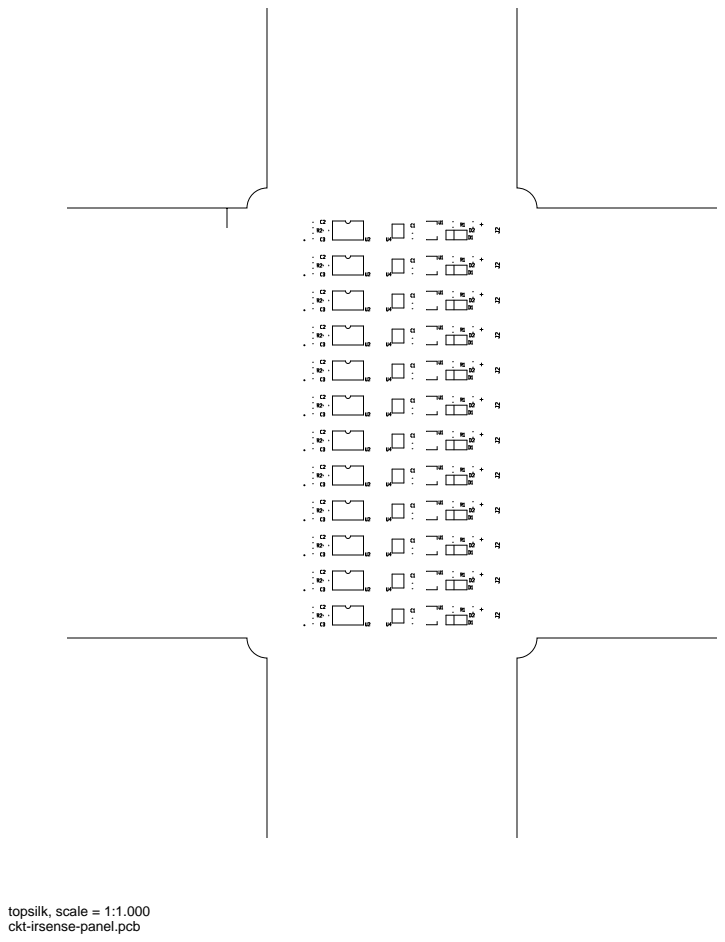
[picture p305: page 9]
topsilk, scale = 1:1.000

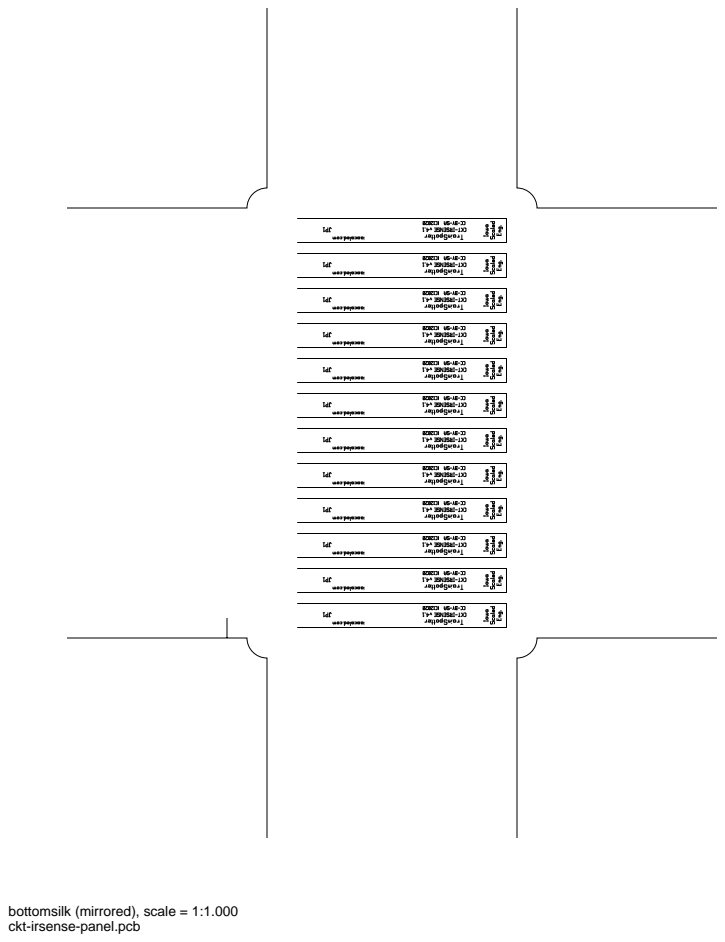
[picture p306: page 10]

bottomsilk (mirrored), scale = 1:1.000

toppaste, scale = 1:1.000 bottompaste (mirrored), scale = 1:1.000

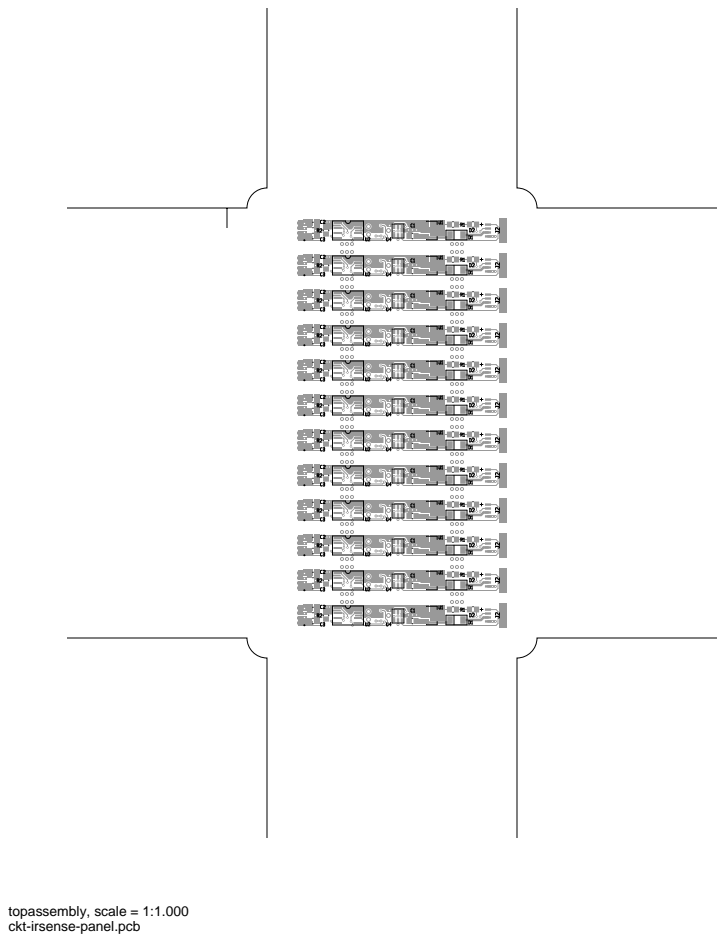
[picture p307: page 13]
topassembly, scale = 1:1.000

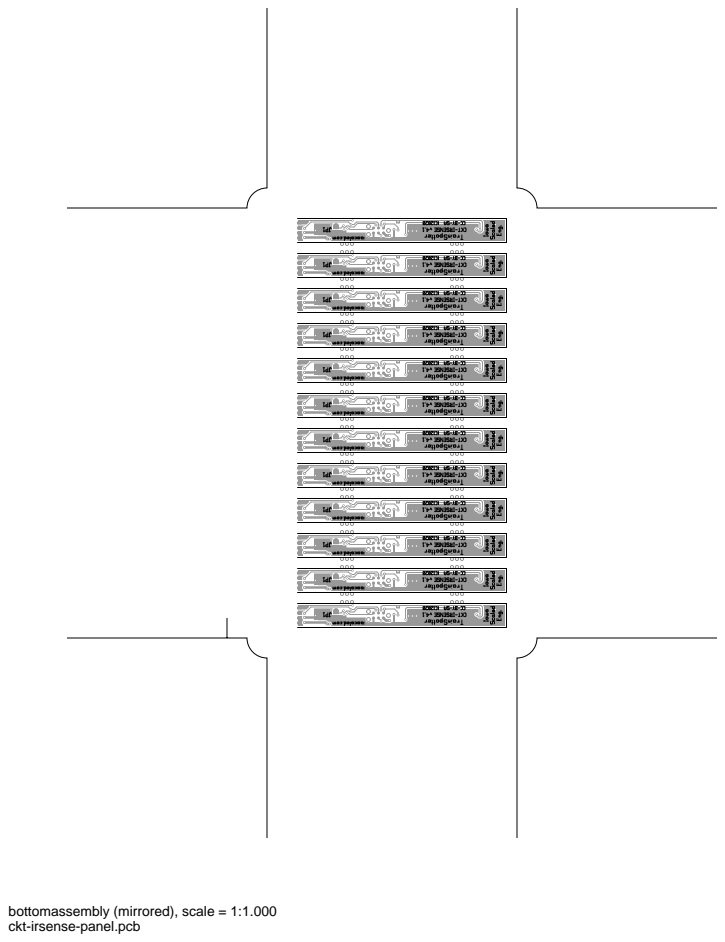
[picture p308: page 14]

bottomassembly (mirrored), scale = 1:1.000

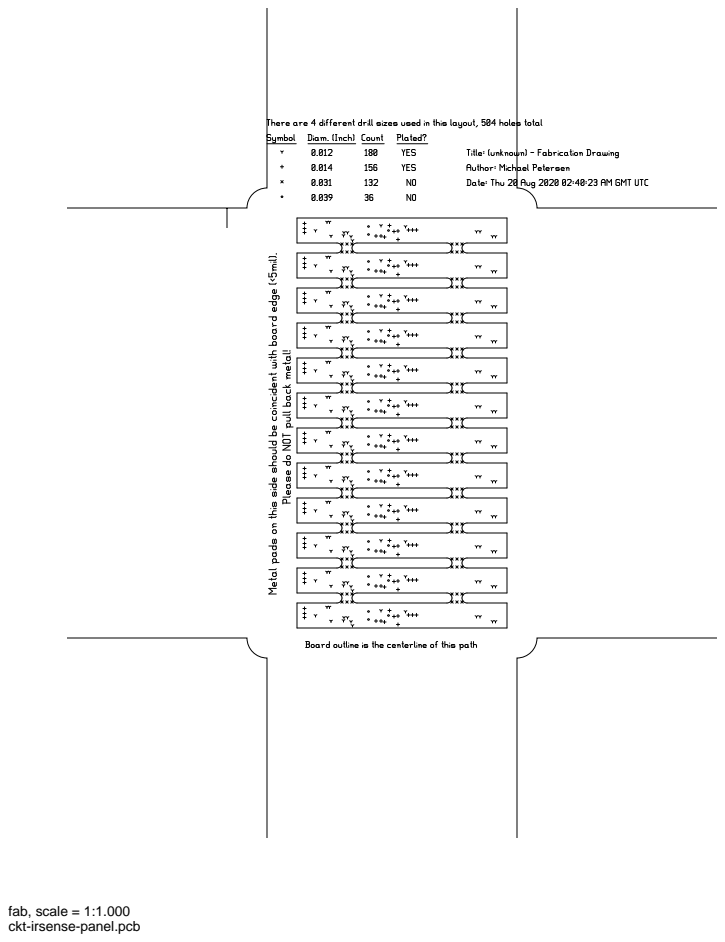
[picture p309: page 15]
fab, scale = 1:1.000
