IowaScaledEngineering/ckt-irsense/pg/ckt-irsense-base-v1.2-9fe6ce4/ckt-irsense-base-pcb.pdf

# ckt-irsense-base.pcb

# 1. Table of Contents (This Page) Created on Thu Apr 26 20:04:58 2018

# 2. top 3. bottom 4. outline 5. plated-drill 6. unplated-drill 7. componentmask 8. soldermask 9. topsilk 10. bottomsilk 11. toppaste 12. topassembly 13. bottomassembly 14. fab

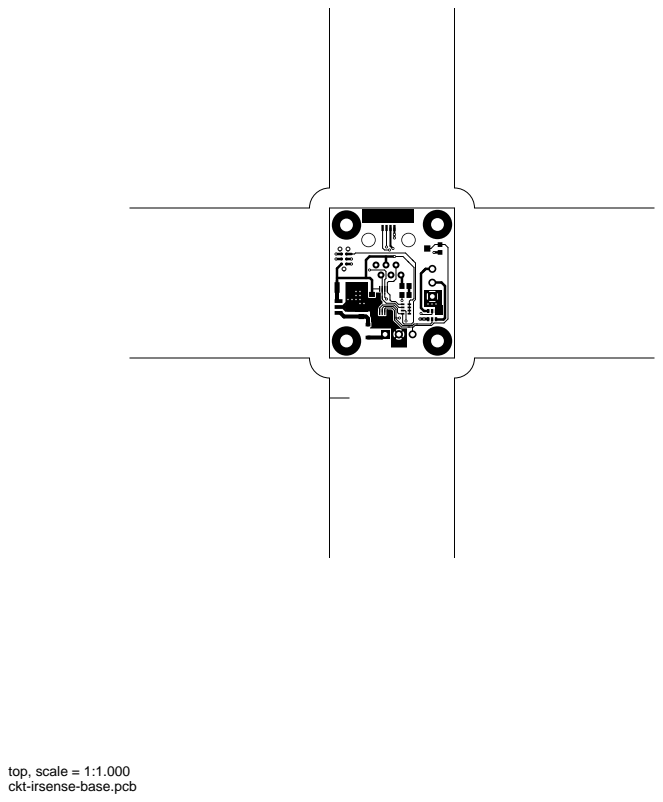
[picture p310: page 2]
top, scale = 1:1.000

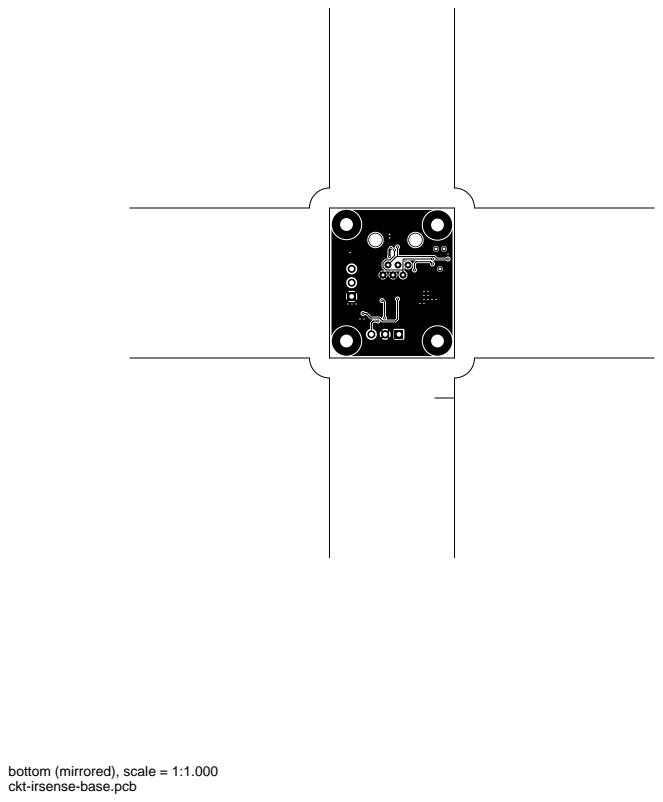
[picture p311: page 3]

bottom (mirrored), scale = 1:1.000

outline, scale = 1:1.000

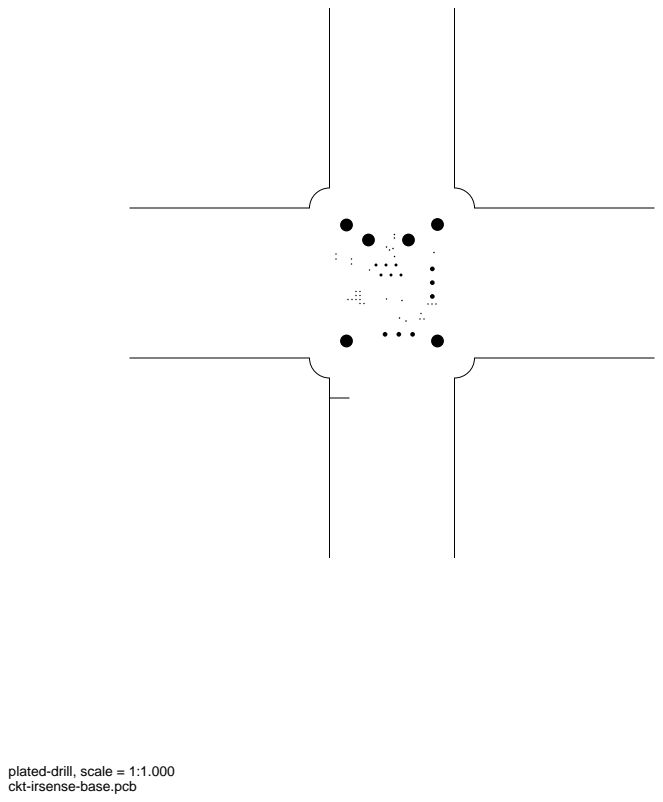
[picture p312: page 5]

plated-drill, scale = 1:1.000

unplated-drill, scale = 1:1.000

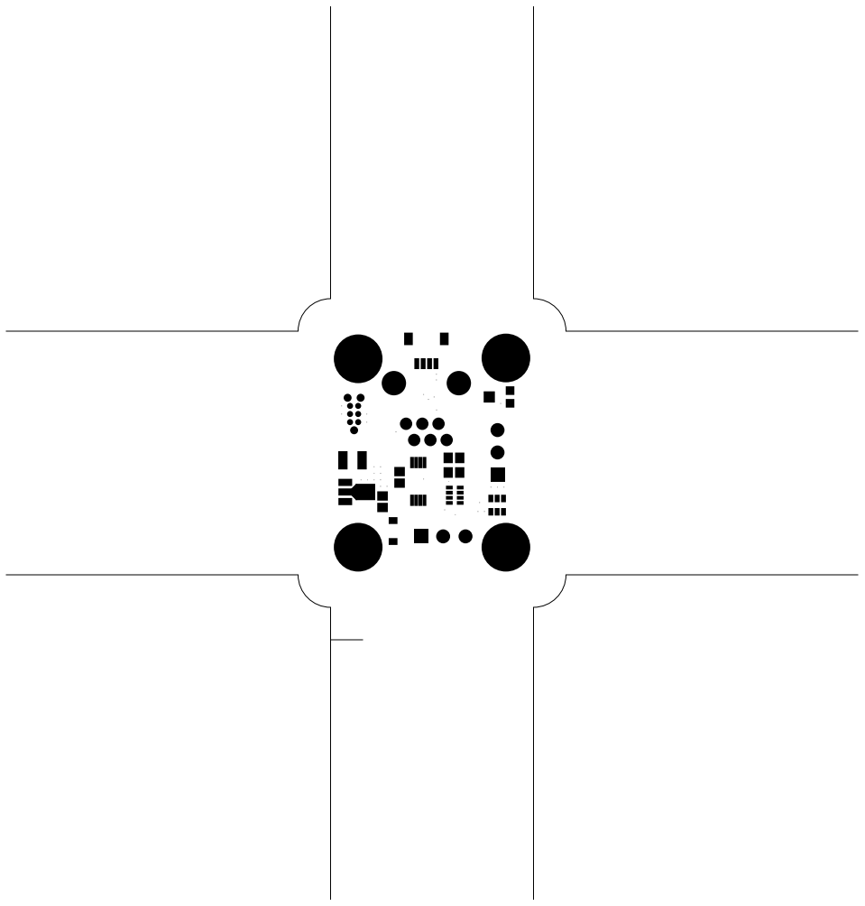
[picture p313: figure]

topmask, scale = 1:1.000

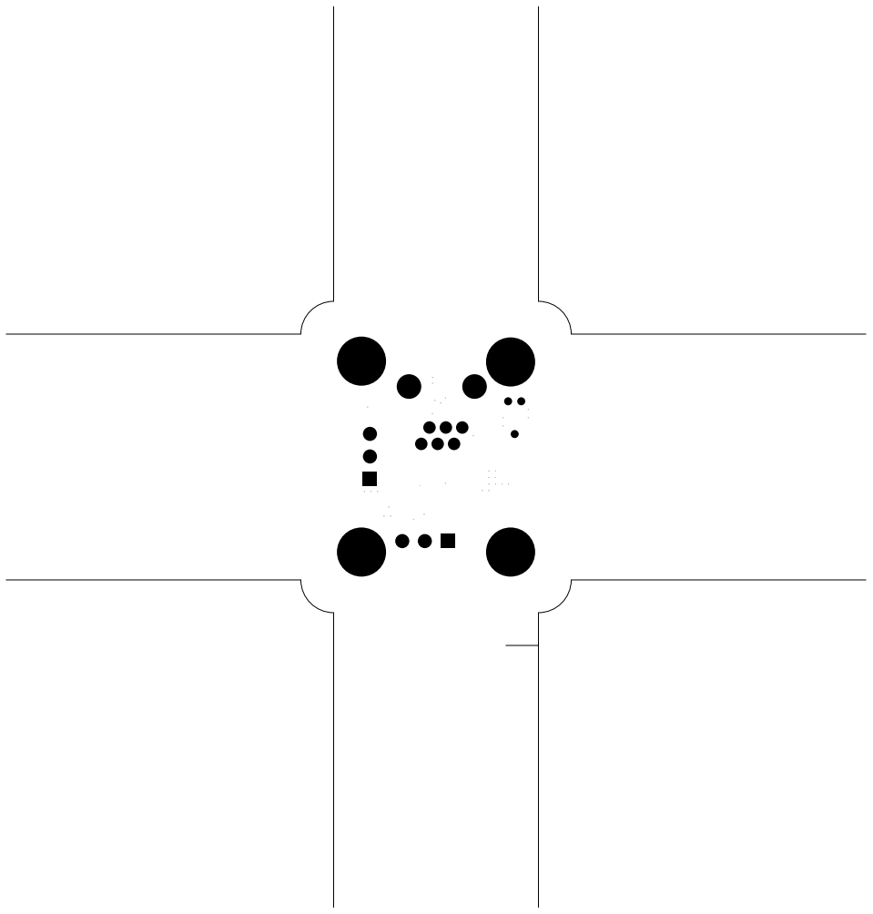
[picture p314: figure]

bottommask (mirrored), scale = 1:1.000

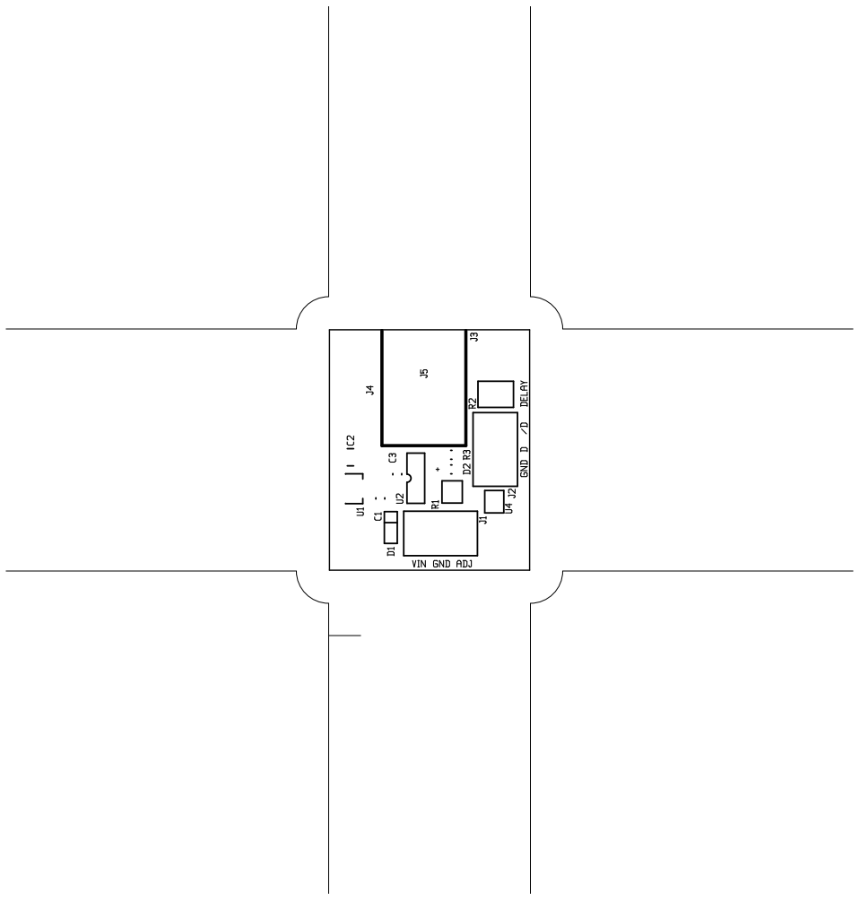
[picture p315: figure]

topsilk, scale = 1:1.000

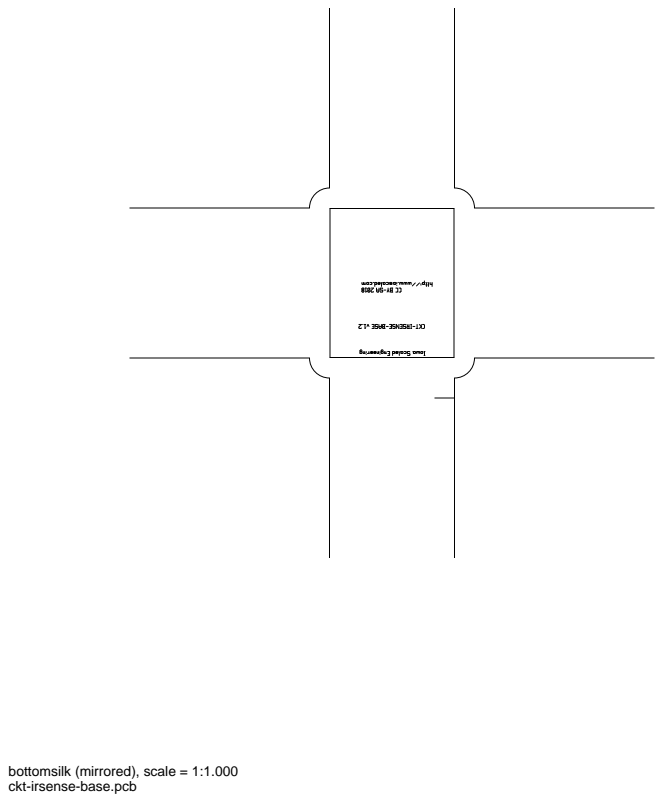
[picture p316: page 10]

bottomsilk (mirrored), scale = 1:1.000

toppaste, scale = 1:1.000

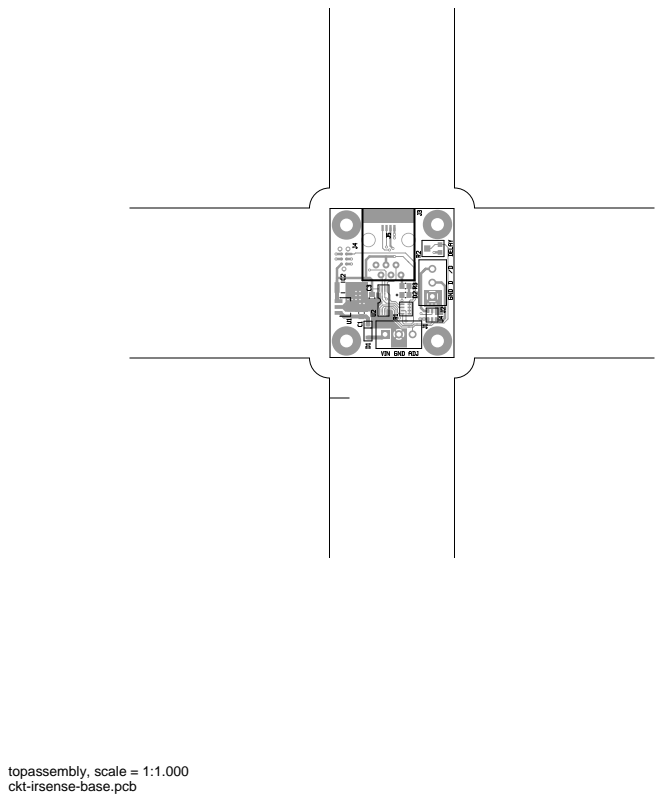
[picture p317: page 12]
topassembly, scale = 1:1.000

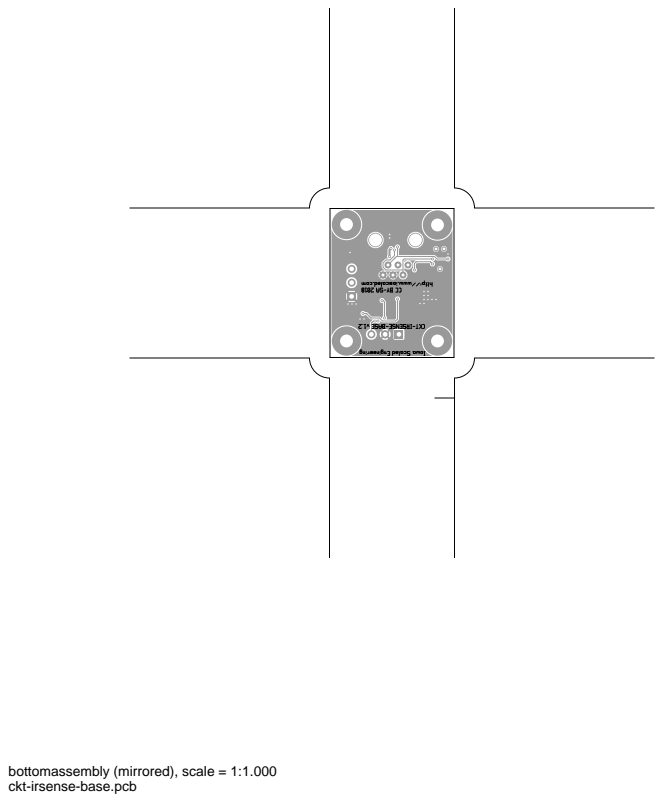
[picture p318: page 13]

bottomassembly (mirrored), scale = 1:1.000

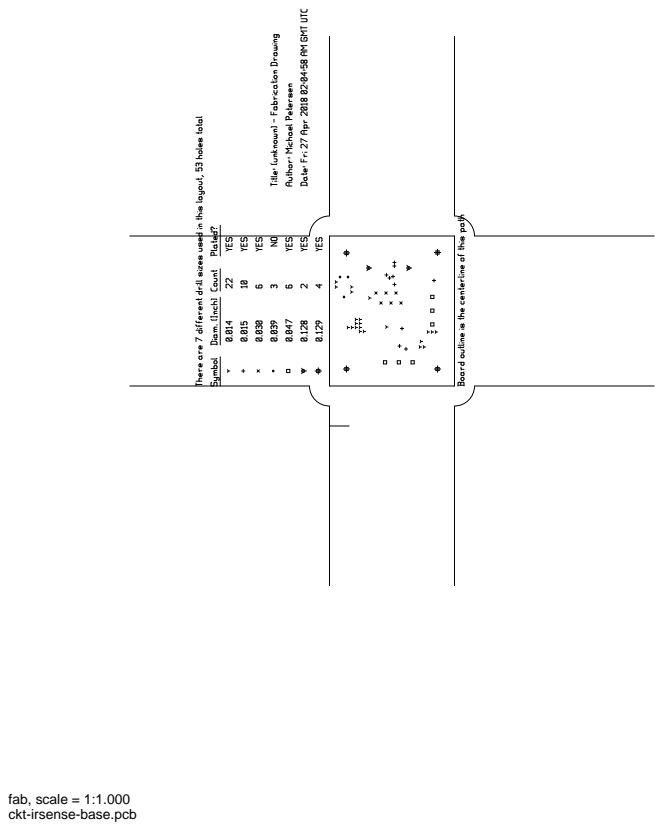
[picture p319: page 14]
fab, scale = 1:1.000
