IowaScaledEngineering/ckt-irsense/pg/ckt-irsense-base-v1.2-9fe6ce4/ckt-irsense-base.pdf

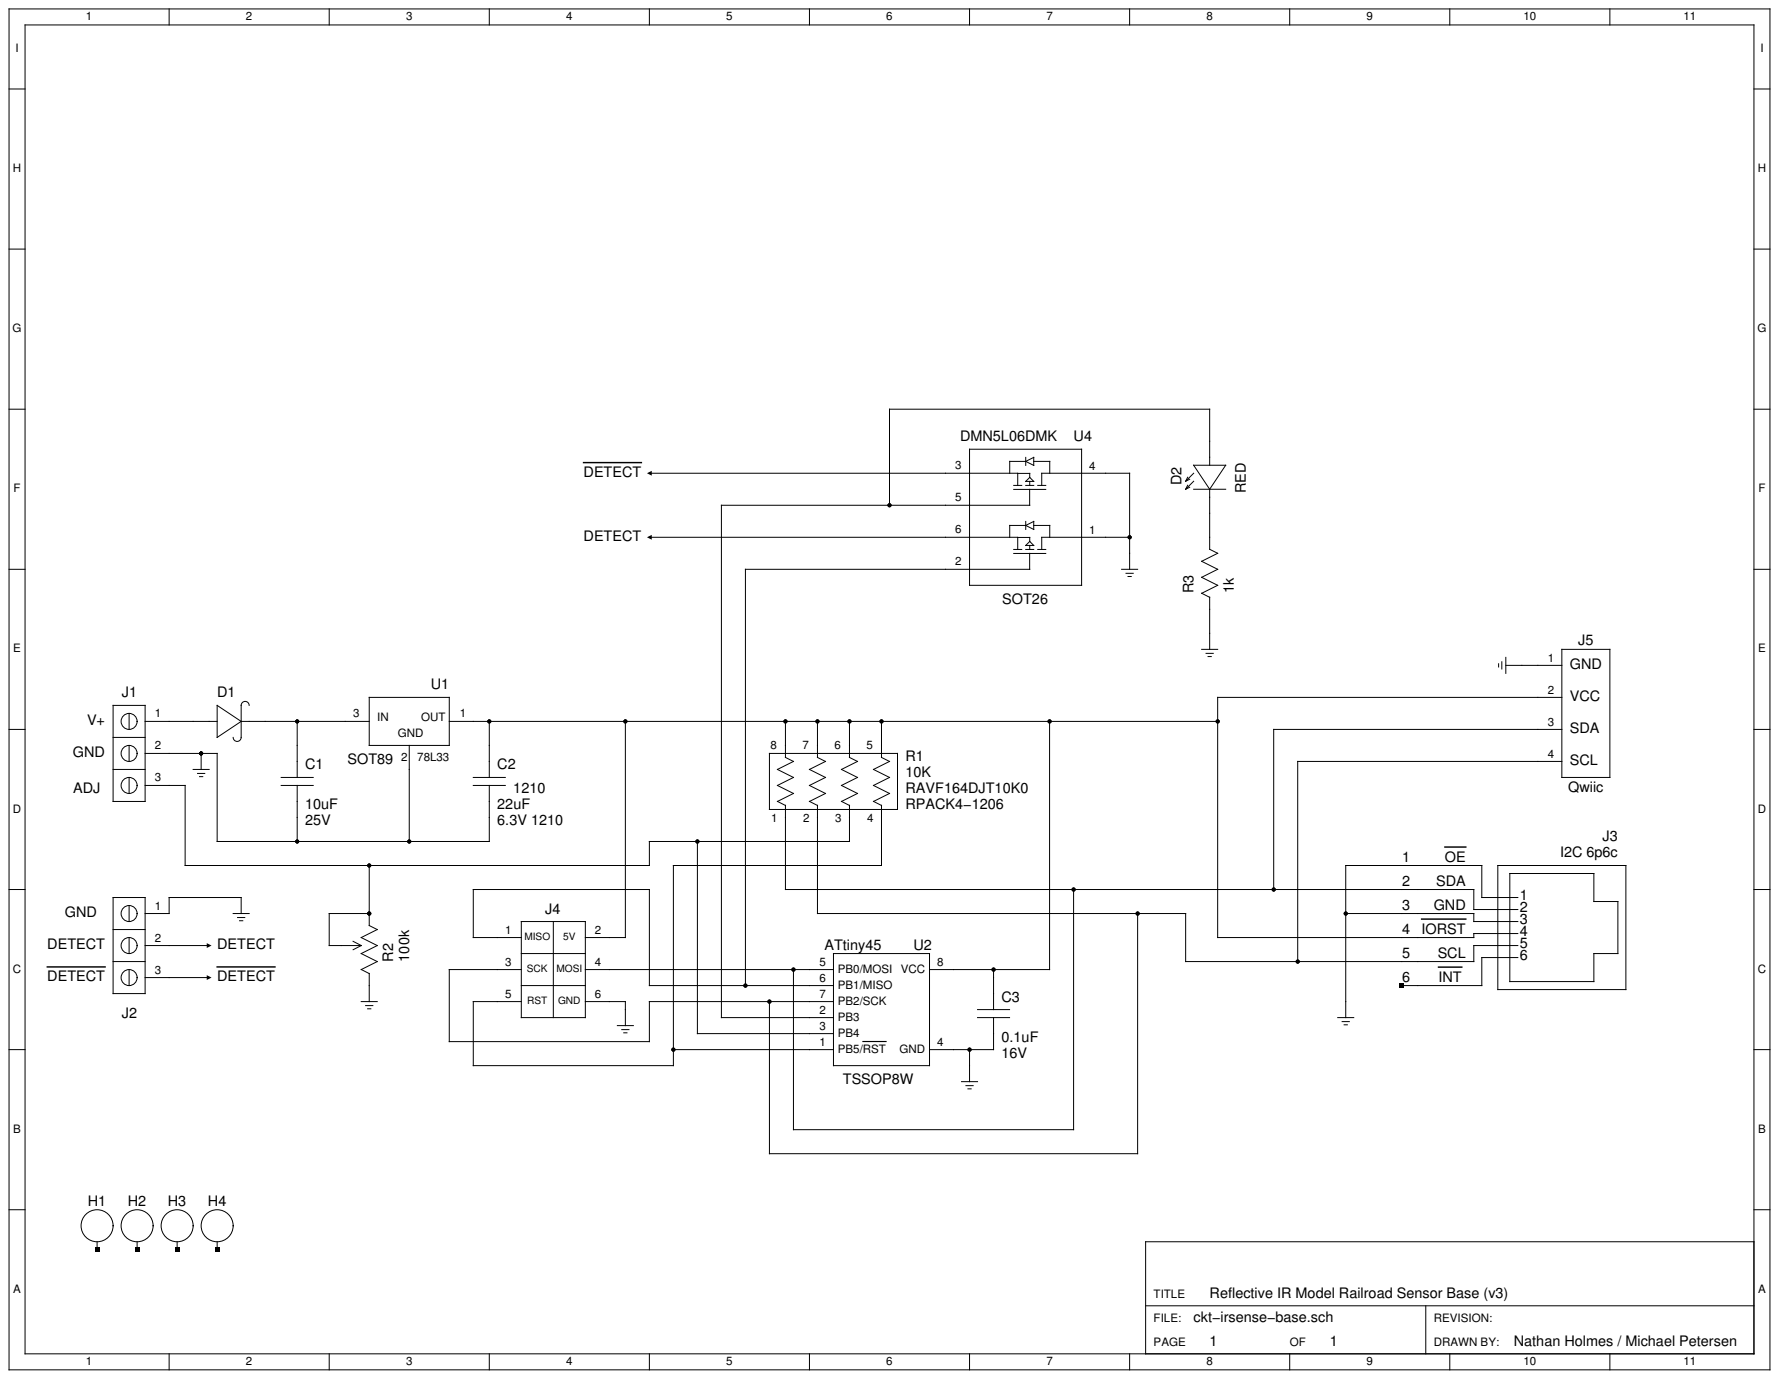
[picture p320: page 1]

Reflective IR Model Railroad Sensor Base (v3)
ckt−irsense−base.sch
