IowaScaledEngineering/ckt-irsense/pg/i2c-irsense-panel-v2.1-6e7594a/i2c-irsense-panel-pcb.pdf

# i2c-irsense-panel.pcb

# 1. Table of Contents (This Page) Created on Sun Jan 28 18:15:10 2018

# 2. top 3. bottom 4. outline 5. plated-drill 6. unplated-drill 7. componentmask 8. soldermask 9. topsilk 10. bottomsilk 11. toppaste 12. topassembly 13. bottomassembly 14. fab

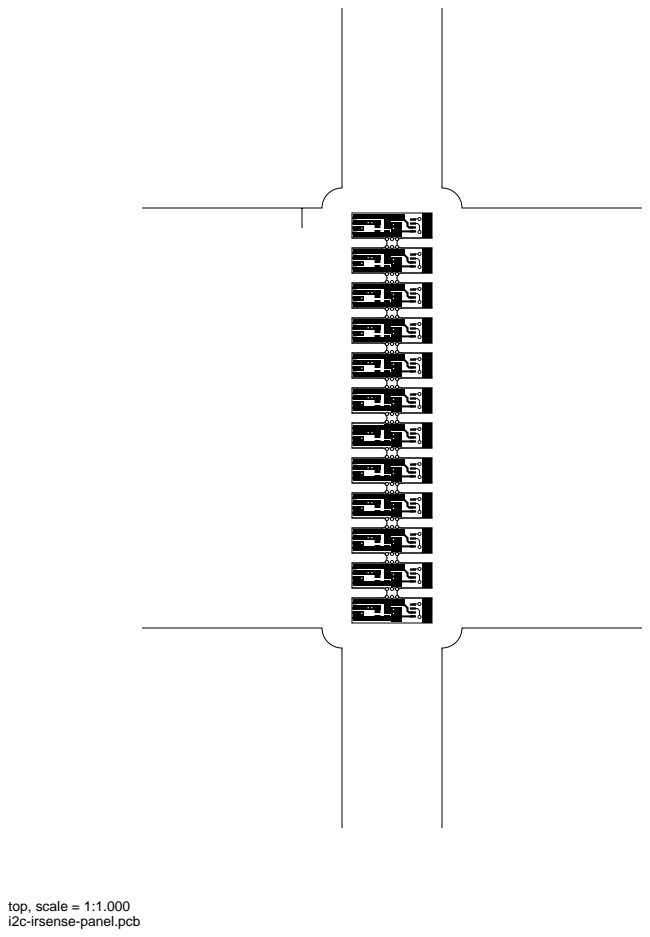
[picture p321: page 2]
top, scale = 1:1.000

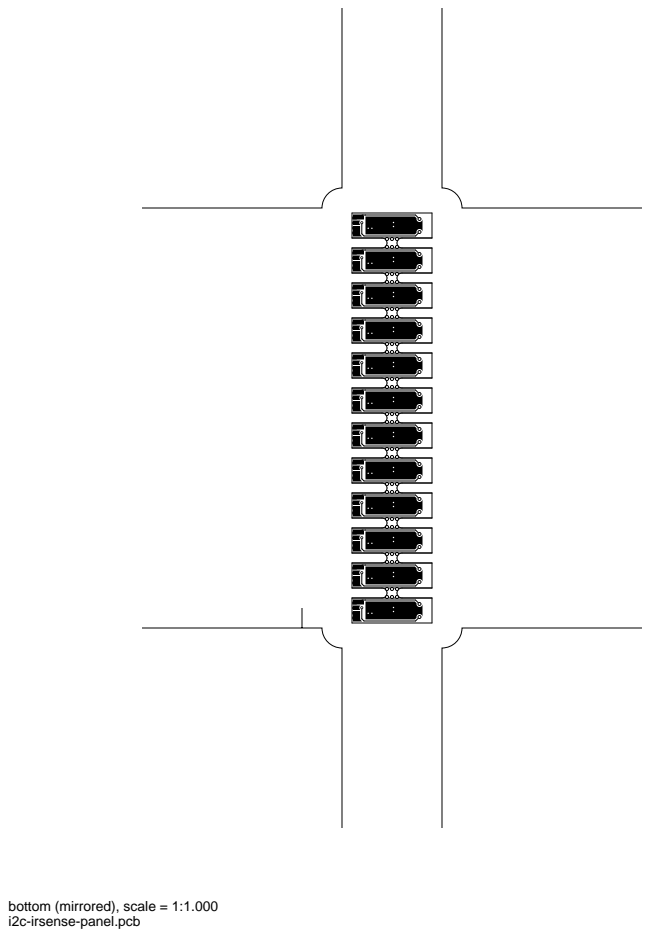
[picture p322: page 3]

bottom (mirrored), scale = 1:1.000

outline, scale = 1:1.000

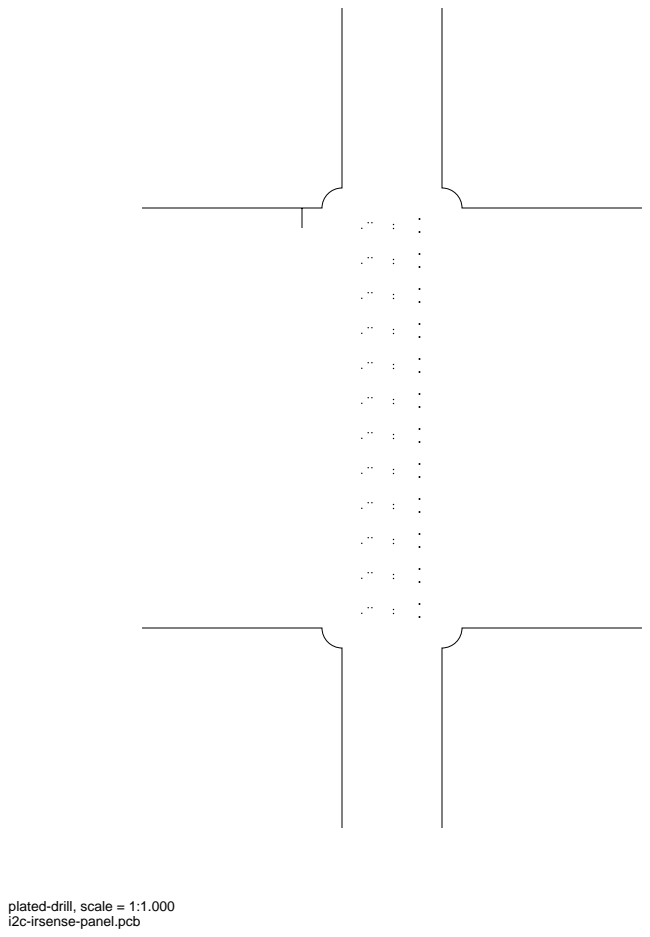
[picture p323: page 5]

plated-drill, scale = 1:1.000

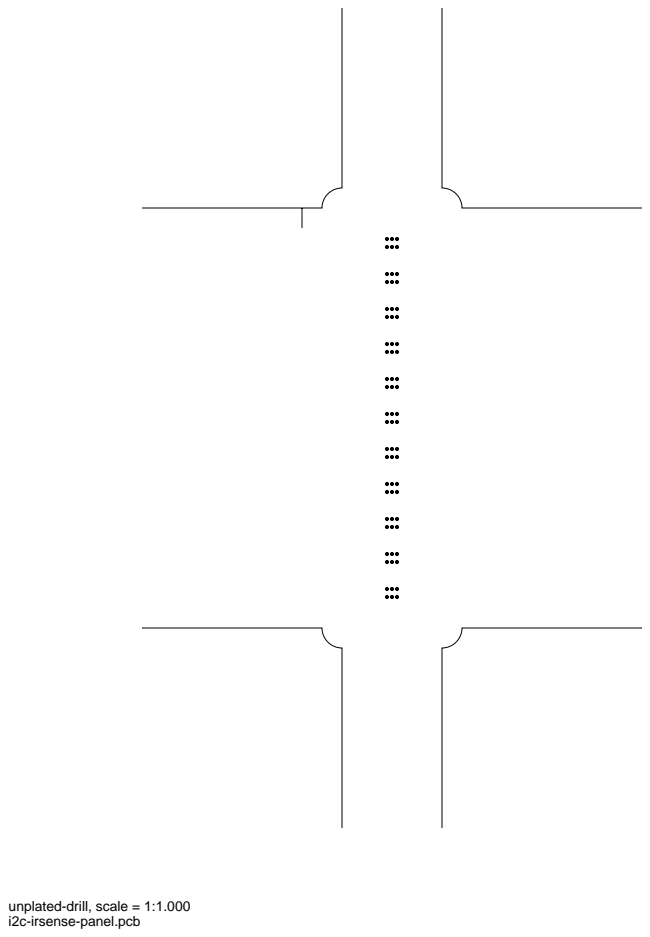
[picture p324: page 6]

unplated-drill, scale = 1:1.000

topmask, scale = 1:1.000 bottommask (mirrored), scale = 1:1.000

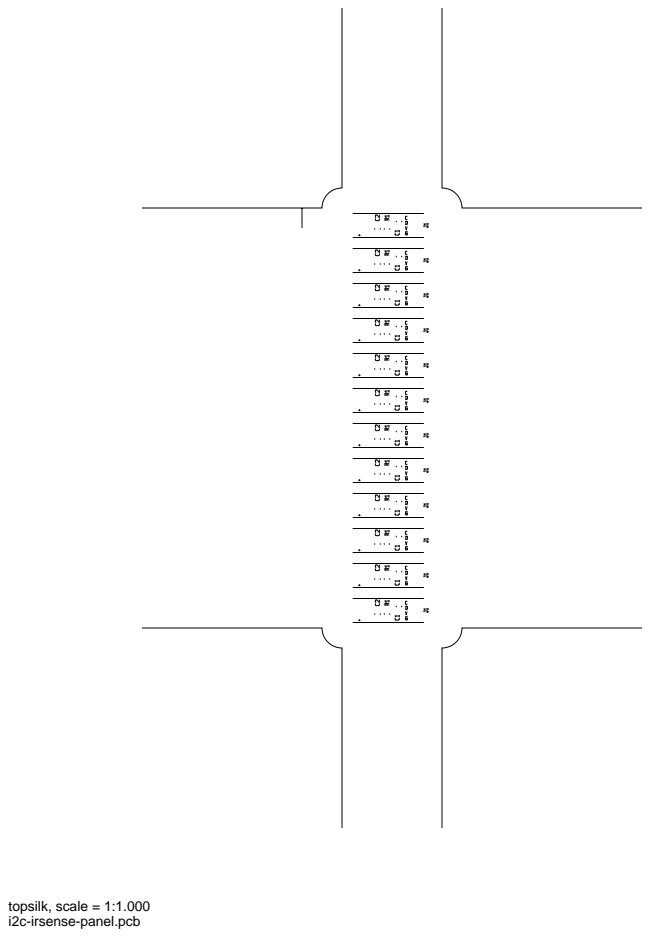
[picture p325: page 9]
topsilk, scale = 1:1.000

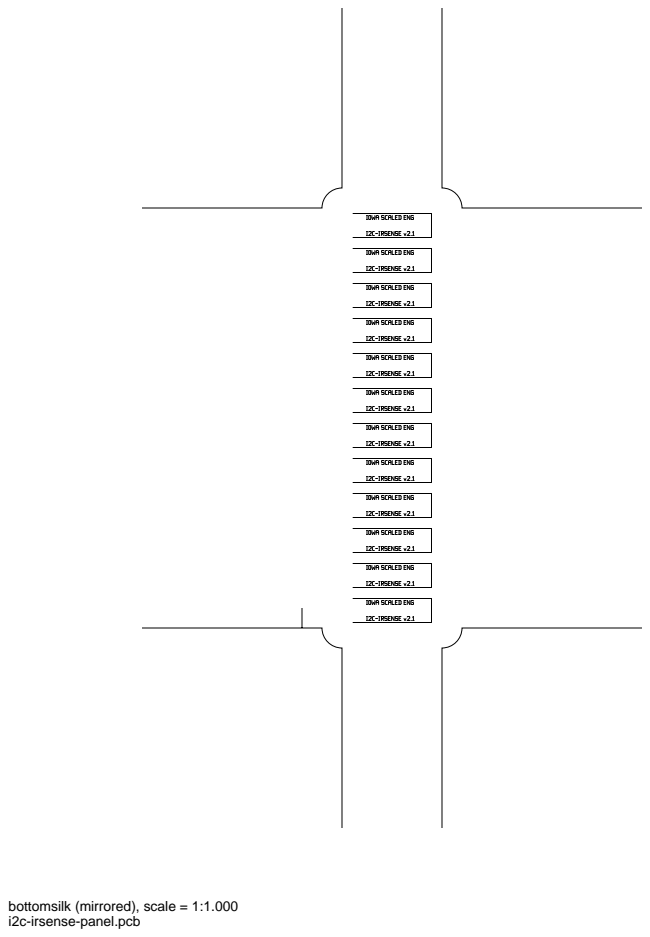
[picture p326: page 10]

bottomsilk (mirrored), scale = 1:1.000

toppaste, scale = 1:1.000

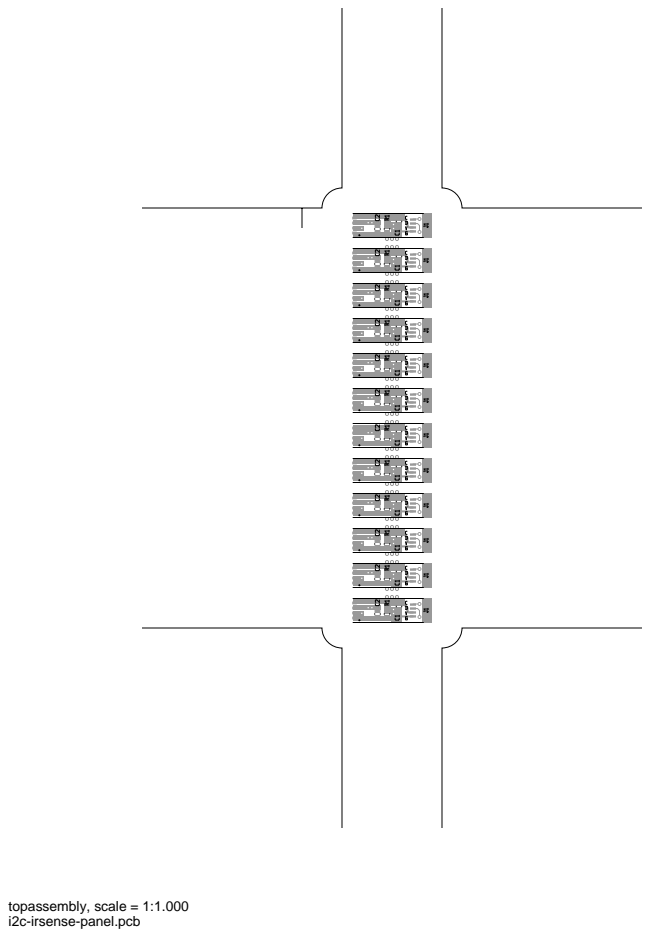
[picture p327: page 12]
topassembly, scale = 1:1.000

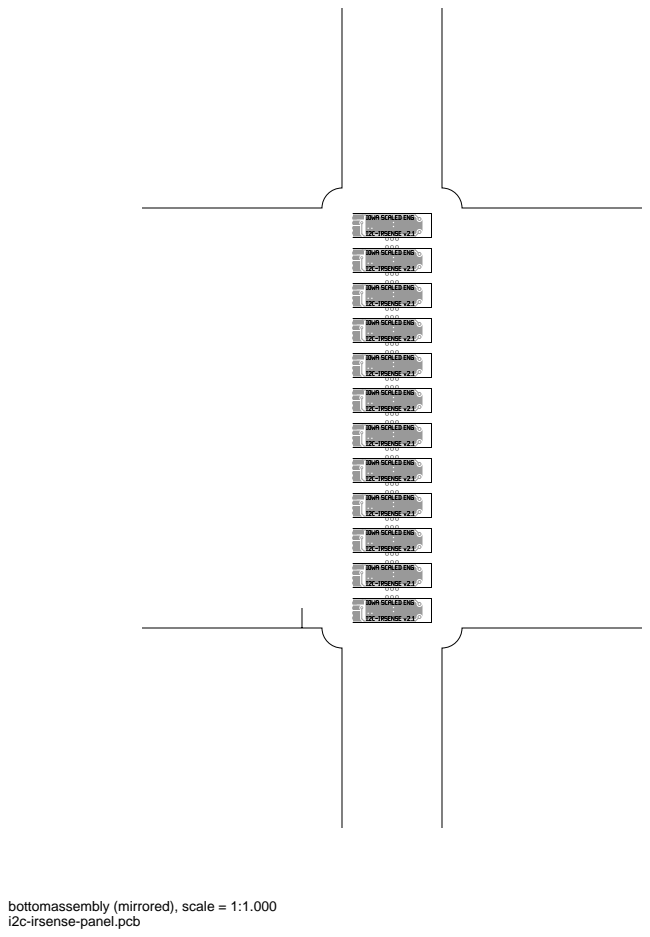
[picture p328: page 13]

bottomassembly (mirrored), scale = 1:1.000

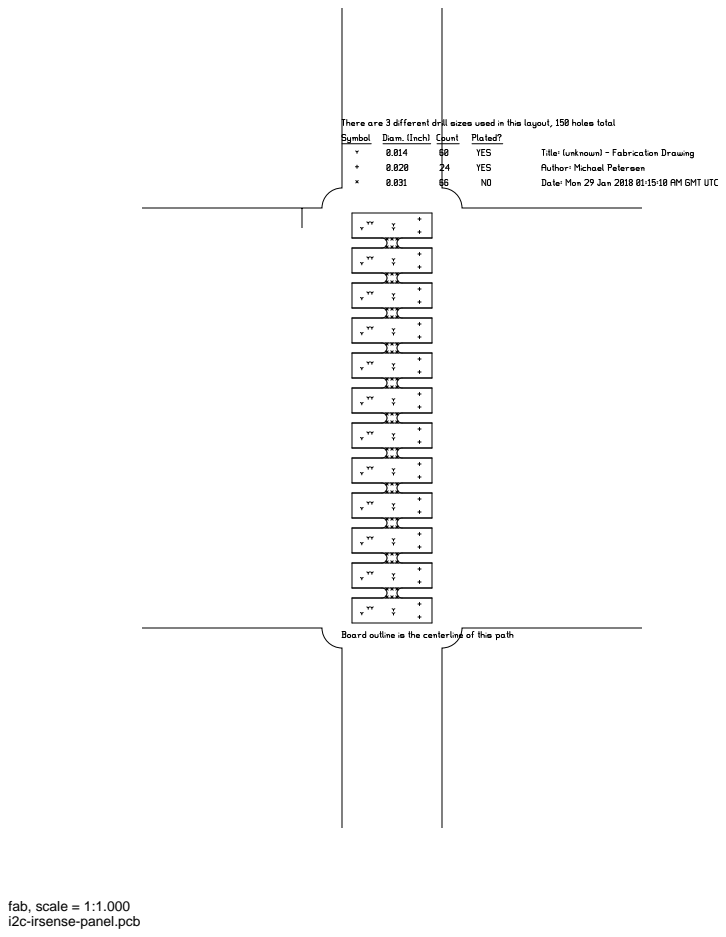
[picture p329: page 14]
fab, scale = 1:1.000
