IowaScaledEngineering/ckt-irsense/pg/i2c-irsense-panel-v2.0-50fbf34/i2c-irsense-panel-pcb.pdf

# i2c-irsense-panel.pcb

# 1. Table of Contents (This Page) Created on Tue Jan 2 19:51:44 2018

# 2. top 3. bottom 4. outline 5. plated-drill 6. unplated-drill 7. componentmask 8. soldermask 9. topsilk 10. bottomsilk 11. toppaste 12. topassembly 13. bottomassembly 14. fab

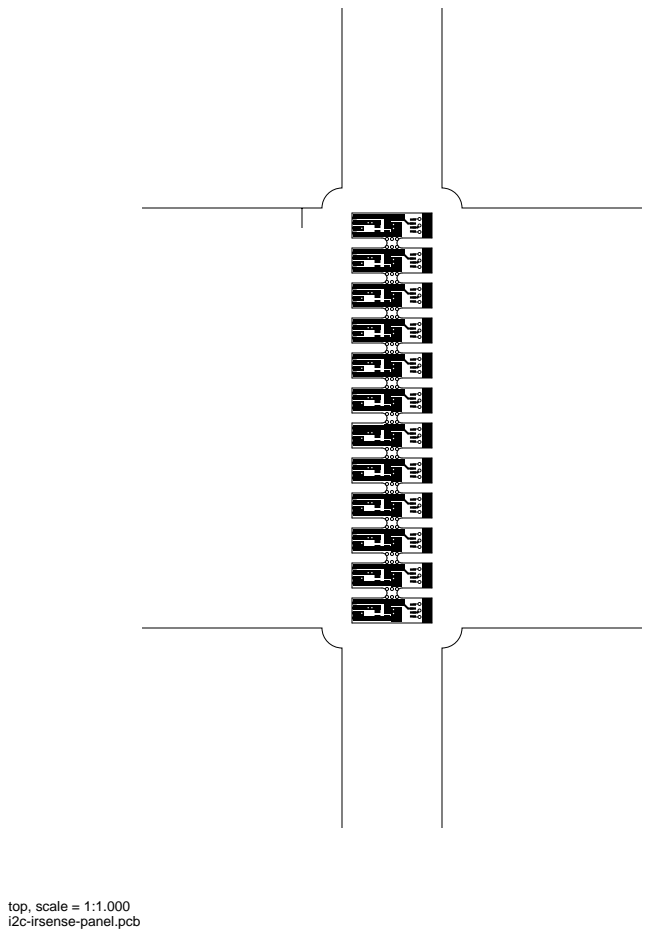
[picture p330: page 2]
top, scale = 1:1.000

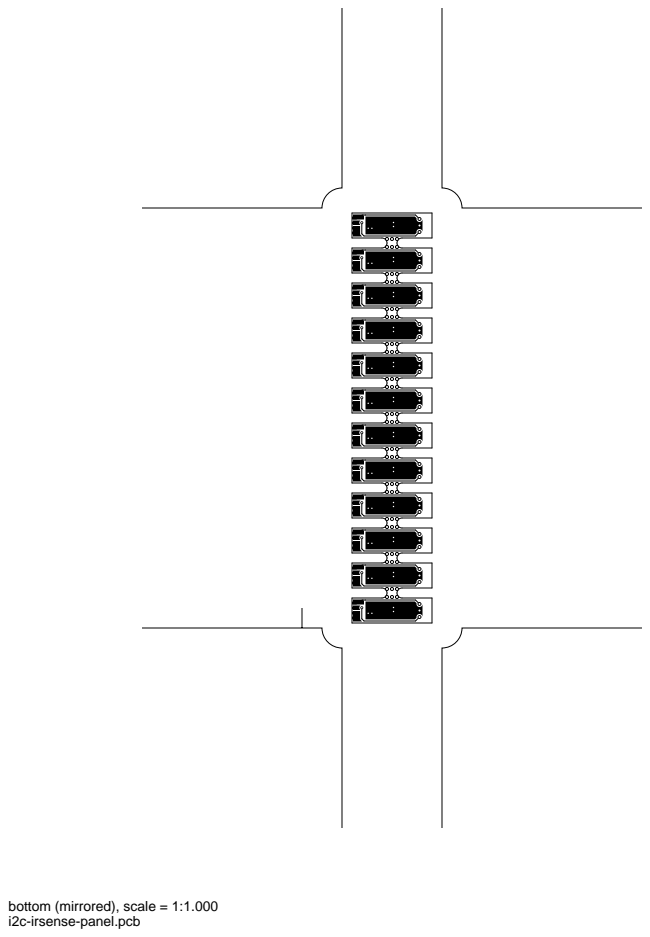
[picture p331: page 3]

bottom (mirrored), scale = 1:1.000

outline, scale = 1:1.000

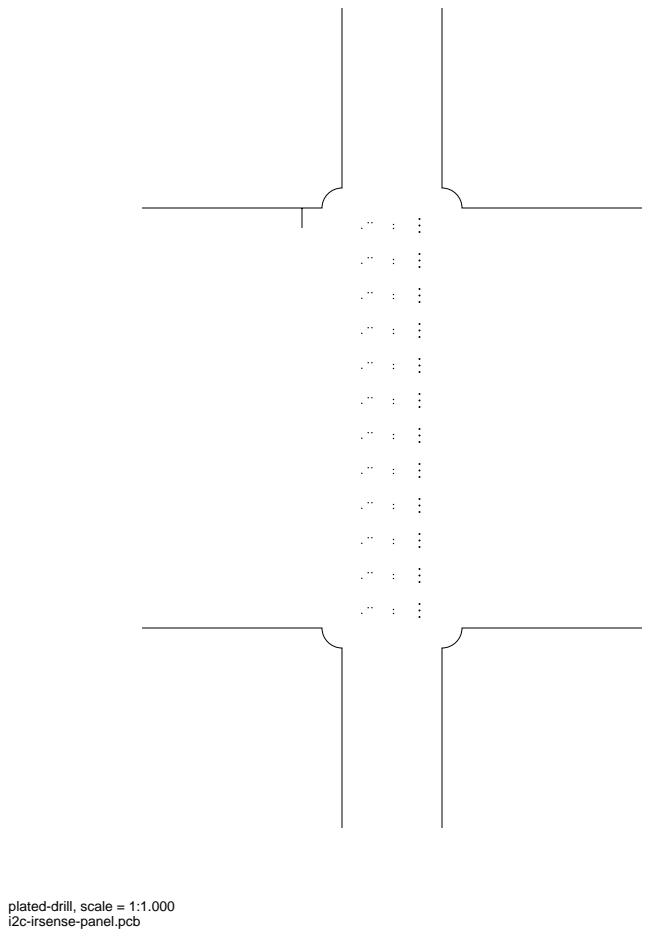
[picture p332: page 5]

plated-drill, scale = 1:1.000


unplated-drill, scale = 1:1.000

topmask, scale = 1:1.000 bottommask (mirrored), scale = 1:1.000

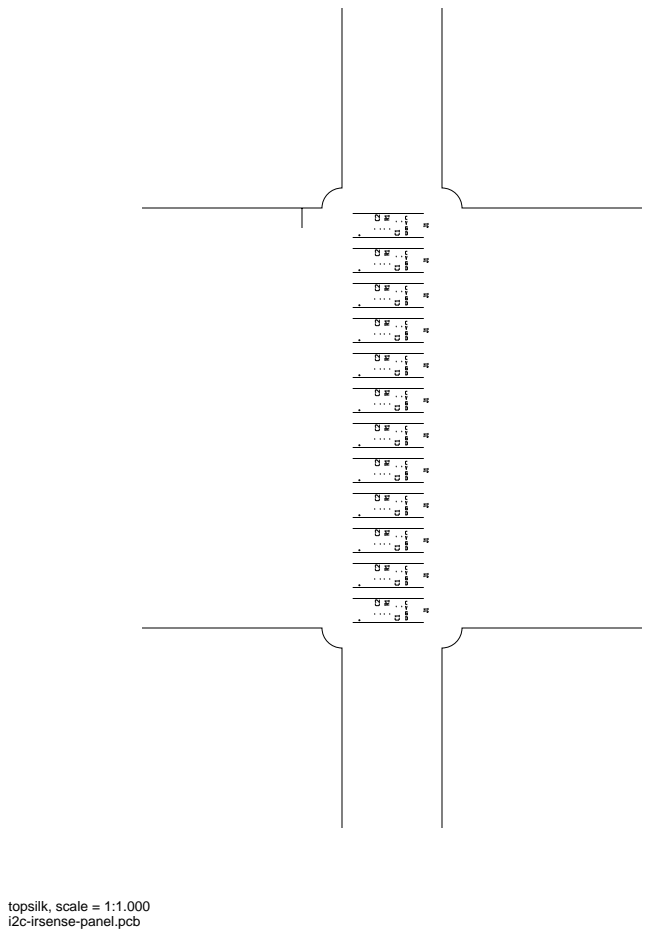
[picture p333: page 9]
topsilk, scale = 1:1.000

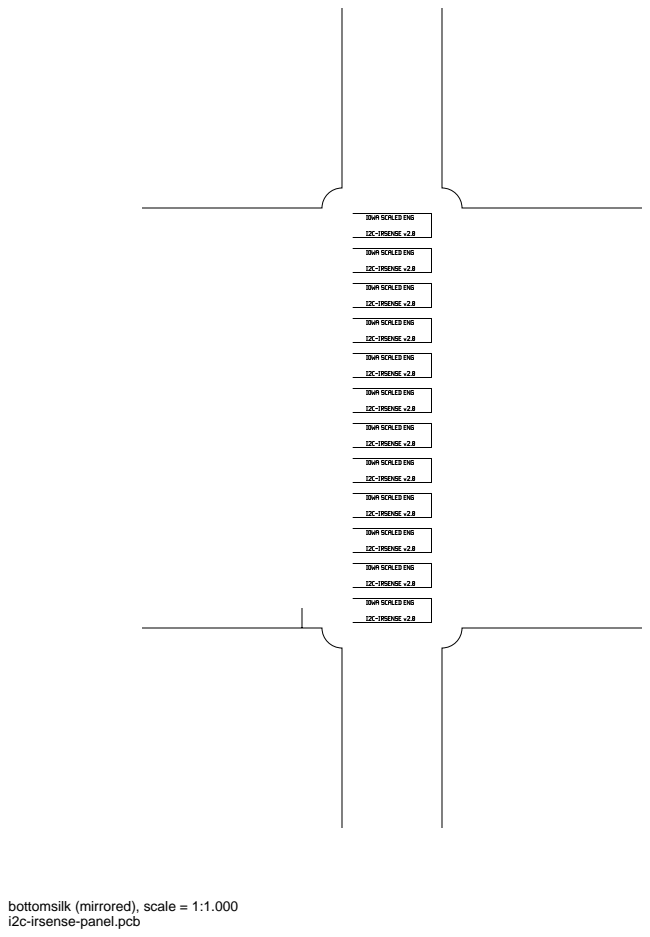
[picture p334: page 10]

bottomsilk (mirrored), scale = 1:1.000

toppaste, scale = 1:1.000

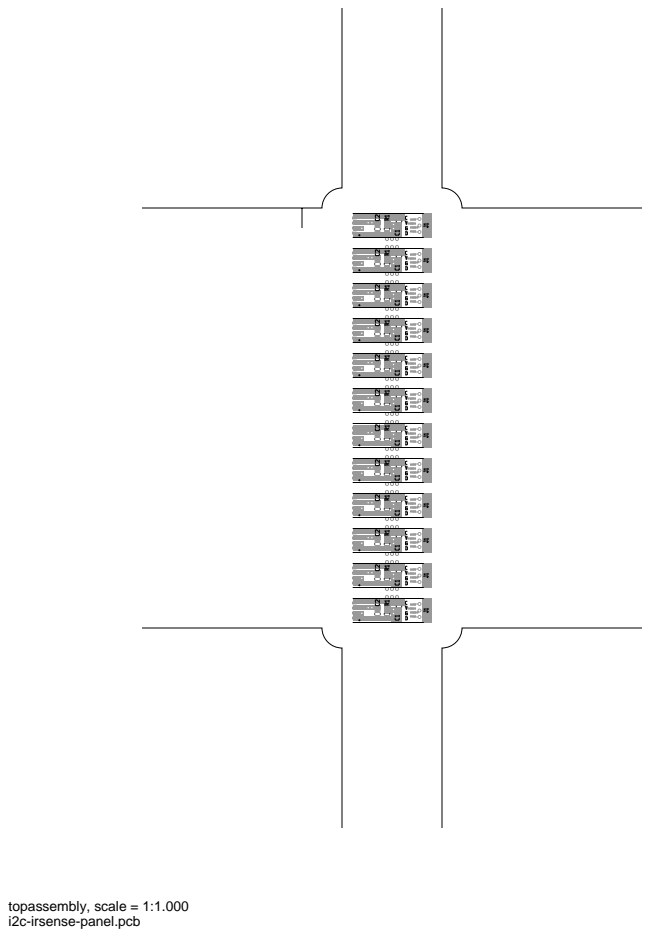
[picture p335: page 12]
topassembly, scale = 1:1.000

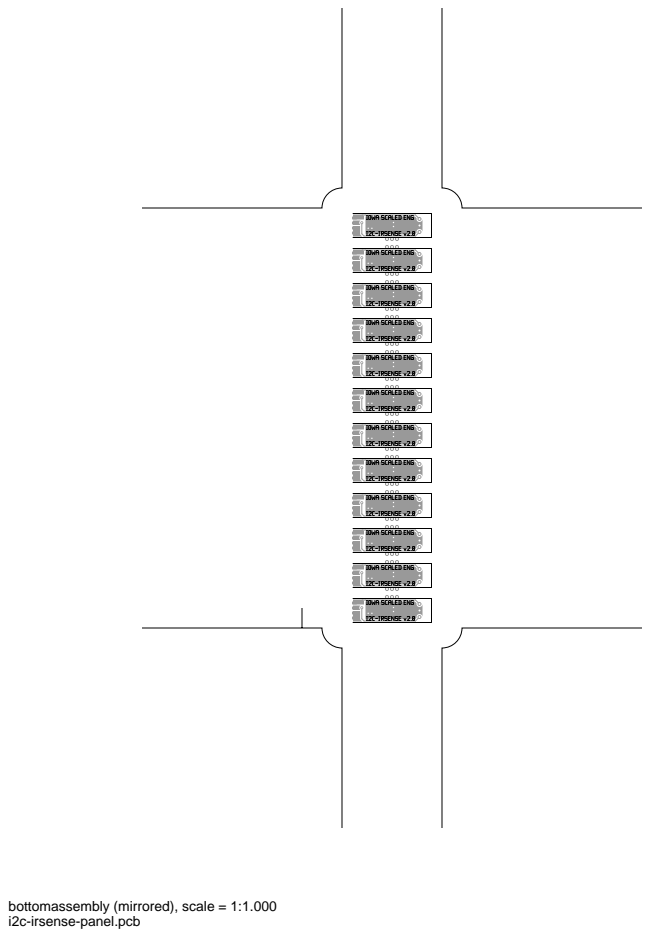
[picture p336: page 13]

bottomassembly (mirrored), scale = 1:1.000

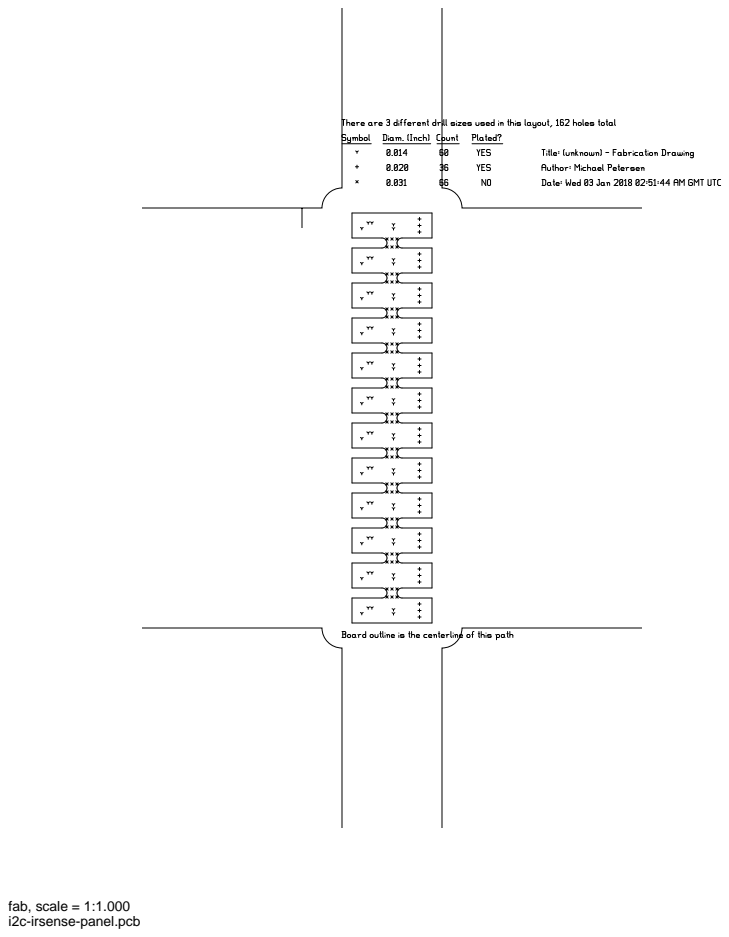
[picture p337: page 14]
fab, scale = 1:1.000
