IowaScaledEngineering/ckt-irsense/pg/ckt-irsense-base-v1.1-283f345/ckt-irsense-base.pdf

Reflective IR Model Railroad Sensor Base (v3)
ckt−irsense−base.sch
