IowaScaledEngineering/ckt-irsense/pg/ckt-irsense-panel-v3.2-bc85a79/ckt-irsense-panel-pcb.pdf

# ckt-irsense-panel.pcb

# 1. Table of Contents (This Page) Created on Sun Feb 1 21:29:51 2015

# 2. top 3. bottom 4. outline 5. plated-drill 6. unplated-drill 7. componentmask 8. soldermask 9. topsilk 10. bottomsilk 11. toppaste 12. topassembly 13. bottomassembly 14. fab

top, scale = 1:1.000


bottom (mirrored), scale = 1:1.000

outline, scale = 1:1.000


plated-drill, scale = 1:1.000


unplated-drill, scale = 1:1.000

topmask, scale = 1:1.000


bottommask (mirrored), scale = 1:1.000

topsilk, scale = 1:1.000


bottomsilk (mirrored), scale = 1:1.000

toppaste, scale = 1:1.000

topassembly, scale = 1:1.000


bottomassembly (mirrored), scale = 1:1.000

fab, scale = 1:1.000
