IowaScaledEngineering/ckt-irsense/pg/ckt-irsense-v3.1-r943/ckt-irsense.pdf

Reflective IR Model Railroad Sensor (v3)
ckt−irsense.sch
