IowaScaledEngineering/ckt-irsense/pg/ckt-irsense-v3.0-r929/ckt-irsense.pdf

Reflective IR Model Railroad Sensor (v3)
ckt−irsense.sch
