IowaScaledEngineering/ckt-irsense/pg/ckt-irsense-v2.0-r755/ckt-irsense.pdf

MISO | 5V

SCK | MOSI

Reflective IR model railroad sensor
ckt−irsense.sch
