IowaScaledEngineering/ckt-irsense/pg/ckt-irsense-v1.0-r656/ckt-irsense.pdf

MISO | 5V

SCK | MOSI

Reflective IR model railroad sensor
ckt−irsense.sch
